daeken/ReCurta/app/curta_jpegs/Curta_1_2037.jpg

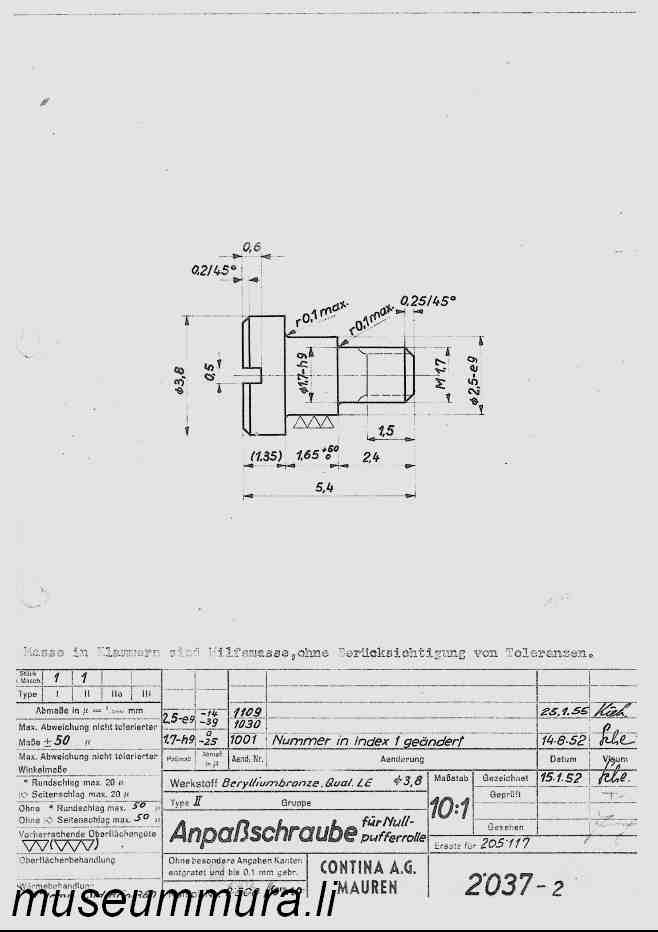
app/curta_jpegs/Curta_1_2037.jpg
