daeken/ReCurta/app/curta_jpegs/Curta_1_10002.jpg

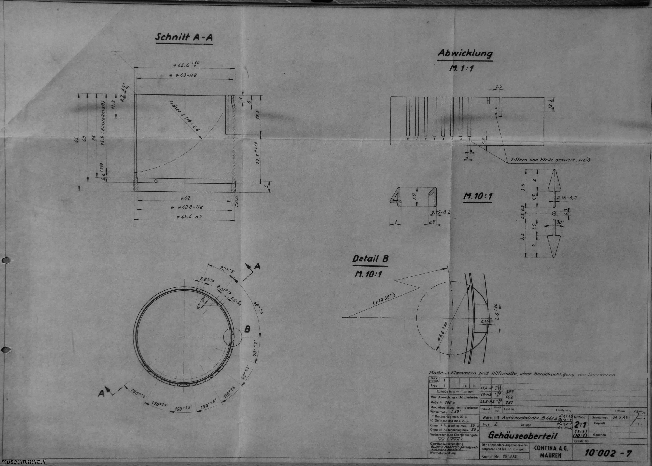
app/curta_jpegs/Curta_1_10002.jpg
