daeken/ReCurta/app/curta_jpegs/Curta_1_10006.jpg

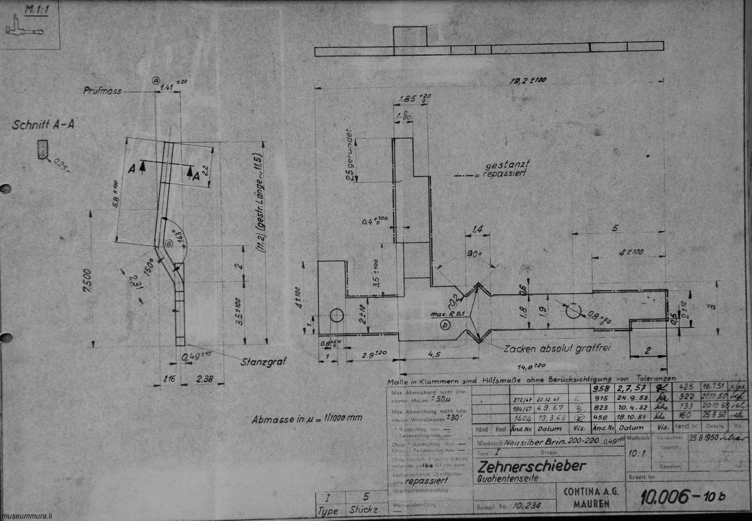
app/curta_jpegs/Curta_1_10006.jpg
