daeken/ReCurta/app/curta_jpegs/Curta_1_10007.jpg

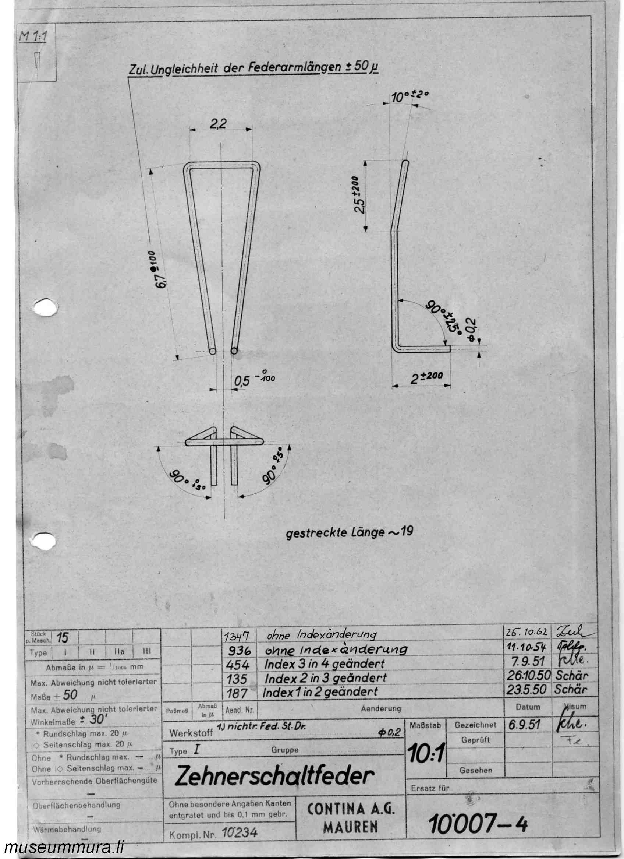
app/curta_jpegs/Curta_1_10007.jpg
