daeken/ReCurta/app/curta_jpegs/Curta_1_10008.jpg

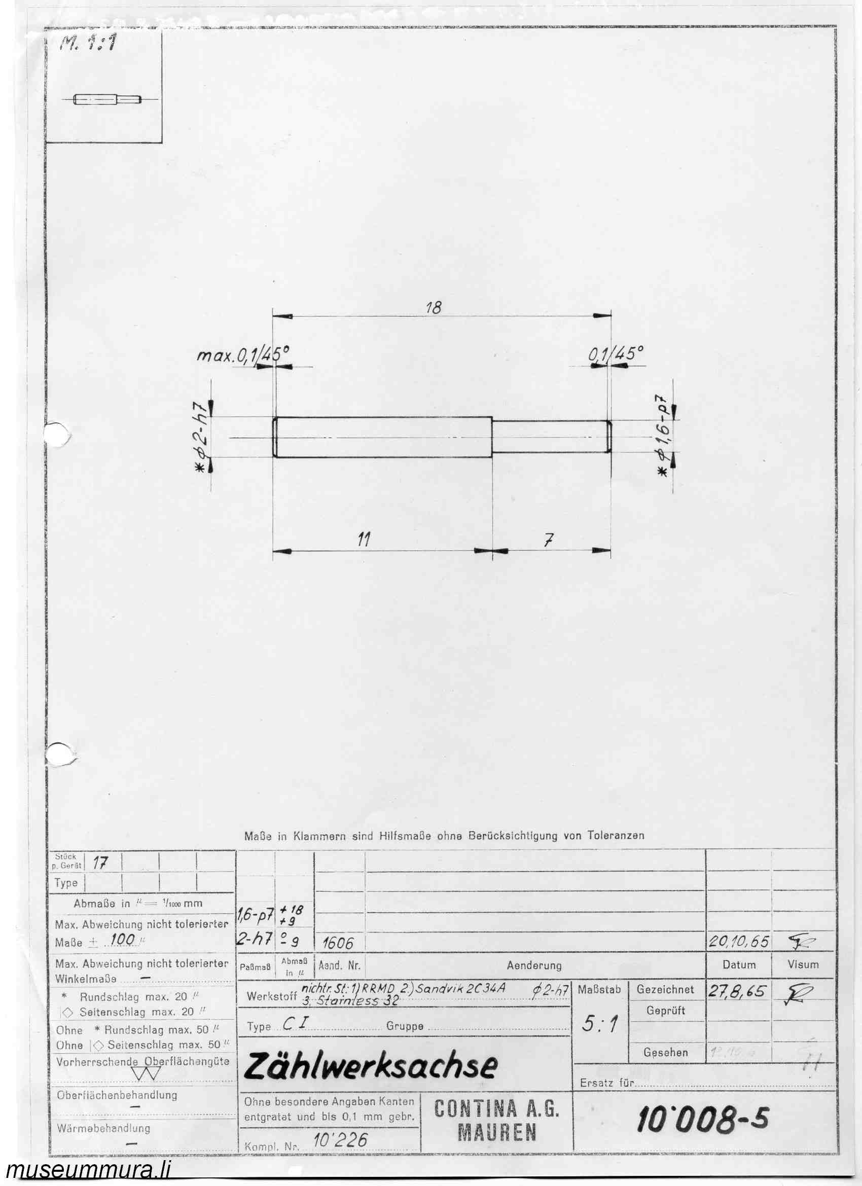
app/curta_jpegs/Curta_1_10008.jpg
