daeken/ReCurta/app/curta_jpegs/Curta_1_10009.jpg

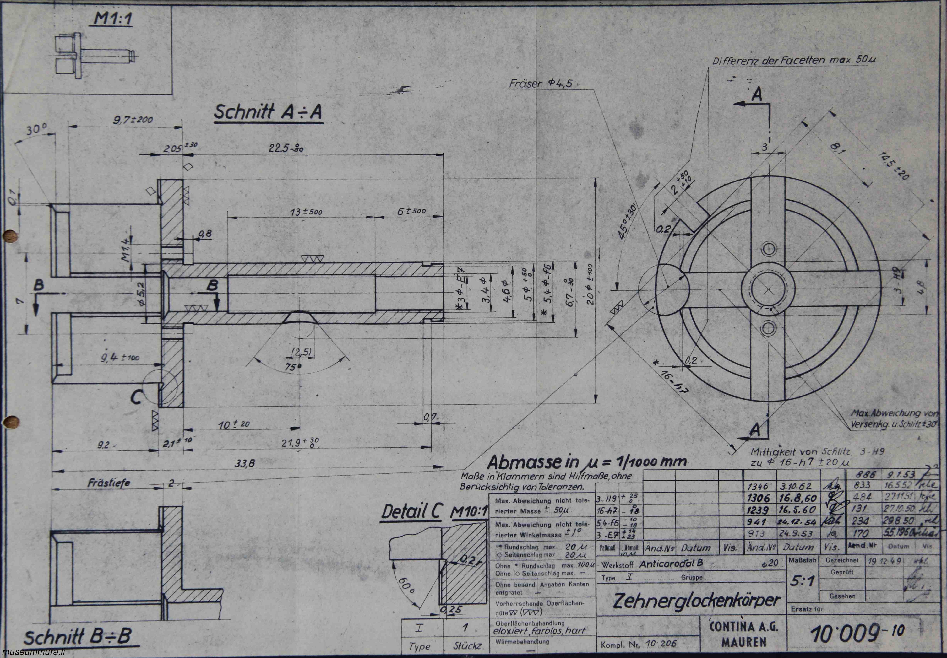
app/curta_jpegs/Curta_1_10009.jpg
