daeken/ReCurta/app/curta_jpegs/Curta_1_10010.jpg

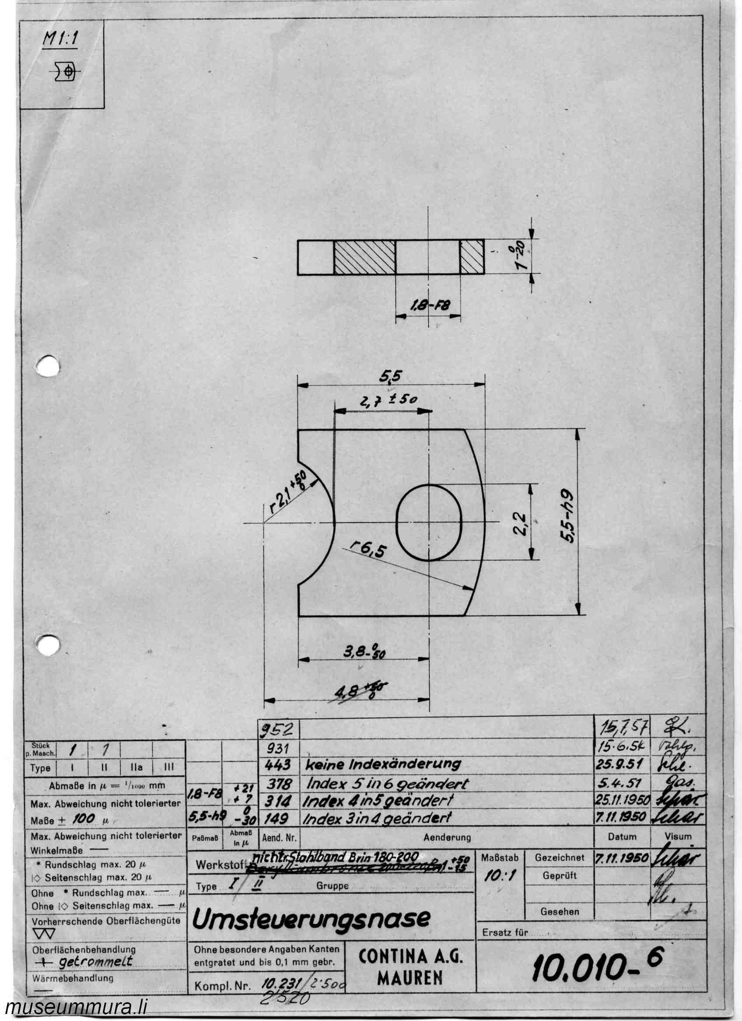
app/curta_jpegs/Curta_1_10010.jpg
