daeken/ReCurta/app/curta_jpegs/Curta_1_10011.jpg

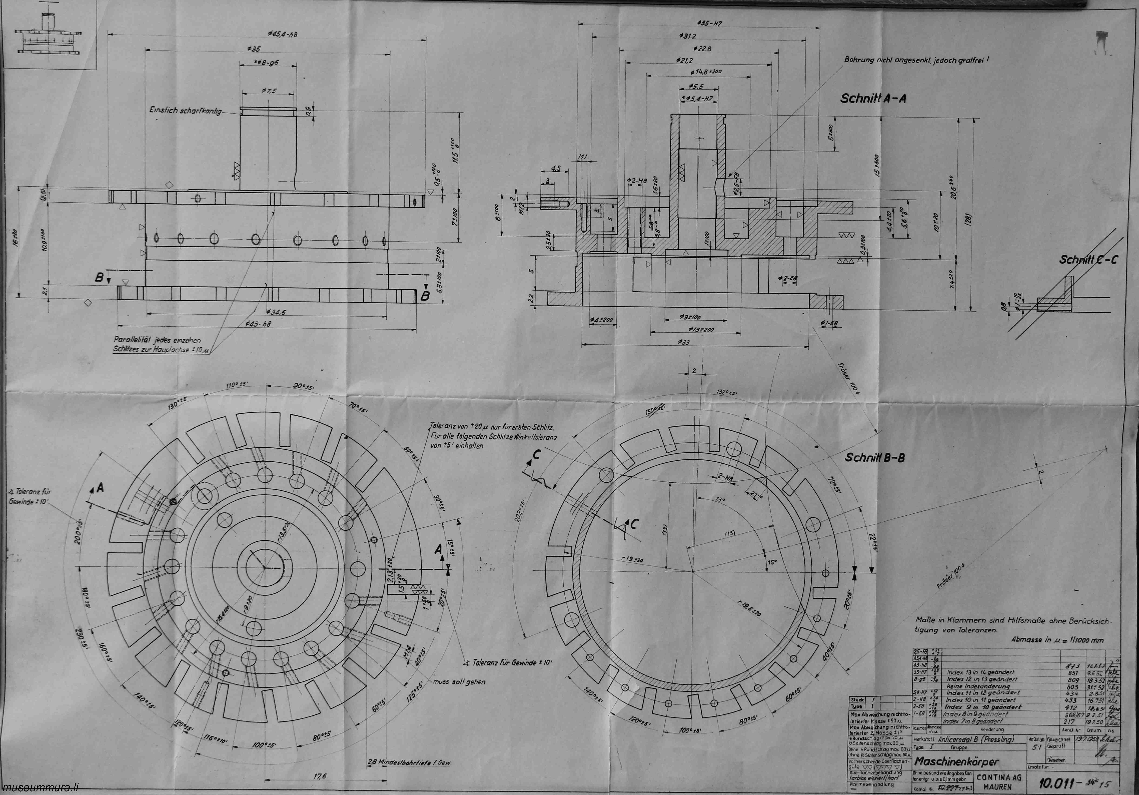
app/curta_jpegs/Curta_1_10011.jpg
