daeken/ReCurta/app/curta_jpegs/Curta_1_10014.jpg

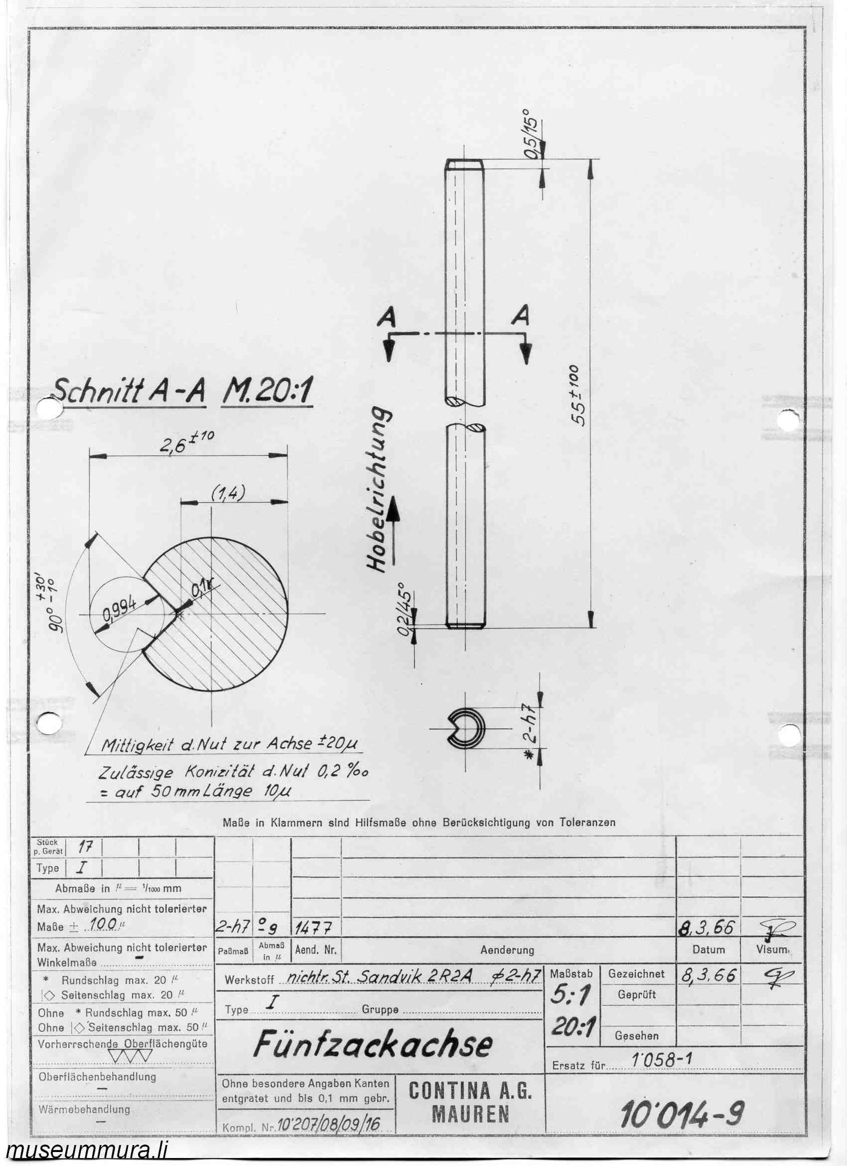
app/curta_jpegs/Curta_1_10014.jpg
