daeken/ReCurta/app/curta_jpegs/Curta_1_10015.jpg

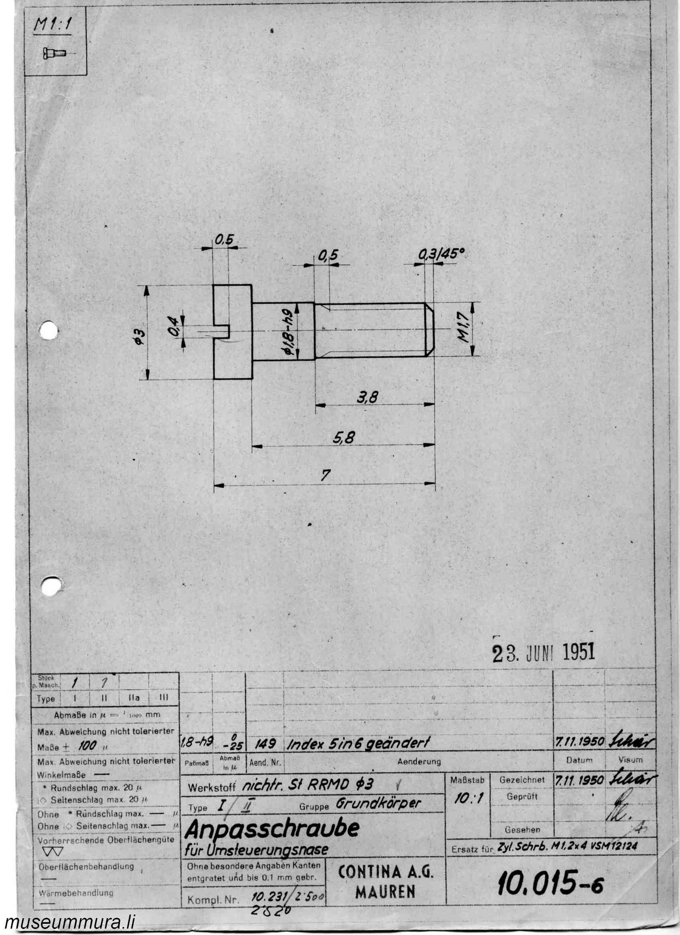
app/curta_jpegs/Curta_1_10015.jpg
