daeken/ReCurta/app/curta_jpegs/Curta_1_10018.jpg

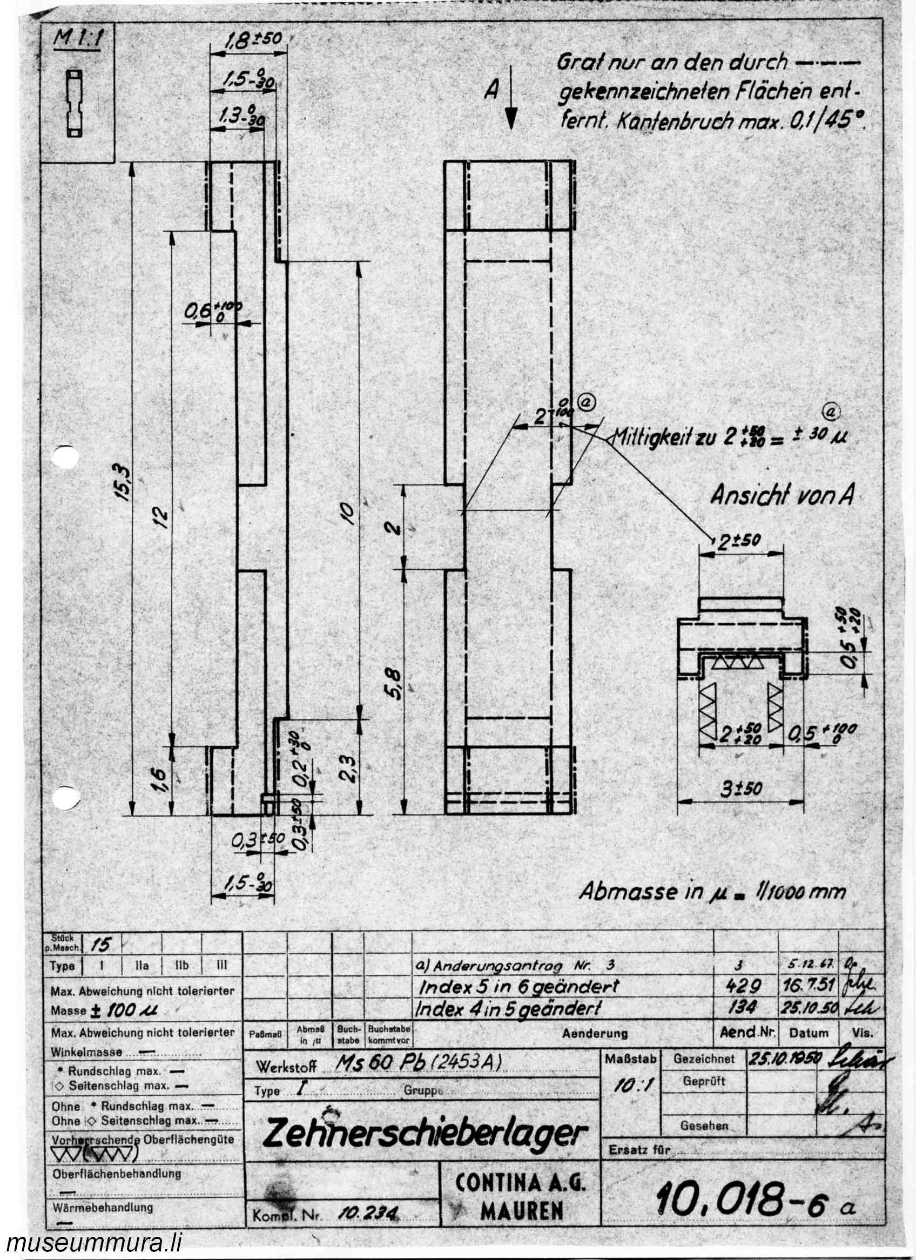
app/curta_jpegs/Curta_1_10018.jpg
