daeken/ReCurta/app/curta_jpegs/Curta_1_10019.jpg

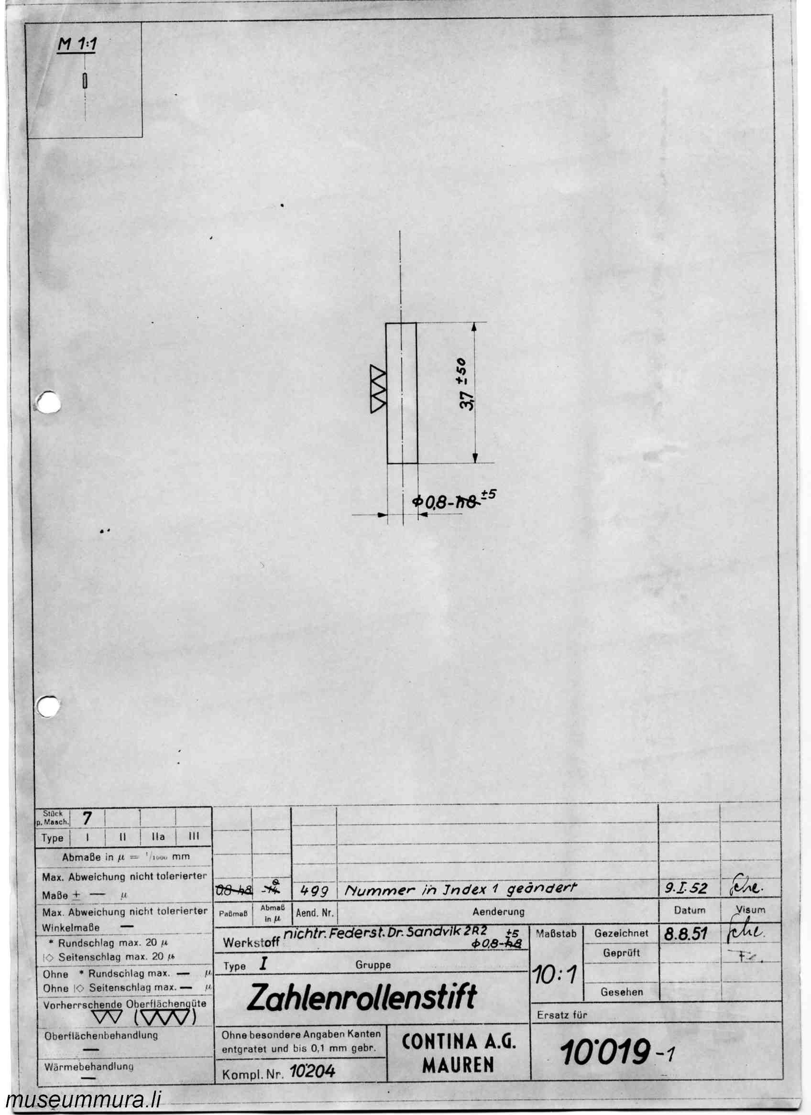
app/curta_jpegs/Curta_1_10019.jpg
