daeken/ReCurta/app/curta_jpegs/Curta_1_10020.jpg

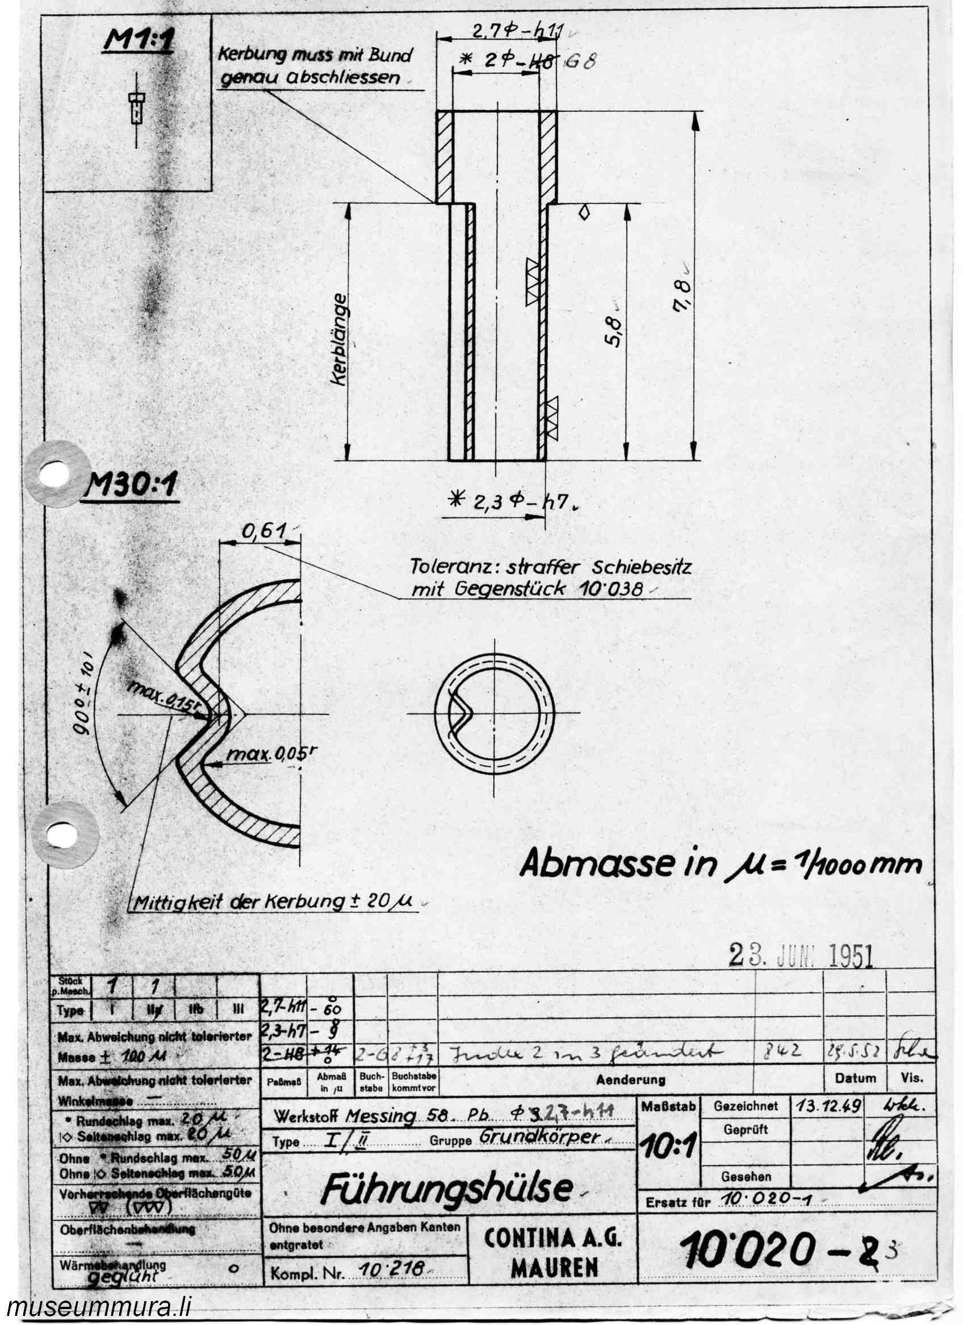
app/curta_jpegs/Curta_1_10020.jpg
