daeken/ReCurta/app/curta_jpegs/Curta_1_10021.jpg

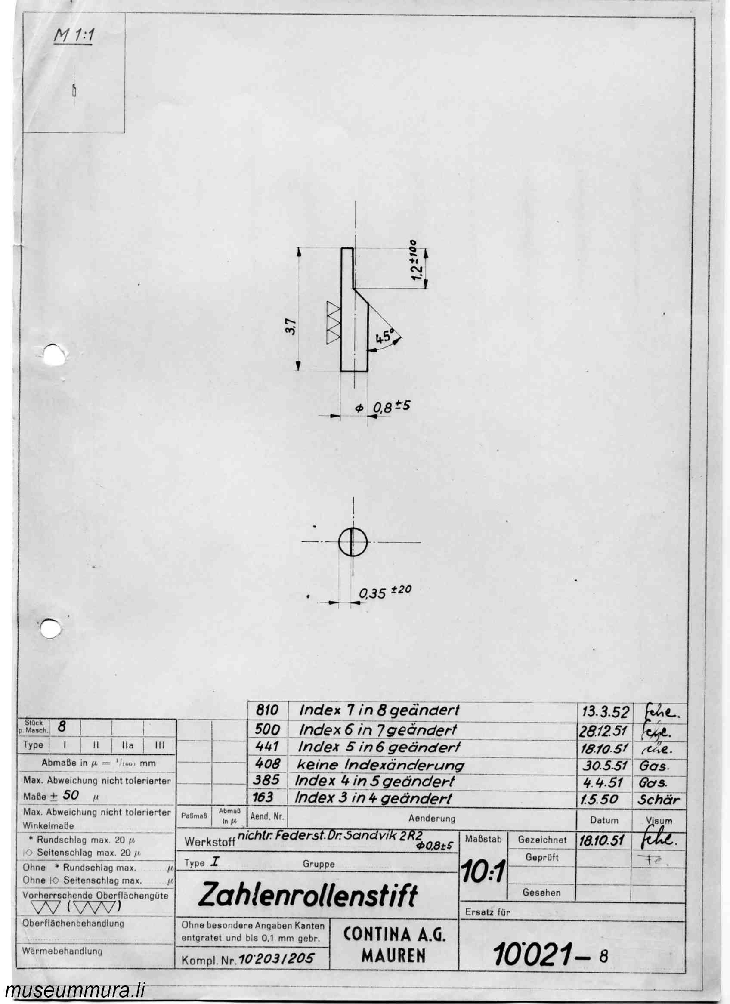
app/curta_jpegs/Curta_1_10021.jpg
