daeken/ReCurta/app/curta_jpegs/Curta_1_10024.jpg

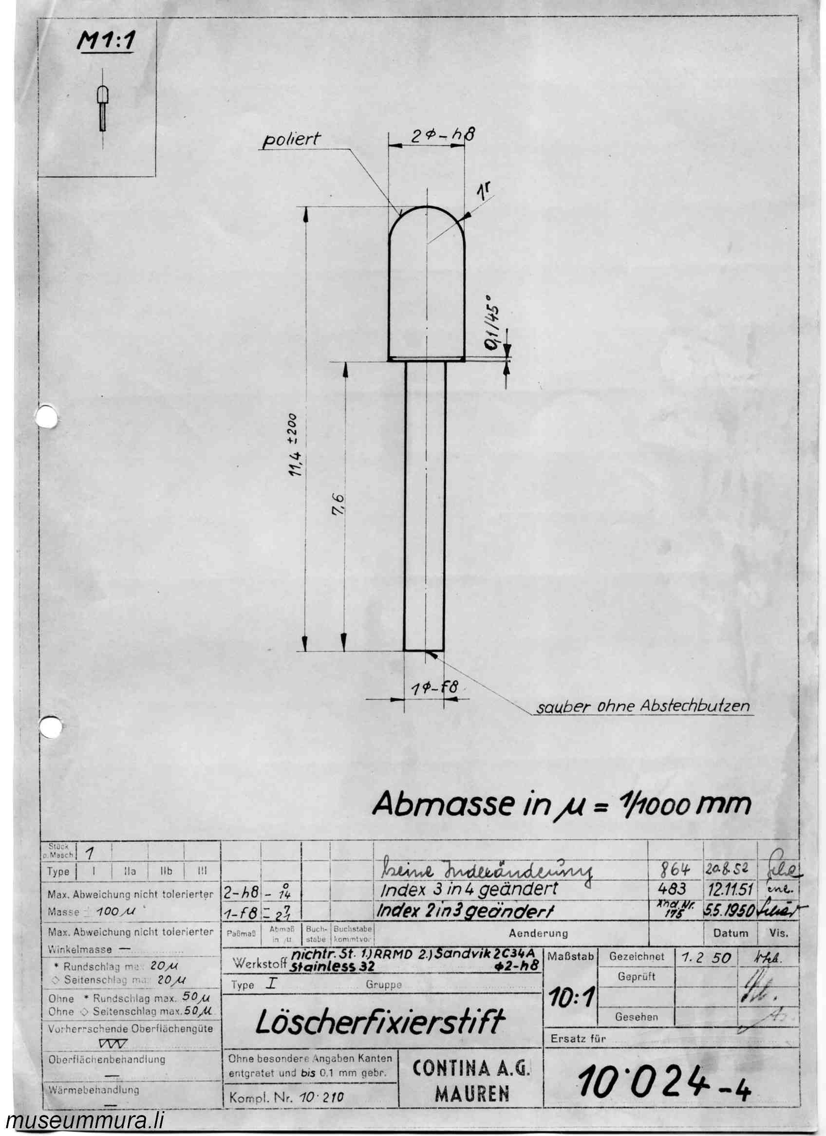
app/curta_jpegs/Curta_1_10024.jpg
