daeken/ReCurta/app/curta_jpegs/Curta_1_10026.jpg

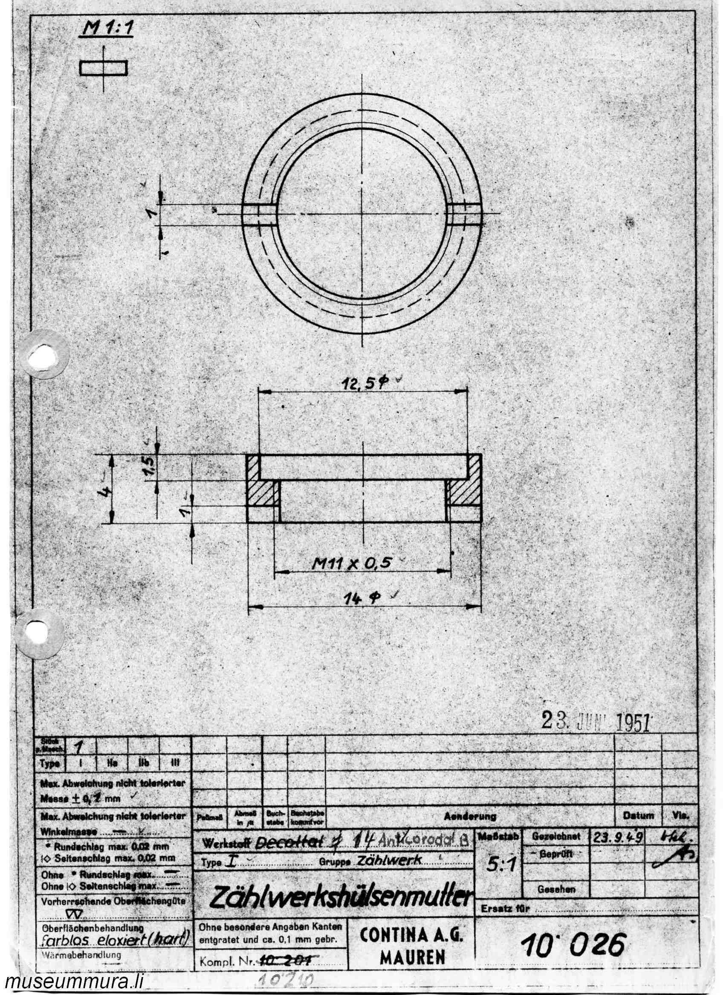
app/curta_jpegs/Curta_1_10026.jpg
