daeken/ReCurta/app/curta_jpegs/Curta_1_10028.jpg

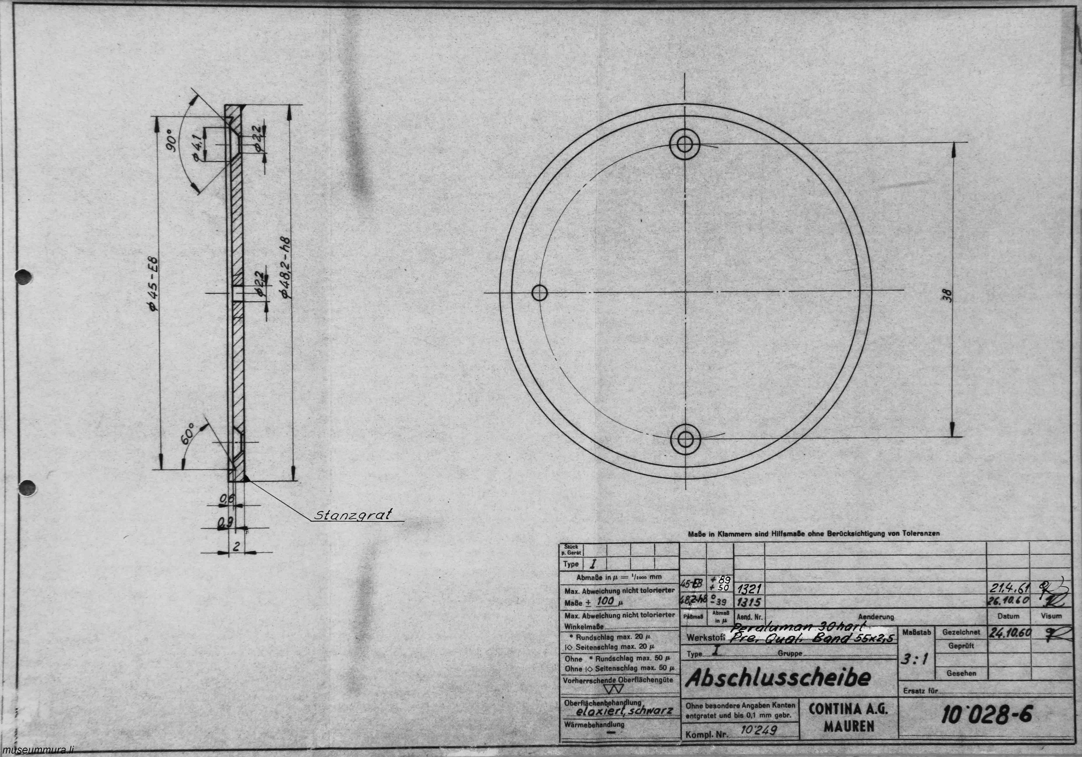
app/curta_jpegs/Curta_1_10028.jpg
