daeken/ReCurta/app/curta_jpegs/Curta_1_10030.jpg

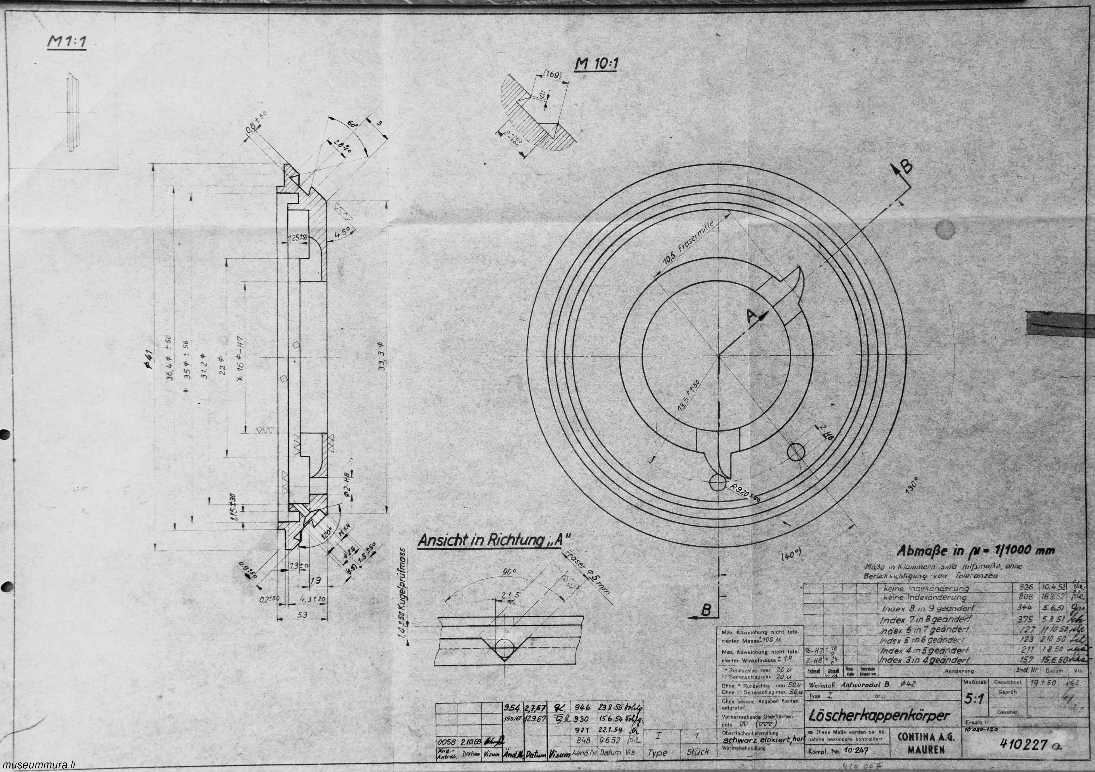
app/curta_jpegs/Curta_1_10030.jpg
