daeken/ReCurta/app/curta_jpegs/Curta_1_10031.jpg

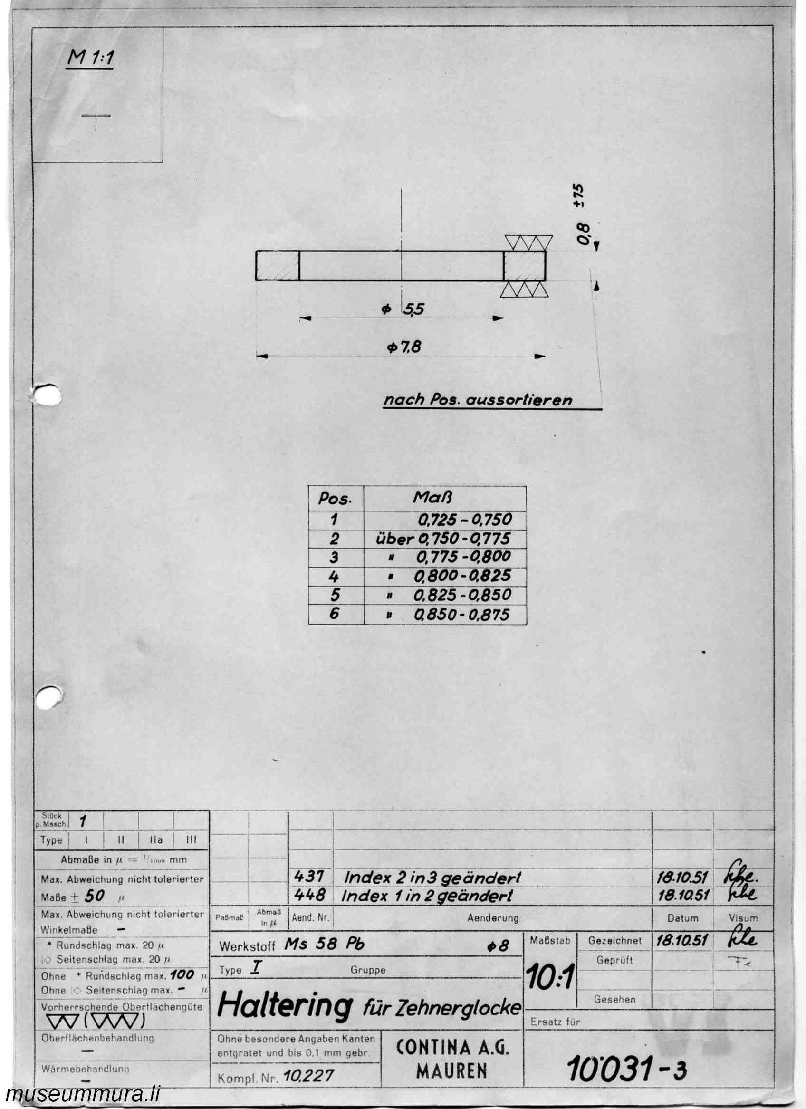
app/curta_jpegs/Curta_1_10031.jpg
