daeken/ReCurta/app/curta_jpegs/Curta_1_10033.jpg

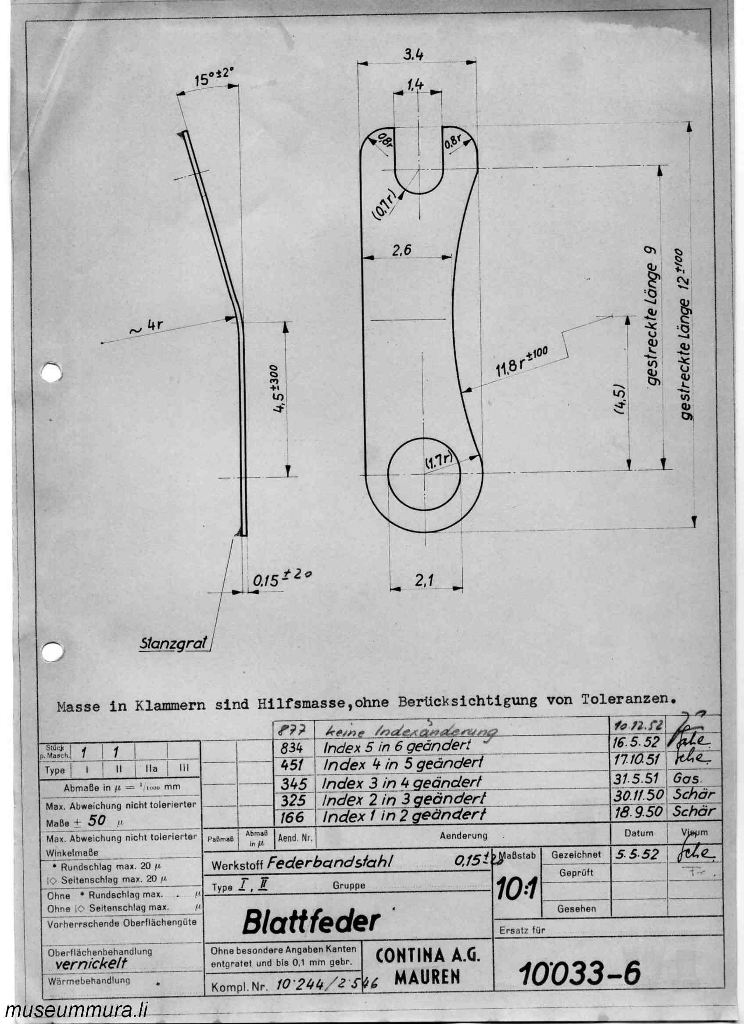
app/curta_jpegs/Curta_1_10033.jpg
