daeken/ReCurta/app/curta_jpegs/Curta_1_10034.jpg

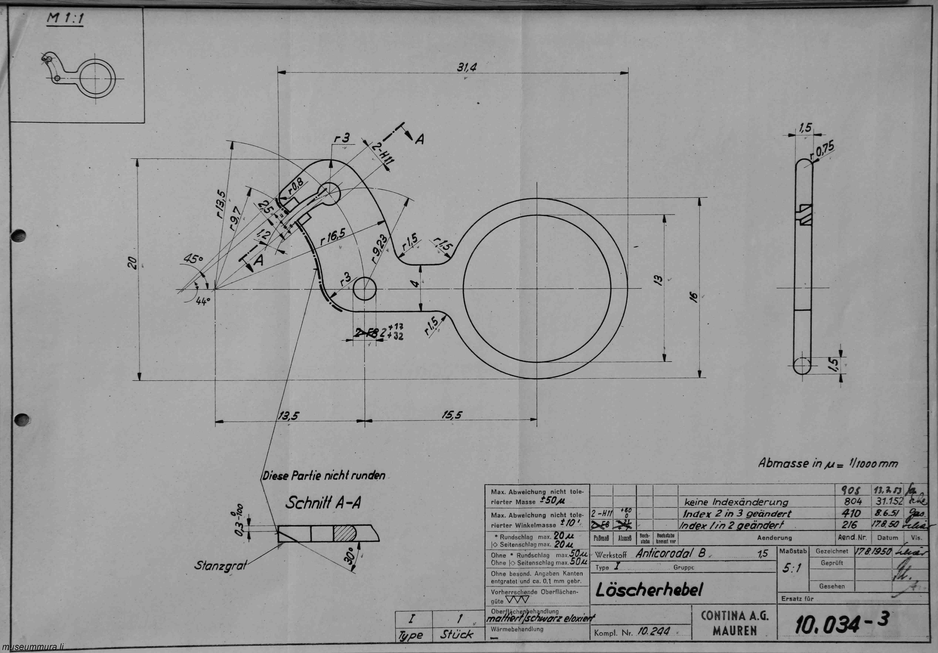
app/curta_jpegs/Curta_1_10034.jpg
