daeken/ReCurta/app/curta_jpegs/Curta_1_10035.jpg

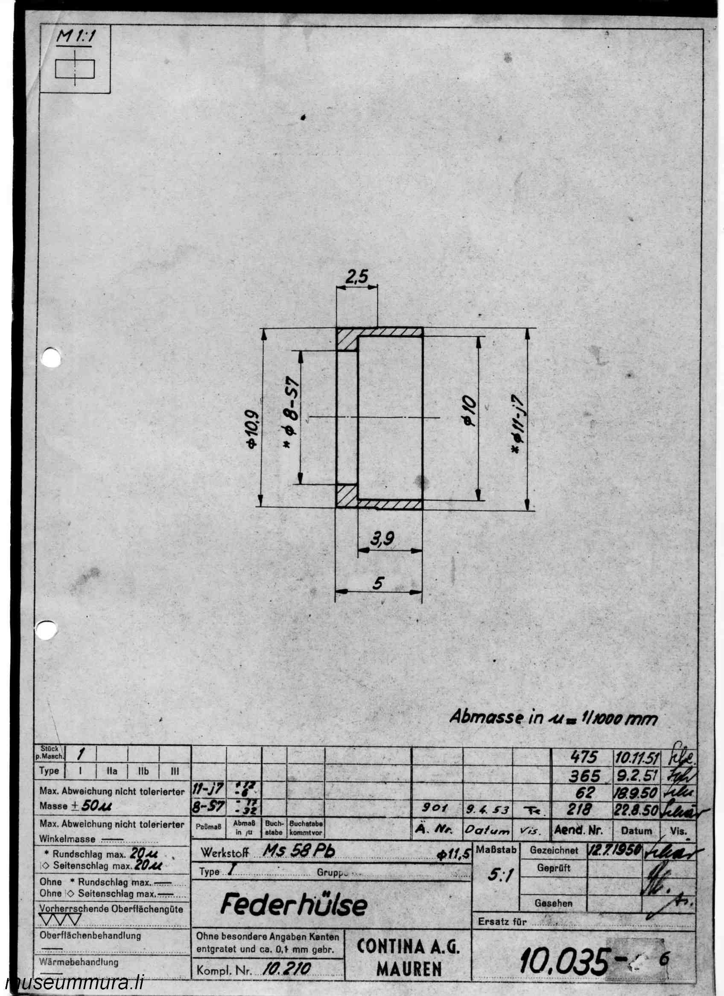
app/curta_jpegs/Curta_1_10035.jpg
