daeken/ReCurta/app/curta_jpegs/Curta_1_10036.jpg

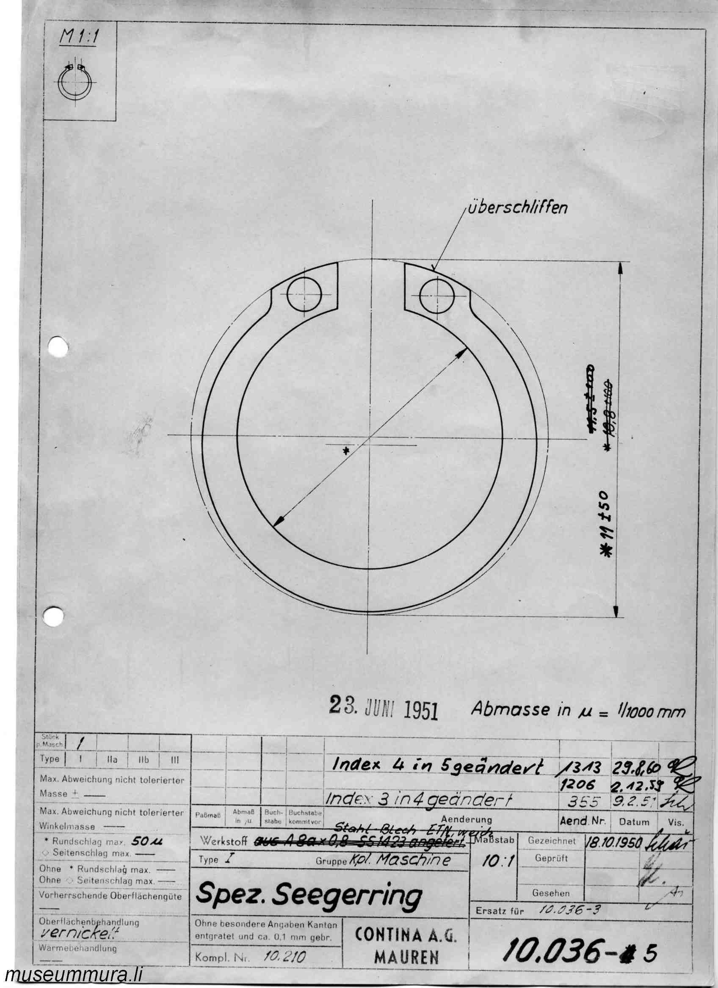
app/curta_jpegs/Curta_1_10036.jpg
