daeken/ReCurta/app/curta_jpegs/Curta_1_10039.jpg

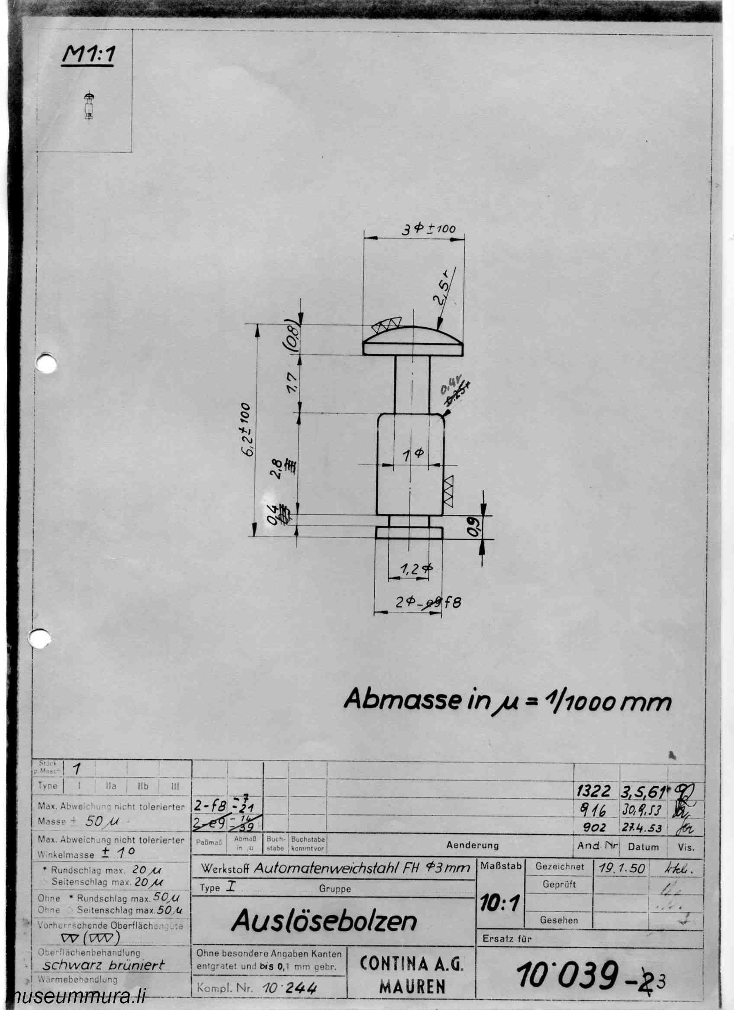
app/curta_jpegs/Curta_1_10039.jpg
