daeken/ReCurta/app/curta_jpegs/Curta_1_10041.jpg

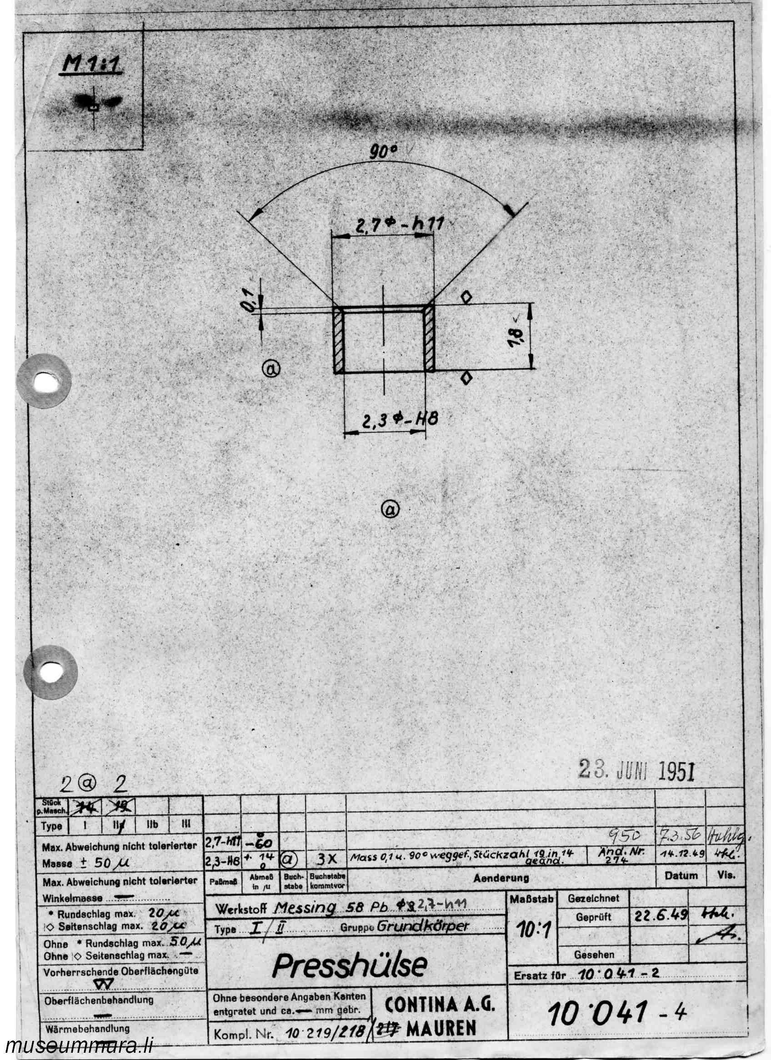
app/curta_jpegs/Curta_1_10041.jpg
