daeken/ReCurta/app/curta_jpegs/Curta_1_10046.jpg

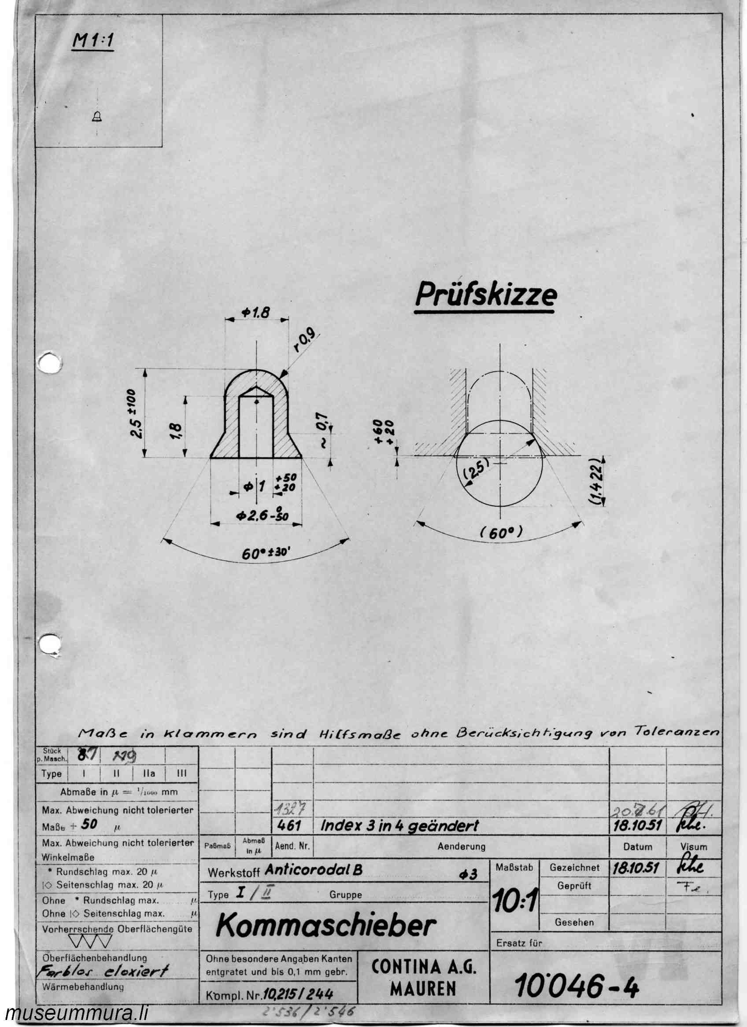
app/curta_jpegs/Curta_1_10046.jpg
