daeken/ReCurta/app/curta_jpegs/Curta_1_10047.jpg

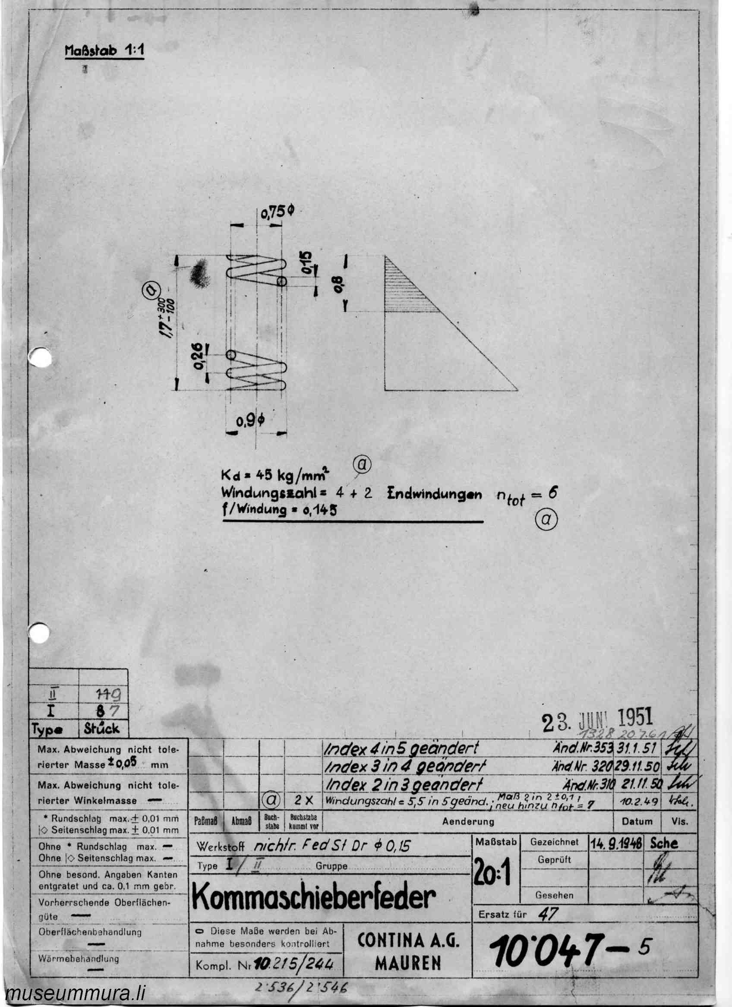
app/curta_jpegs/Curta_1_10047.jpg
