daeken/ReCurta/app/curta_jpegs/Curta_1_10048.jpg

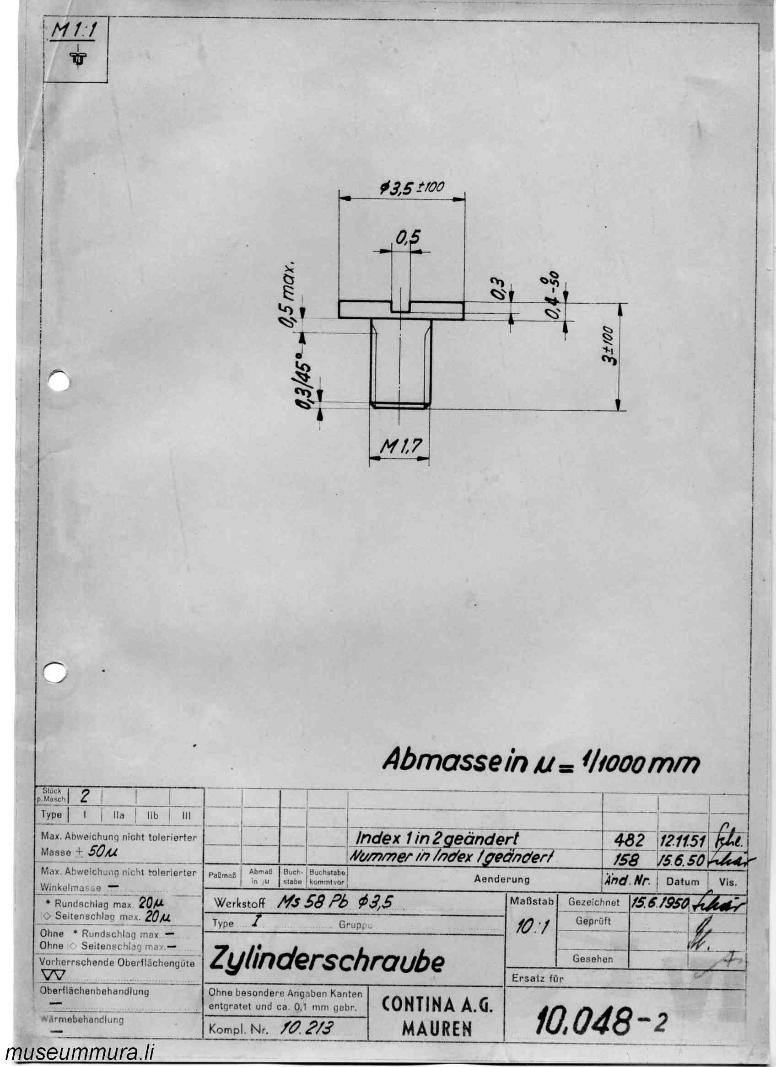
app/curta_jpegs/Curta_1_10048.jpg
