daeken/ReCurta/app/curta_jpegs/Curta_1_10049.jpg

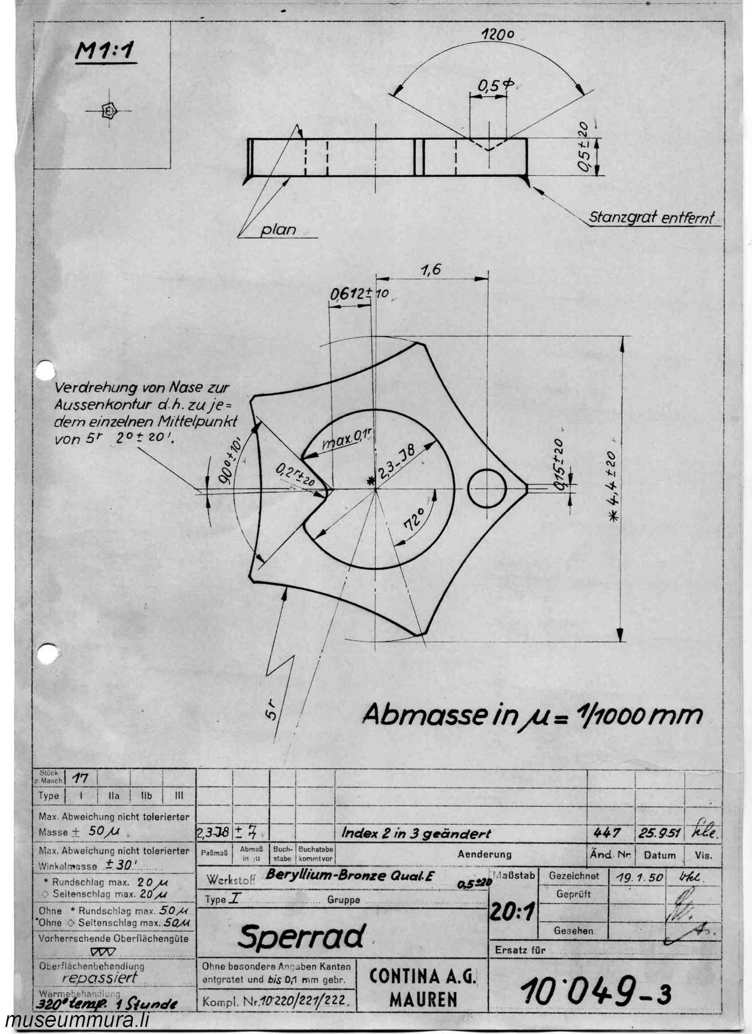
app/curta_jpegs/Curta_1_10049.jpg
