daeken/ReCurta/app/curta_jpegs/Curta_1_10051.jpg

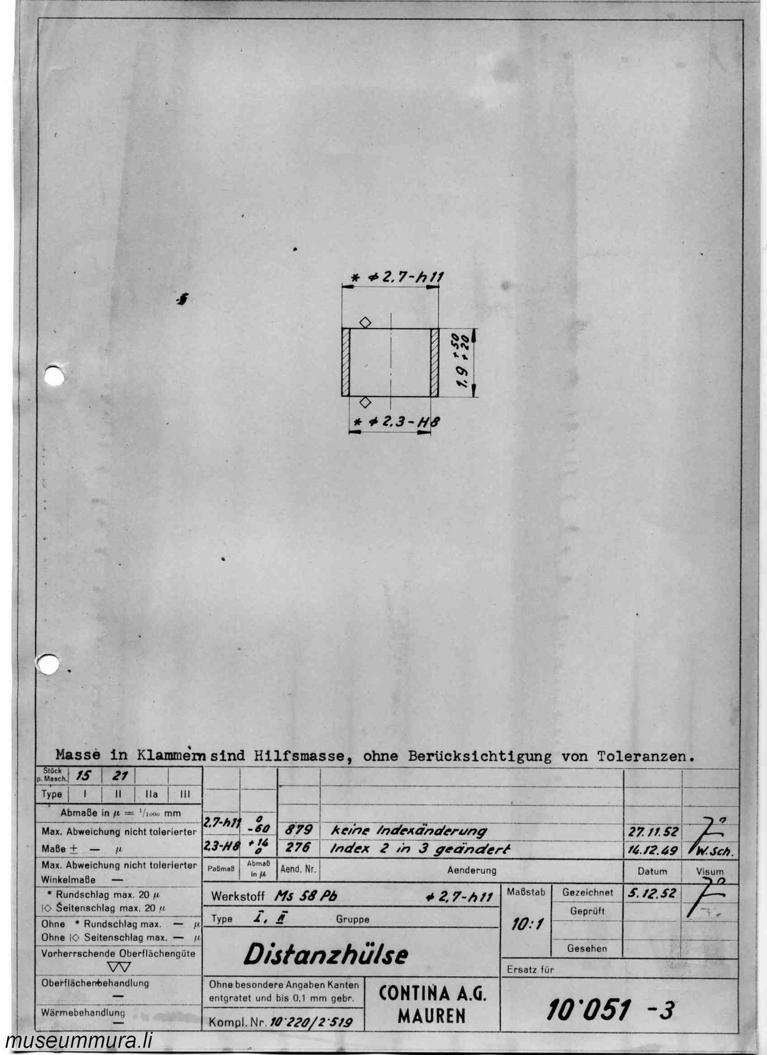
app/curta_jpegs/Curta_1_10051.jpg
