daeken/ReCurta/app/curta_jpegs/Curta_1_10052.jpg

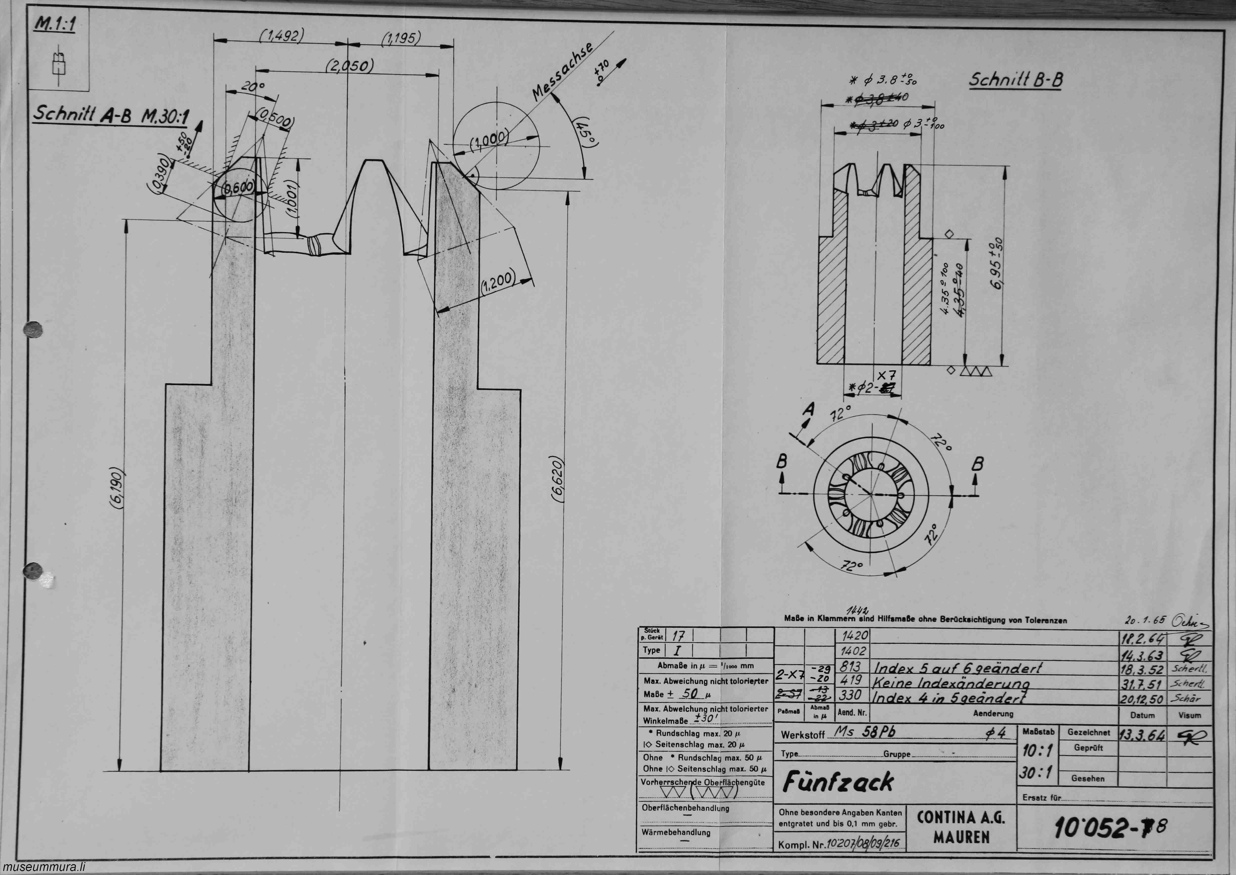
app/curta_jpegs/Curta_1_10052.jpg
