daeken/ReCurta/app/curta_jpegs/Curta_1_10059.jpg

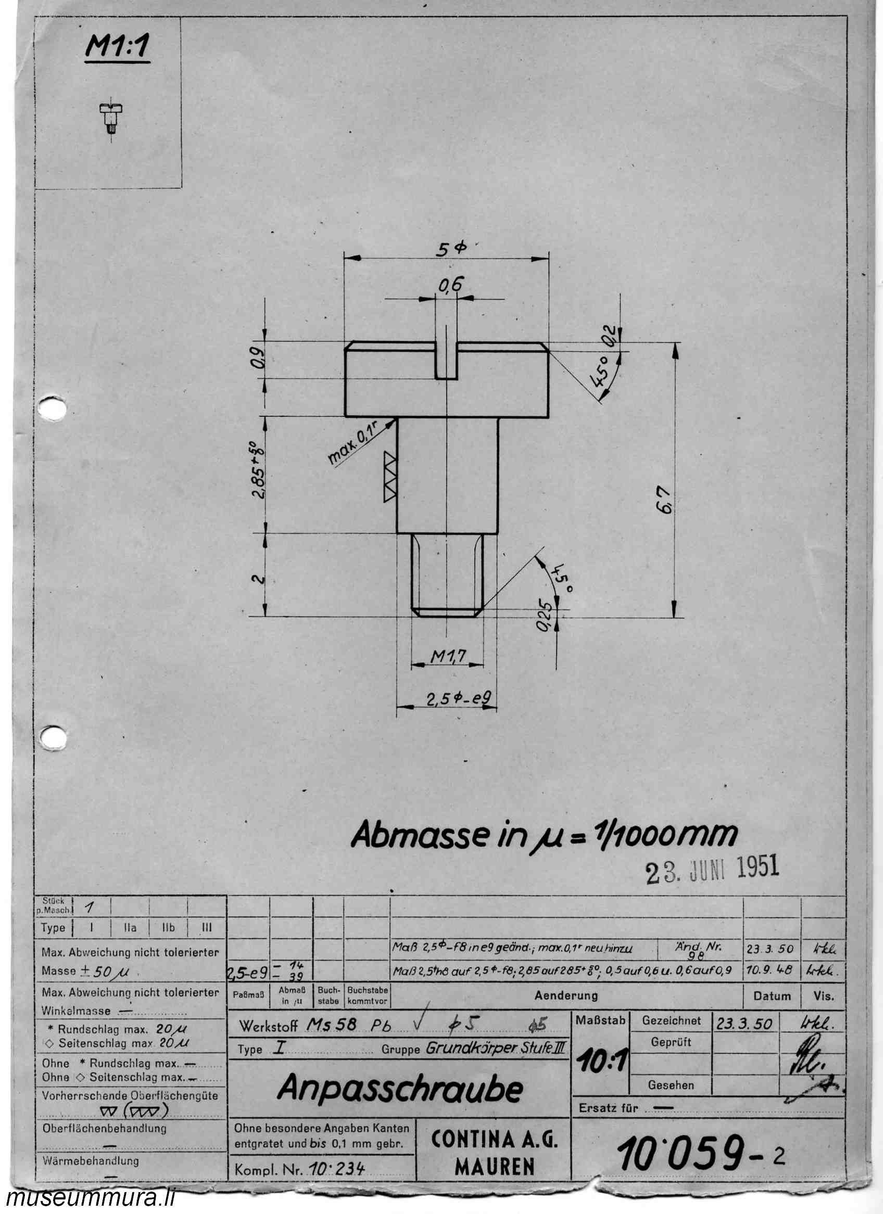
app/curta_jpegs/Curta_1_10059.jpg
