daeken/ReCurta/app/curta_jpegs/Curta_1_10064.jpg

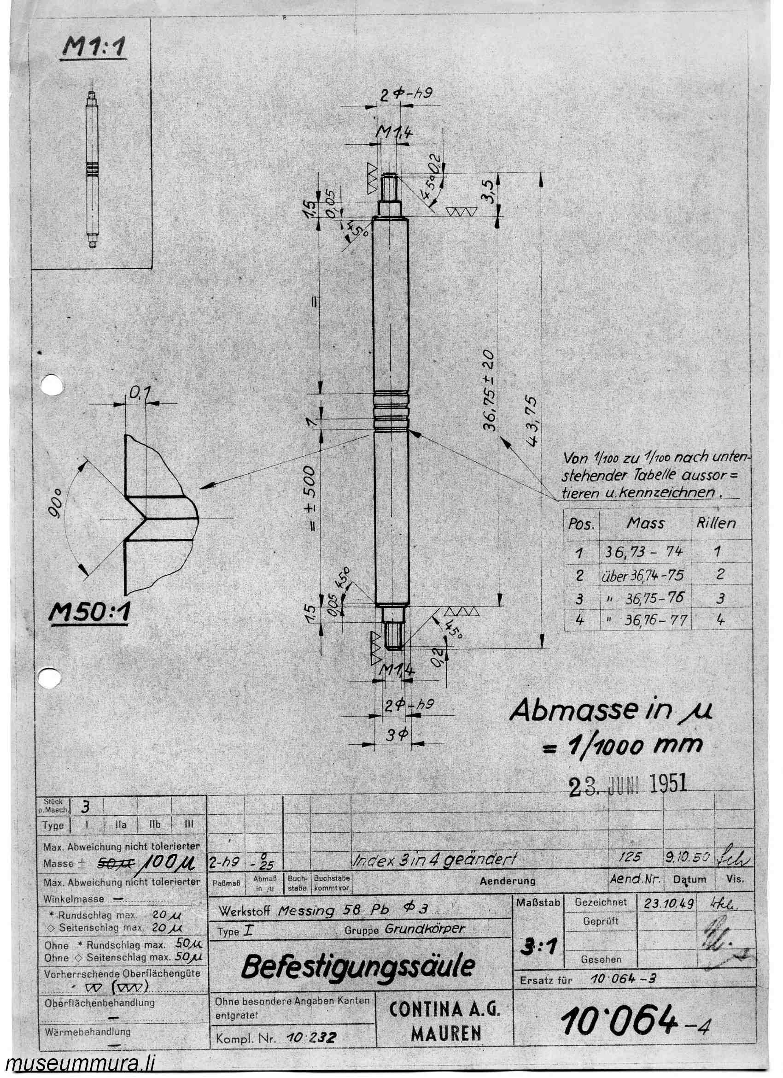
app/curta_jpegs/Curta_1_10064.jpg
