daeken/ReCurta/app/curta_jpegs/Curta_1_10068.jpg

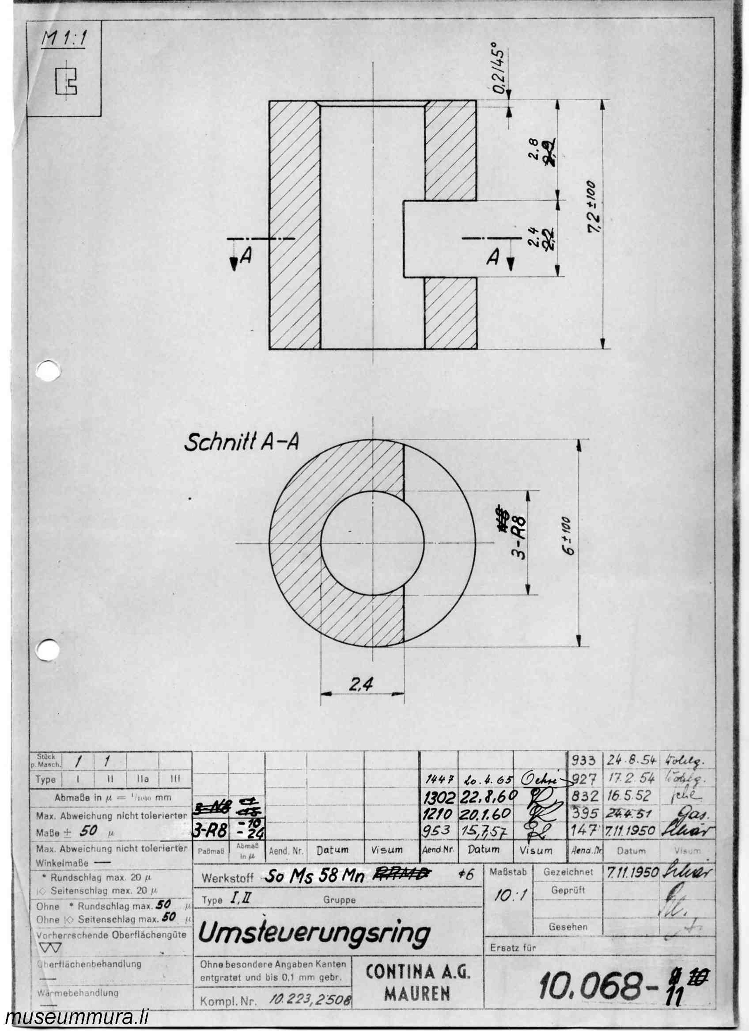
app/curta_jpegs/Curta_1_10068.jpg
