daeken/ReCurta/app/curta_jpegs/Curta_1_10072.jpg

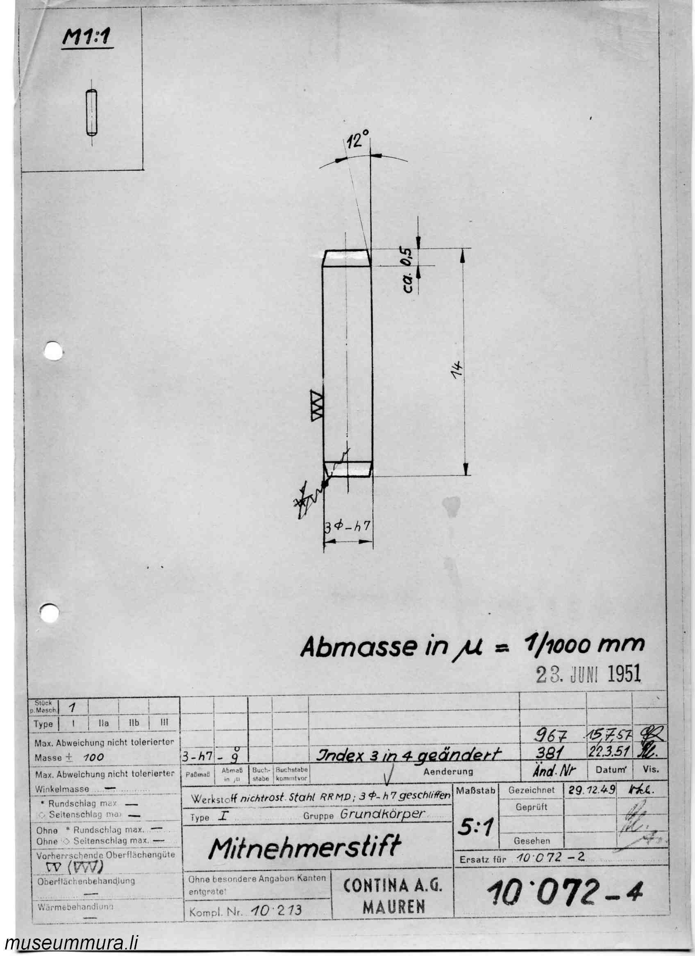
app/curta_jpegs/Curta_1_10072.jpg
