daeken/ReCurta/app/curta_jpegs/Curta_1_10073.jpg

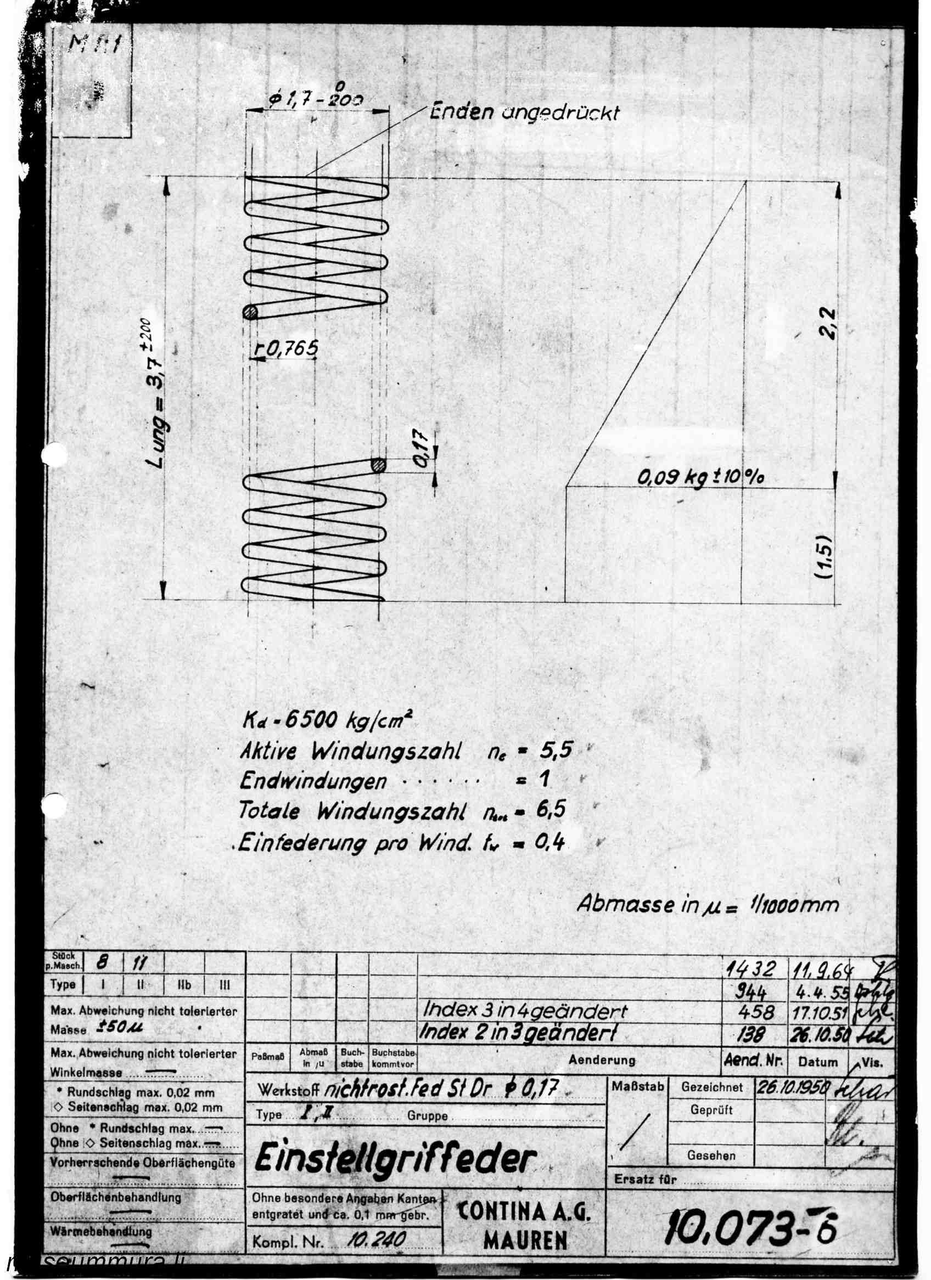
app/curta_jpegs/Curta_1_10073.jpg
