daeken/ReCurta/app/curta_jpegs/Curta_1_10074.jpg

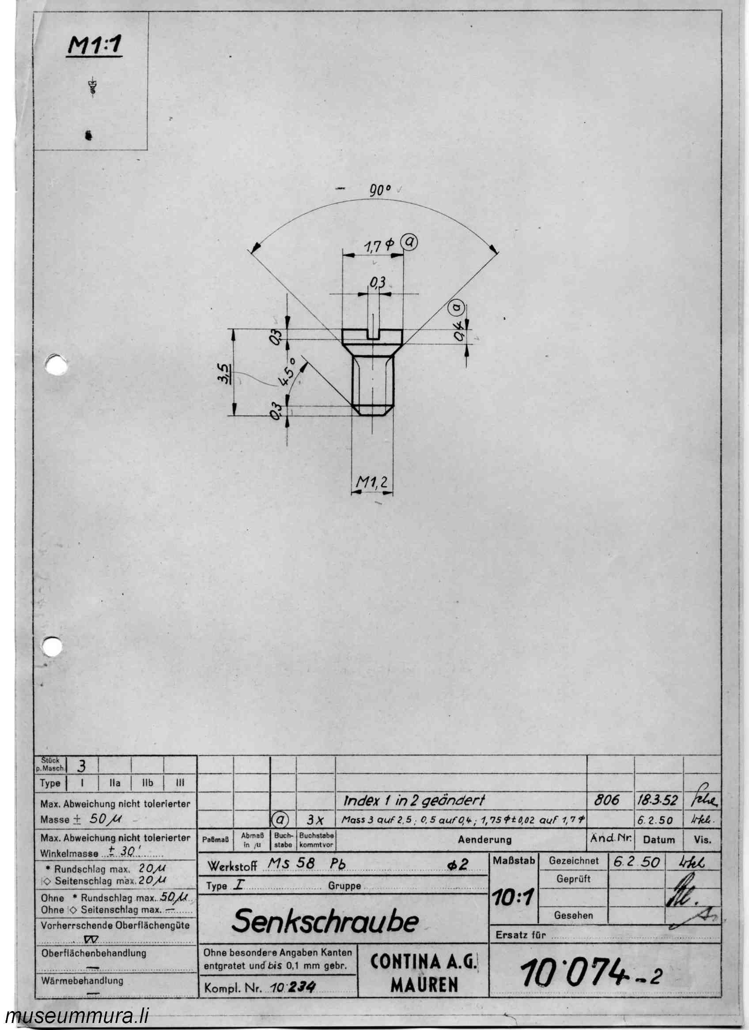
app/curta_jpegs/Curta_1_10074.jpg
