daeken/ReCurta/app/curta_jpegs/Curta_1_10075.jpg

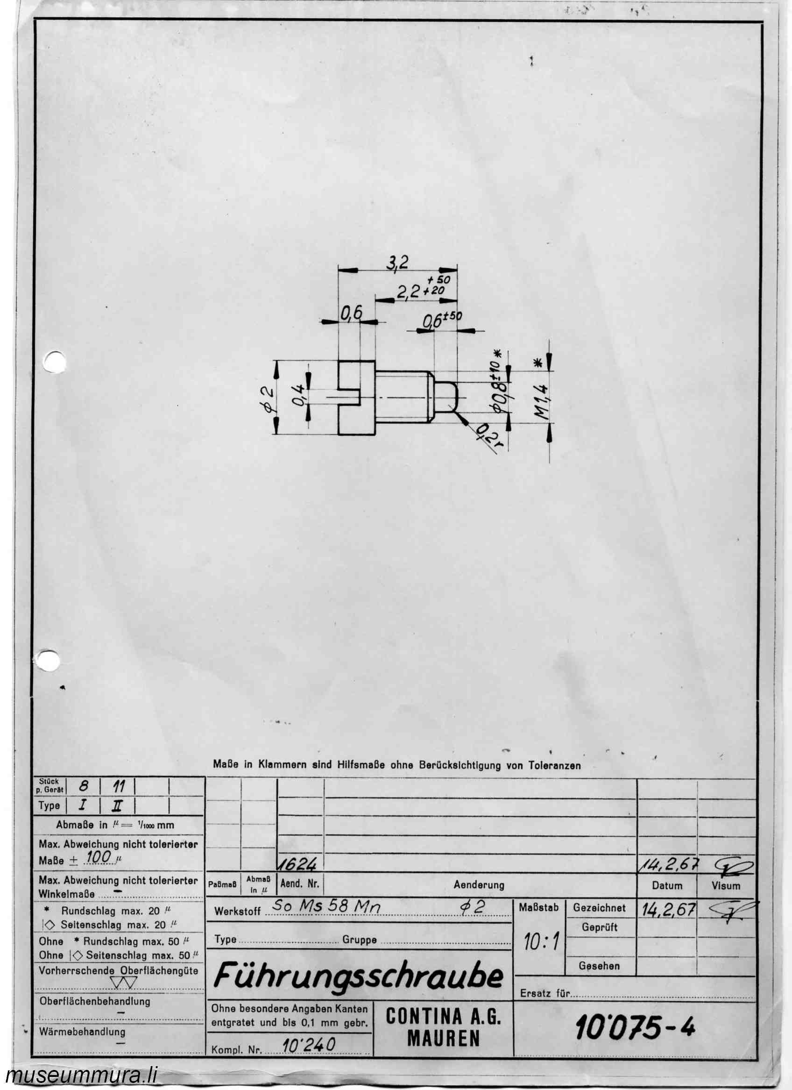
app/curta_jpegs/Curta_1_10075.jpg
