daeken/ReCurta/app/curta_jpegs/Curta_1_10076.jpg

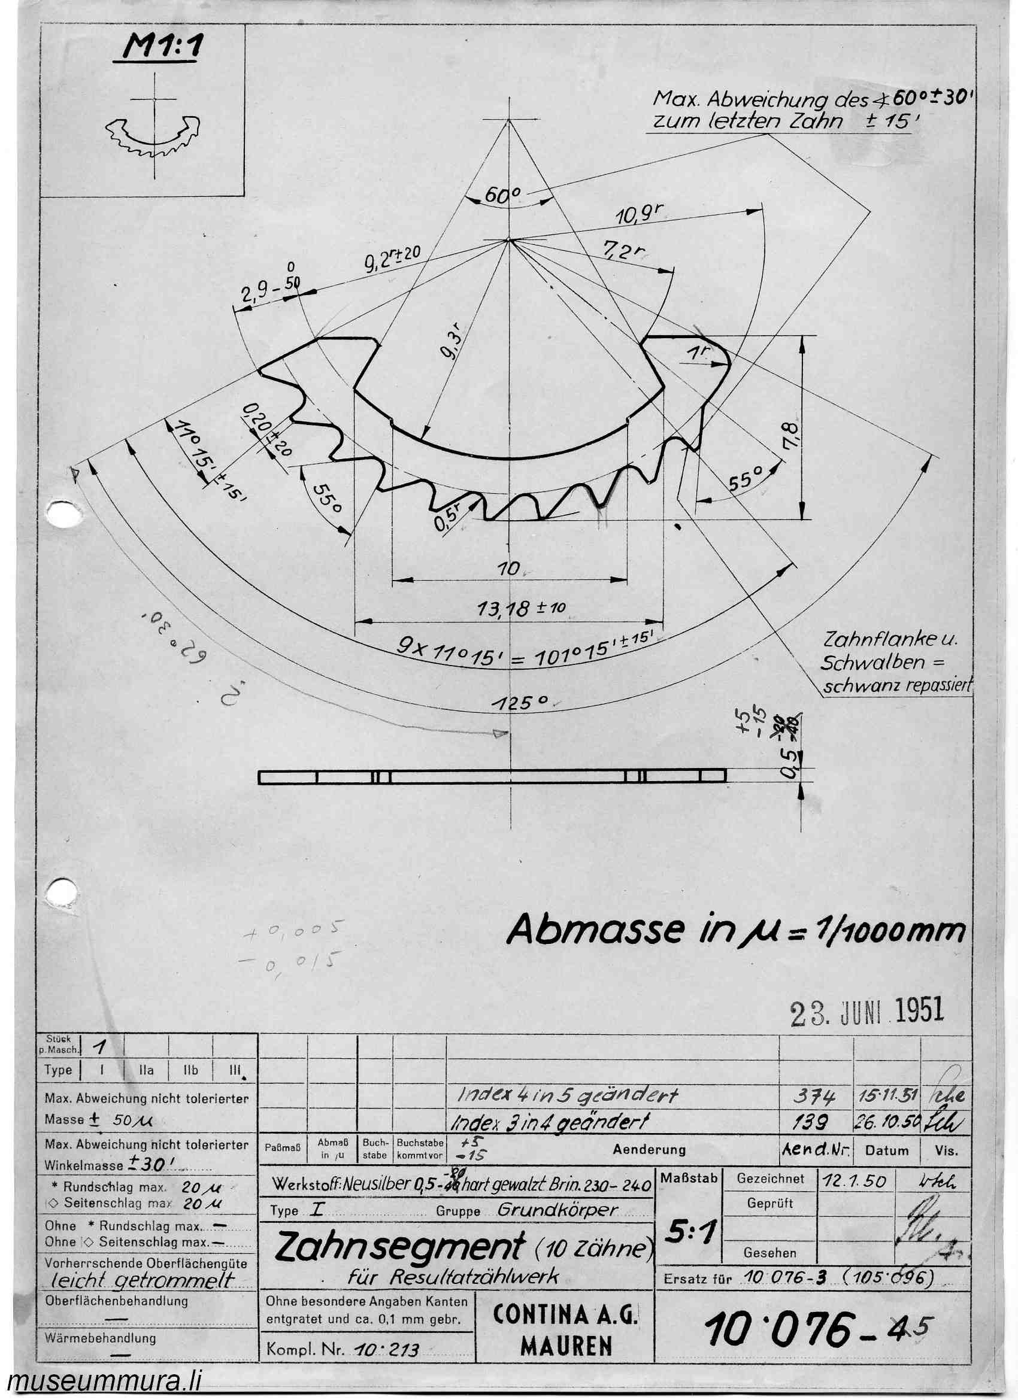
app/curta_jpegs/Curta_1_10076.jpg
