daeken/ReCurta/app/curta_jpegs/Curta_1_10077.jpg

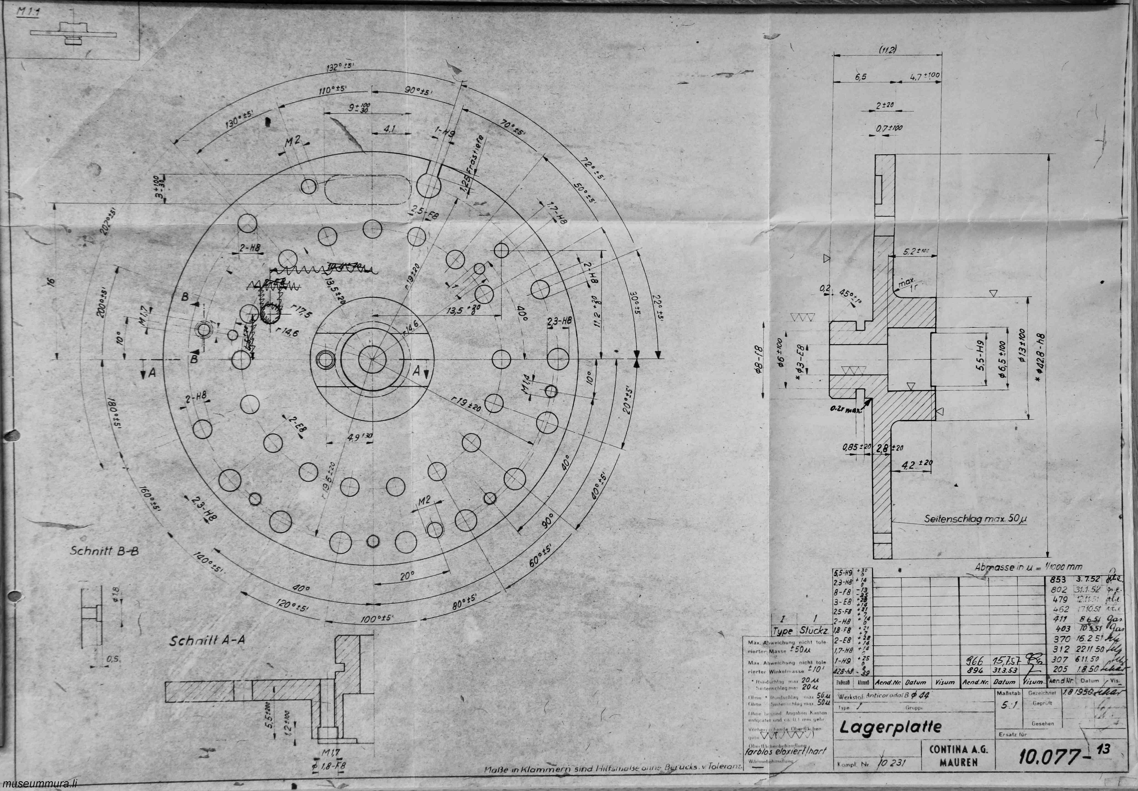
app/curta_jpegs/Curta_1_10077.jpg
