daeken/ReCurta/app/curta_jpegs/Curta_1_10078.jpg

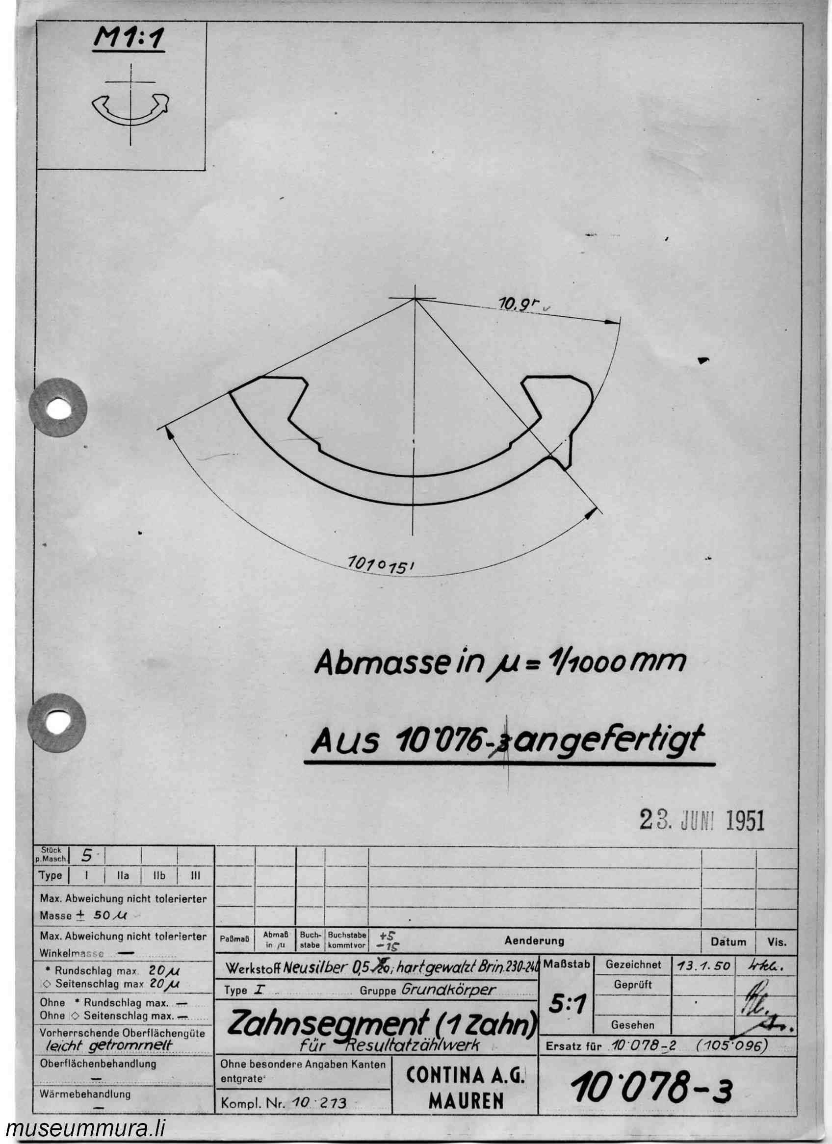
app/curta_jpegs/Curta_1_10078.jpg
