daeken/ReCurta/app/curta_jpegs/Curta_1_10081.jpg

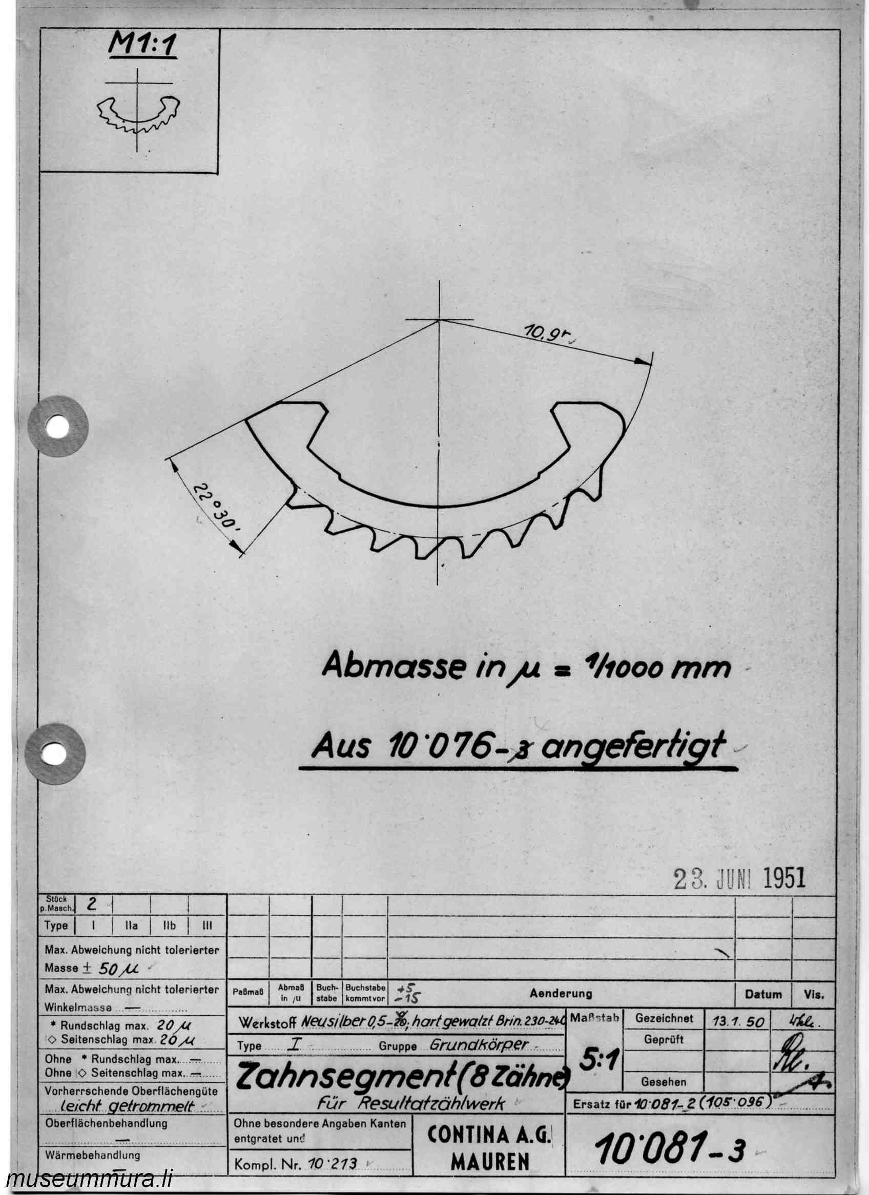
app/curta_jpegs/Curta_1_10081.jpg
