daeken/ReCurta/app/curta_jpegs/Curta_1_10082.jpg

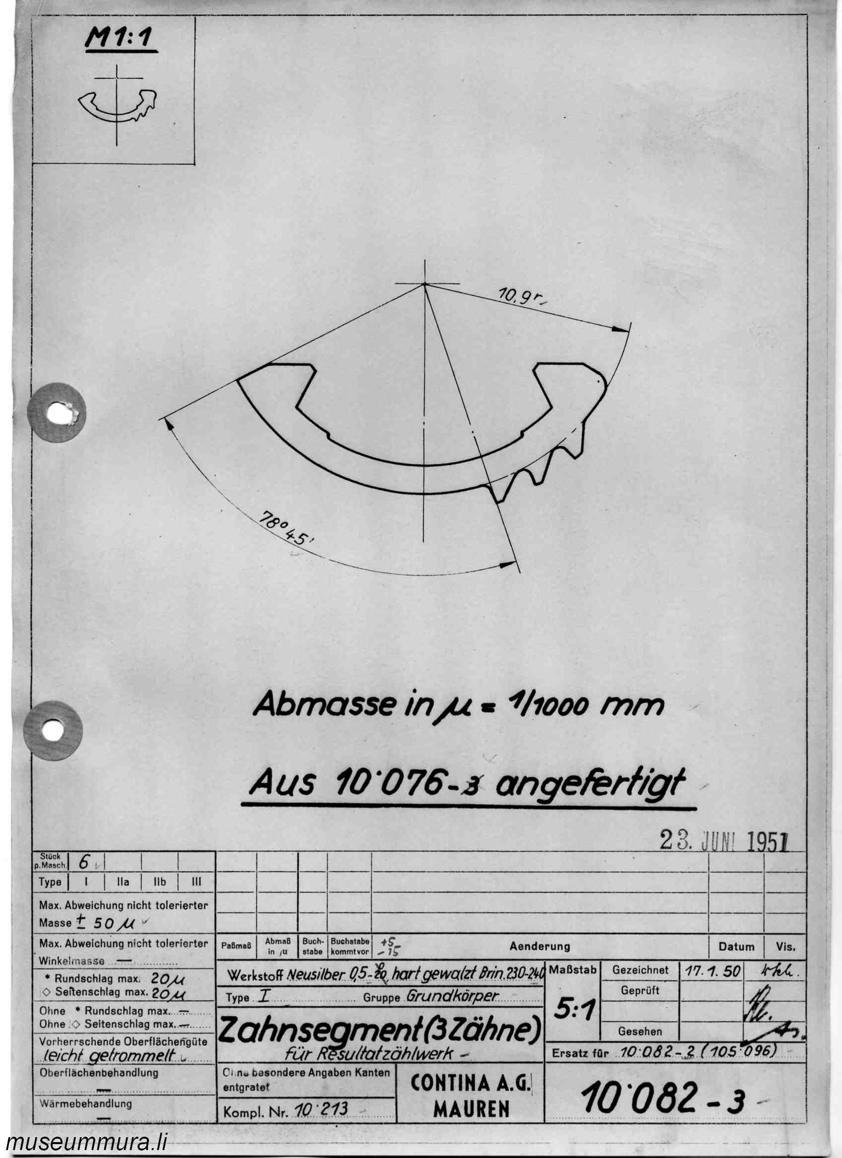
app/curta_jpegs/Curta_1_10082.jpg
