daeken/ReCurta/app/curta_jpegs/Curta_1_10083.jpg

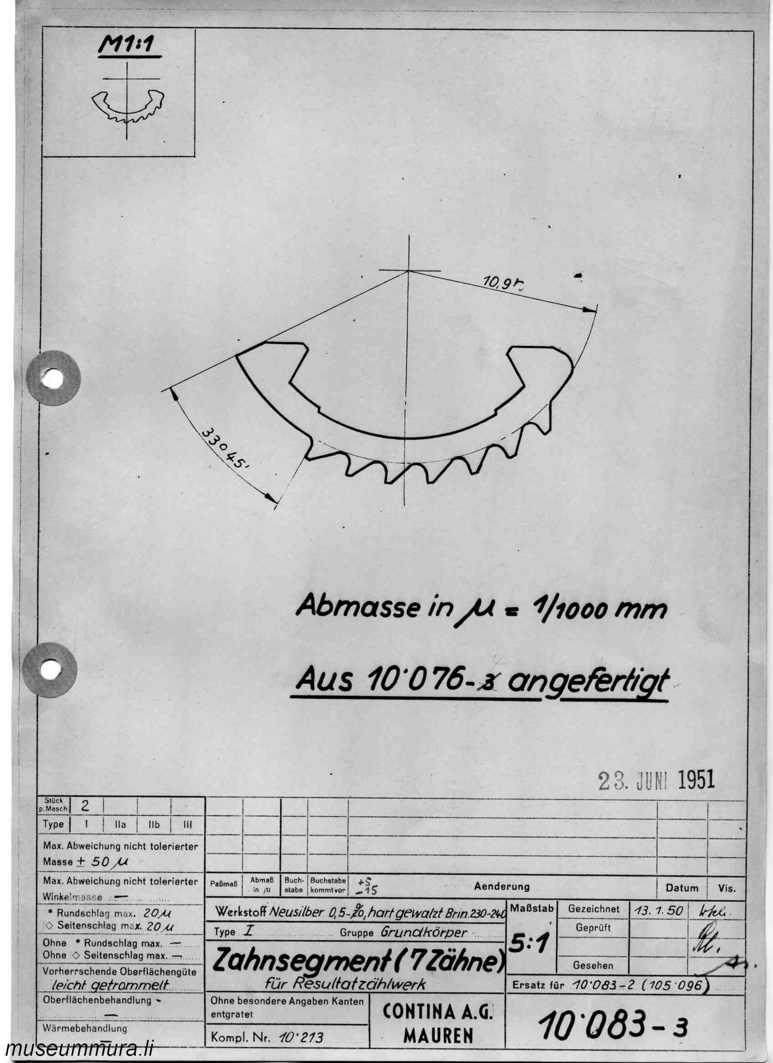
app/curta_jpegs/Curta_1_10083.jpg
