daeken/ReCurta/app/curta_jpegs/Curta_1_10084.jpg

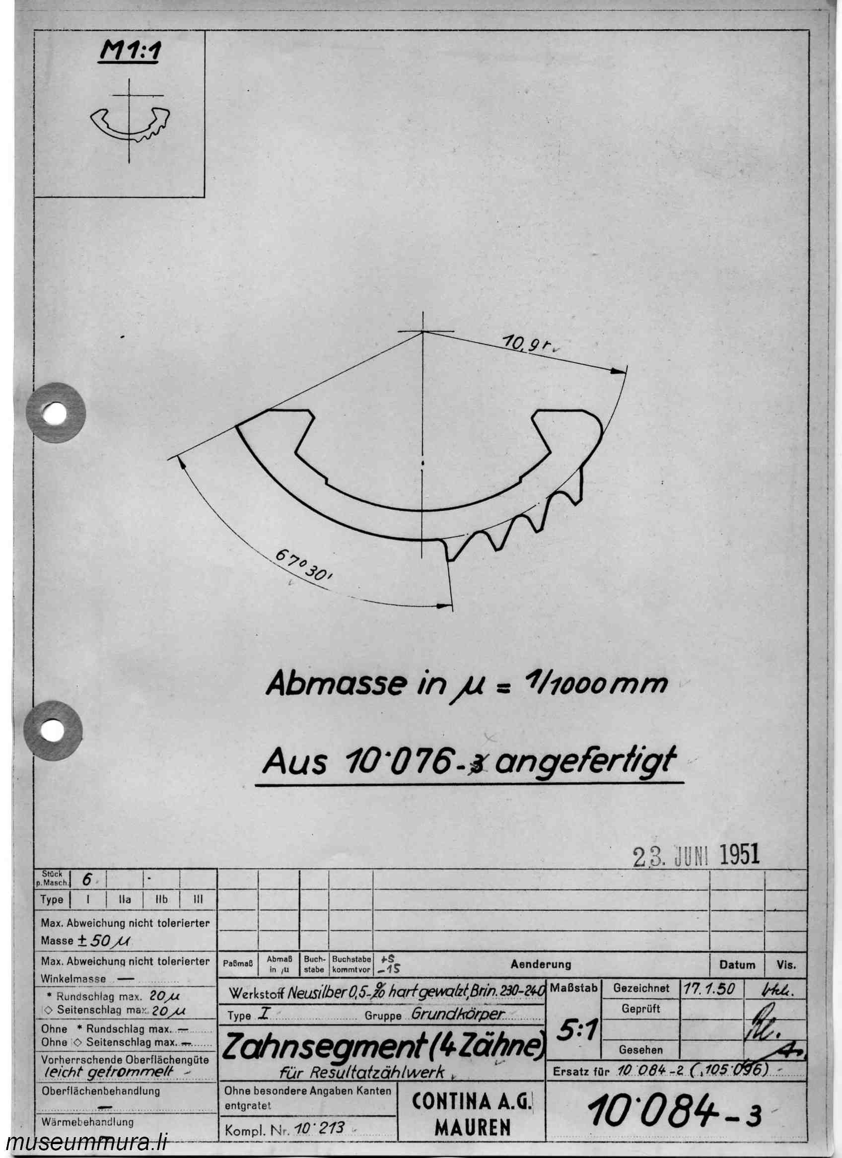
app/curta_jpegs/Curta_1_10084.jpg
