daeken/ReCurta/app/curta_jpegs/Curta_1_10085.jpg

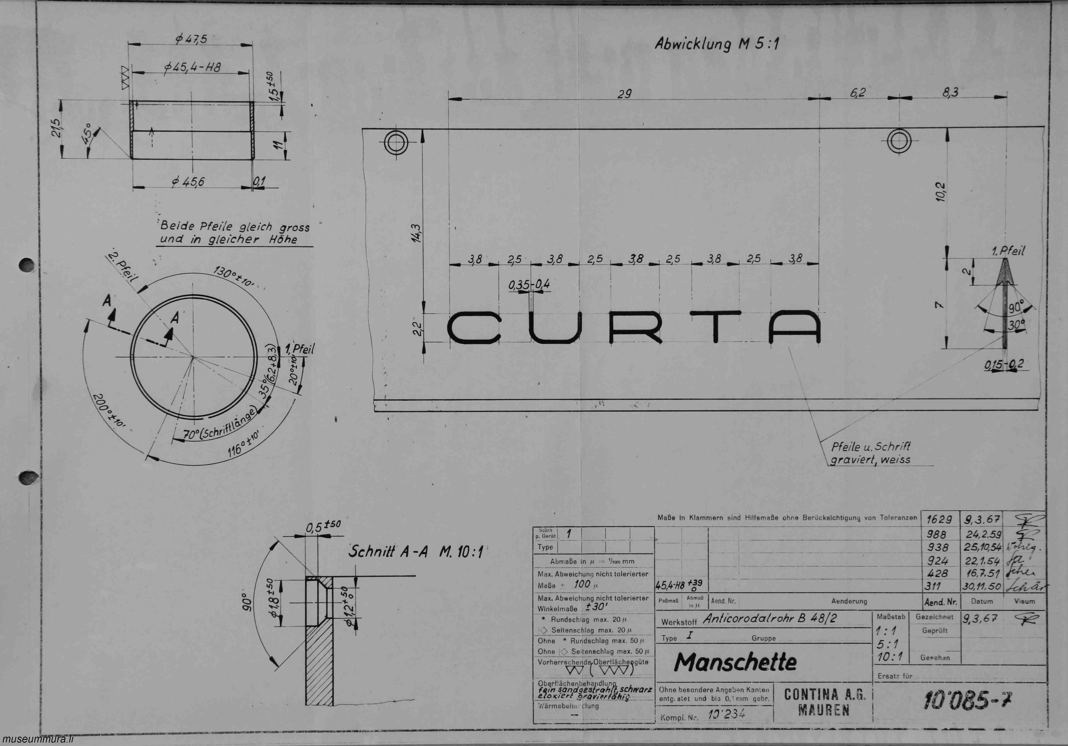
app/curta_jpegs/Curta_1_10085.jpg
