daeken/ReCurta/app/curta_jpegs/Curta_1_10086.jpg

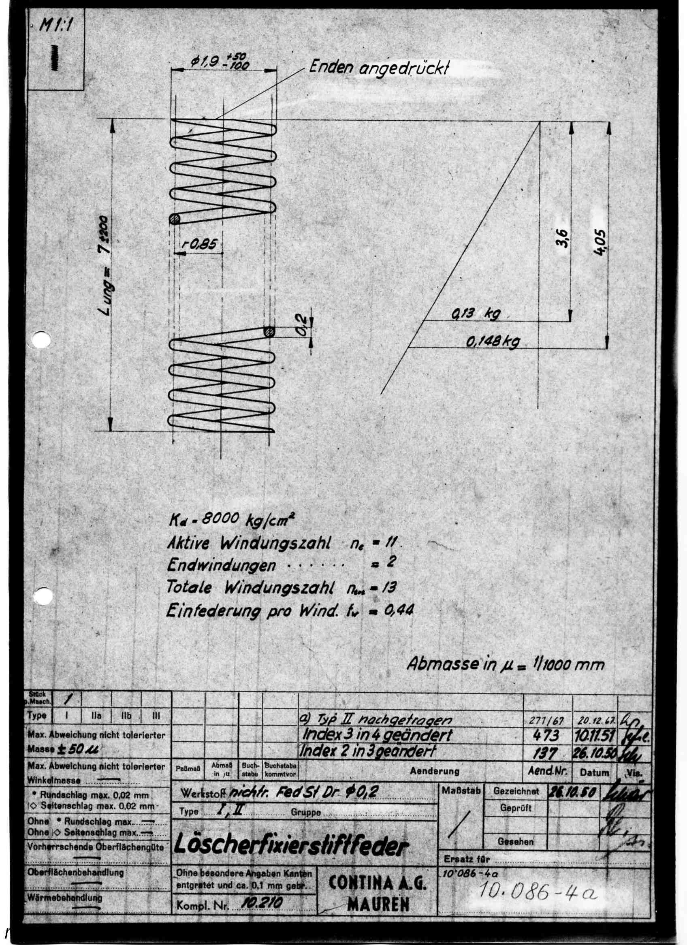
app/curta_jpegs/Curta_1_10086.jpg
