daeken/ReCurta/app/curta_jpegs/Curta_1_10087.jpg

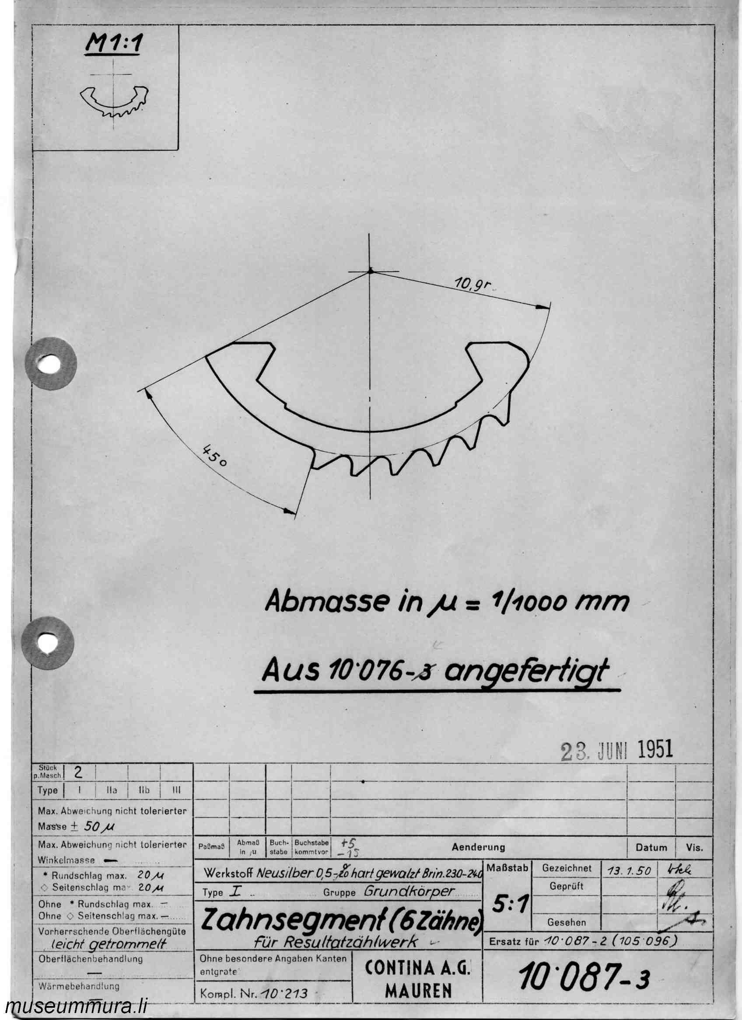
app/curta_jpegs/Curta_1_10087.jpg
