daeken/ReCurta/app/curta_jpegs/Curta_1_10088.jpg

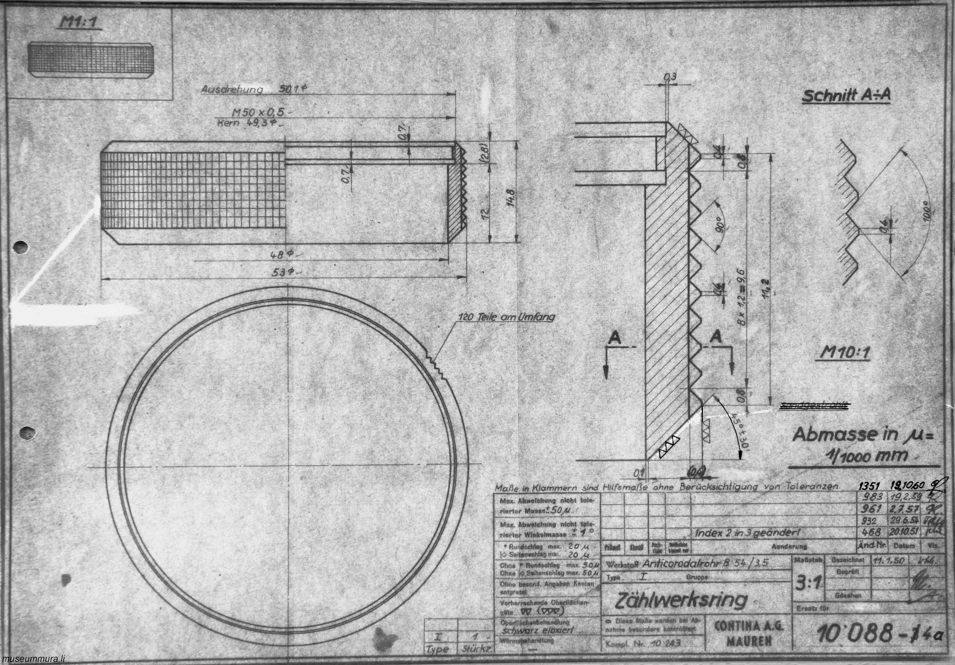
app/curta_jpegs/Curta_1_10088.jpg
