daeken/ReCurta/app/curta_jpegs/Curta_1_10089.jpg

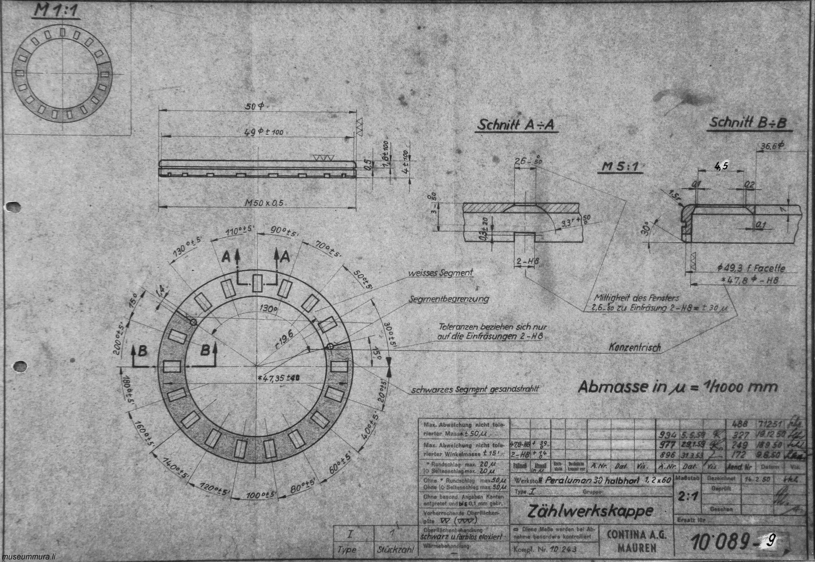
app/curta_jpegs/Curta_1_10089.jpg
