daeken/ReCurta/app/curta_jpegs/Curta_1_10094.jpg

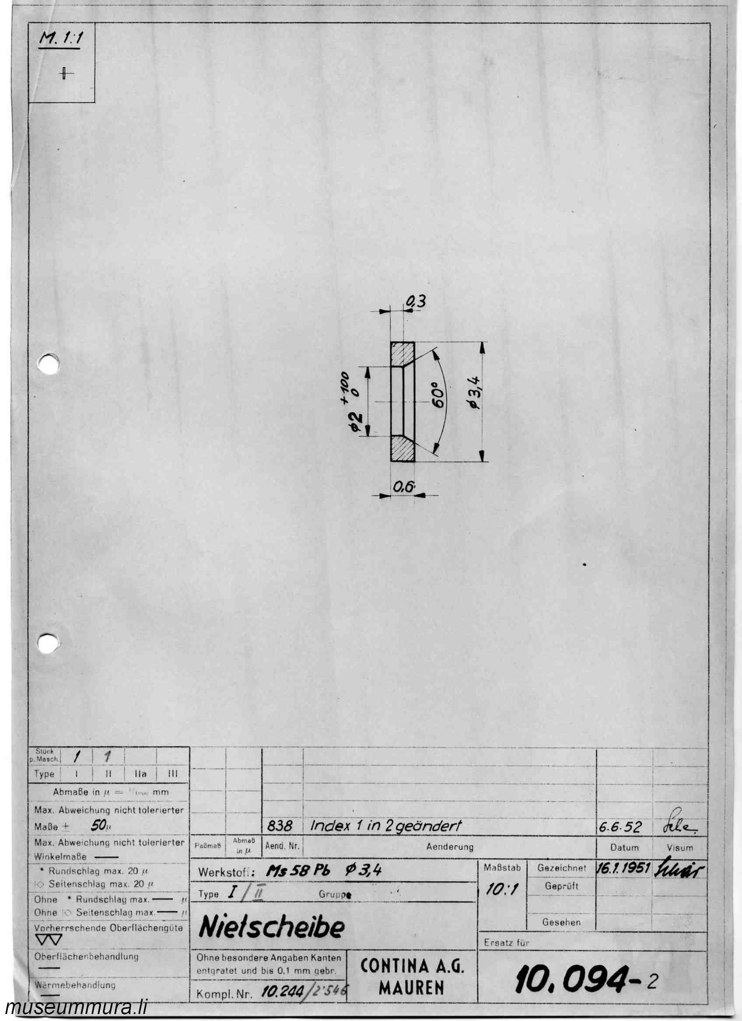
app/curta_jpegs/Curta_1_10094.jpg
