daeken/ReCurta/app/curta_jpegs/Curta_1_10098.jpg

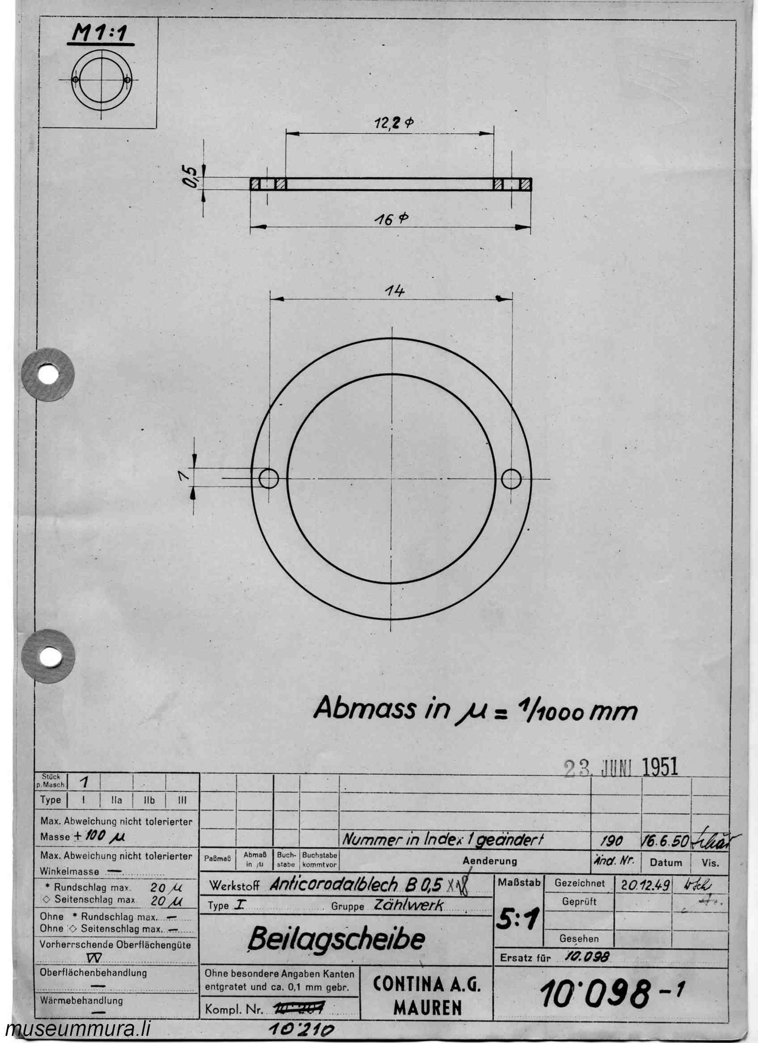
app/curta_jpegs/Curta_1_10098.jpg
