daeken/ReCurta/app/curta_jpegs/Curta_1_10101.jpg

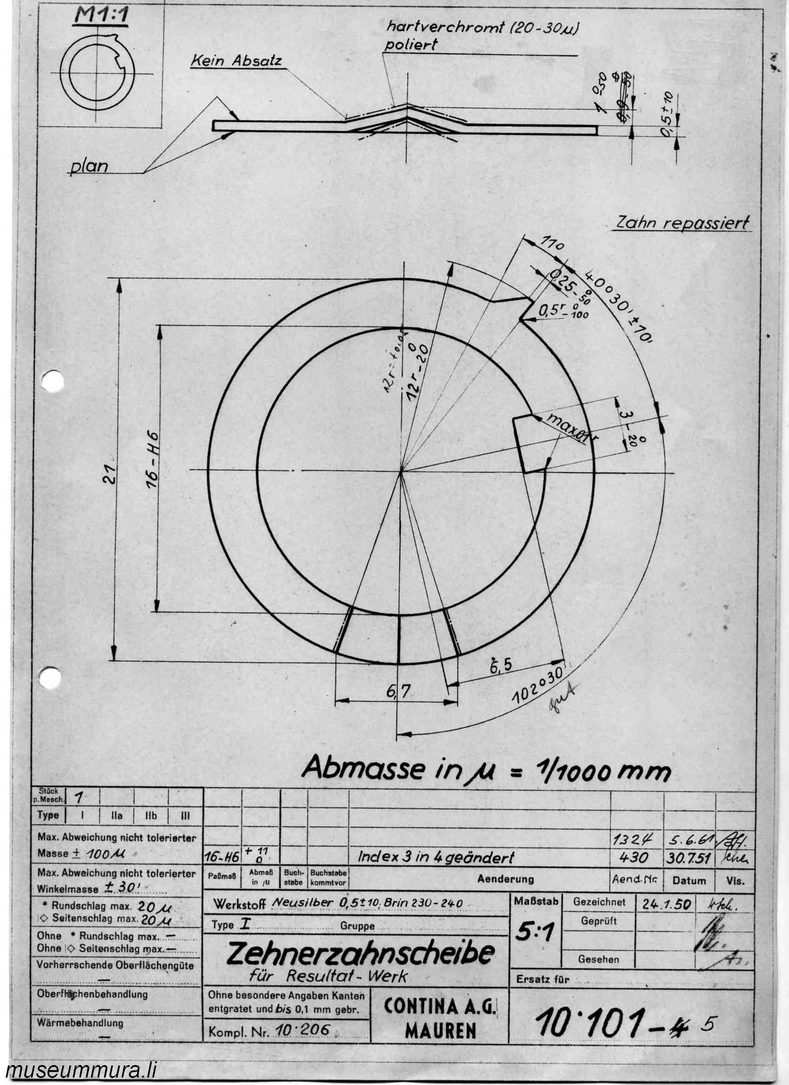
app/curta_jpegs/Curta_1_10101.jpg
