daeken/ReCurta/app/curta_jpegs/Curta_1_10103.jpg

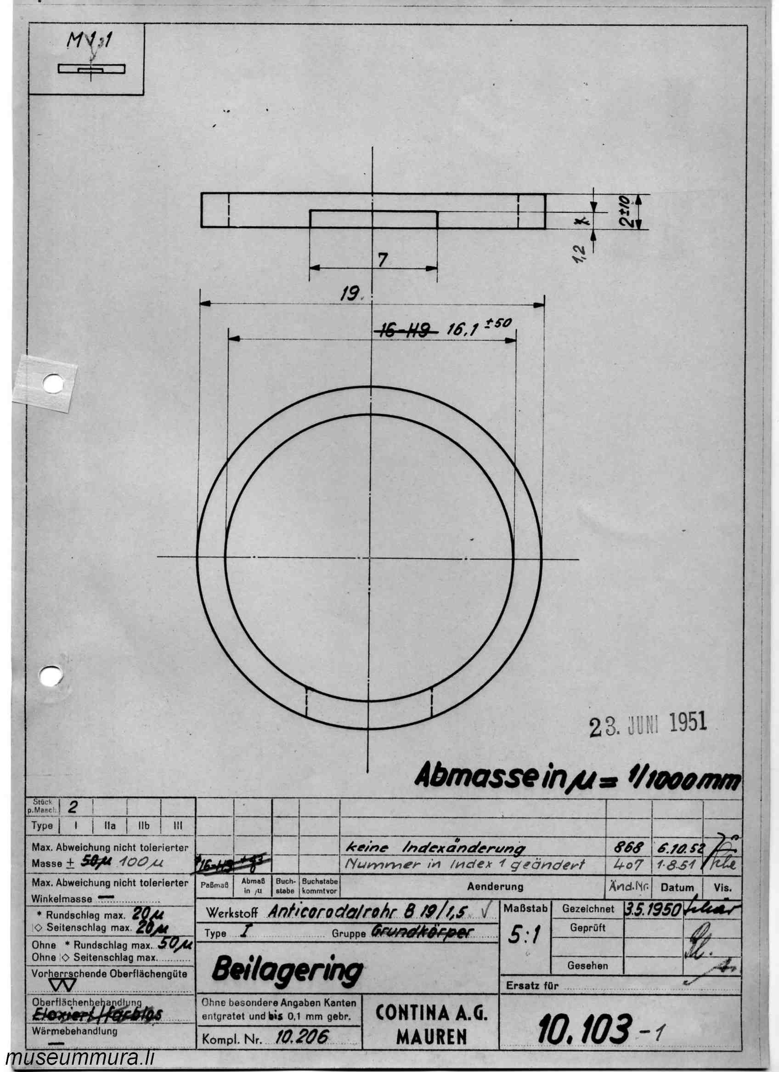
app/curta_jpegs/Curta_1_10103.jpg
