daeken/ReCurta/app/curta_jpegs/Curta_1_10105.jpg

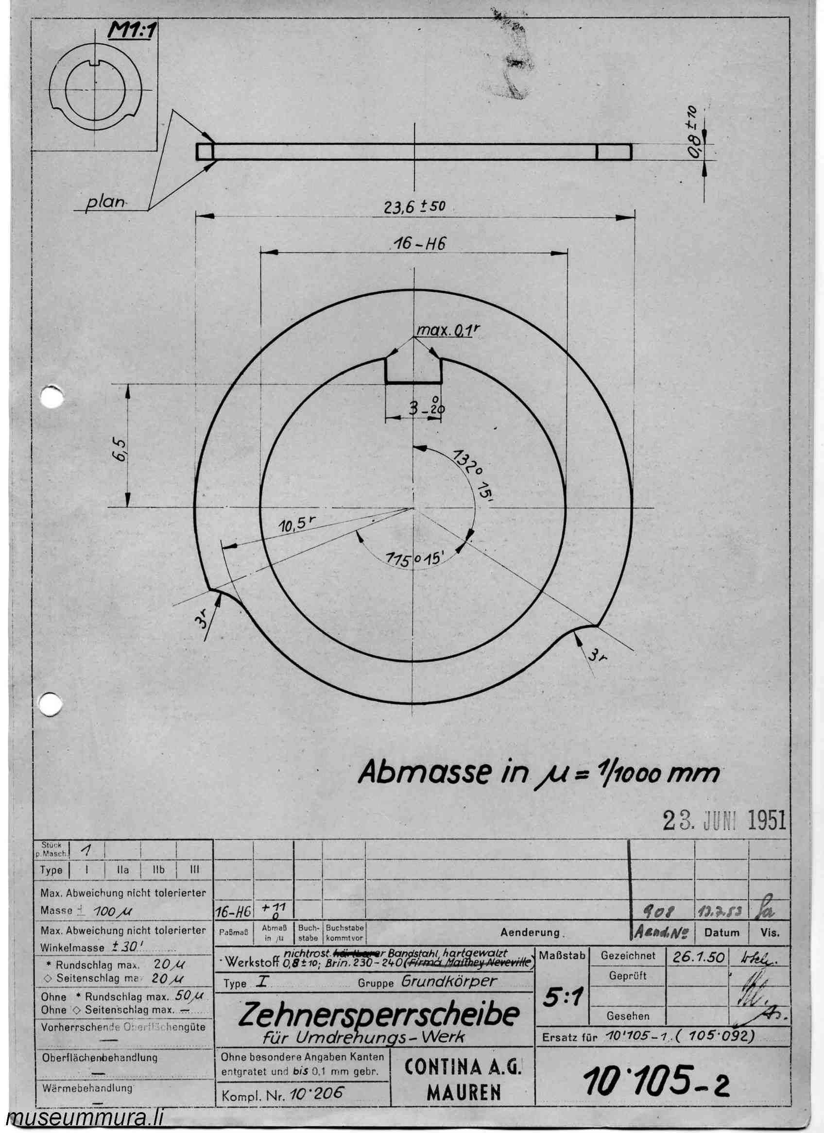
app/curta_jpegs/Curta_1_10105.jpg
