daeken/ReCurta/app/curta_jpegs/Curta_1_10106.jpg

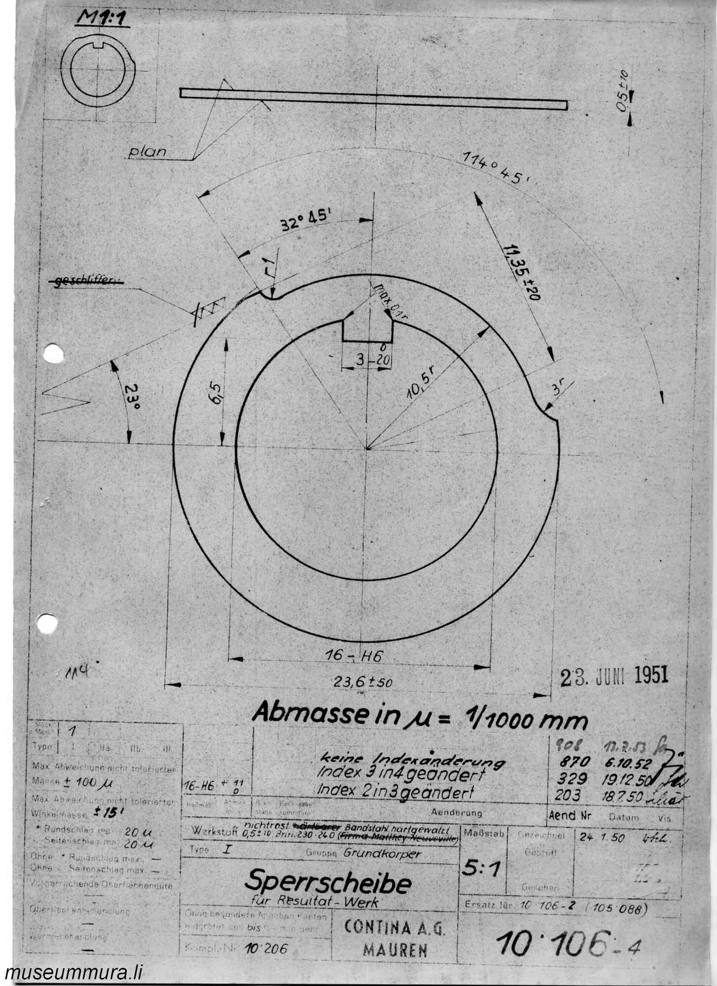
app/curta_jpegs/Curta_1_10106.jpg
