daeken/ReCurta/app/curta_jpegs/Curta_1_10107.jpg

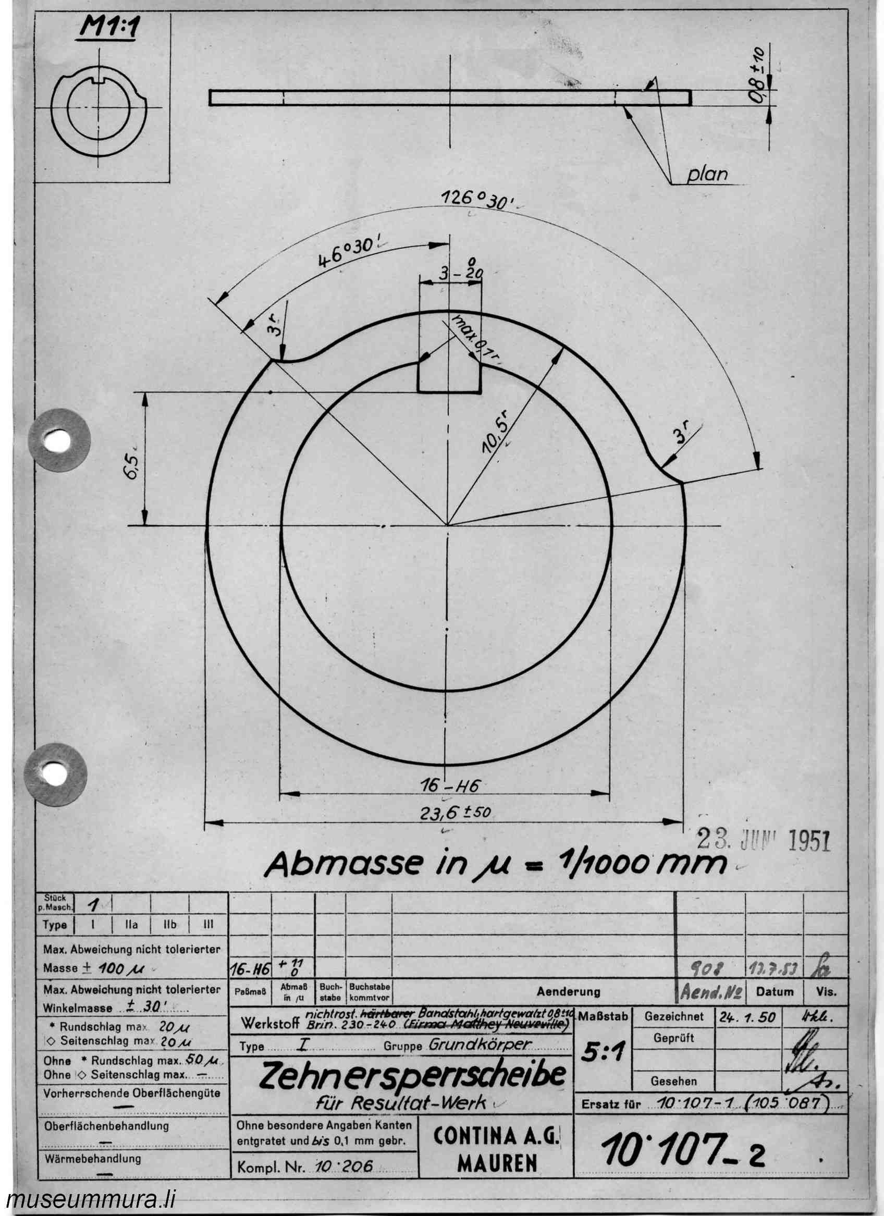
app/curta_jpegs/Curta_1_10107.jpg
