daeken/ReCurta/app/curta_jpegs/Curta_1_10110.jpg

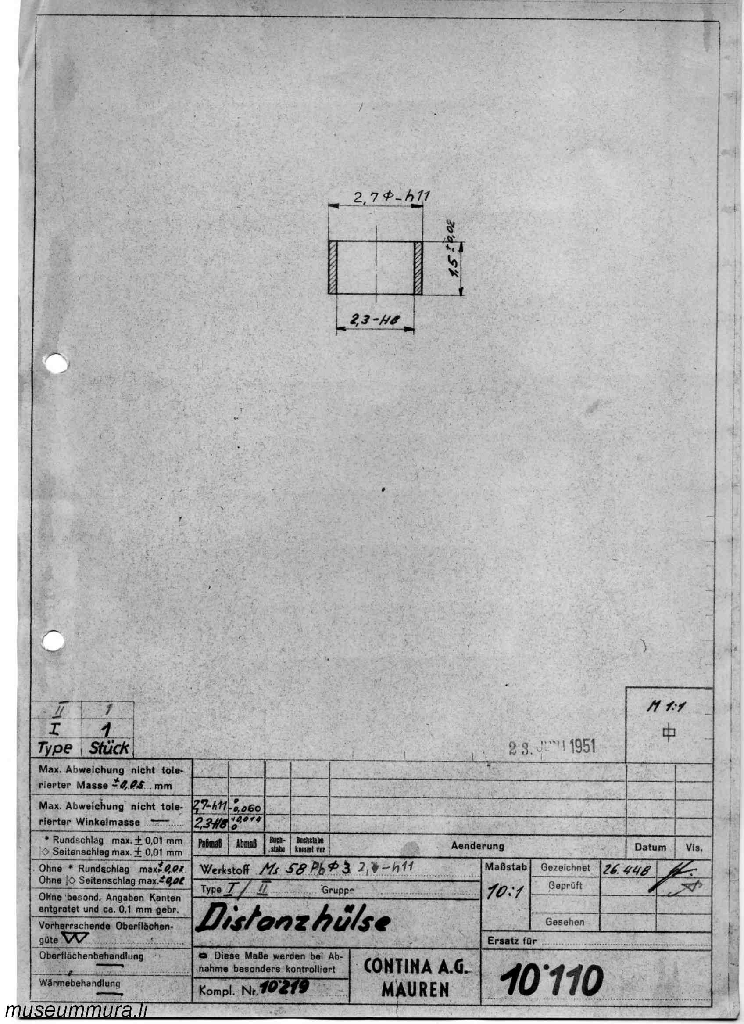
app/curta_jpegs/Curta_1_10110.jpg
