daeken/ReCurta/app/curta_jpegs/Curta_1_10111.jpg

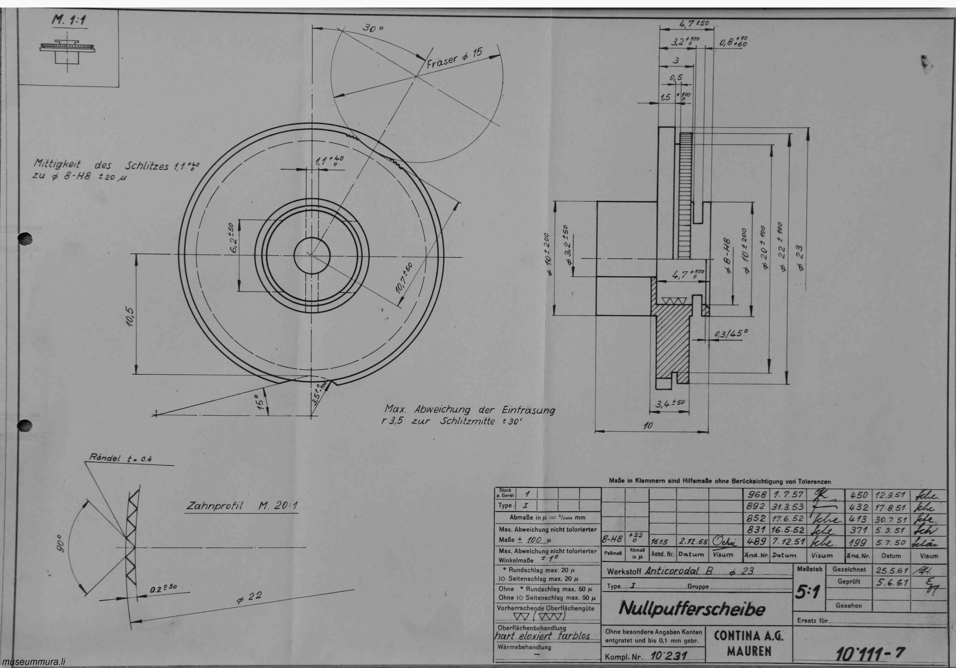
app/curta_jpegs/Curta_1_10111.jpg
