daeken/ReCurta/app/curta_jpegs/Curta_1_10112.jpg

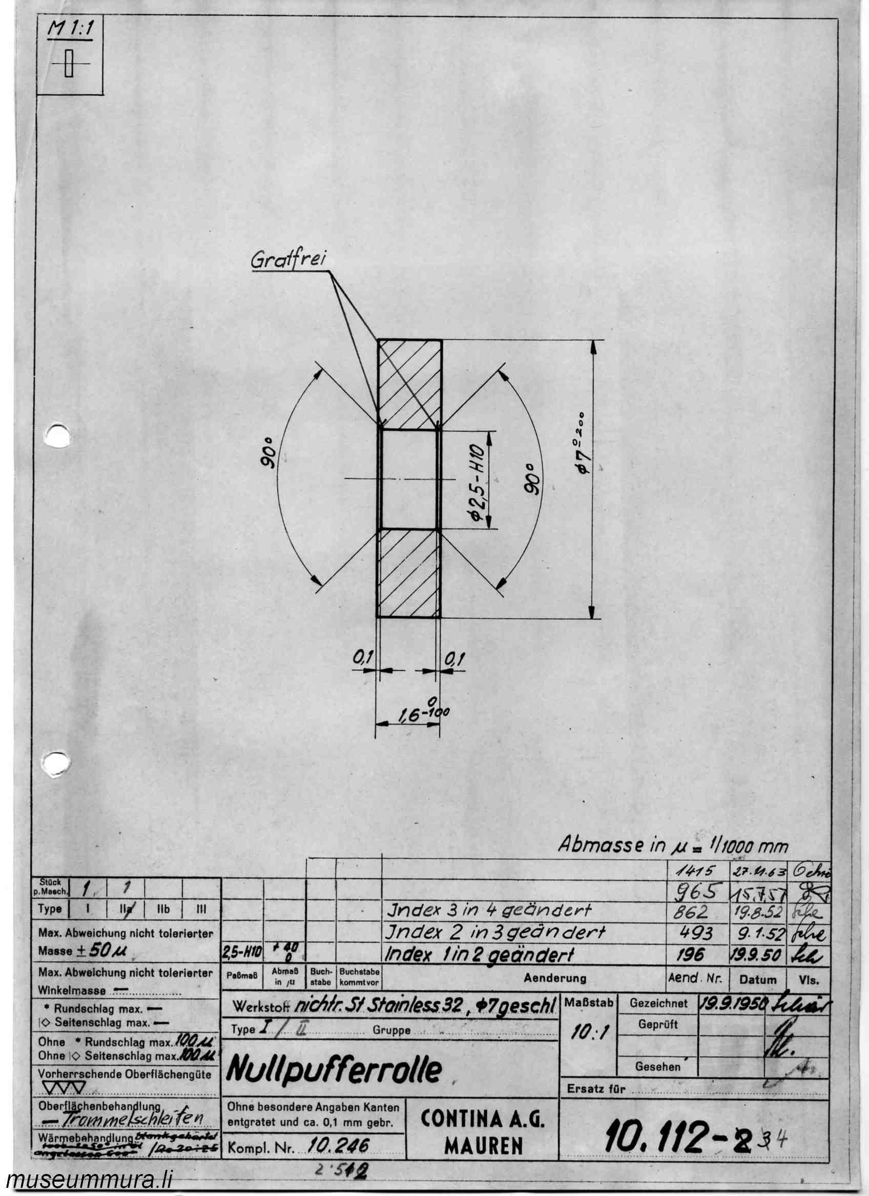
app/curta_jpegs/Curta_1_10112.jpg
