daeken/ReCurta/app/curta_jpegs/Curta_1_10114.jpg

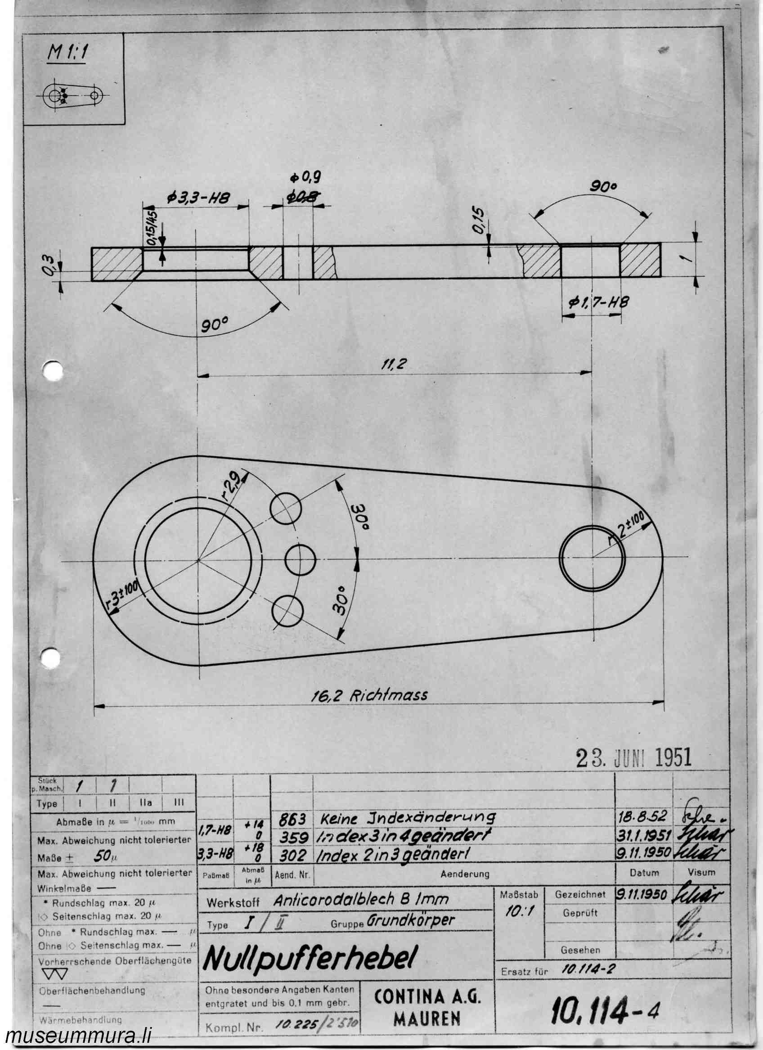
app/curta_jpegs/Curta_1_10114.jpg
