daeken/ReCurta/app/curta_jpegs/Curta_1_10116.jpg

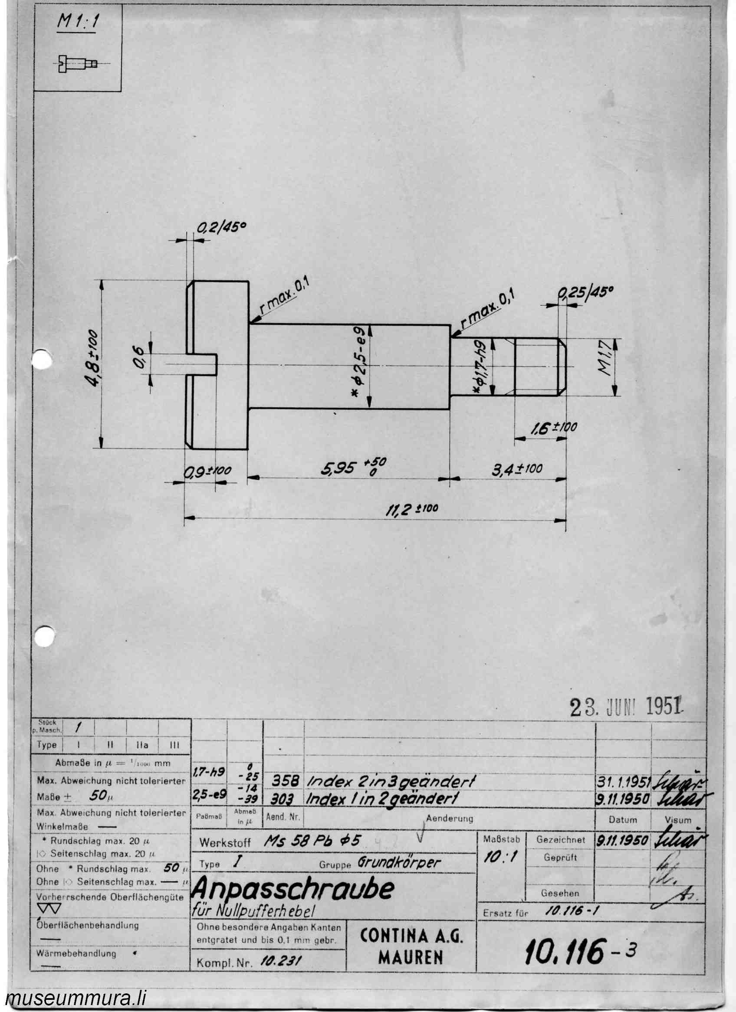
app/curta_jpegs/Curta_1_10116.jpg
