daeken/ReCurta/app/curta_jpegs/Curta_1_10119.jpg

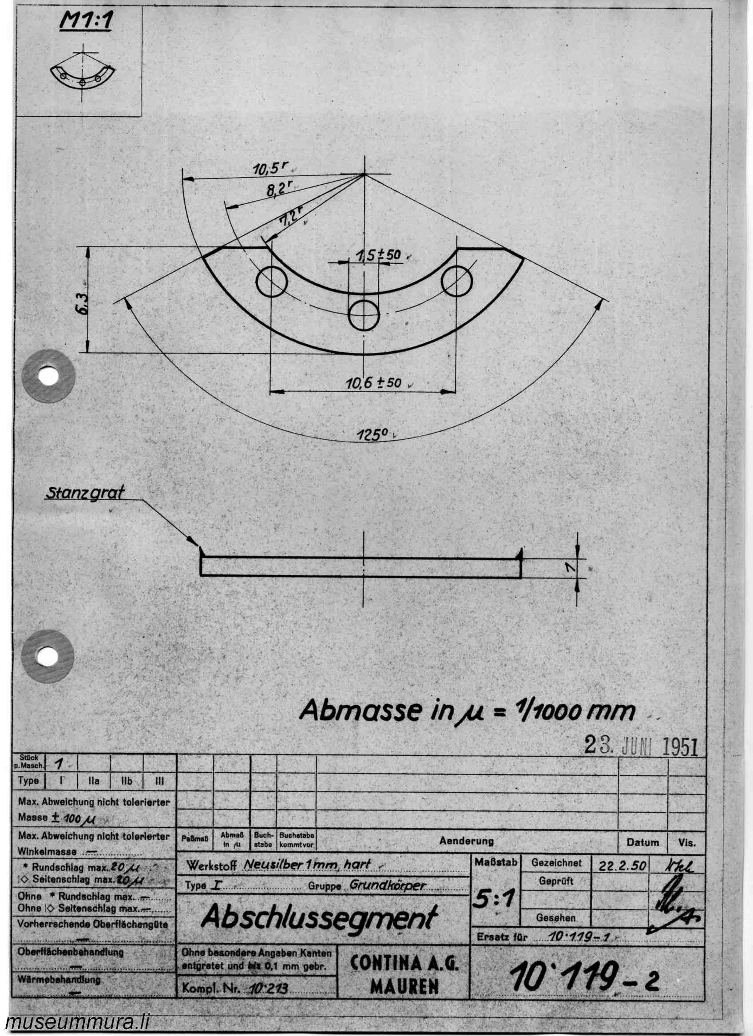
app/curta_jpegs/Curta_1_10119.jpg
