daeken/ReCurta/app/curta_jpegs/Curta_1_10124.jpg

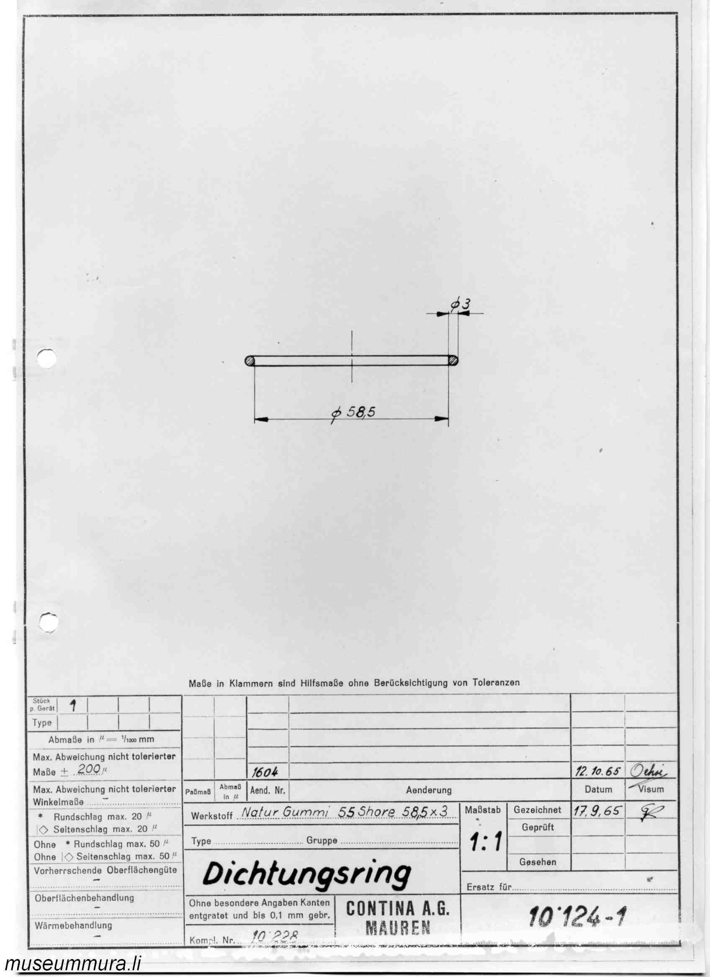
app/curta_jpegs/Curta_1_10124.jpg
