daeken/ReCurta/app/curta_jpegs/Curta_1_10125.jpg

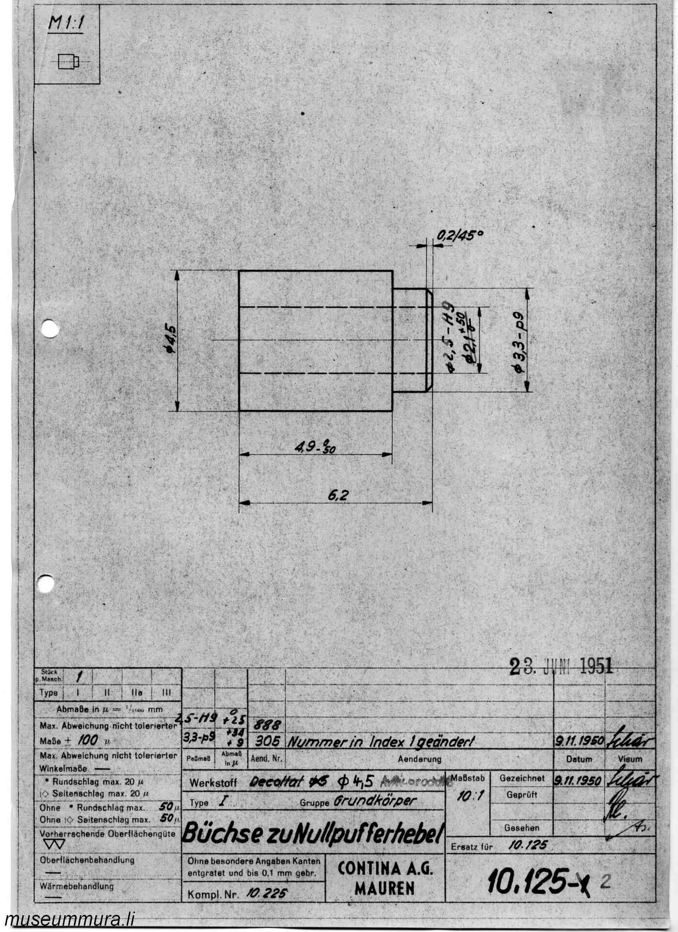
app/curta_jpegs/Curta_1_10125.jpg
