daeken/ReCurta/app/curta_jpegs/Curta_1_10126.jpg

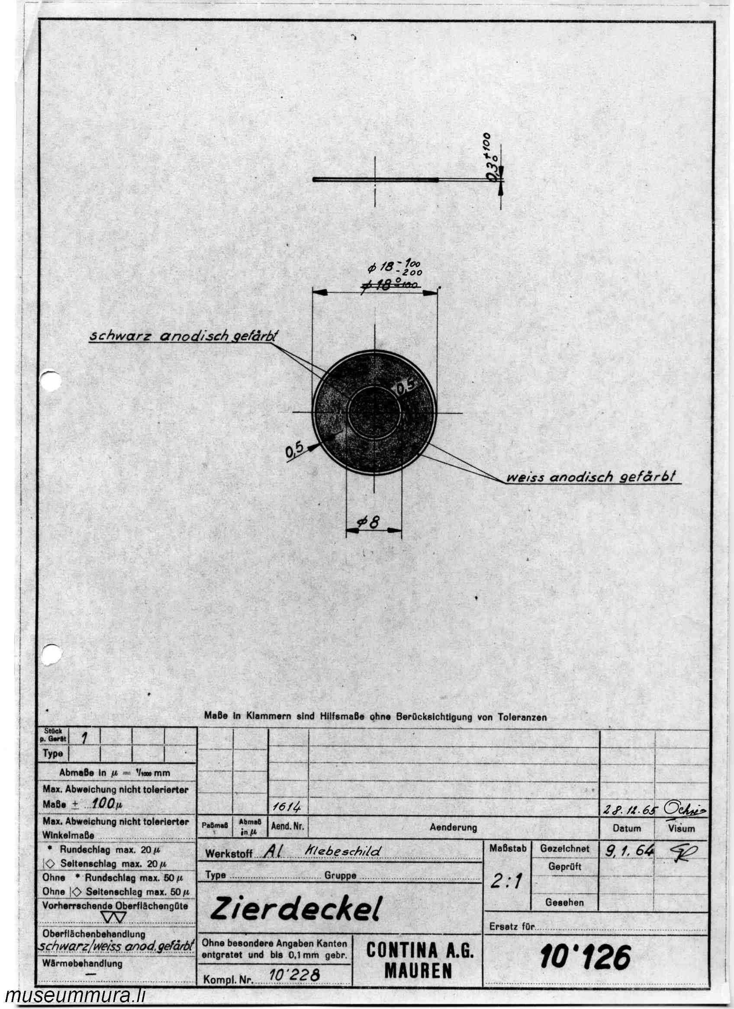
app/curta_jpegs/Curta_1_10126.jpg
