daeken/ReCurta/app/curta_jpegs/Curta_1_10130.jpg

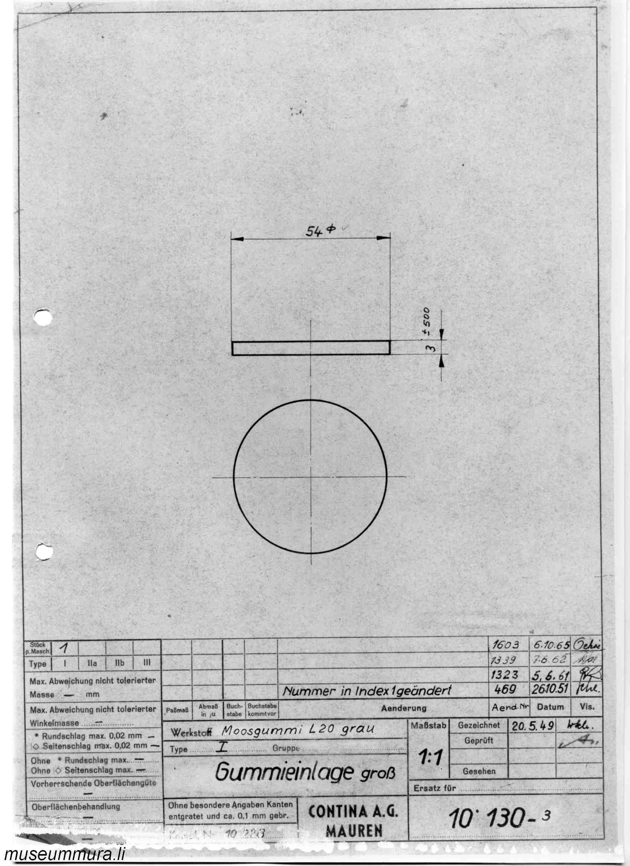
app/curta_jpegs/Curta_1_10130.jpg
