daeken/ReCurta/app/curta_jpegs/Curta_1_10131.jpg

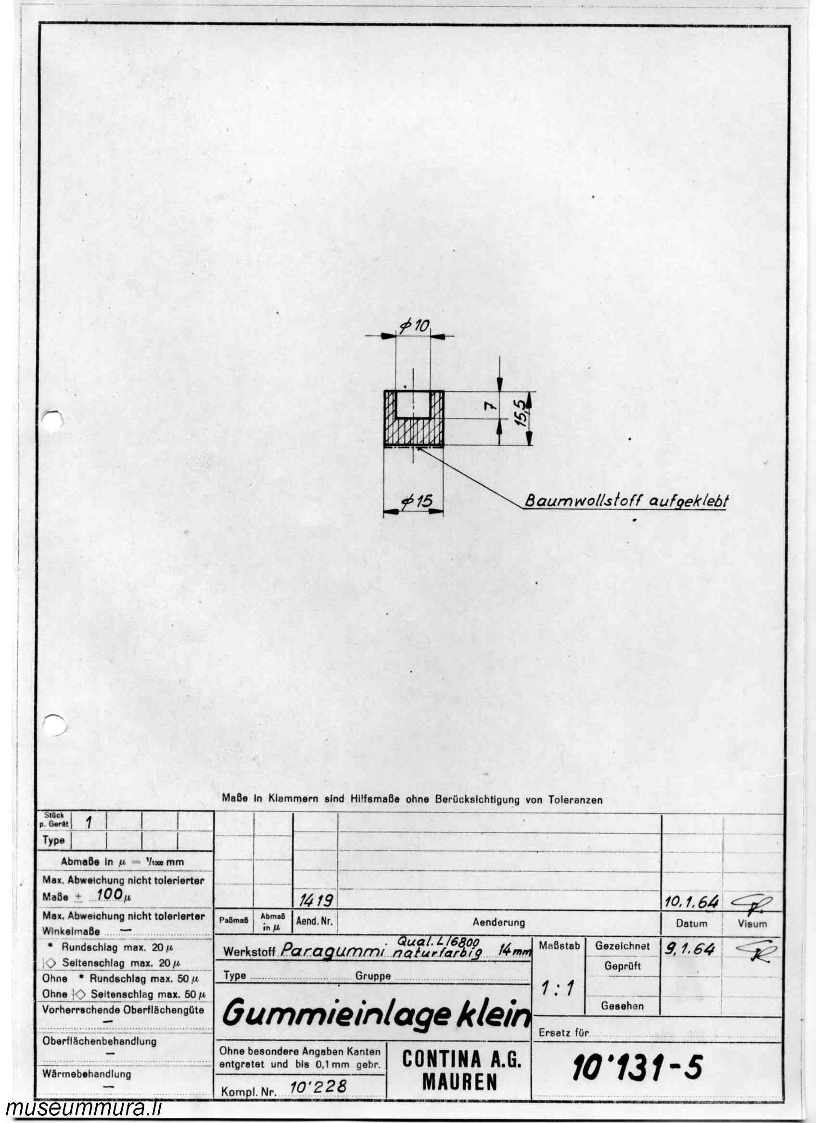
app/curta_jpegs/Curta_1_10131.jpg
