daeken/ReCurta/app/curta_jpegs/Curta_1_10136.jpg

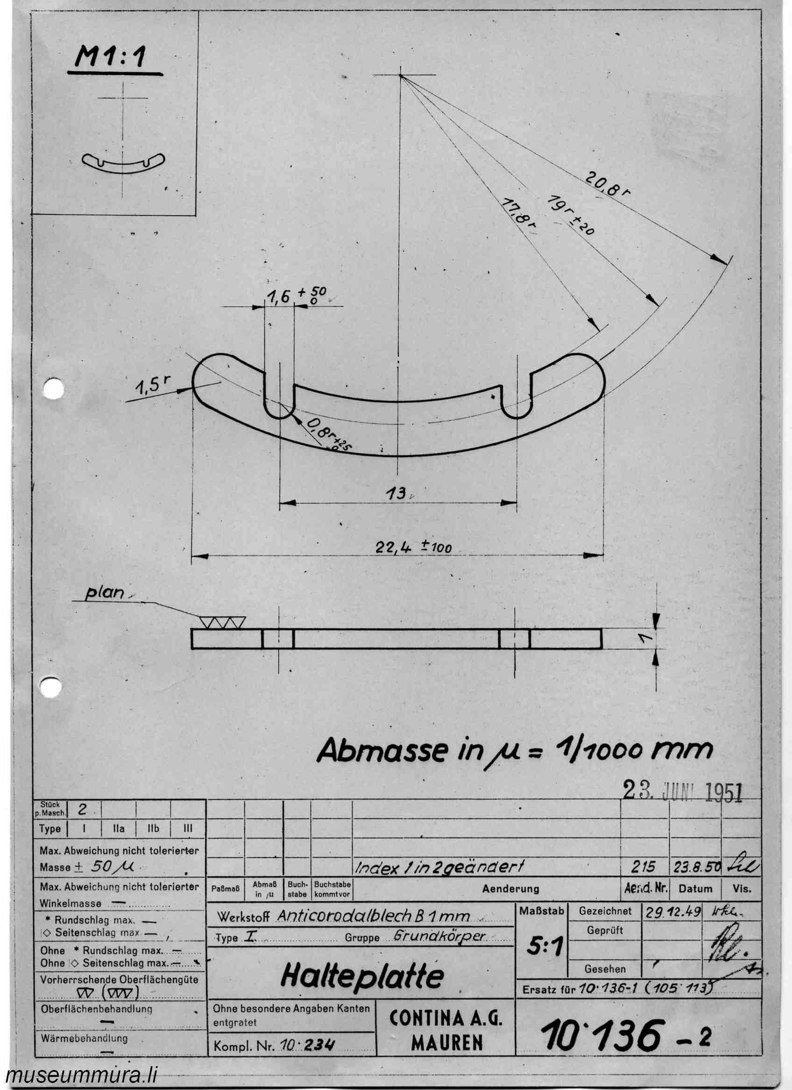
app/curta_jpegs/Curta_1_10136.jpg
