daeken/ReCurta/app/curta_jpegs/Curta_1_10138.jpg

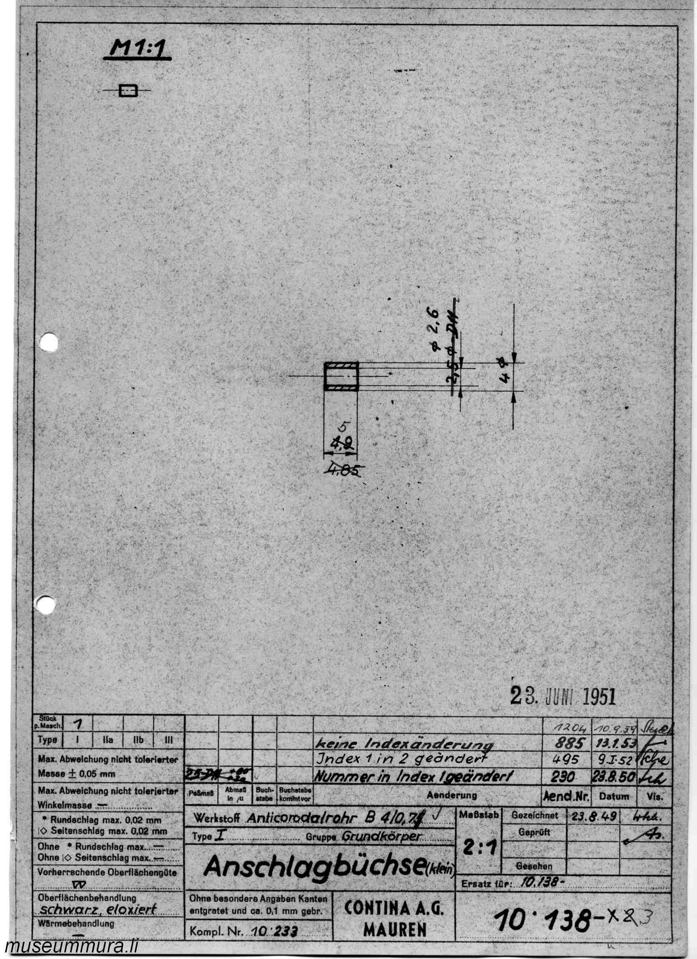
app/curta_jpegs/Curta_1_10138.jpg
