daeken/ReCurta/app/curta_jpegs/Curta_1_10142.jpg

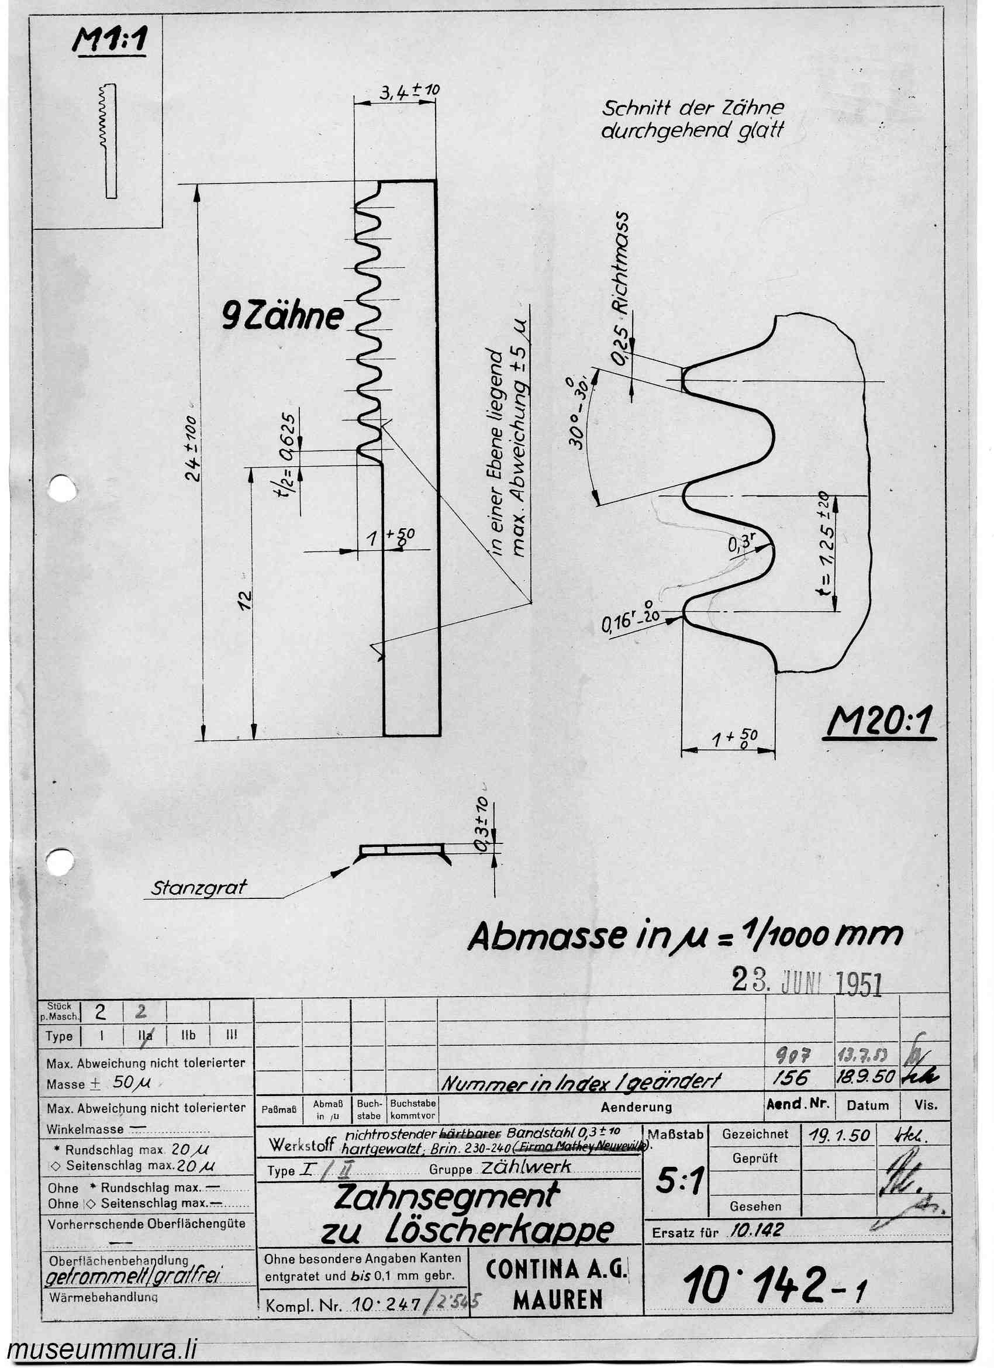
app/curta_jpegs/Curta_1_10142.jpg
