daeken/ReCurta/app/curta_jpegs/Curta_1_10143.jpg

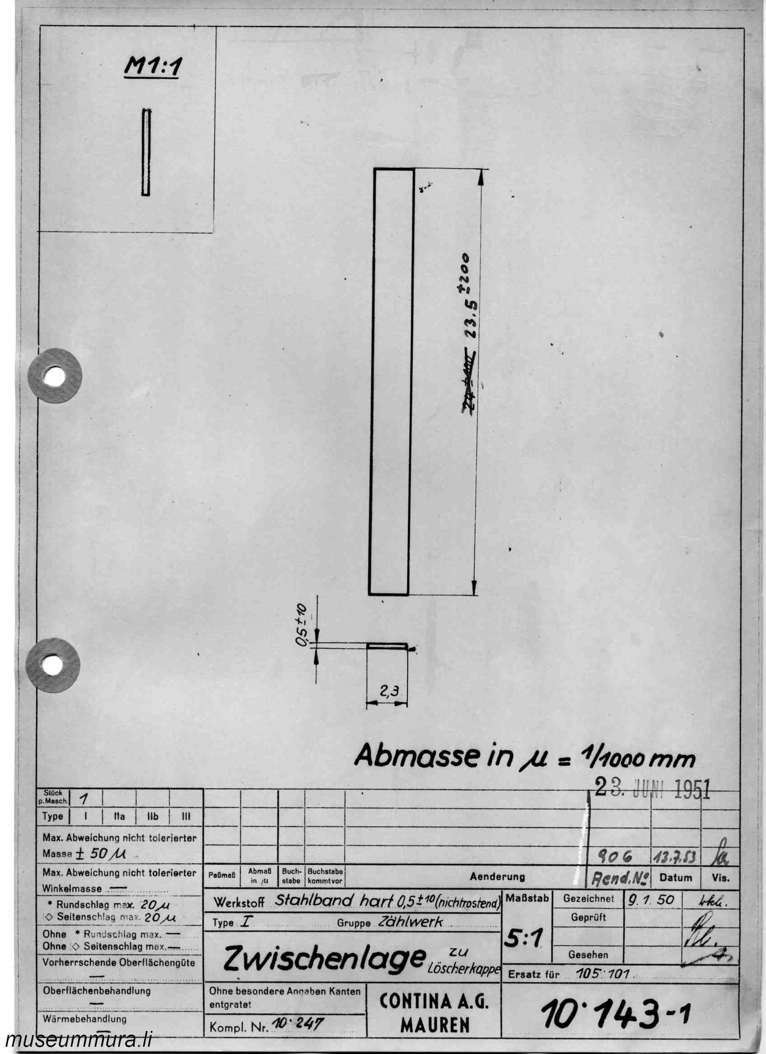
app/curta_jpegs/Curta_1_10143.jpg
