daeken/ReCurta/app/curta_jpegs/Curta_1_10145.jpg

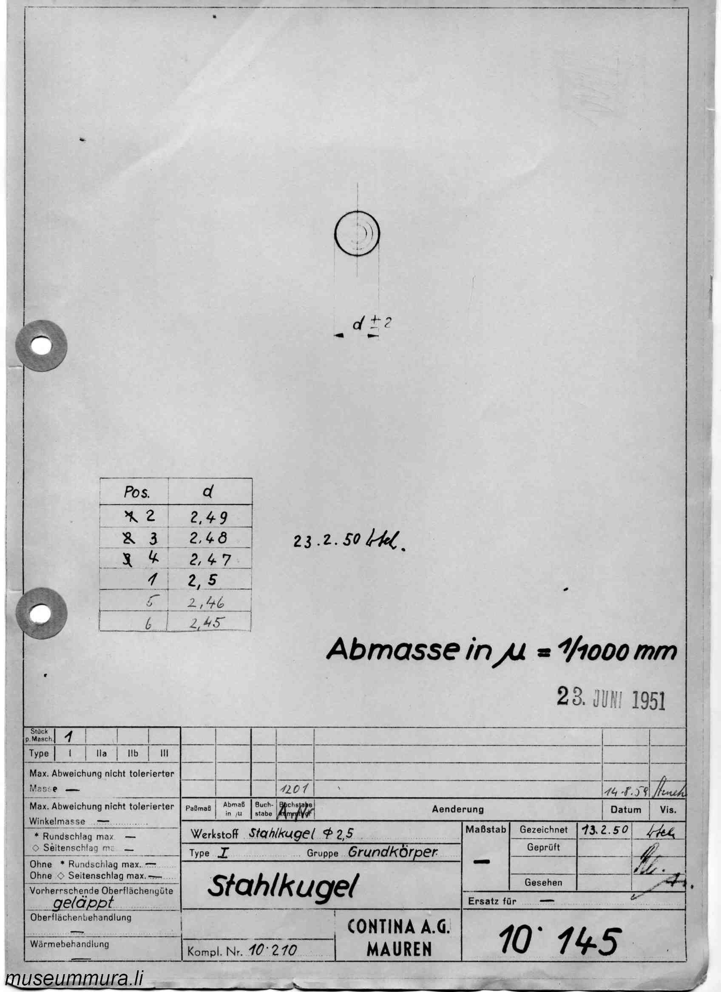
app/curta_jpegs/Curta_1_10145.jpg
