daeken/ReCurta/app/curta_jpegs/Curta_1_10147.jpg

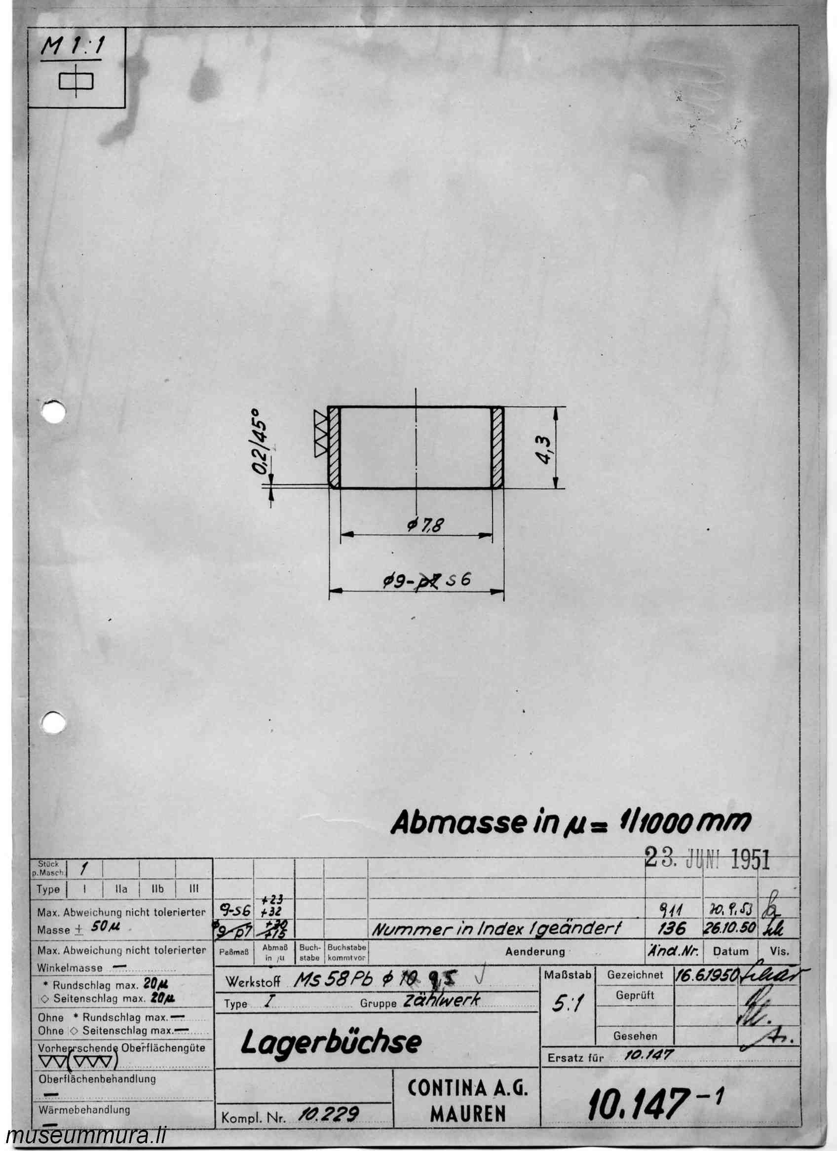
app/curta_jpegs/Curta_1_10147.jpg
