daeken/ReCurta/app/curta_jpegs/Curta_1_10150.jpg

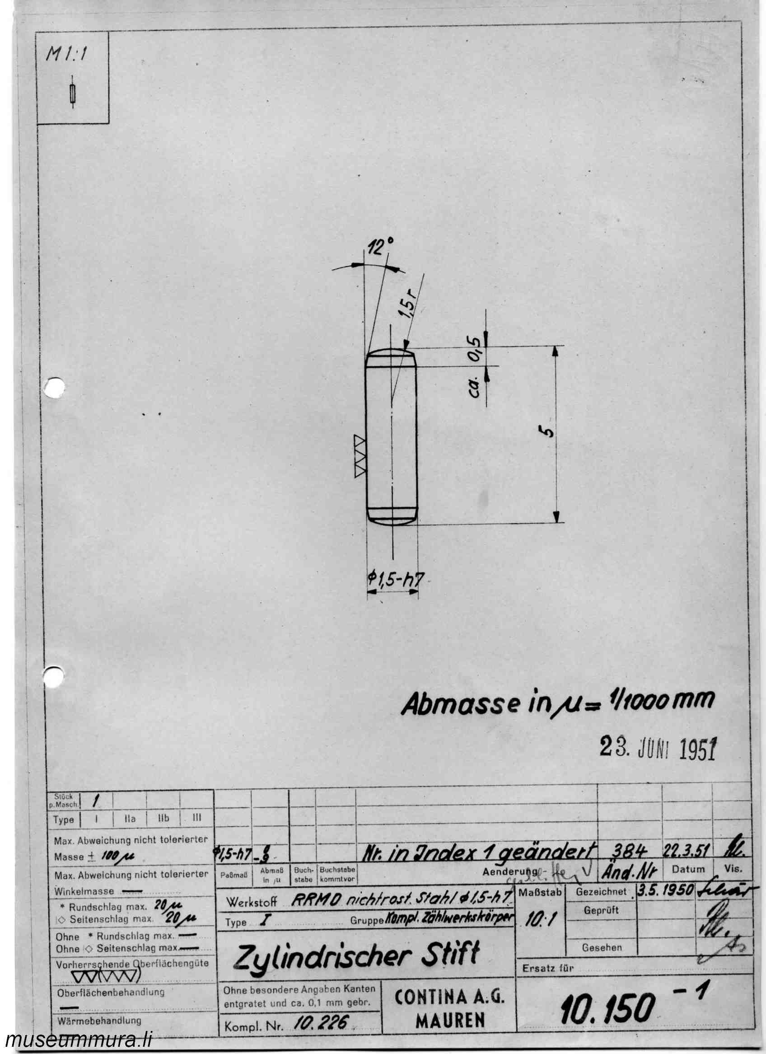
app/curta_jpegs/Curta_1_10150.jpg
