daeken/ReCurta/app/curta_jpegs/Curta_1_10153.jpg

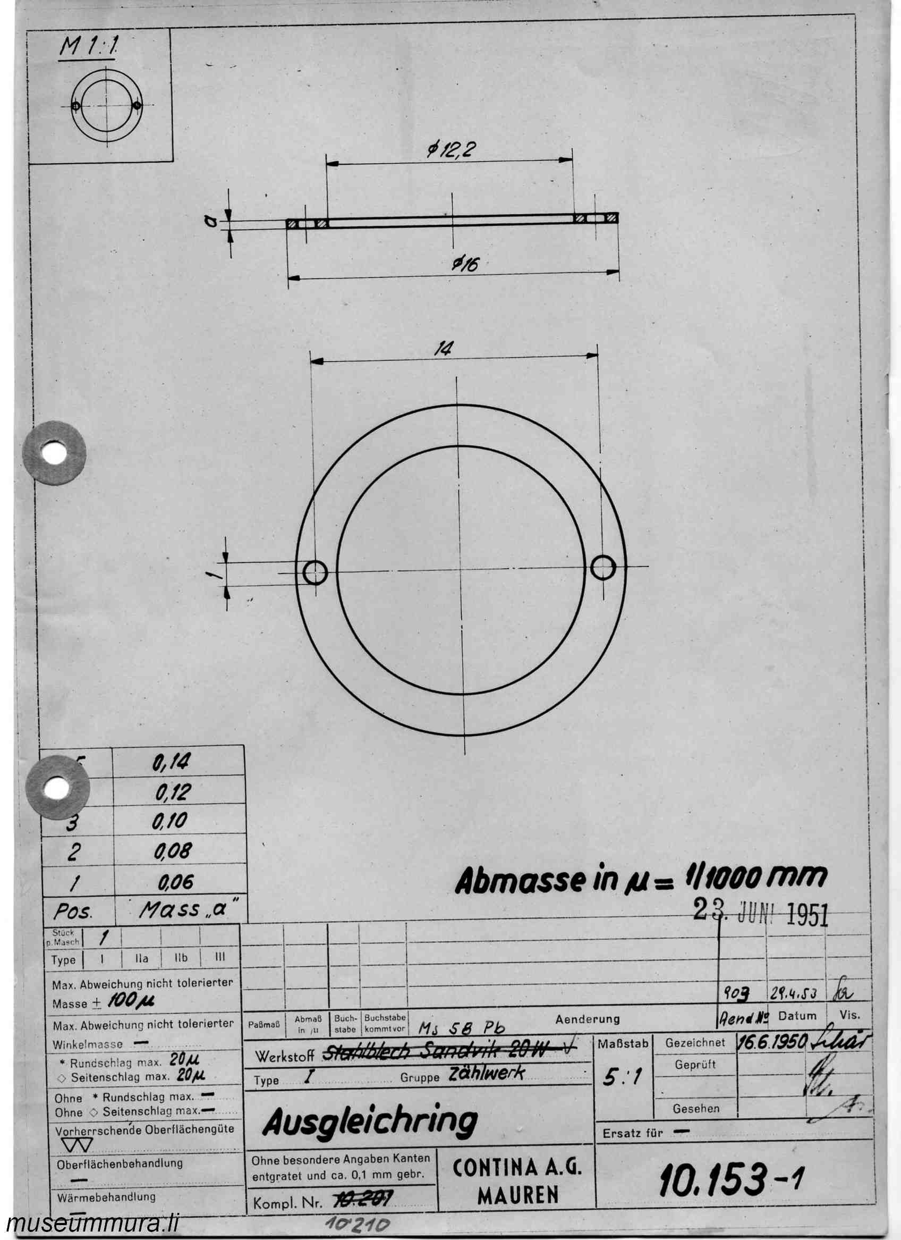
app/curta_jpegs/Curta_1_10153.jpg
