daeken/ReCurta/app/curta_jpegs/Curta_1_10156.jpg

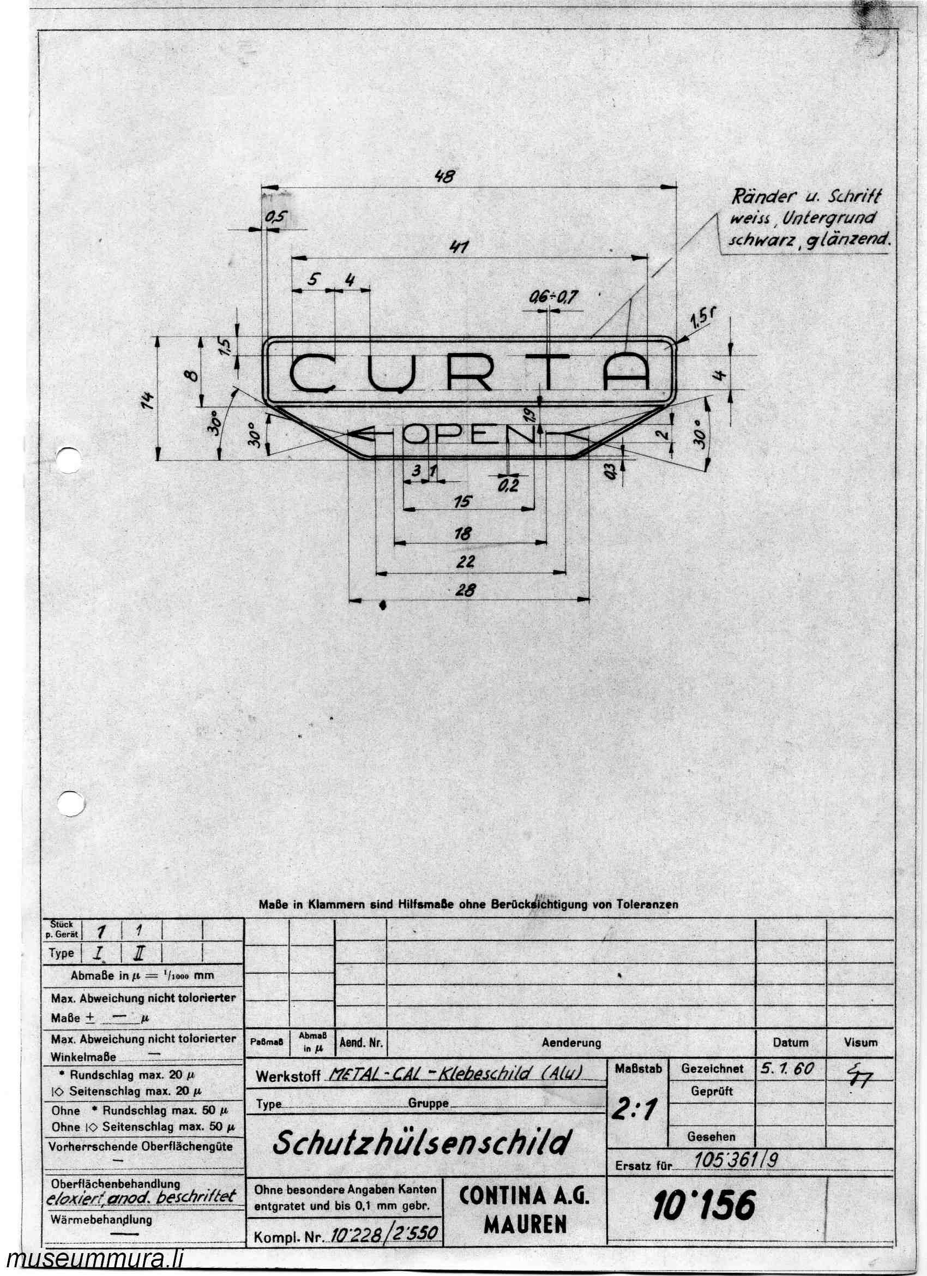
app/curta_jpegs/Curta_1_10156.jpg
