daeken/ReCurta/app/curta_jpegs/Curta_1_10158.jpg

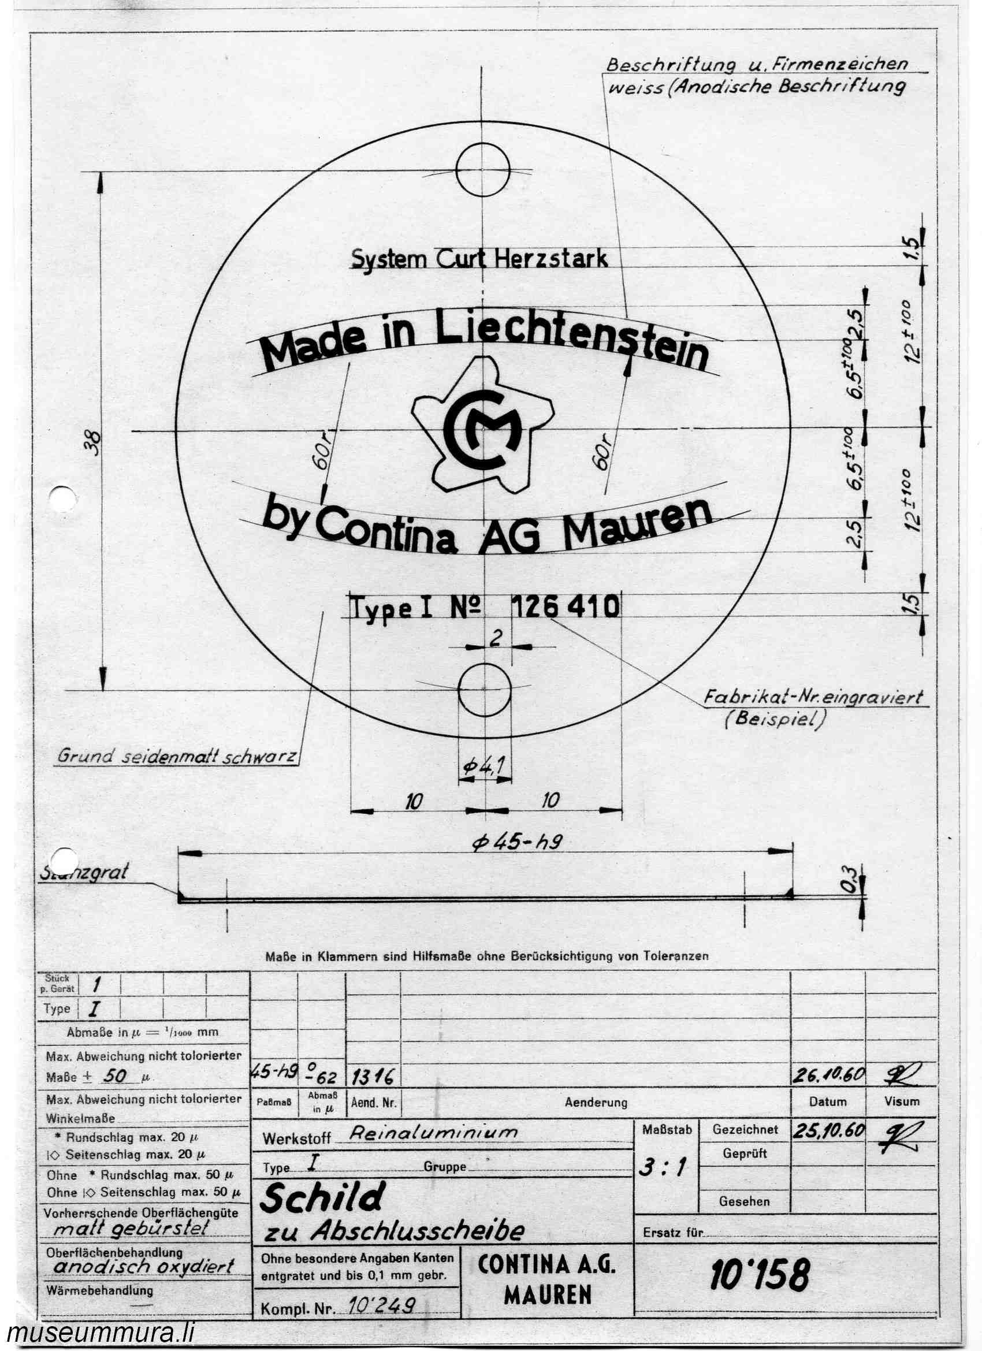
app/curta_jpegs/Curta_1_10158.jpg
