daeken/ReCurta/app/curta_jpegs/Curta_1_10162.jpg

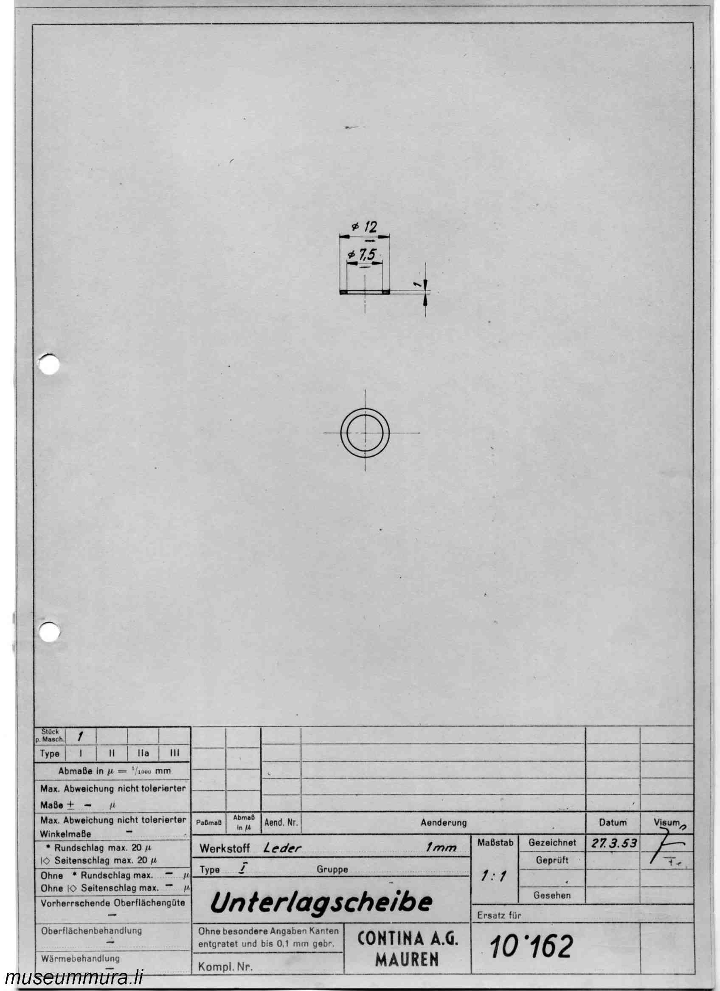
app/curta_jpegs/Curta_1_10162.jpg
