daeken/ReCurta/reference-photo/IMG_1038.jpg

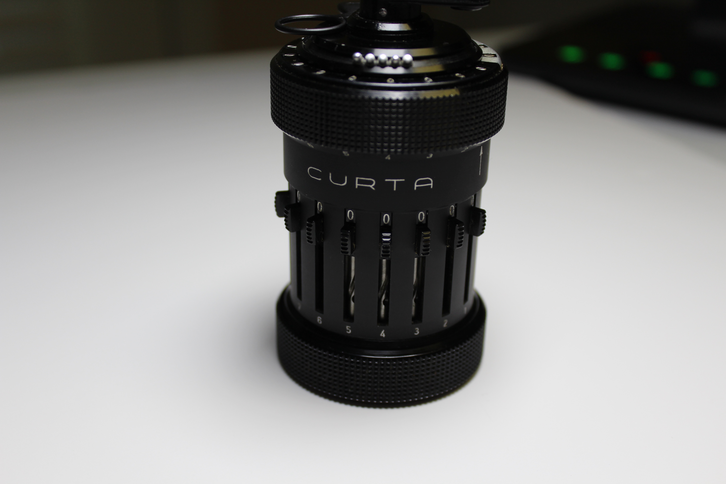
reference-photo/IMG_1038.jpg
