daeken/ReCurta/reference-photo/IMG_1040.jpg

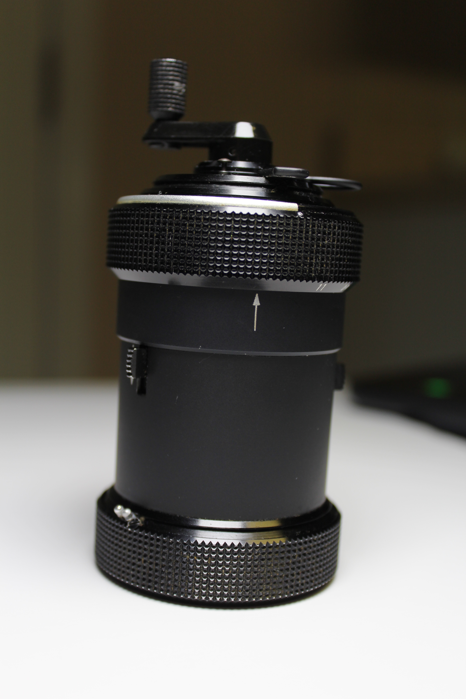
reference-photo/IMG_1040.jpg
