daeken/ReCurta/reference-photo/IMG_1043.jpg

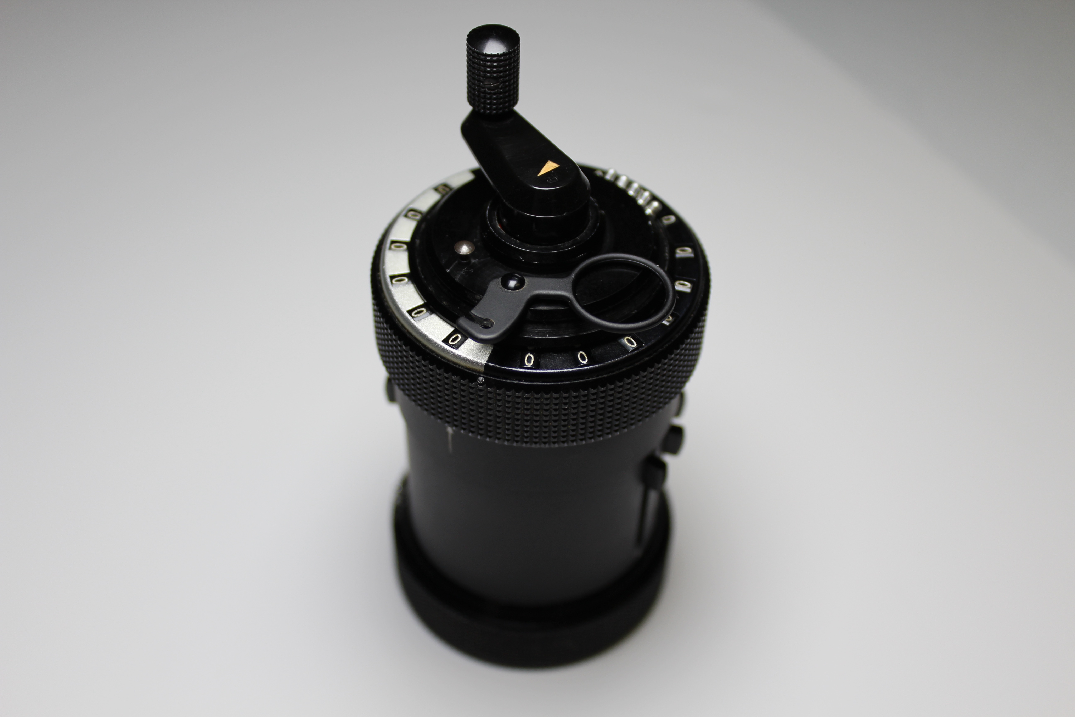
reference-photo/IMG_1043.jpg
