daeken/ReCurta/reference-photo/IMG_1048.jpg

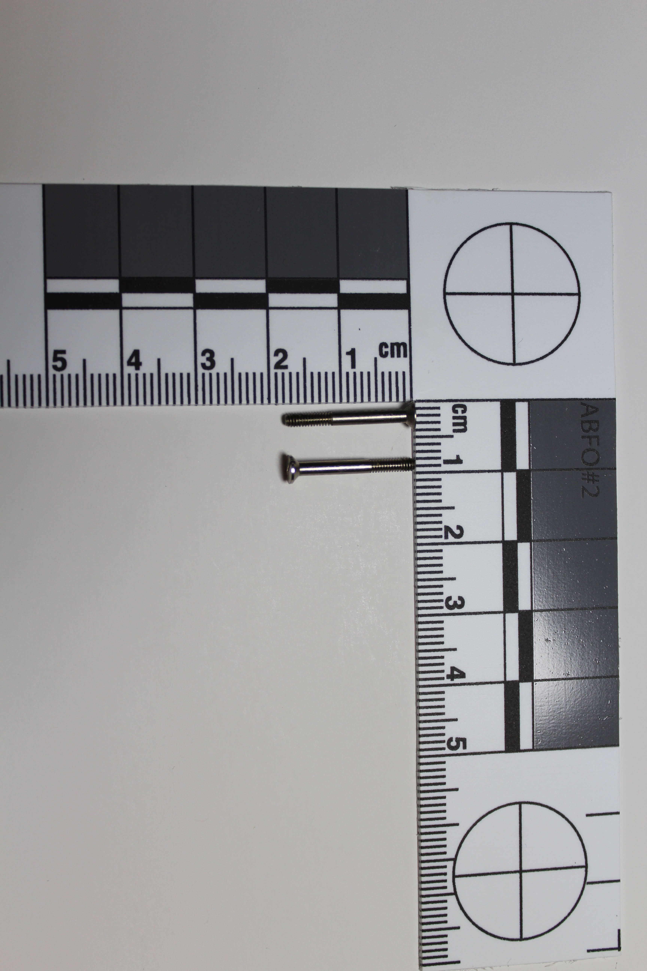
reference-photo/IMG_1048.jpg
