daeken/ReCurta/reference-photo/IMG_1049.jpg

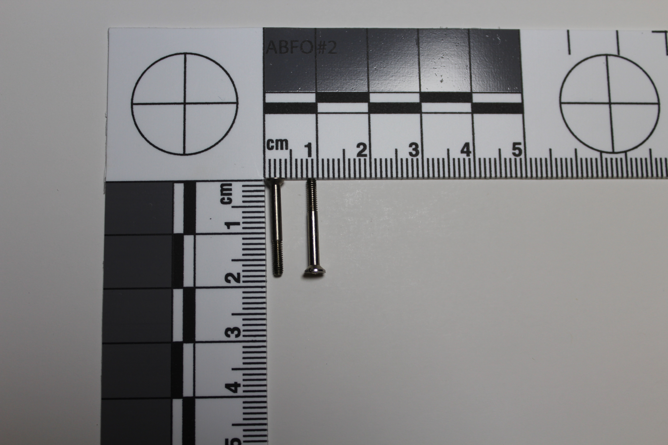
reference-photo/IMG_1049.jpg
