daeken/ReCurta/reference-photo/IMG_1050.jpg

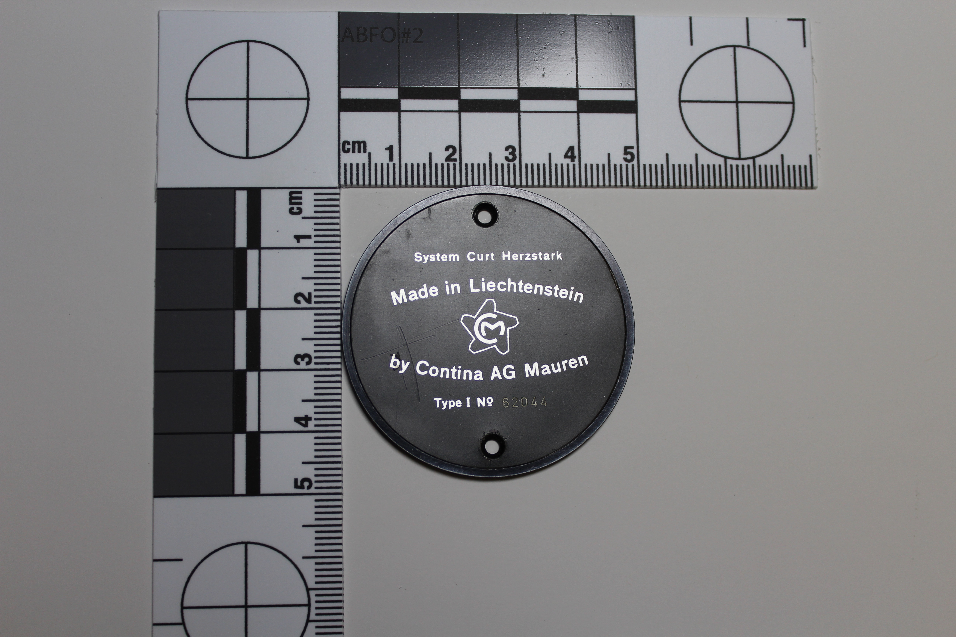
reference-photo/IMG_1050.jpg
