daeken/ReCurta/reference-photo/IMG_1051.jpg

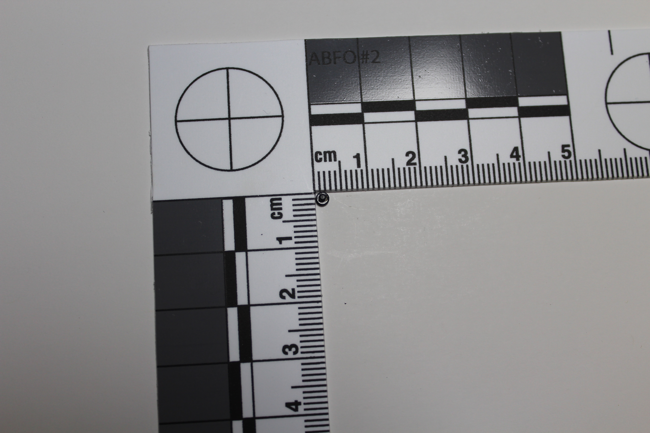
reference-photo/IMG_1051.jpg
