daeken/ReCurta/reference-photo/IMG_1054.jpg

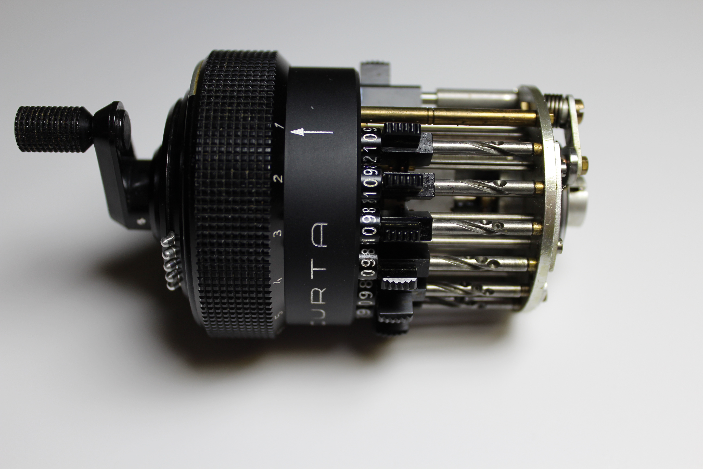
reference-photo/IMG_1054.jpg
