daeken/ReCurta/reference-photo/IMG_1055.jpg

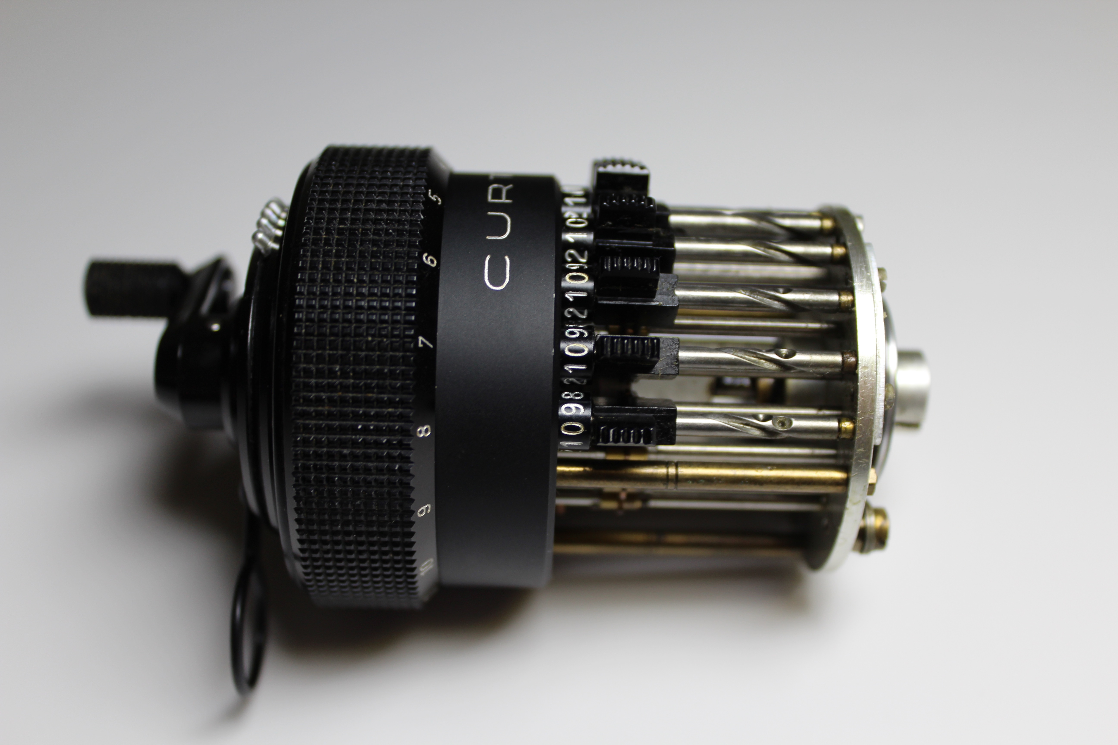
reference-photo/IMG_1055.jpg
