daeken/ReCurta/reference-photo/IMG_1056.jpg

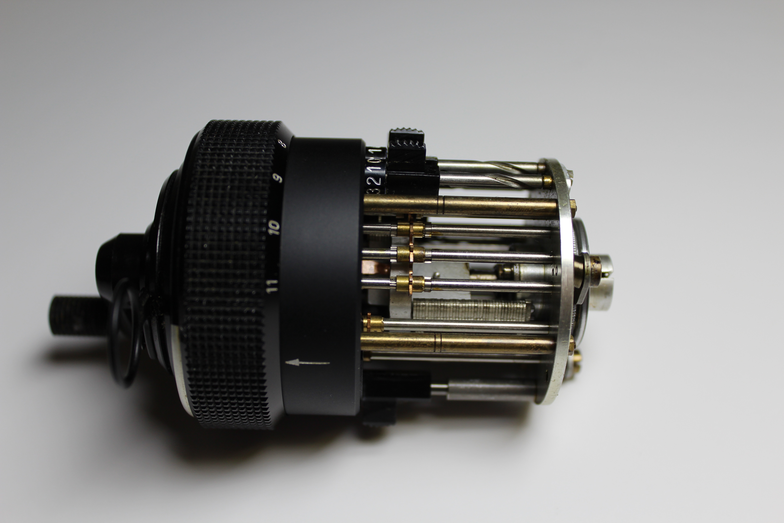
reference-photo/IMG_1056.jpg
