daeken/ReCurta/reference-photo/IMG_1059.jpg

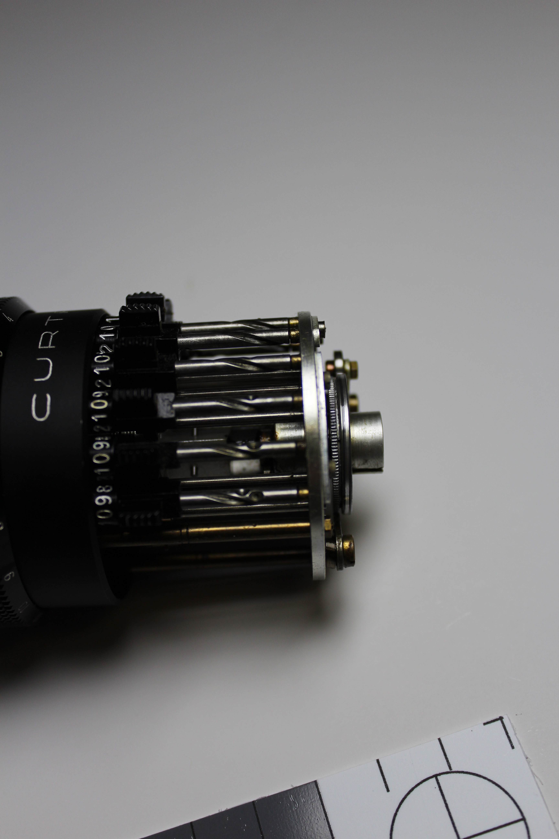
reference-photo/IMG_1059.jpg
