daeken/ReCurta/reference-photo/IMG_1061.jpg

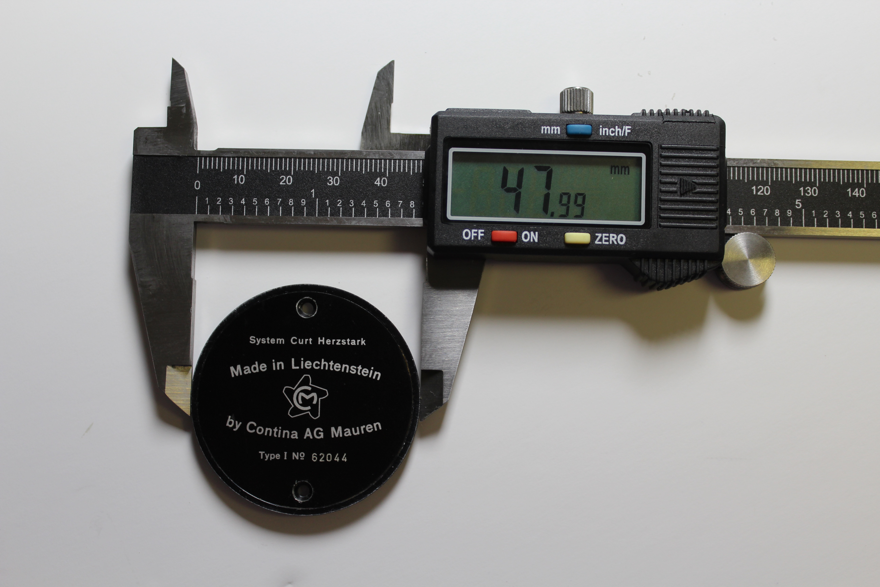
reference-photo/IMG_1061.jpg
