daeken/ReCurta/reference-photo/tn_Img_2981-3095.jpg

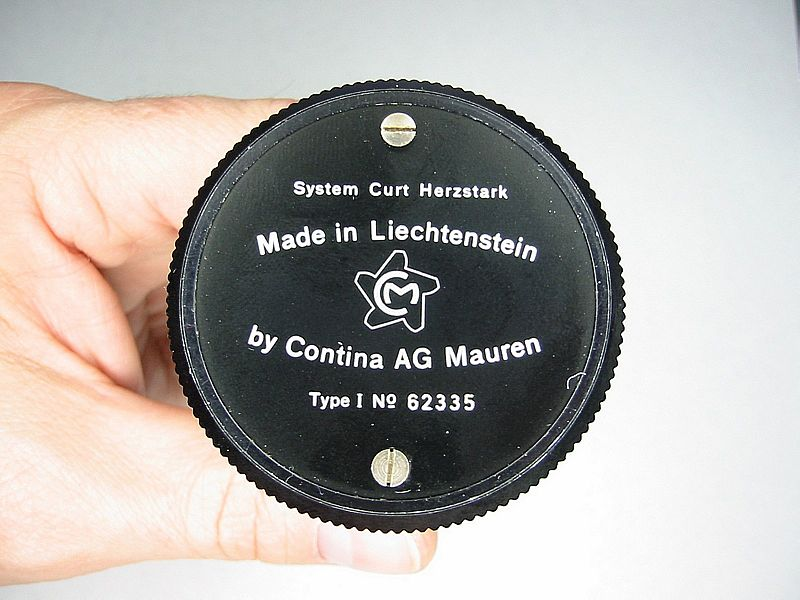
reference-photo/tn_Img_2981-3095.jpg
