daeken/ReCurta/reference-photo/tn_Img_2981-3096.jpg

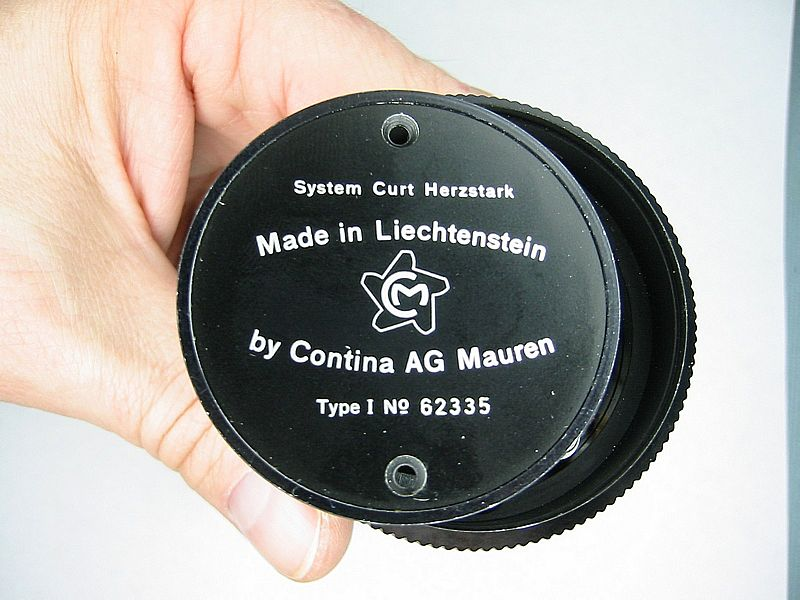
reference-photo/tn_Img_2981-3096.jpg
