daeken/ReCurta/reference-photo/tn_Img_2981-3098.jpg

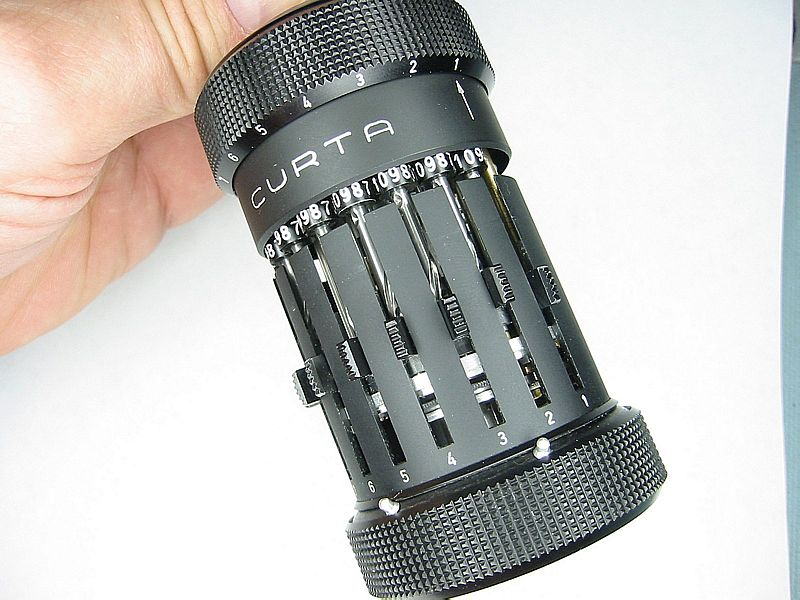
reference-photo/tn_Img_2981-3098.jpg
