daeken/ReCurta/reference-photo/tn_Img_2981-3099.jpg

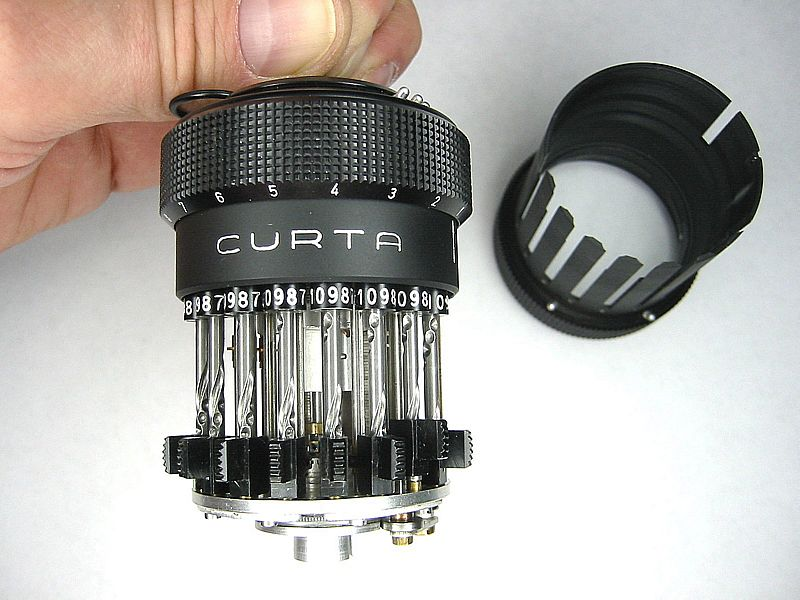
reference-photo/tn_Img_2981-3099.jpg
