daeken/ReCurta/reference-photo/tn_Img_2981-3101.jpg

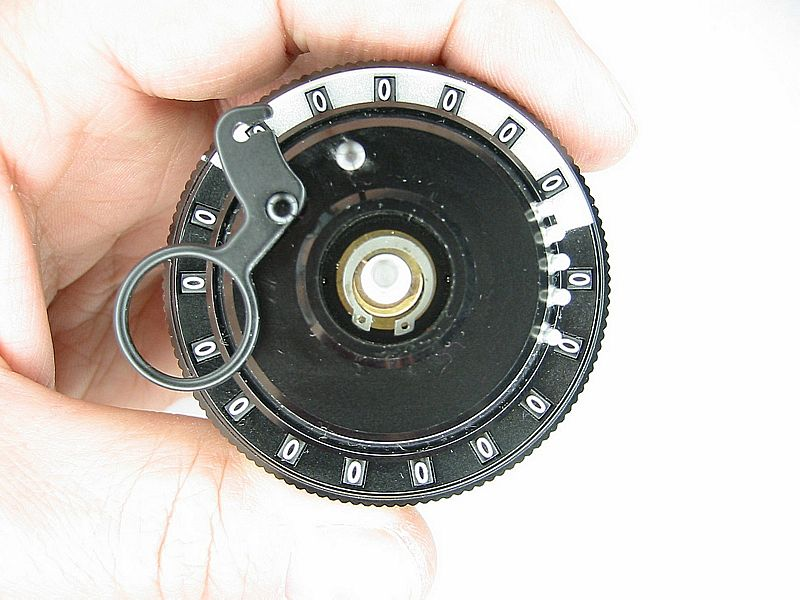
reference-photo/tn_Img_2981-3101.jpg
