daeken/ReCurta/reference-photo/tn_Img_2981-3102.jpg

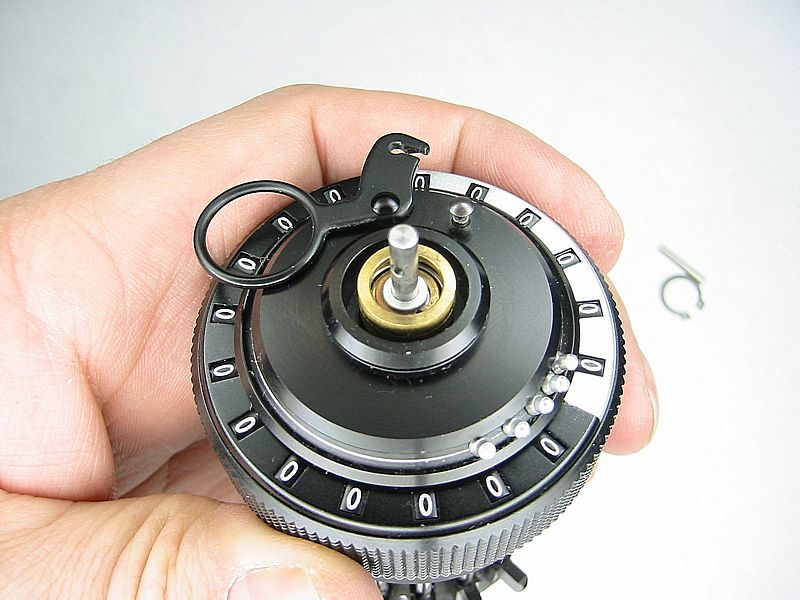
reference-photo/tn_Img_2981-3102.jpg
