daeken/ReCurta/reference-photo/tn_Img_2981-3104.jpg

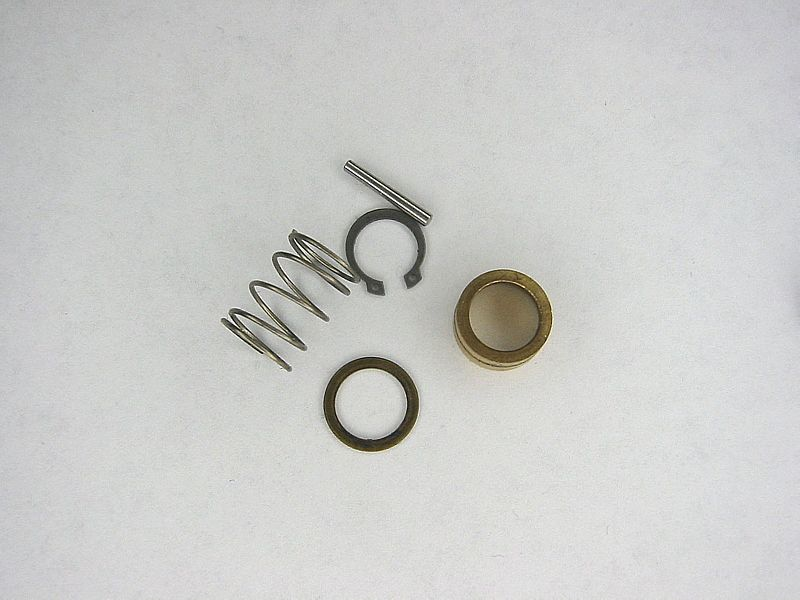
reference-photo/tn_Img_2981-3104.jpg
