daeken/ReCurta/reference-photo/tn_Img_2981-3105.jpg

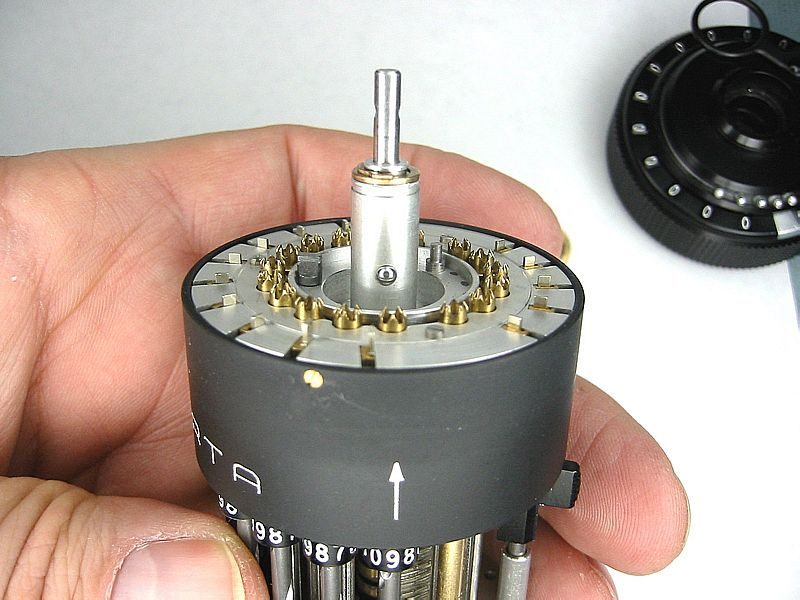
reference-photo/tn_Img_2981-3105.jpg
