daeken/ReCurta/reference-photo/tn_Img_2981-3106.jpg

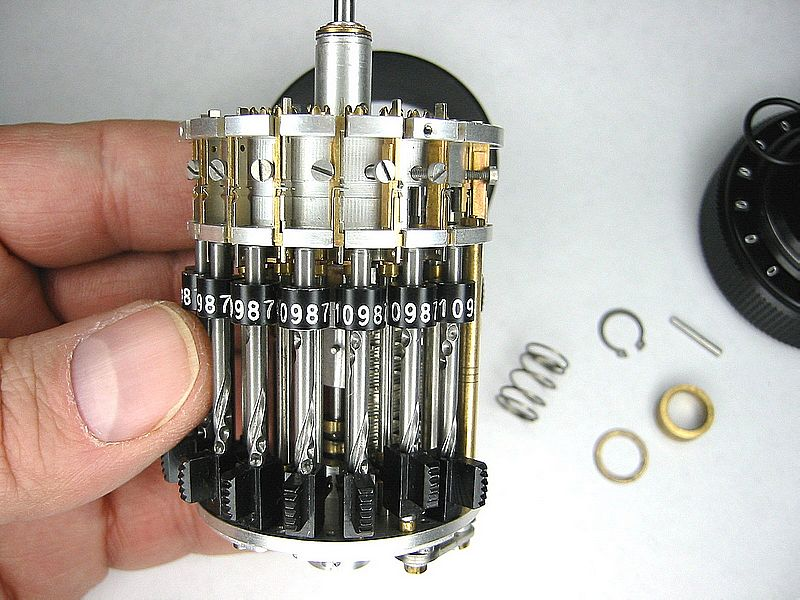
reference-photo/tn_Img_2981-3106.jpg
