daeken/ReCurta/reference-photo/tn_Img_2981-3107.jpg

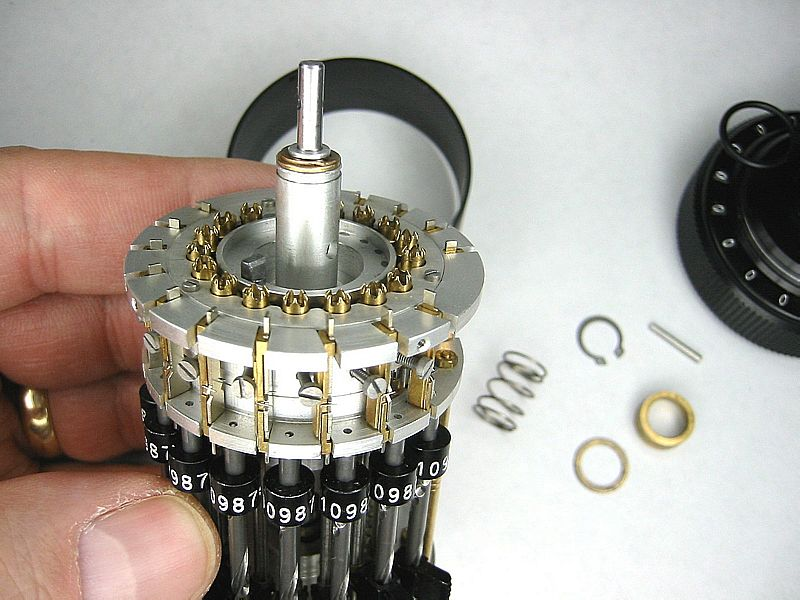
reference-photo/tn_Img_2981-3107.jpg
