daeken/ReCurta/reference-photo/tn_Img_2981-3109.jpg

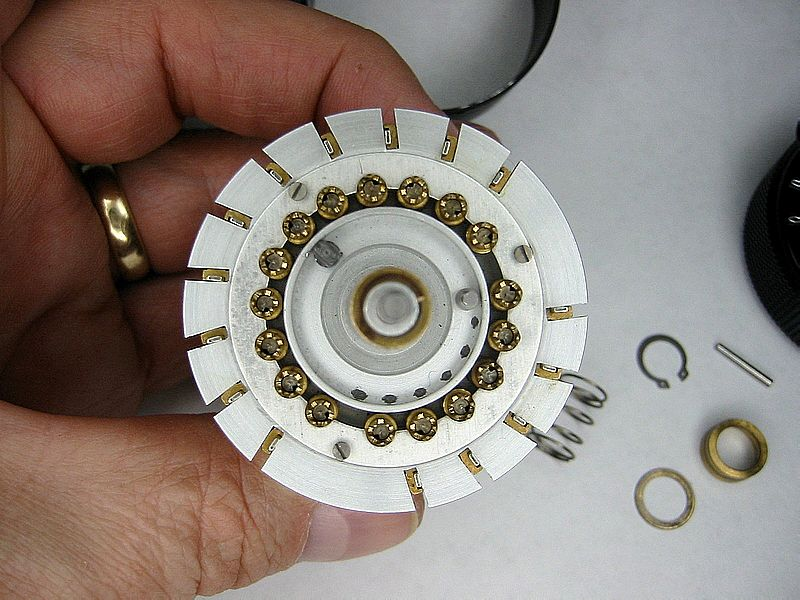
reference-photo/tn_Img_2981-3109.jpg
