daeken/ReCurta/reference-photo/tn_Img_2981a.jpg

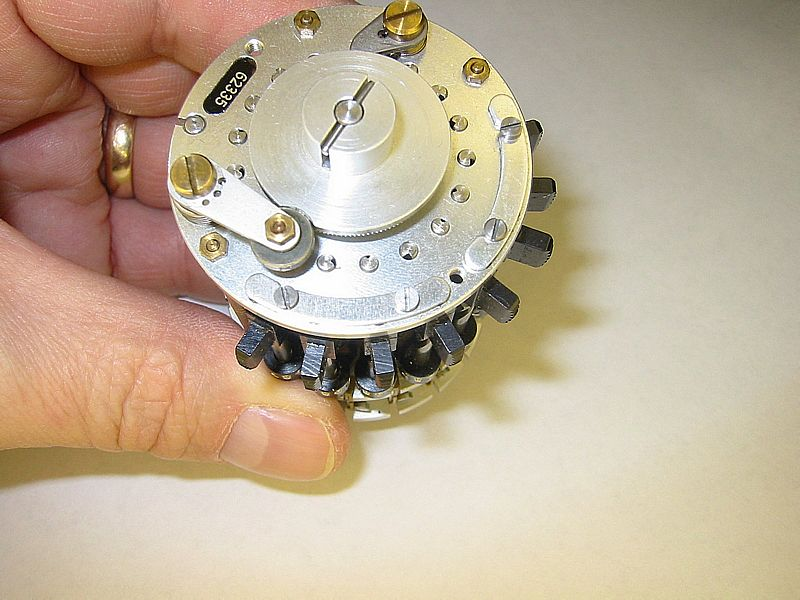
reference-photo/tn_Img_2981a.jpg
