daeken/ReCurta/reference-photo/tn_Img_2983a-3047.jpg

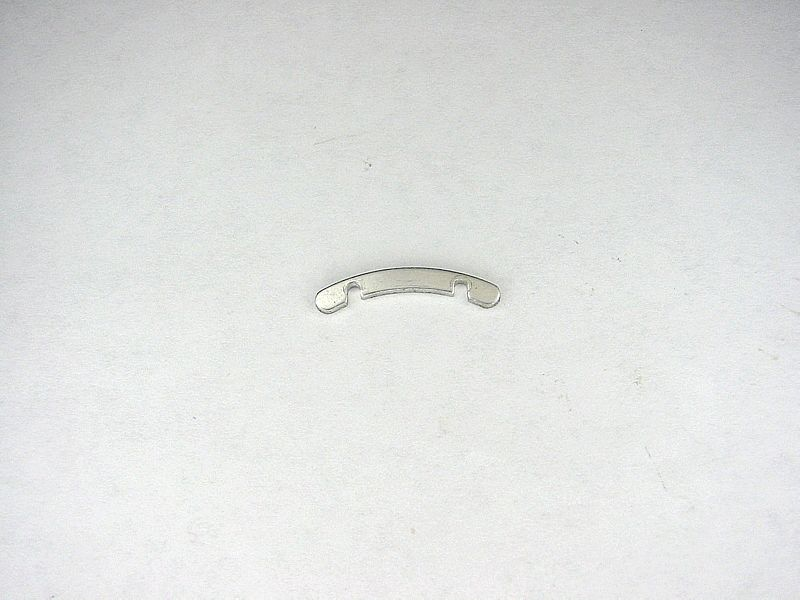
reference-photo/tn_Img_2983a-3047.jpg
