daeken/ReCurta/reference-photo/tn_Img_2984.jpg

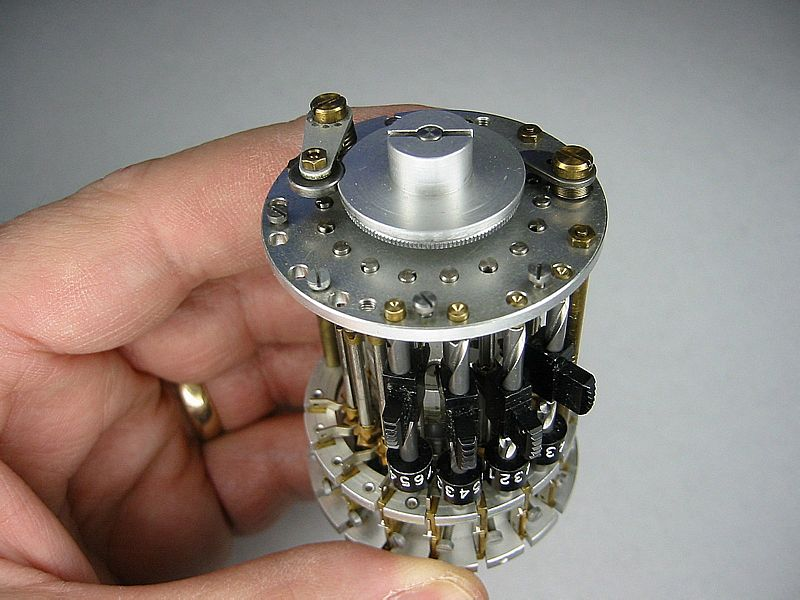
reference-photo/tn_Img_2984.jpg
