daeken/ReCurta/reference-photo/tn_Img_2986-3037.jpg

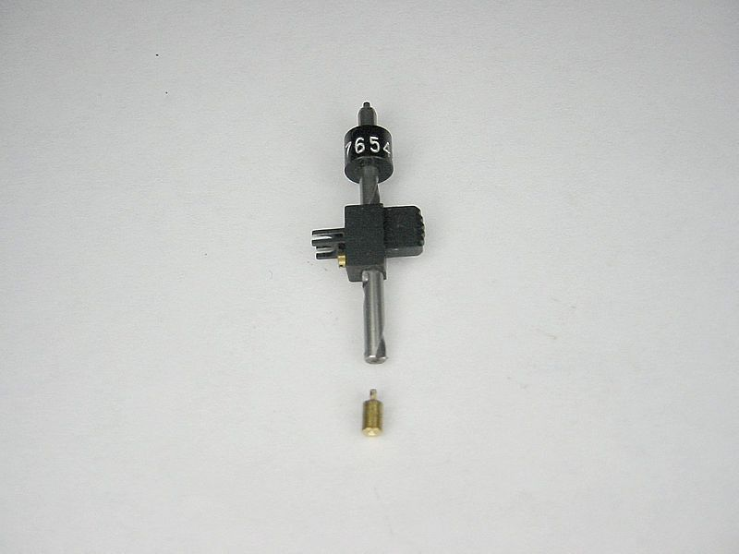
reference-photo/tn_Img_2986-3037.jpg
