daeken/ReCurta/reference-photo/tn_Img_2986-3039.jpg

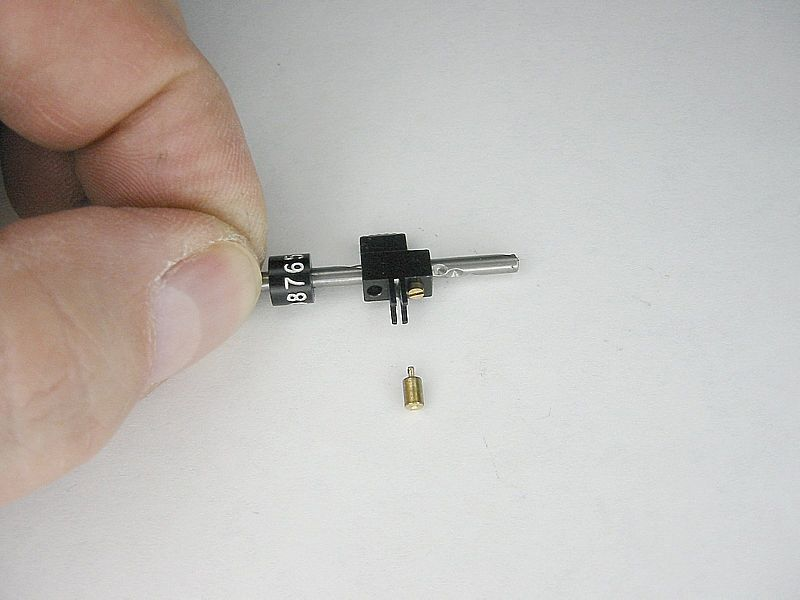
reference-photo/tn_Img_2986-3039.jpg
