daeken/ReCurta/reference-photo/tn_Img_2986-3040.jpg

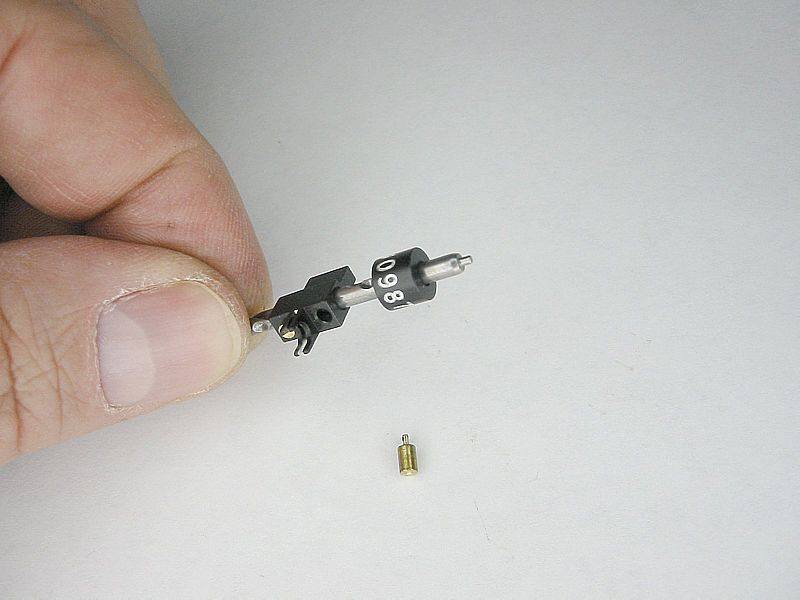
reference-photo/tn_Img_2986-3040.jpg
