daeken/ReCurta/reference-photo/tn_Img_2986-3057.jpg

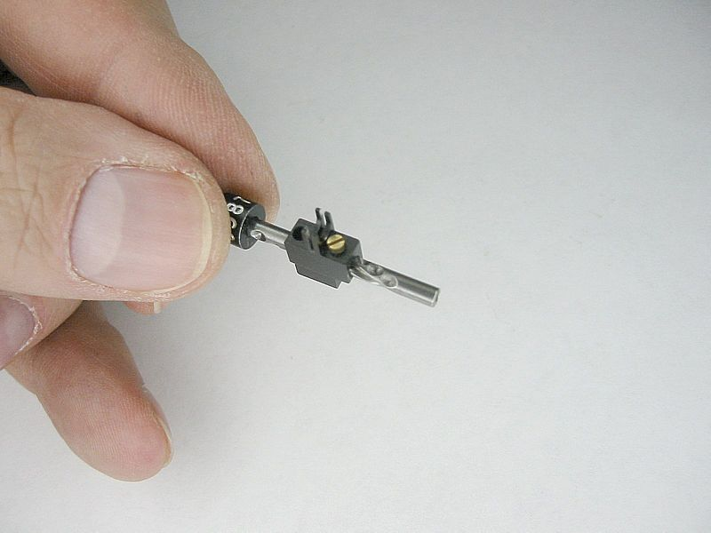
reference-photo/tn_Img_2986-3057.jpg
