daeken/ReCurta/reference-photo/tn_Img_2986a.jpg

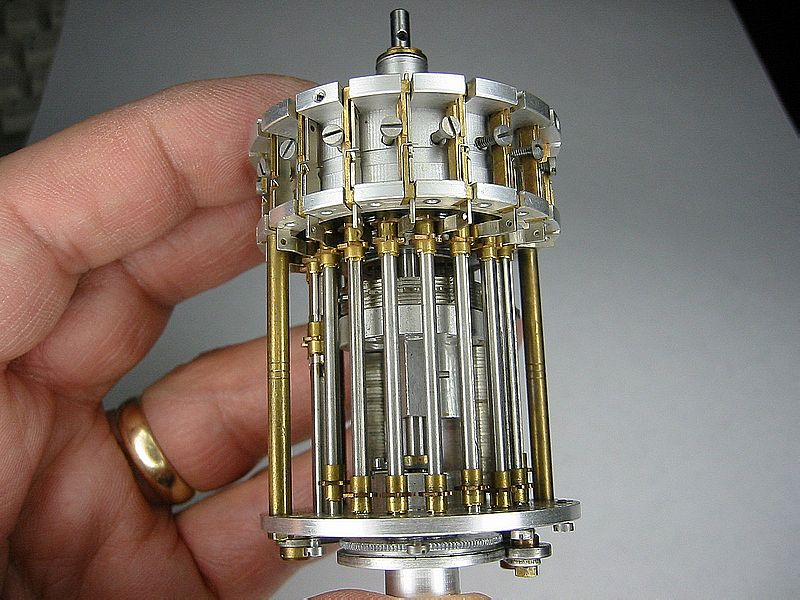
reference-photo/tn_Img_2986a.jpg
