daeken/ReCurta/reference-photo/tn_Img_2988a-3092.jpg

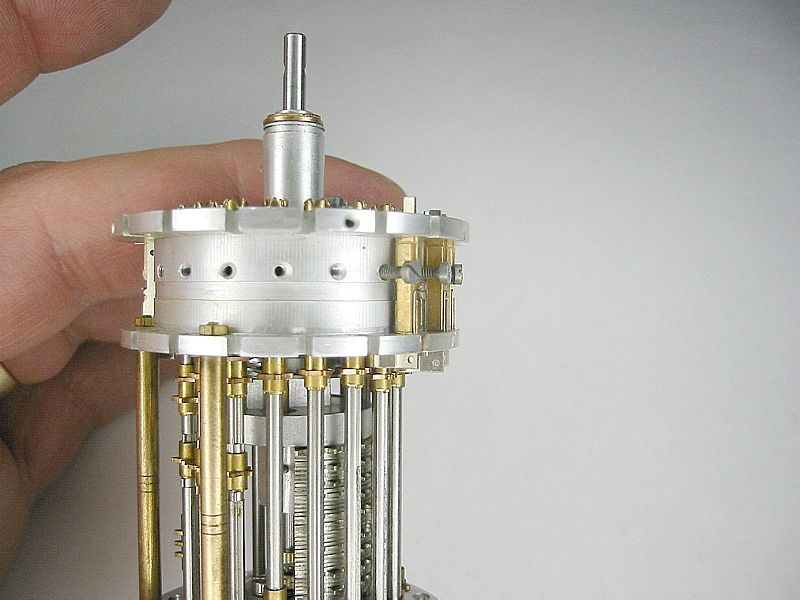
reference-photo/tn_Img_2988a-3092.jpg
