daeken/ReCurta/reference-photo/tn_Img_2988a-3094.jpg

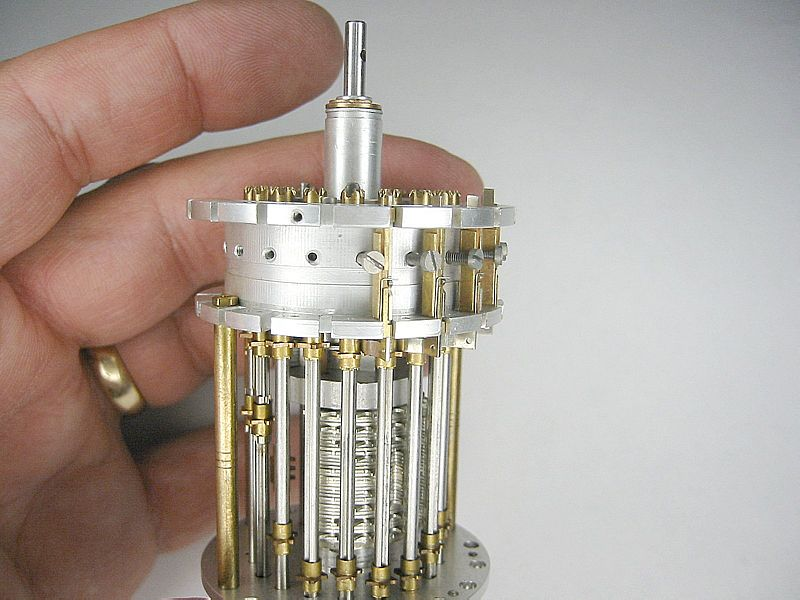
reference-photo/tn_Img_2988a-3094.jpg
