daeken/ReCurta/reference-photo/tn_Img_2989.jpg

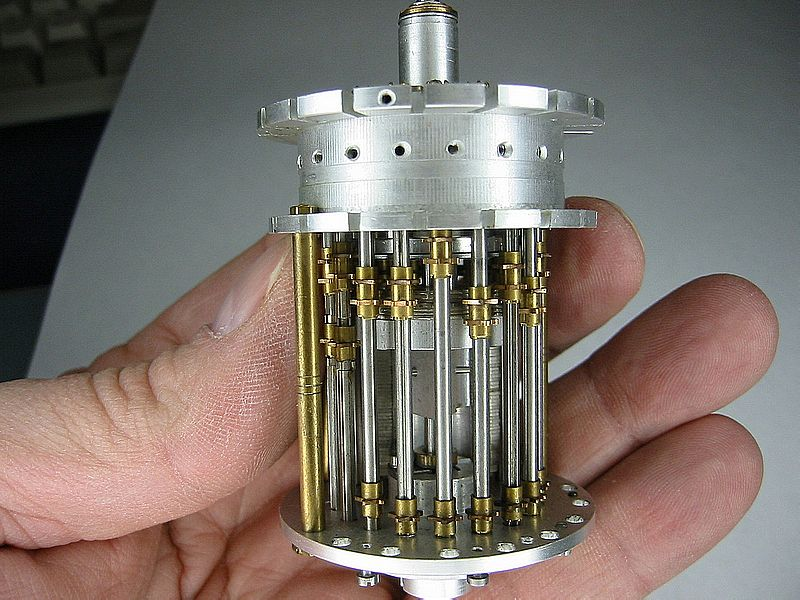
reference-photo/tn_Img_2989.jpg
