daeken/ReCurta/reference-photo/tn_Img_2991-3026.jpg

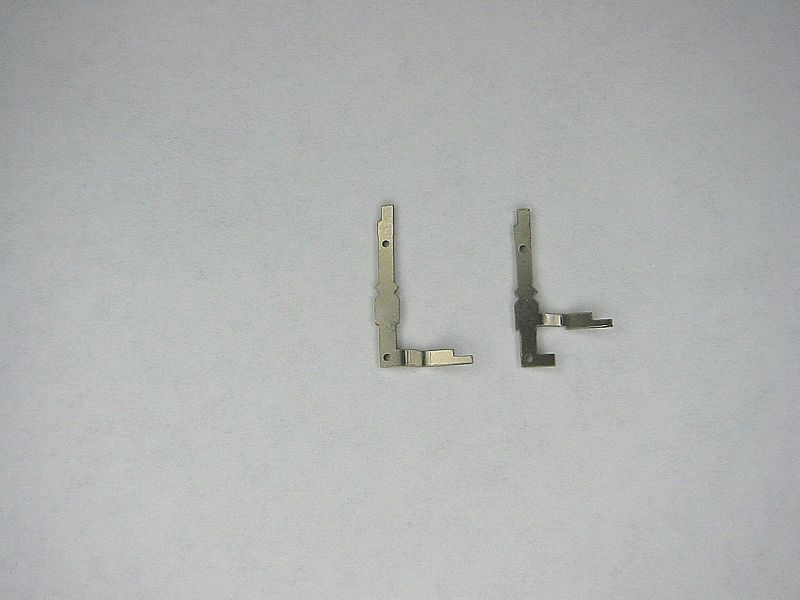
reference-photo/tn_Img_2991-3026.jpg
