daeken/ReCurta/reference-photo/tn_Img_2991a.jpg

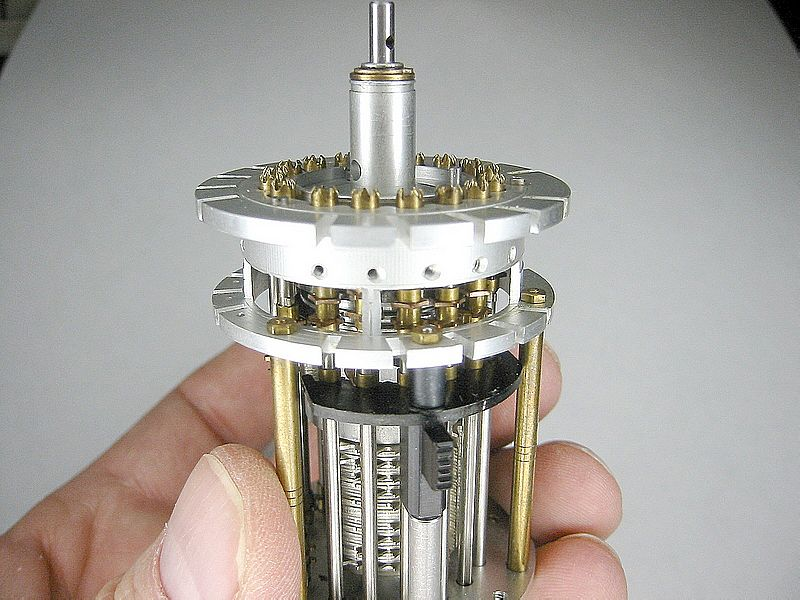
reference-photo/tn_Img_2991a.jpg
