daeken/ReCurta/reference-photo/tn_Img_2992.jpg

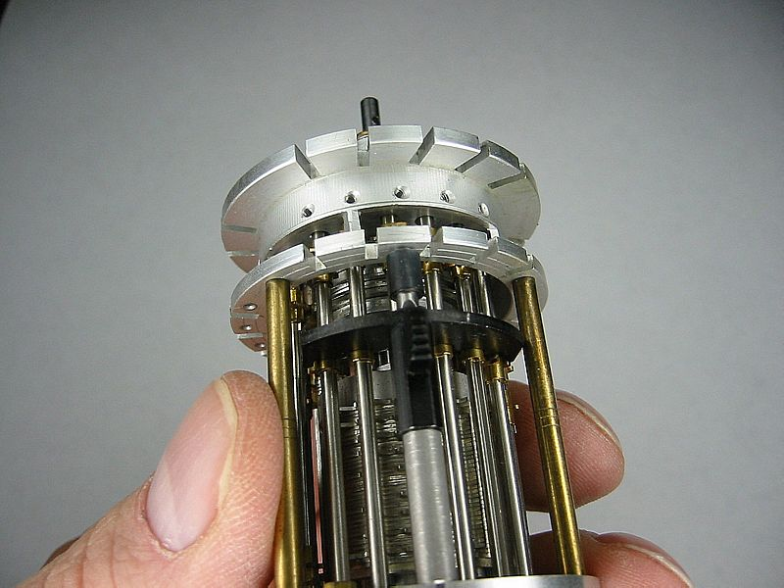
reference-photo/tn_Img_2992.jpg
