daeken/ReCurta/reference-photo/tn_Img_2993.jpg

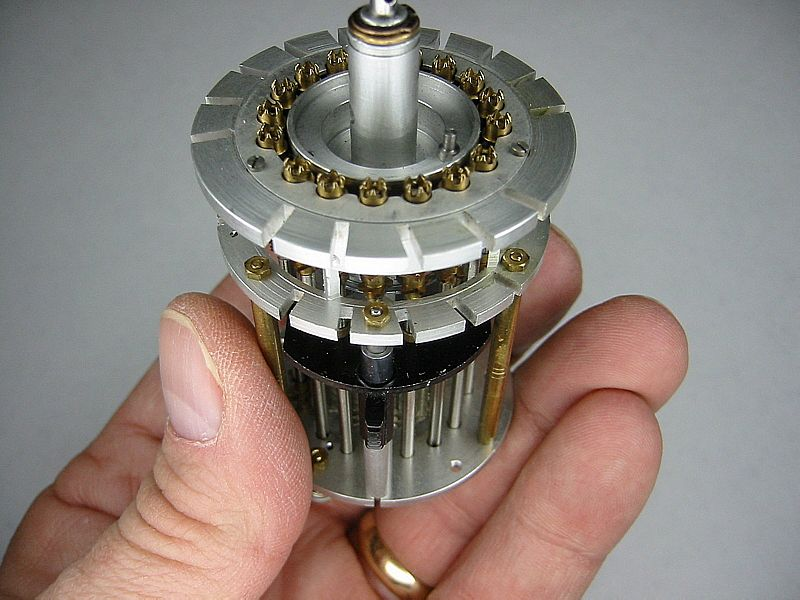
reference-photo/tn_Img_2993.jpg
