daeken/ReCurta/reference-photo/tn_Img_2994.jpg

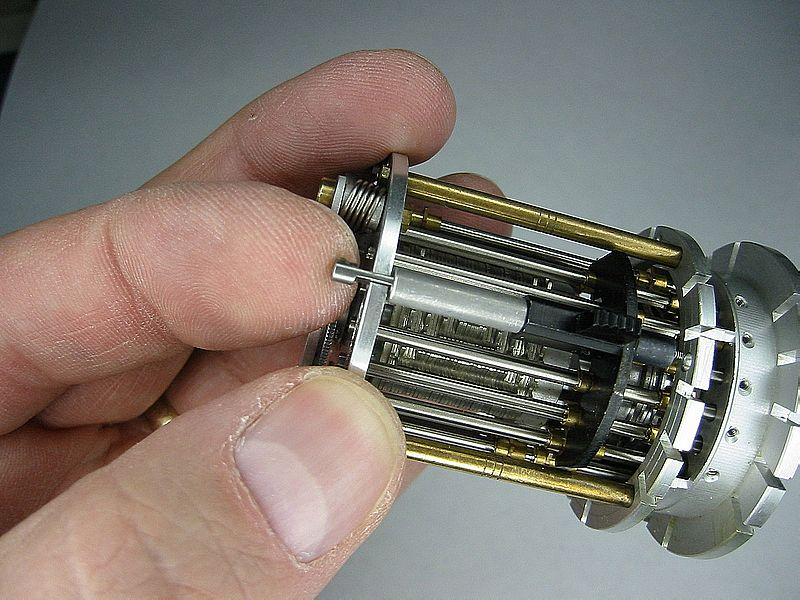
reference-photo/tn_Img_2994.jpg
