daeken/ReCurta/reference-photo/tn_Img_2995-3042.jpg

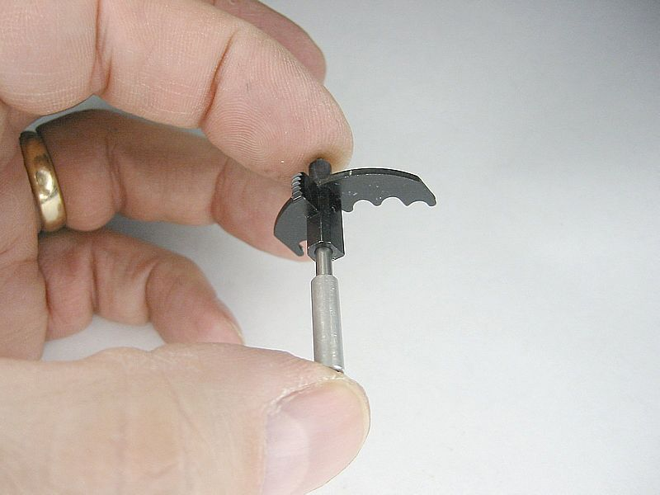
reference-photo/tn_Img_2995-3042.jpg
