daeken/ReCurta/reference-photo/tn_Img_2995-3044.jpg

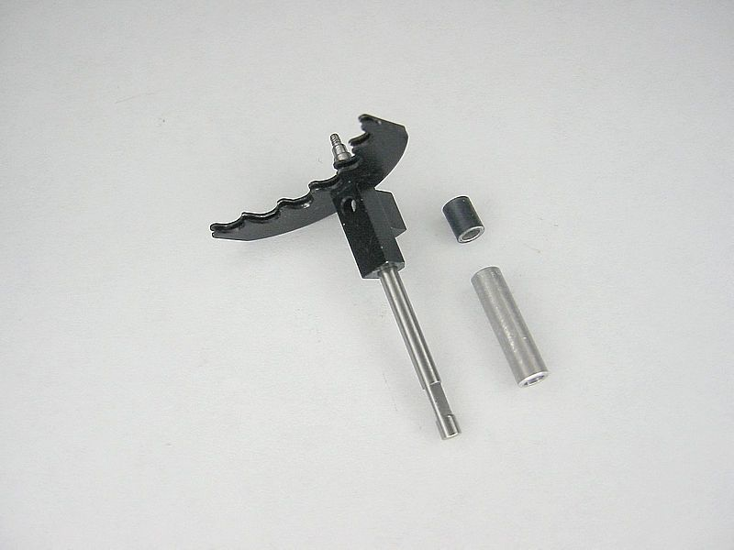
reference-photo/tn_Img_2995-3044.jpg
