daeken/ReCurta/reference-photo/tn_Img_2995-3045.jpg

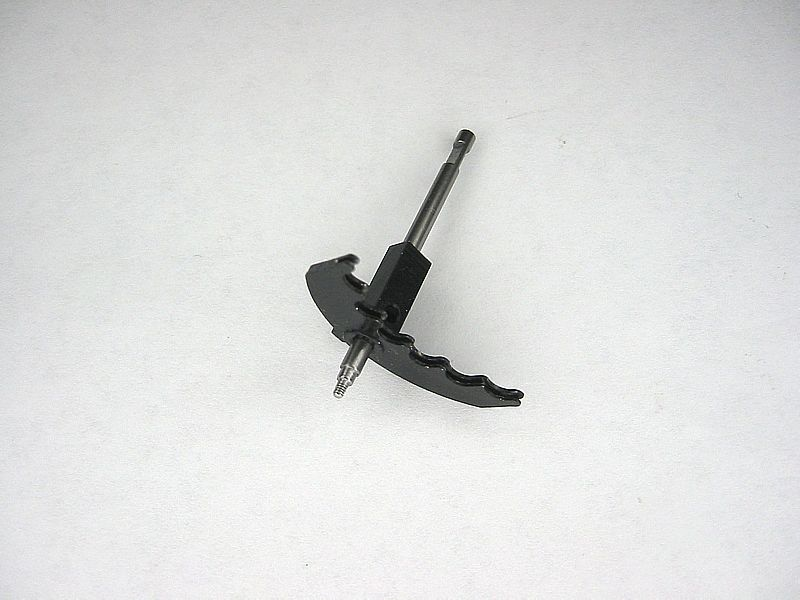
reference-photo/tn_Img_2995-3045.jpg
