daeken/ReCurta/reference-photo/tn_Img_2995-3046-3088.jpg

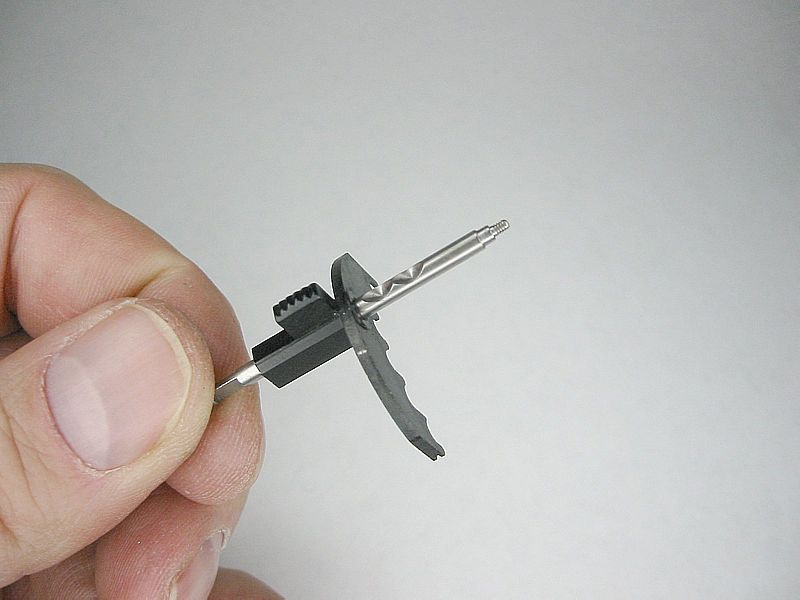
reference-photo/tn_Img_2995-3046-3088.jpg
