daeken/ReCurta/reference-photo/tn_Img_2995-3112.jpg

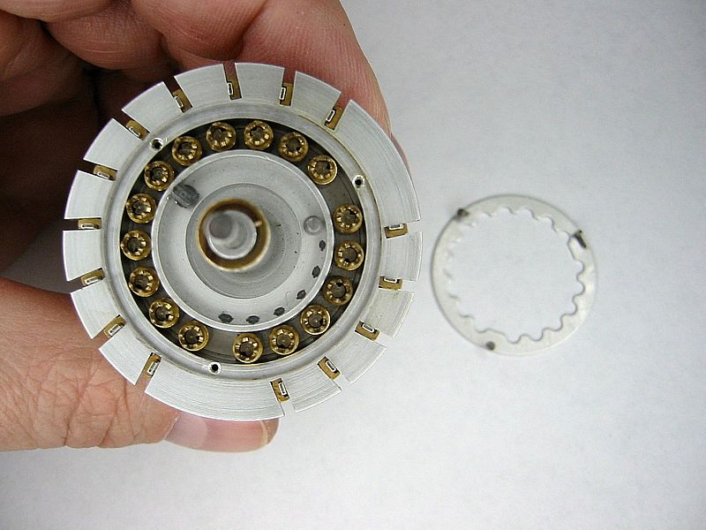
reference-photo/tn_Img_2995-3112.jpg
