daeken/ReCurta/reference-photo/tn_Img_2995-3113.jpg

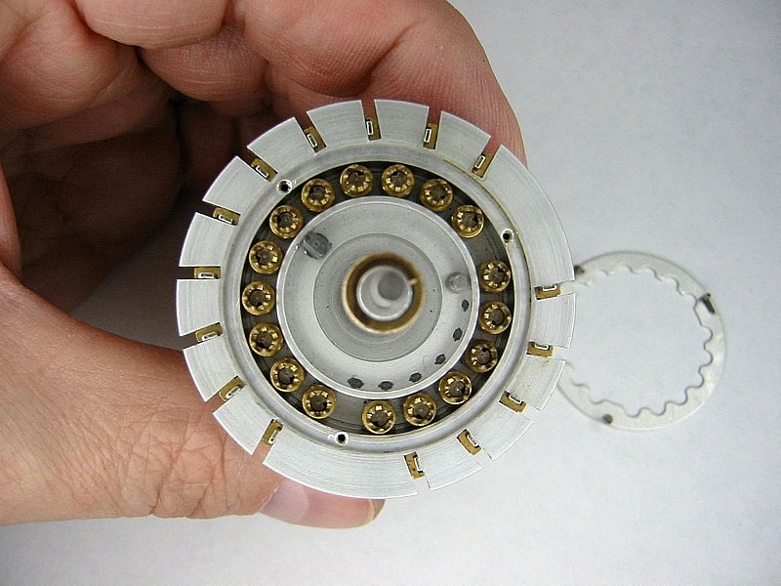
reference-photo/tn_Img_2995-3113.jpg
