daeken/ReCurta/reference-photo/tn_Img_2995-3114.jpg

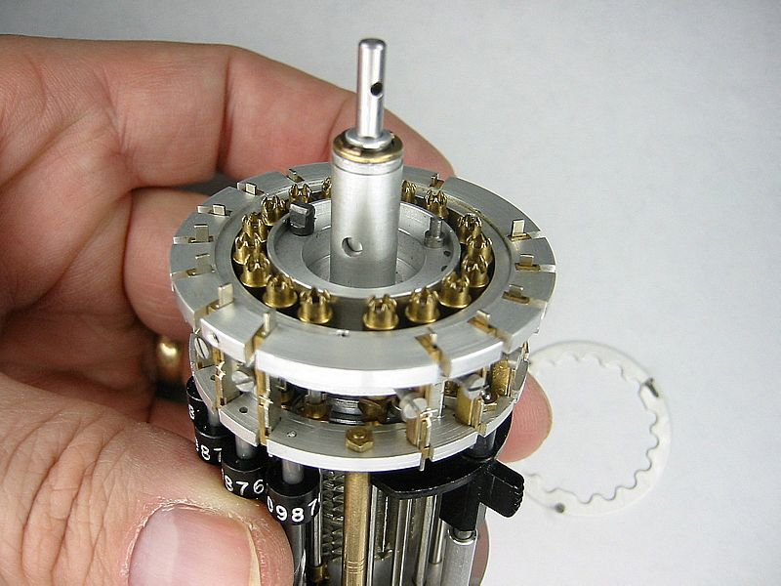
reference-photo/tn_Img_2995-3114.jpg
