daeken/ReCurta/reference-photo/tn_Img_2997-3053.jpg

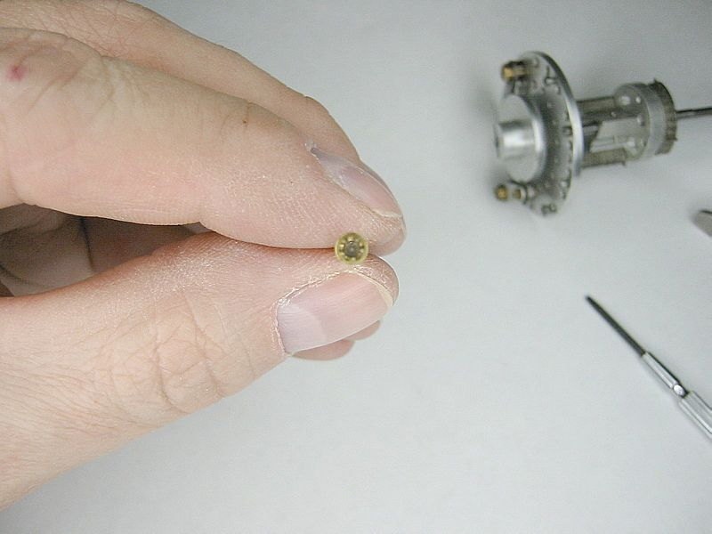
reference-photo/tn_Img_2997-3053.jpg
