daeken/ReCurta/reference-photo/tn_Img_2997-3054.jpg

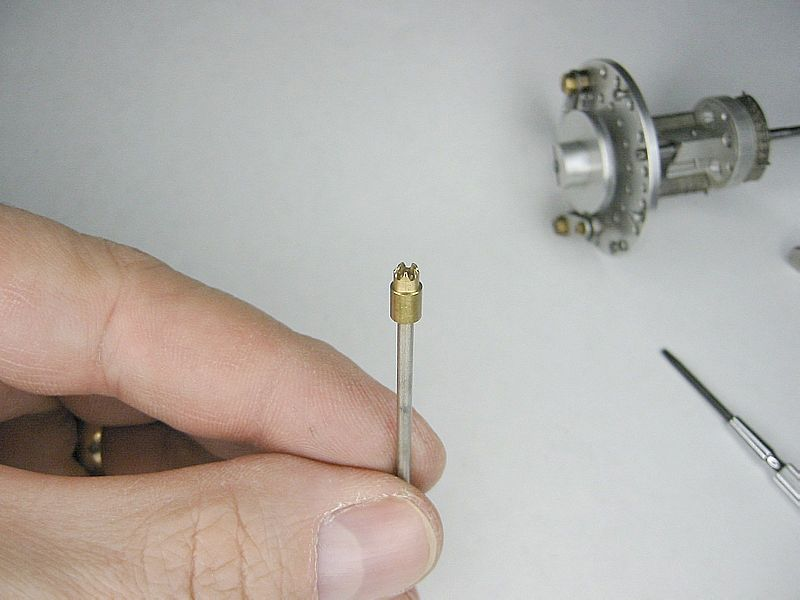
reference-photo/tn_Img_2997-3054.jpg
