daeken/ReCurta/reference-photo/tn_Img_2998-3032.jpg

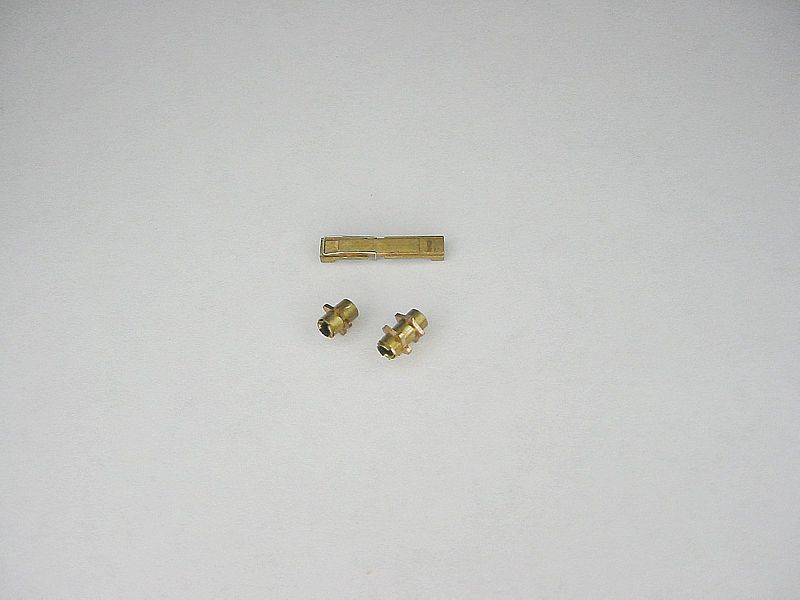
reference-photo/tn_Img_2998-3032.jpg
