daeken/ReCurta/reference-photo/tn_Img_2998-3033.jpg

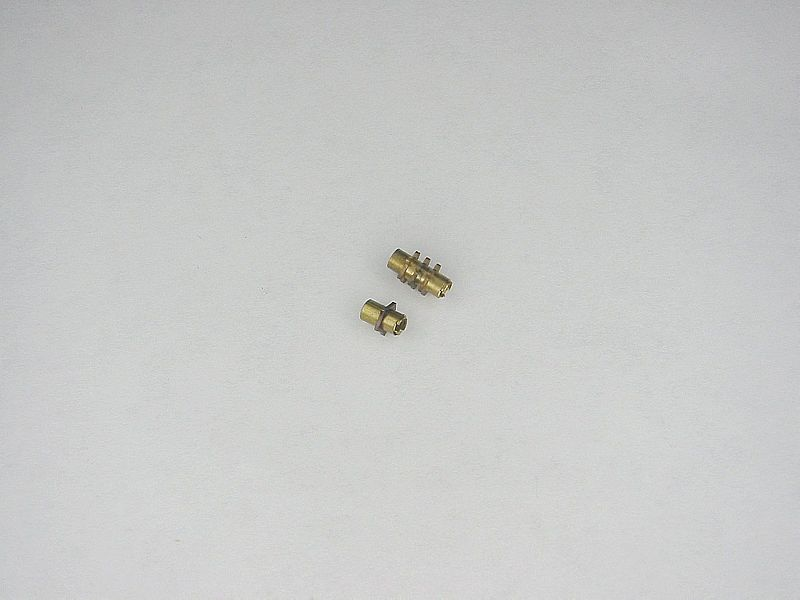
reference-photo/tn_Img_2998-3033.jpg
