daeken/ReCurta/reference-photo/tn_Img_3002.jpg

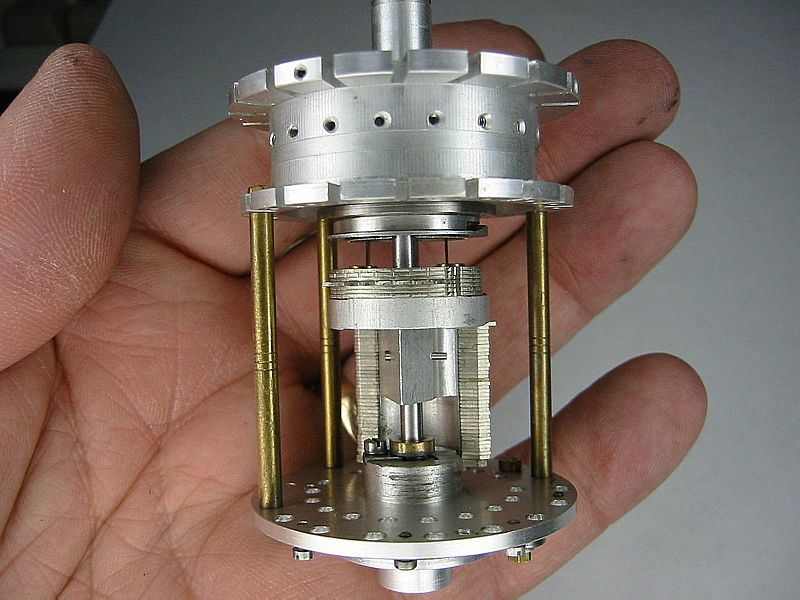
reference-photo/tn_Img_3002.jpg
