daeken/ReCurta/reference-photo/tn_Img_3003.jpg

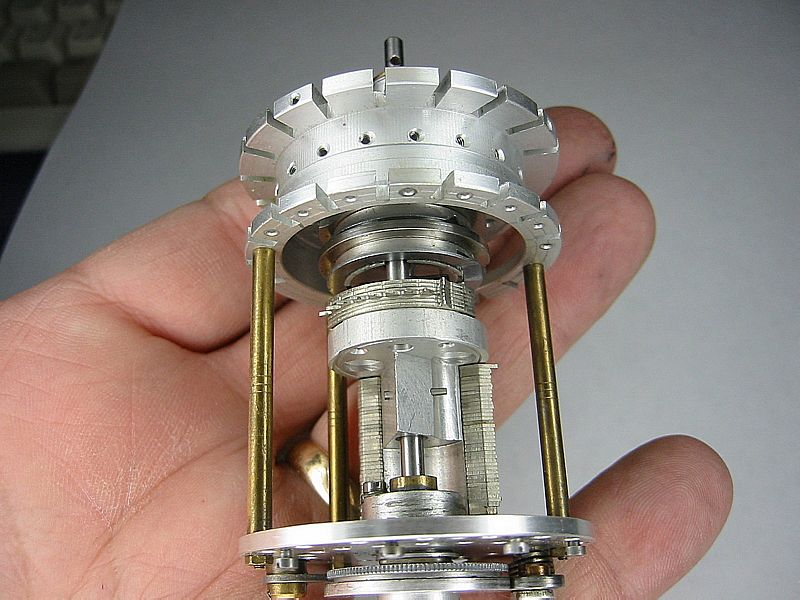
reference-photo/tn_Img_3003.jpg
