daeken/ReCurta/reference-photo/tn_Img_3005.jpg

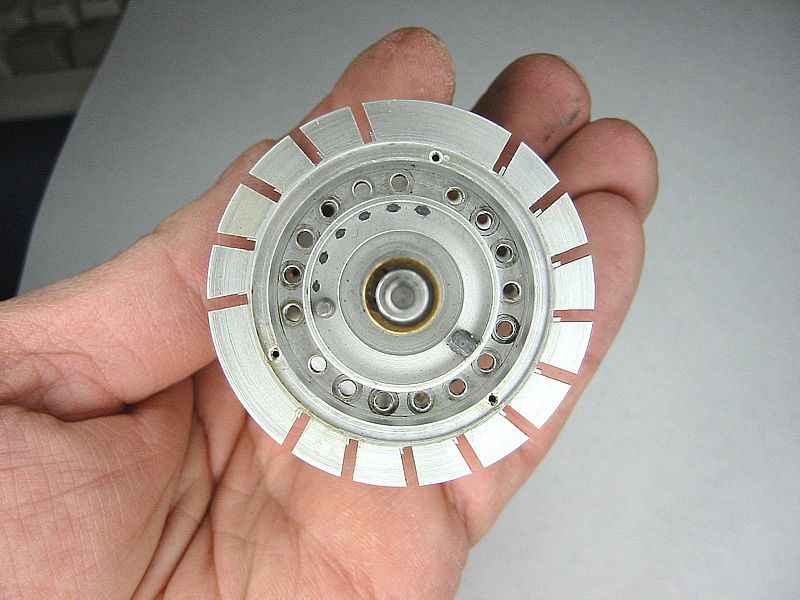
reference-photo/tn_Img_3005.jpg
