daeken/ReCurta/reference-photo/tn_Img_3006.jpg

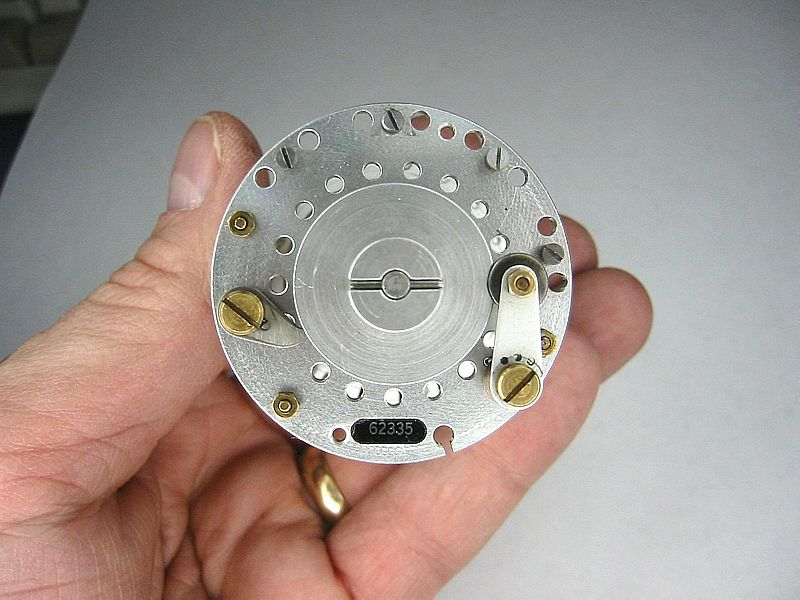
reference-photo/tn_Img_3006.jpg
