daeken/ReCurta/reference-photo/tn_Img_3009-3089.jpg

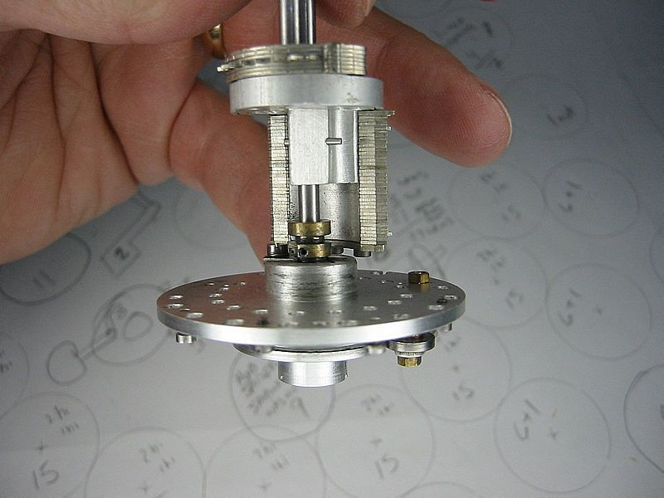
reference-photo/tn_Img_3009-3089.jpg
