daeken/ReCurta/reference-photo/tn_Img_3009-3090.jpg

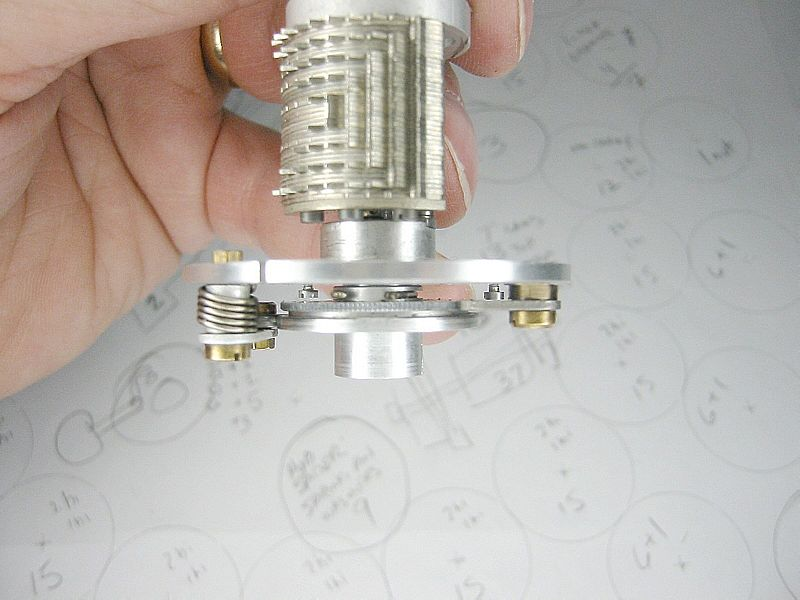
reference-photo/tn_Img_3009-3090.jpg
