daeken/ReCurta/reference-photo/tn_Img_3009a.jpg

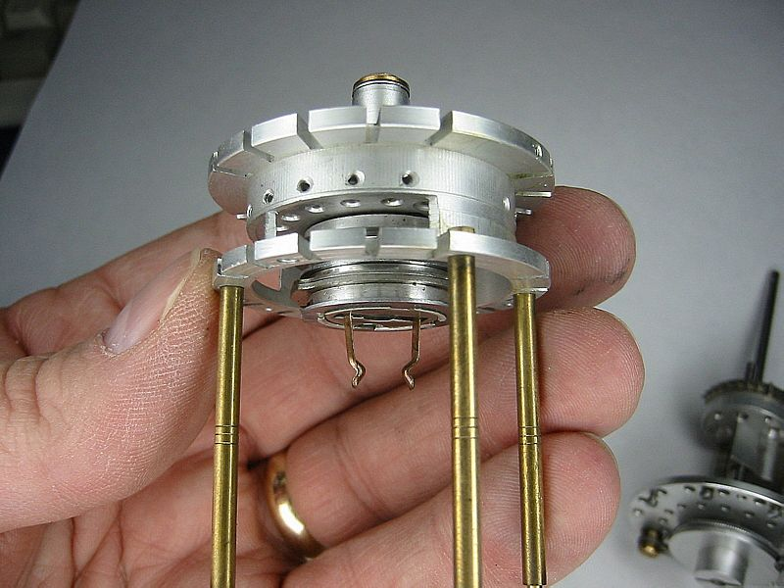
reference-photo/tn_Img_3009a.jpg
