daeken/ReCurta/reference-photo/tn_Img_3010.jpg

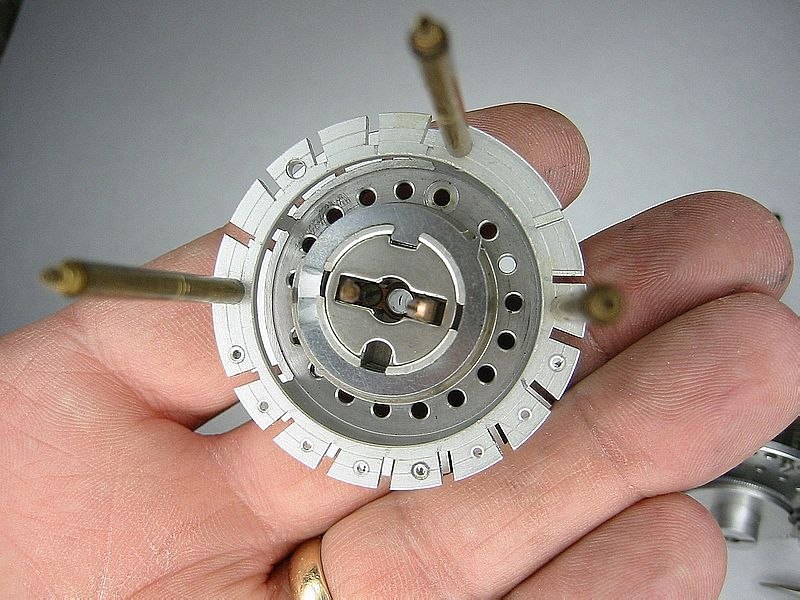
reference-photo/tn_Img_3010.jpg
