daeken/ReCurta/reference-photo/tn_Img_3014-3012.jpg

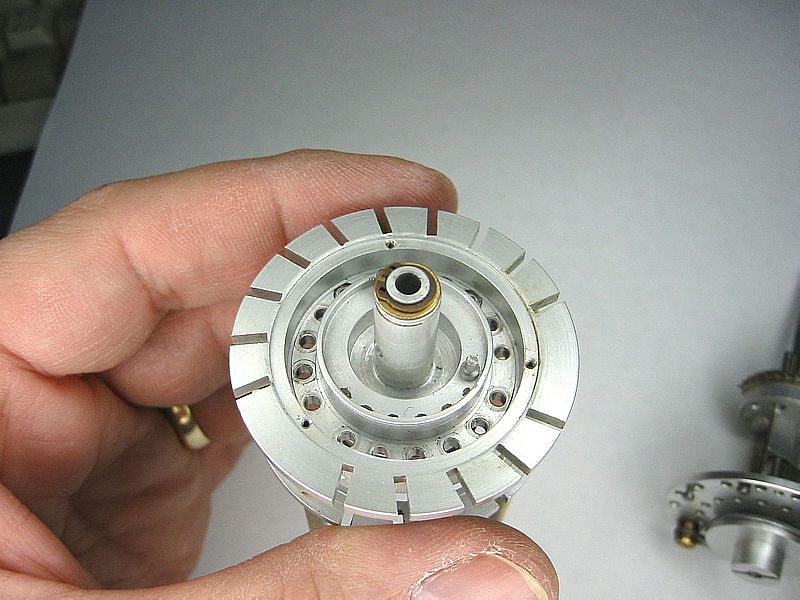
reference-photo/tn_Img_3014-3012.jpg
