daeken/ReCurta/reference-photo/tn_Img_3015.jpg

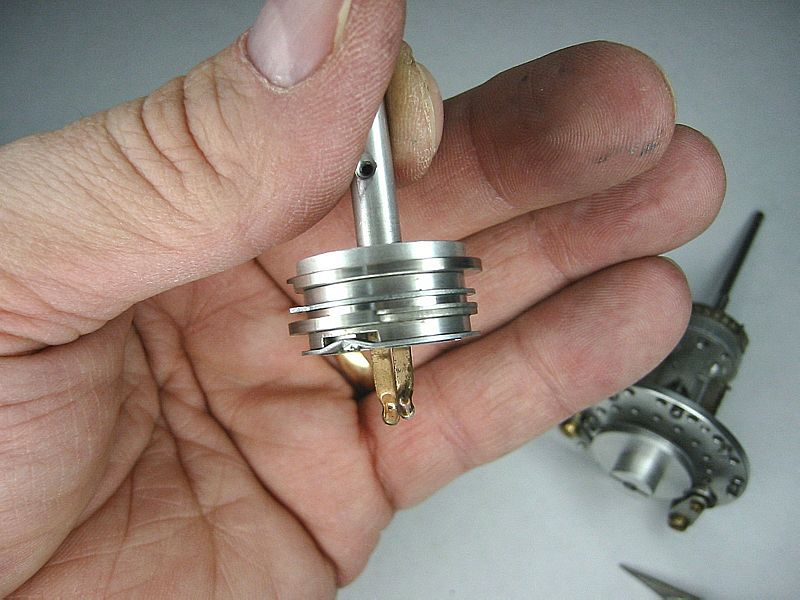
reference-photo/tn_Img_3015.jpg
