daeken/ReCurta/reference-photo/tn_Img_3017.jpg

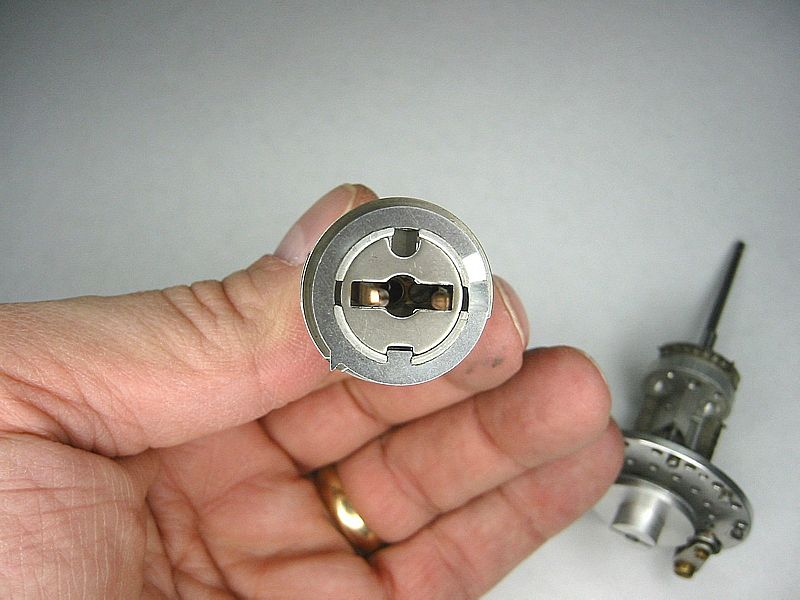
reference-photo/tn_Img_3017.jpg
