daeken/ReCurta/reference-photo/tn_Img_3018.jpg

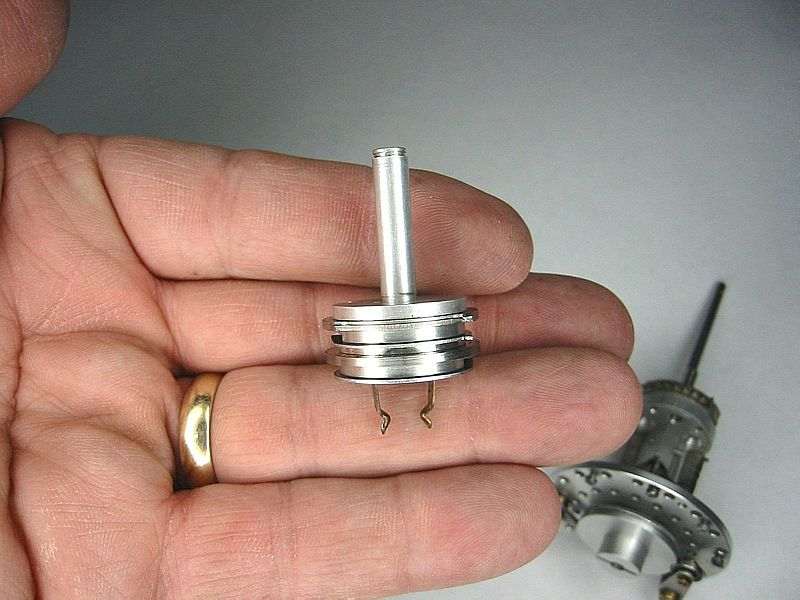
reference-photo/tn_Img_3018.jpg
