daeken/ReCurta/reference-photo/tn_Img_3020a-3013.jpg

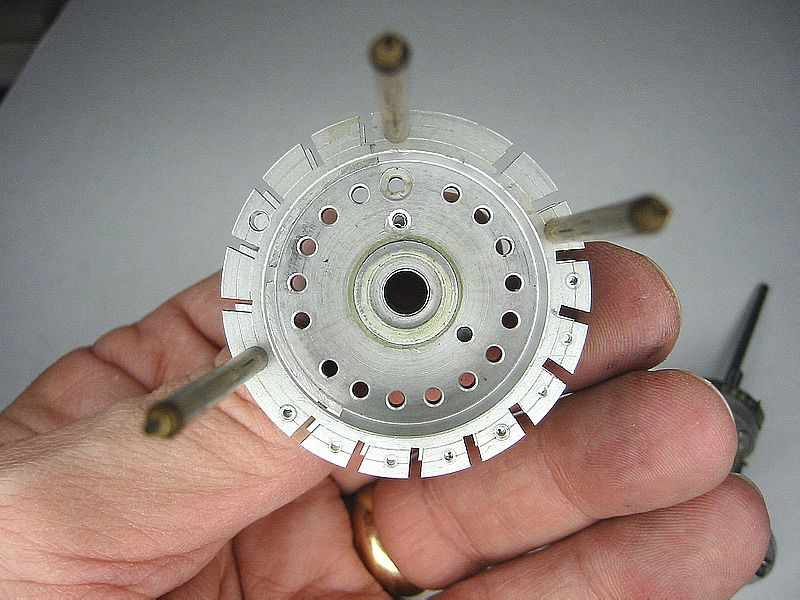
reference-photo/tn_Img_3020a-3013.jpg
