daeken/ReCurta/reference-photo/tn_Img_3021.jpg

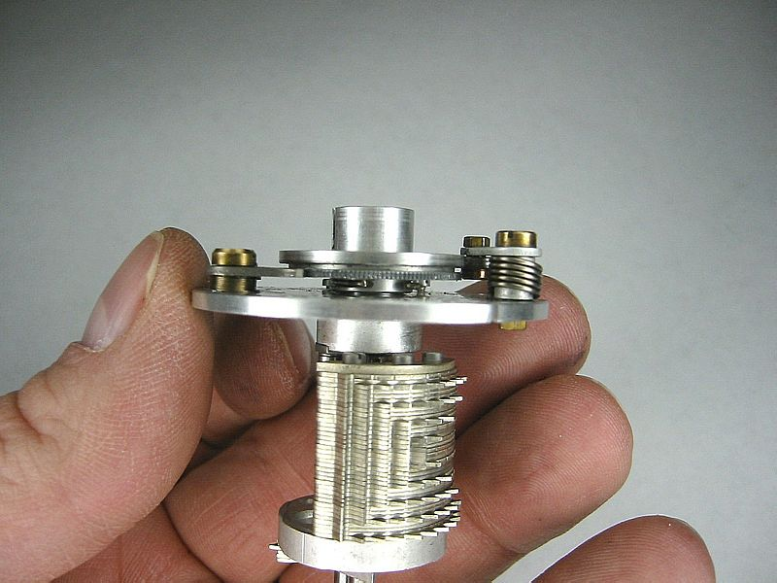
reference-photo/tn_Img_3021.jpg
