daeken/ReCurta/reference-photo/tn_Img_3023.jpg

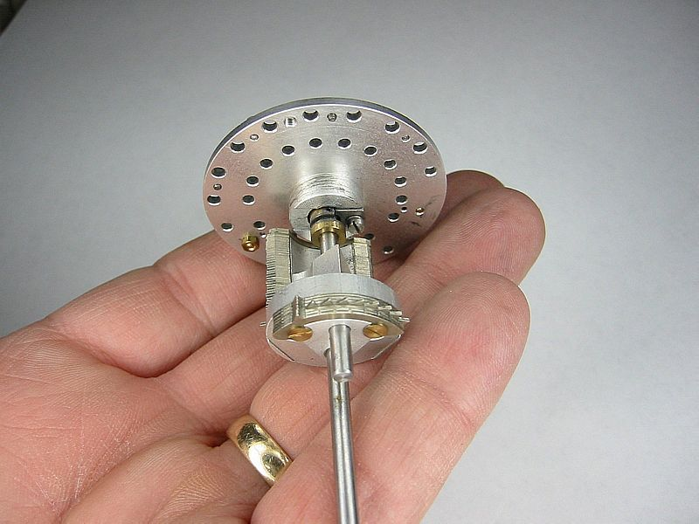
reference-photo/tn_Img_3023.jpg
