daeken/ReCurta/reference-photo/tn_Img_3051.jpg

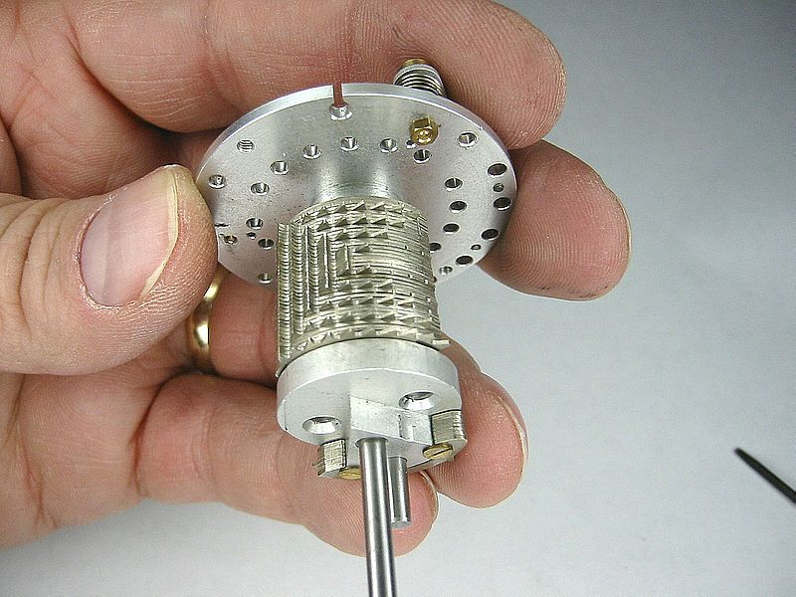
reference-photo/tn_Img_3051.jpg
