daeken/ReCurta/reference-photo/tn_Img_3052.jpg

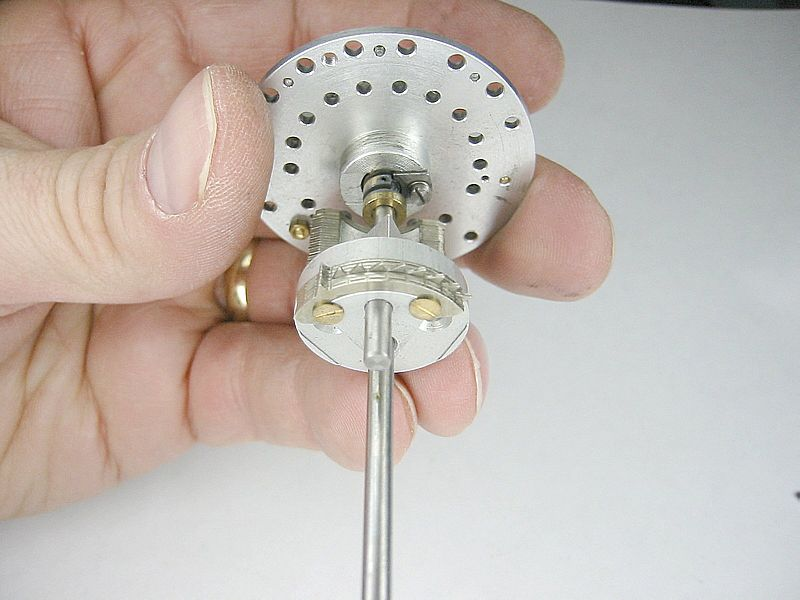
reference-photo/tn_Img_3052.jpg
