daeken/ReCurta/reference-photo/tn_Img_3058.jpg

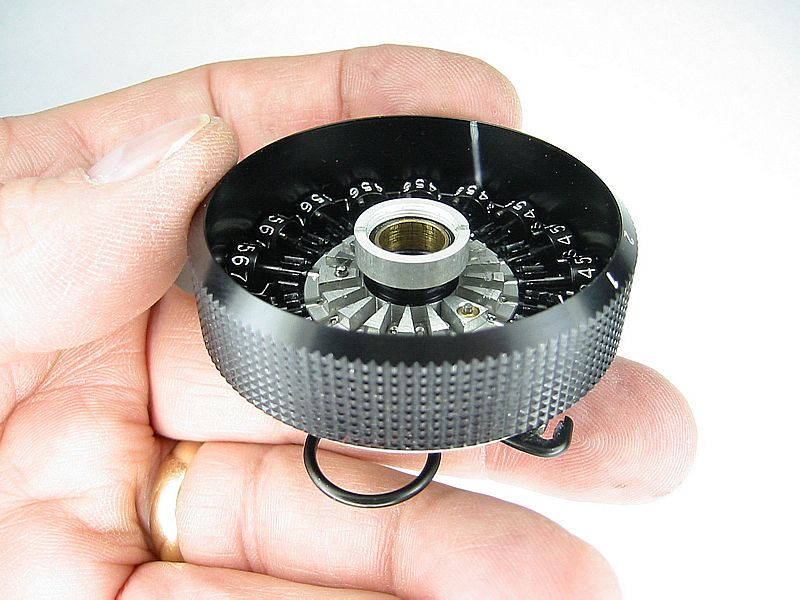
reference-photo/tn_Img_3058.jpg
