daeken/ReCurta/reference-photo/tn_Img_3064.jpg

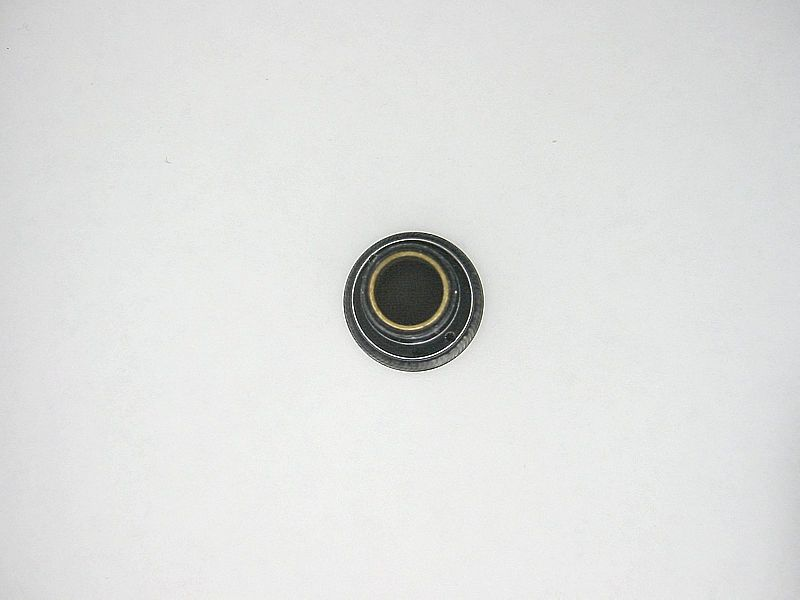
reference-photo/tn_Img_3064.jpg
