daeken/ReCurta/reference-photo/tn_Img_3066.jpg

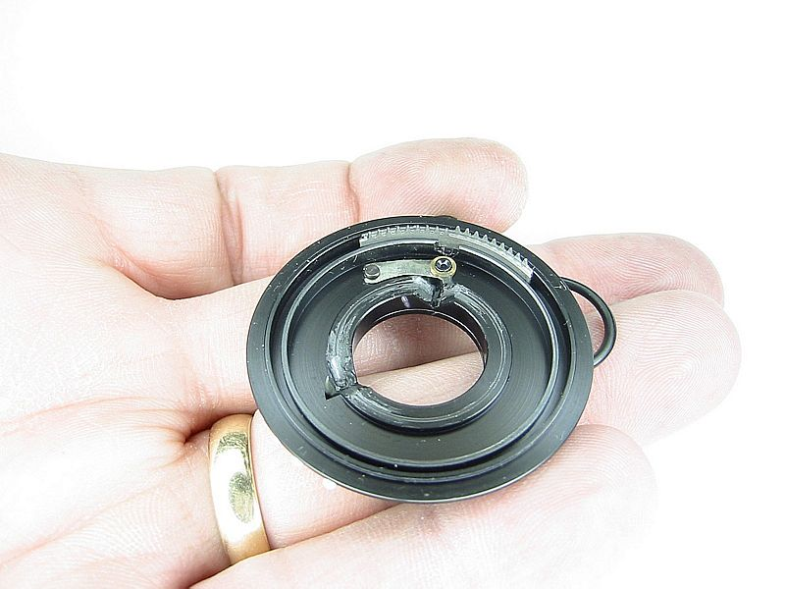
reference-photo/tn_Img_3066.jpg
