daeken/ReCurta/reference-photo/tn_Img_3068.jpg

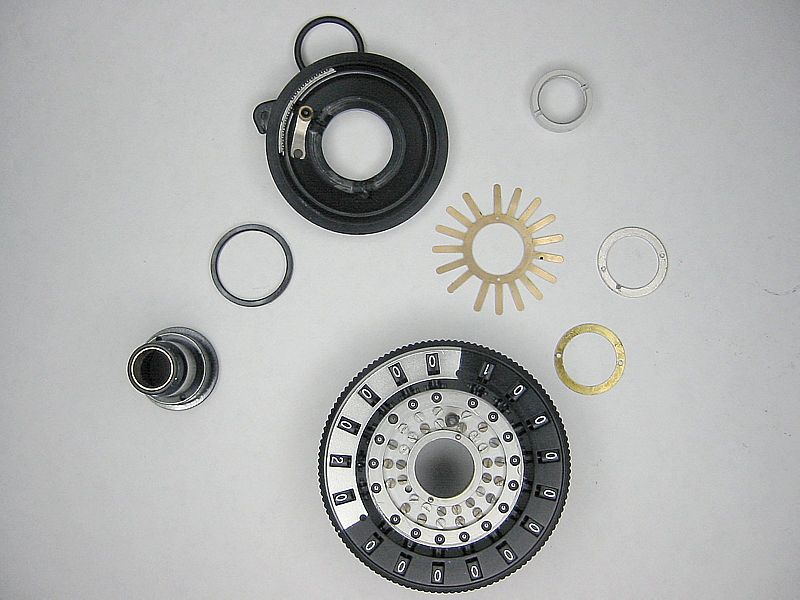
reference-photo/tn_Img_3068.jpg
