daeken/ReCurta/reference-photo/tn_Img_3070.jpg

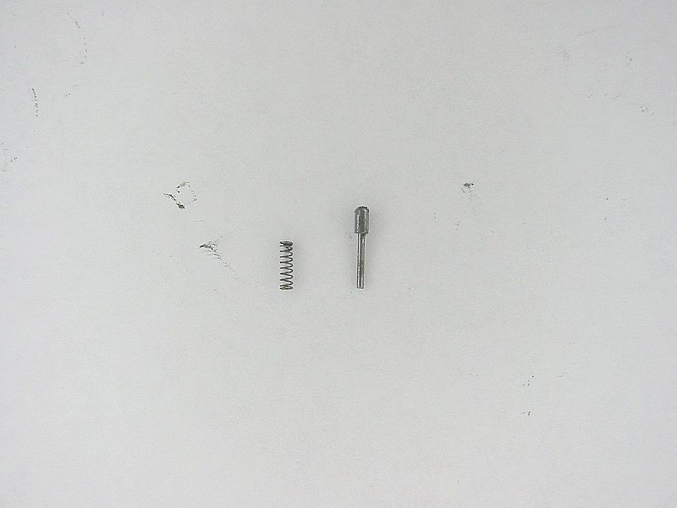
reference-photo/tn_Img_3070.jpg
