daeken/ReCurta/reference-photo/tn_Img_3074.jpg

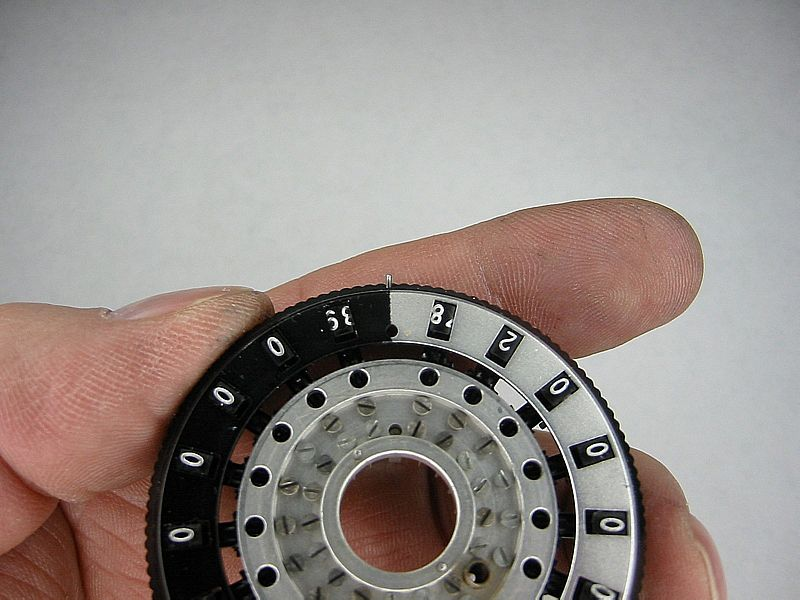
reference-photo/tn_Img_3074.jpg
