daeken/ReCurta/reference-photo/tn_Img_3075.jpg

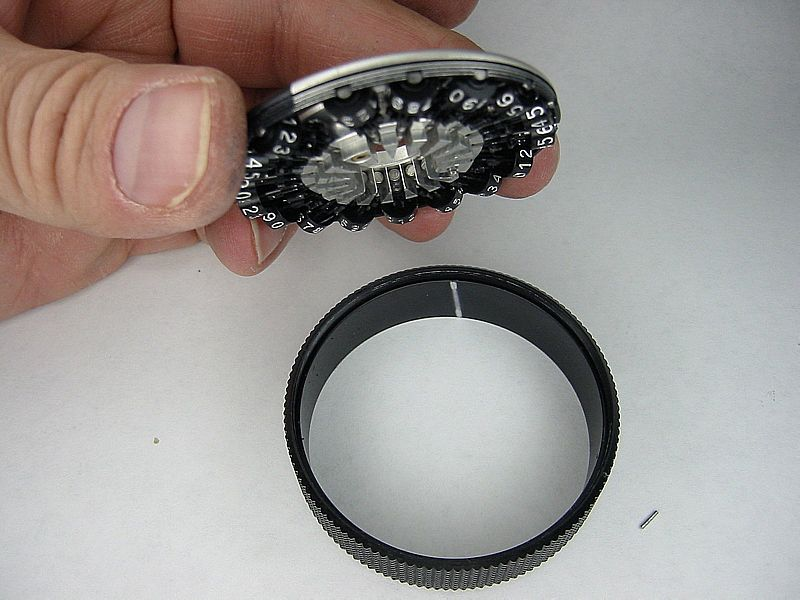
reference-photo/tn_Img_3075.jpg
