daeken/ReCurta/reference-photos/IMG_1039.jpg

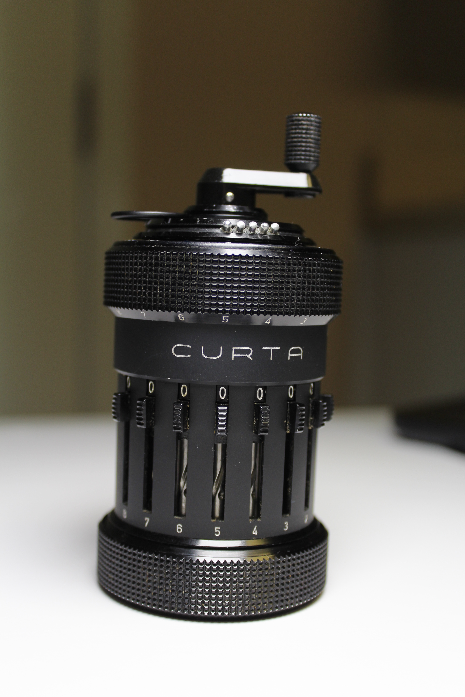
reference-photos/IMG_1039.jpg
