daeken/ReCurta/reference-photos/IMG_1042.jpg

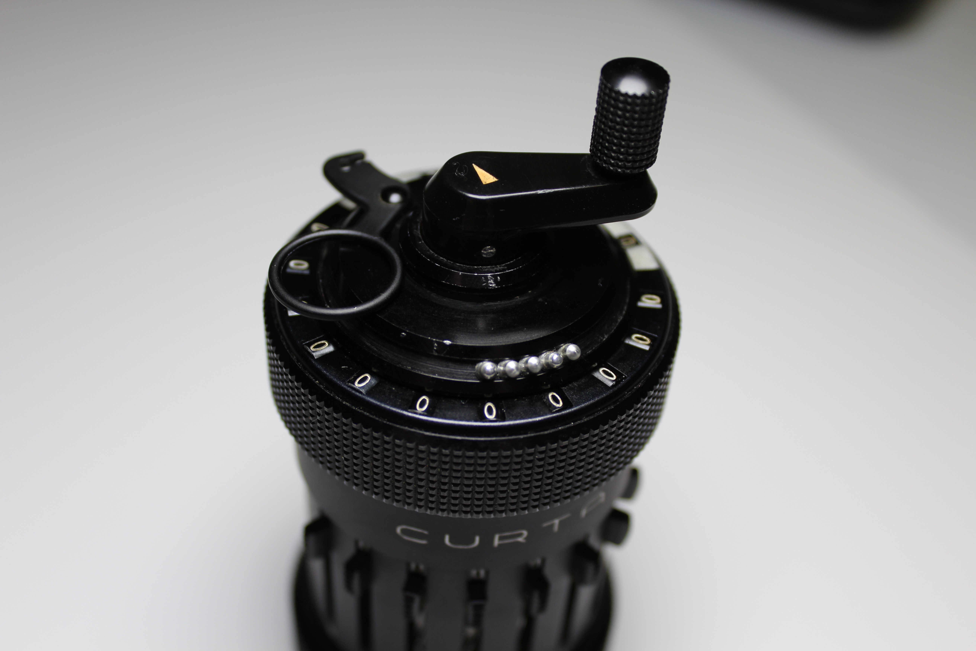
reference-photos/IMG_1042.jpg
