daeken/ReCurta/reference-photos/IMG_1044.jpg

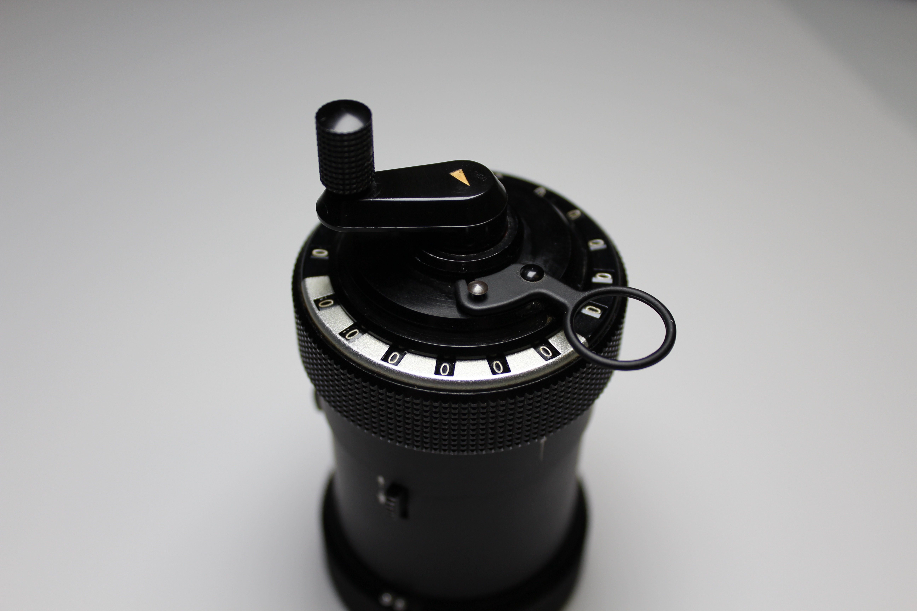
reference-photos/IMG_1044.jpg
