daeken/ReCurta/reference-photos/IMG_1046.jpg

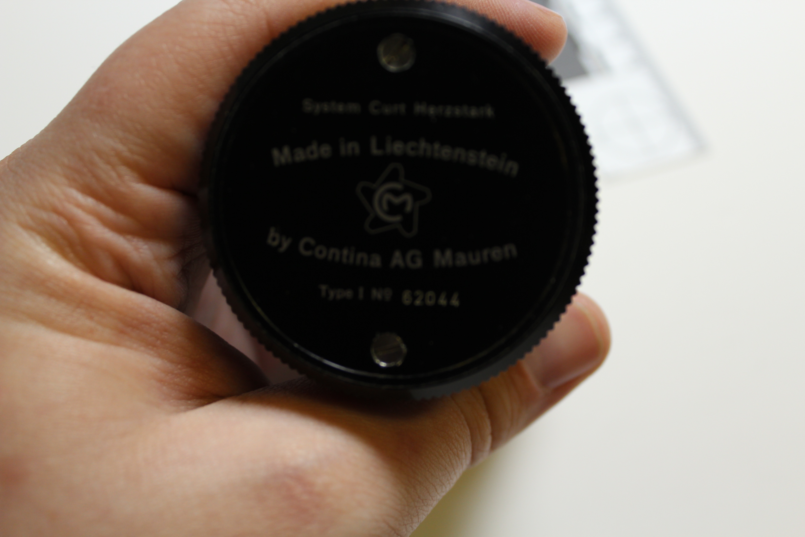
reference-photos/IMG_1046.jpg
