daeken/ReCurta/reference-photos/IMG_1052.jpg

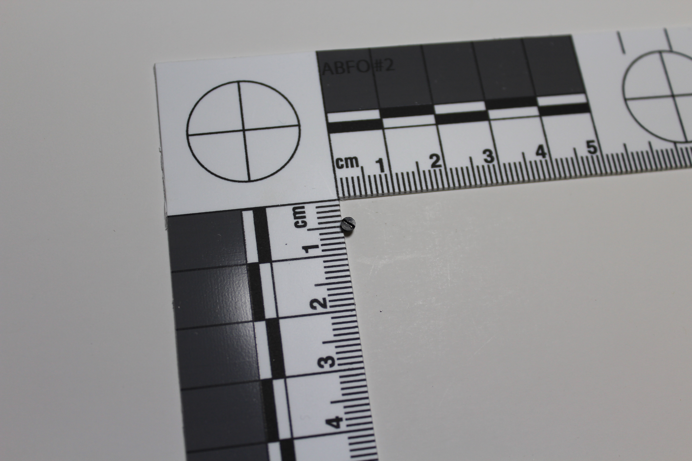
reference-photos/IMG_1052.jpg
