daeken/ReCurta/reference-photos/IMG_1053.jpg

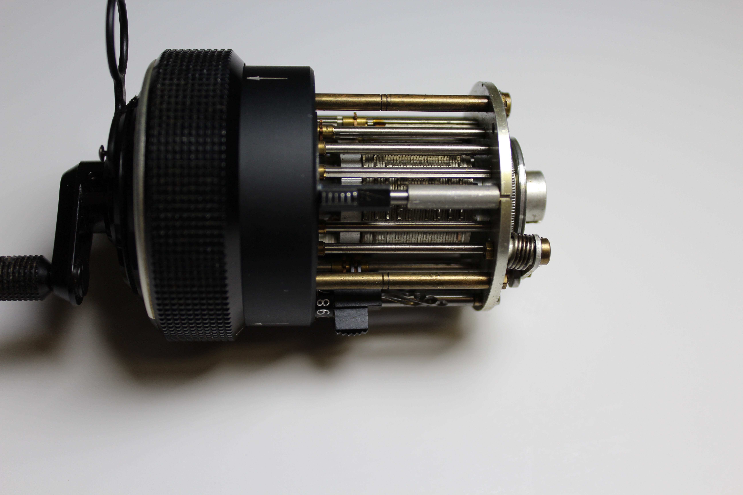
reference-photos/IMG_1053.jpg
