daeken/ReCurta/reference-photos/IMG_1057.jpg

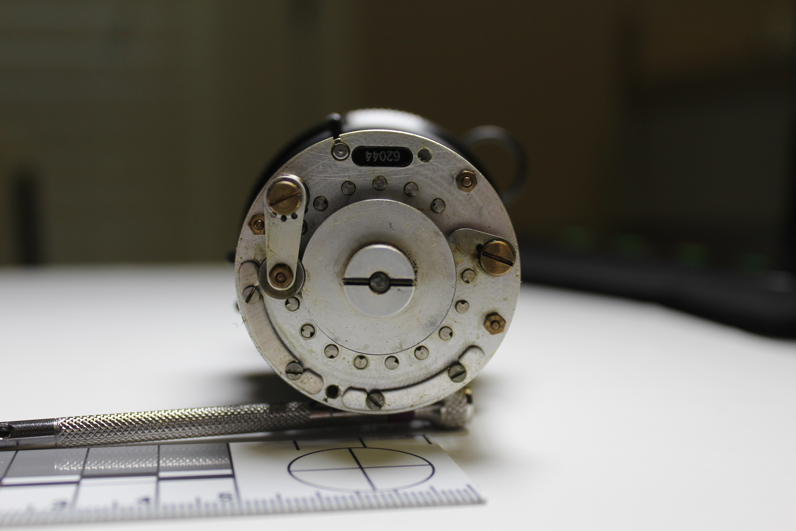
reference-photos/IMG_1057.jpg
