daeken/ReCurta/reference-photos/IMG_1095.jpg

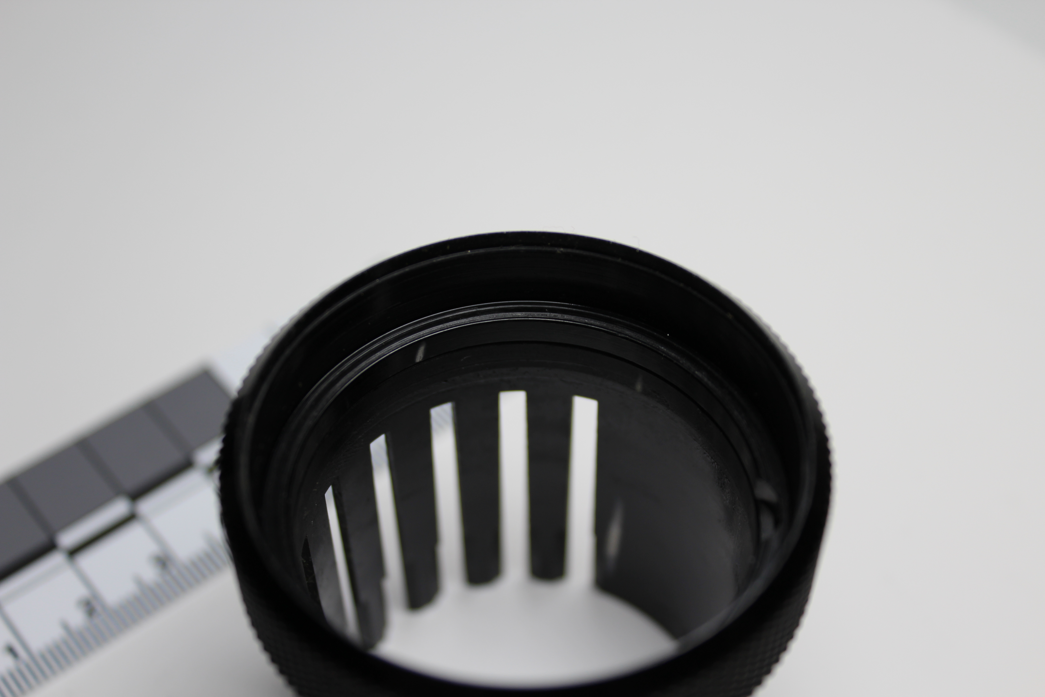
reference-photos/IMG_1095.jpg
