daeken/ReCurta/reference-photos/tn_Img_2981-3100-3121.jpg

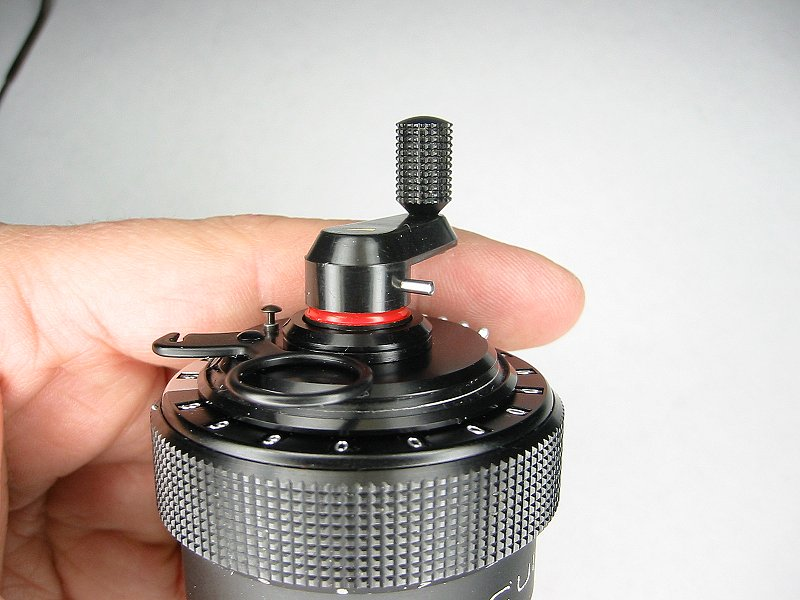
reference-photos/tn_Img_2981-3100-3121.jpg
