daeken/ReCurta/reference-photos/tn_Img_2986-3038.jpg

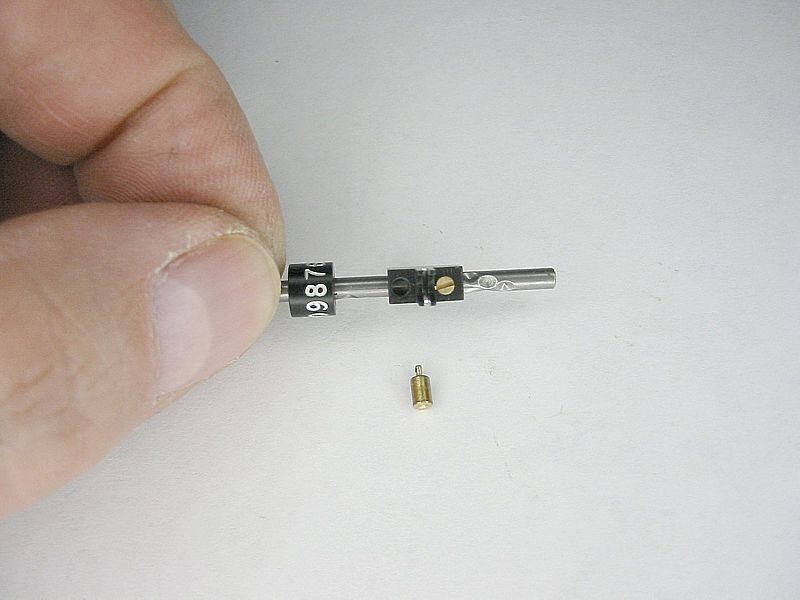
reference-photos/tn_Img_2986-3038.jpg
