daeken/ReCurta/reference-photos/tn_Img_2987.jpg

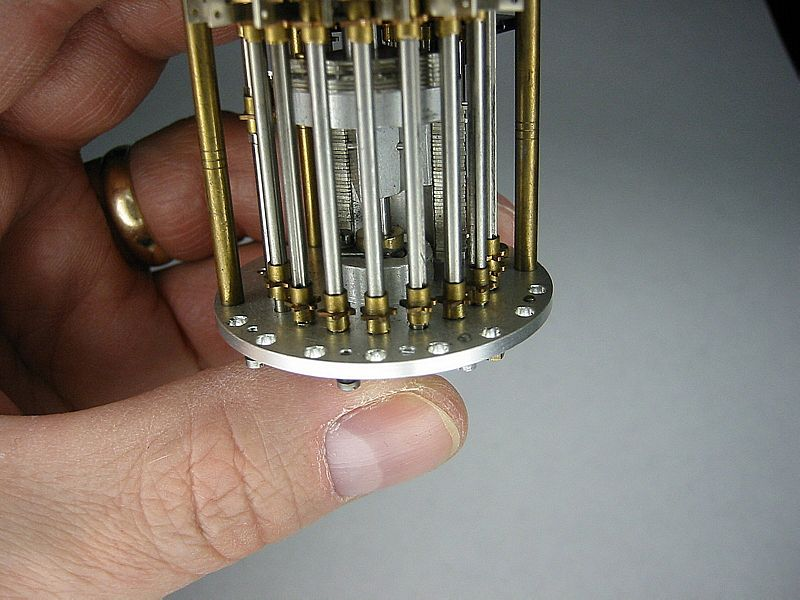
reference-photos/tn_Img_2987.jpg
