daeken/ReCurta/reference-photos/tn_Img_2988.jpg

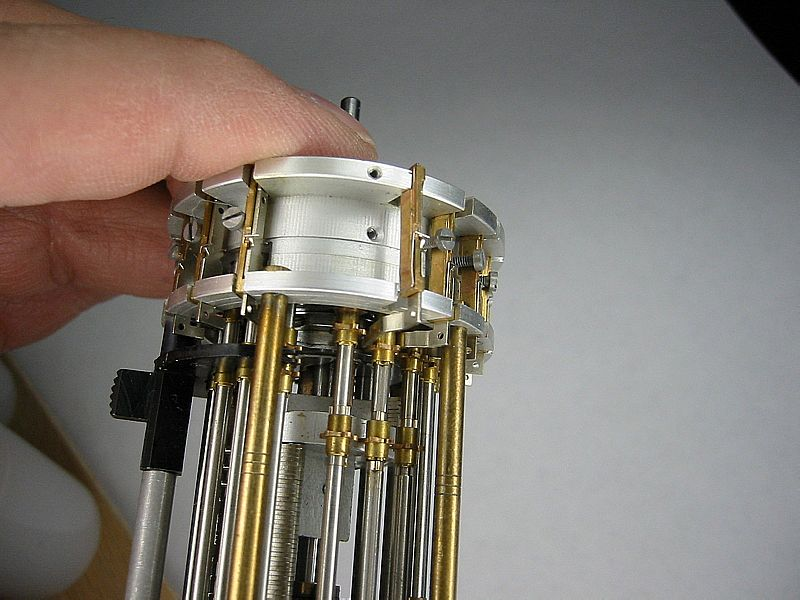
reference-photos/tn_Img_2988.jpg
