daeken/ReCurta/reference-photos/tn_Img_2990.jpg

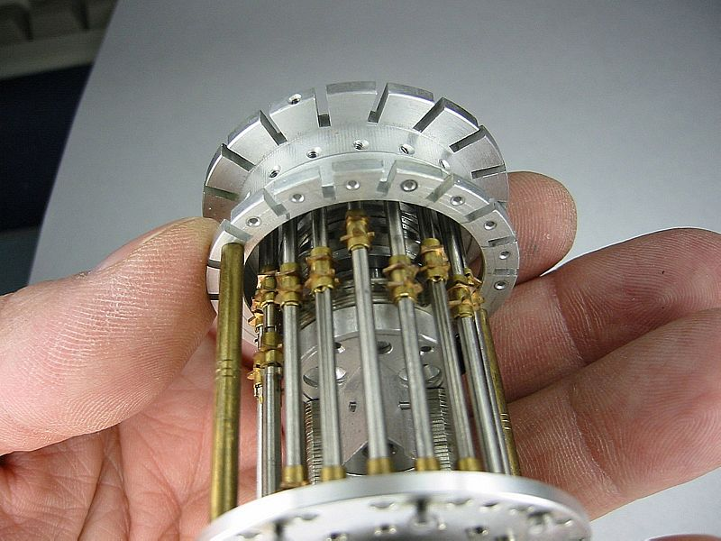
reference-photos/tn_Img_2990.jpg
