daeken/ReCurta/reference-photos/tn_Img_2991-3027.jpg

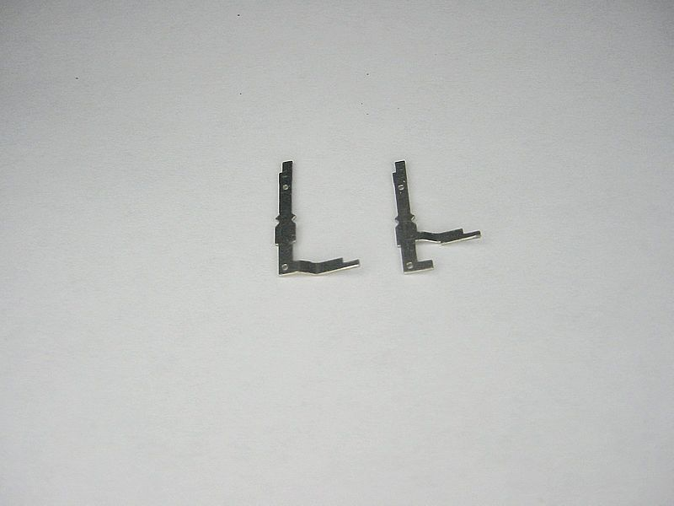
reference-photos/tn_Img_2991-3027.jpg
