daeken/ReCurta/reference-photos/tn_Img_2991-3028.jpg

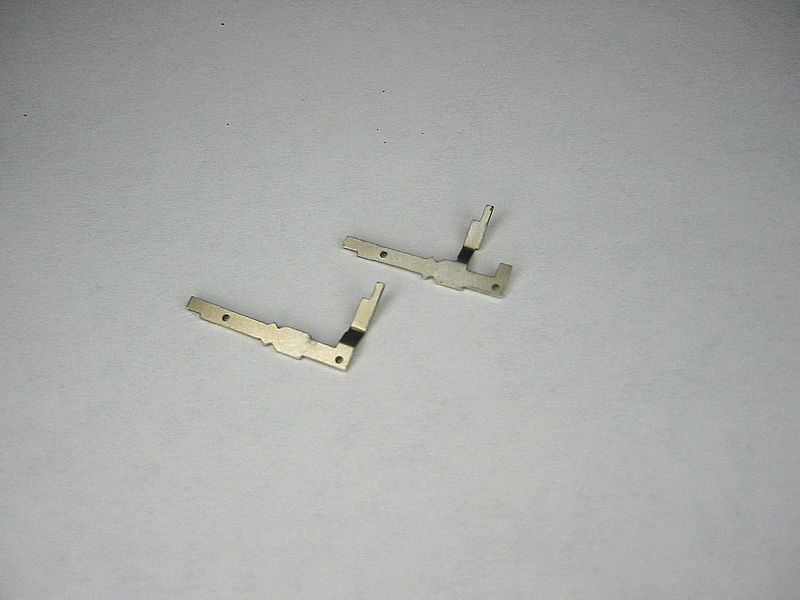
reference-photos/tn_Img_2991-3028.jpg
