daeken/ReCurta/reference-photos/tn_Img_2995-3041.jpg

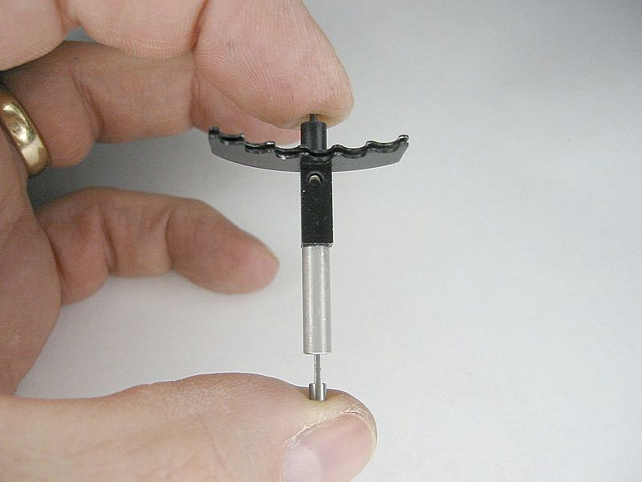
reference-photos/tn_Img_2995-3041.jpg
