daeken/ReCurta/reference-photos/tn_Img_2995-3046.jpg

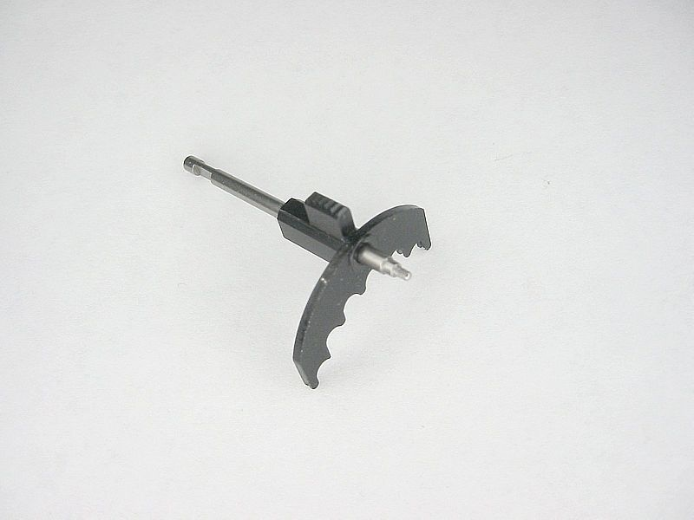
reference-photos/tn_Img_2995-3046.jpg
