daeken/ReCurta/reference-photos/tn_Img_2995-3115-3056.jpg

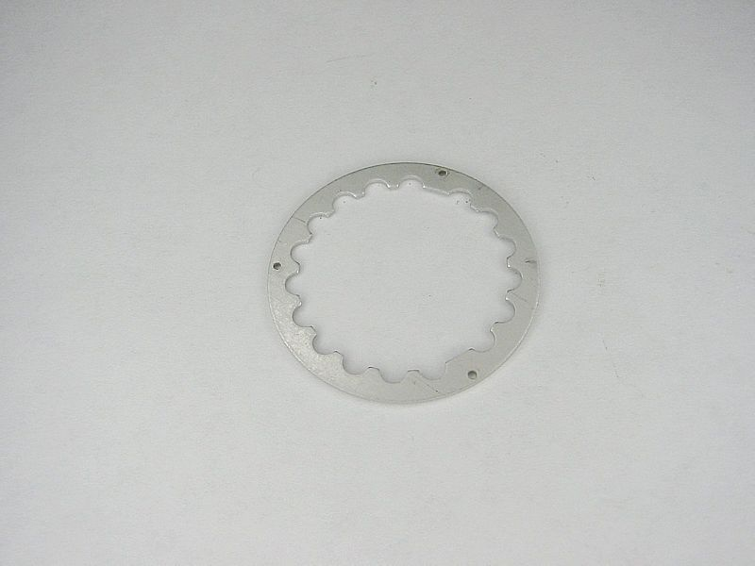
reference-photos/tn_Img_2995-3115-3056.jpg
