daeken/ReCurta/reference-photos/tn_Img_2996-2995.jpg

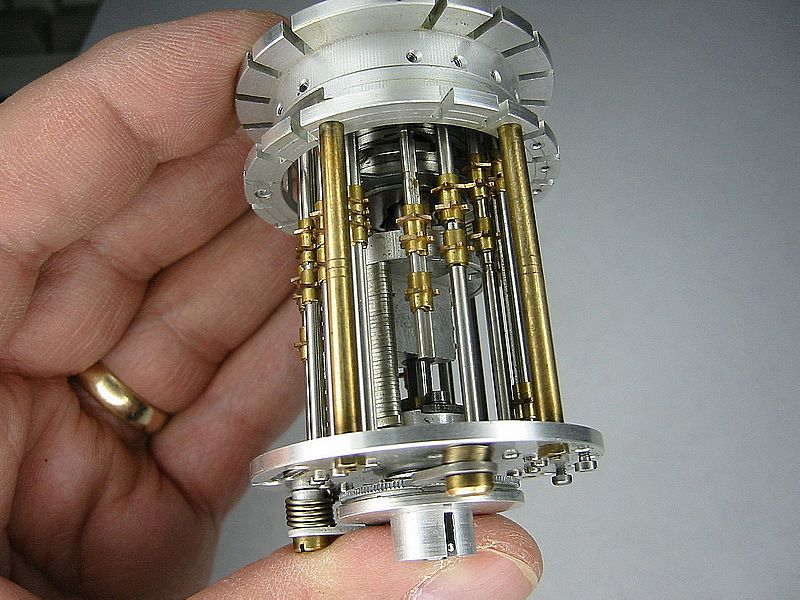
reference-photos/tn_Img_2996-2995.jpg
