daeken/ReCurta/reference-photos/tn_Img_2997a.jpg

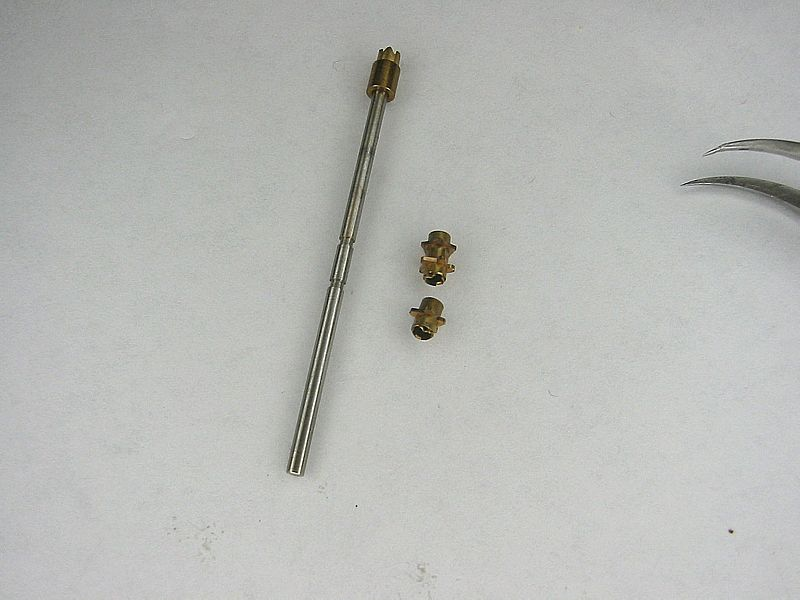
reference-photos/tn_Img_2997a.jpg
