daeken/ReCurta/reference-photos/tn_Img_2998-3030.jpg

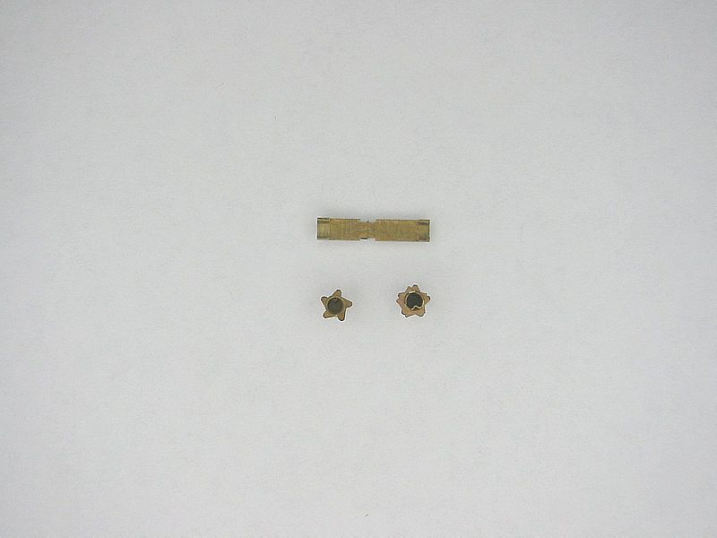
reference-photos/tn_Img_2998-3030.jpg
