daeken/ReCurta/reference-photos/tn_Img_2998-3031.jpg

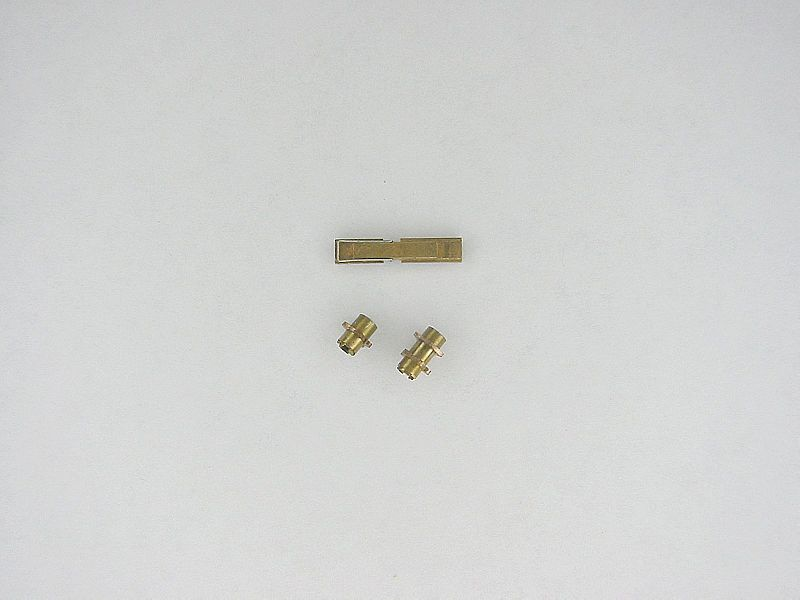
reference-photos/tn_Img_2998-3031.jpg
