daeken/ReCurta/reference-photos/tn_Img_2998a.jpg

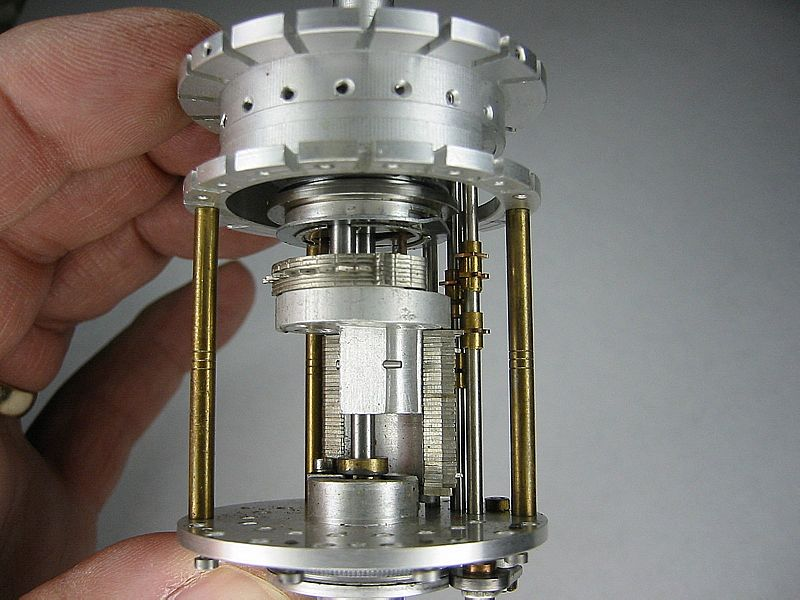
reference-photos/tn_Img_2998a.jpg
