daeken/ReCurta/reference-photos/tn_Img_2999.jpg

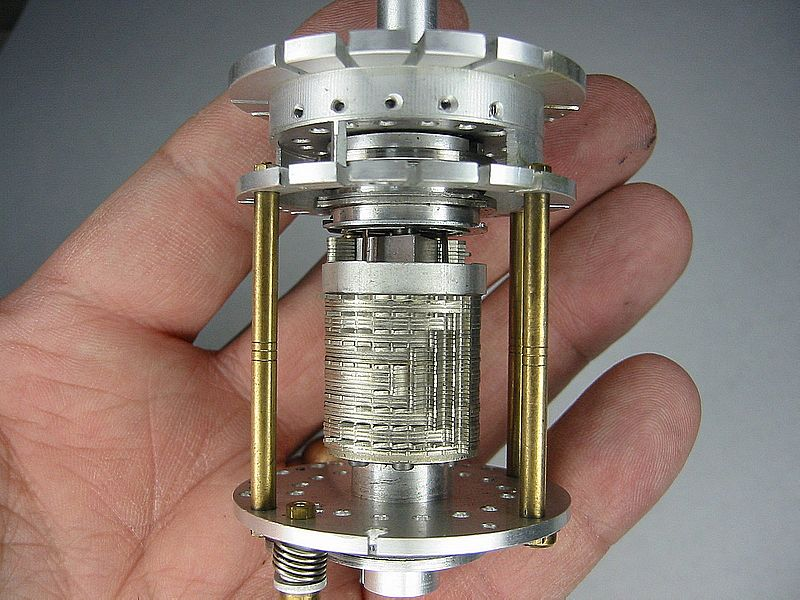
reference-photos/tn_Img_2999.jpg
