daeken/ReCurta/reference-photos/tn_Img_3001.jpg

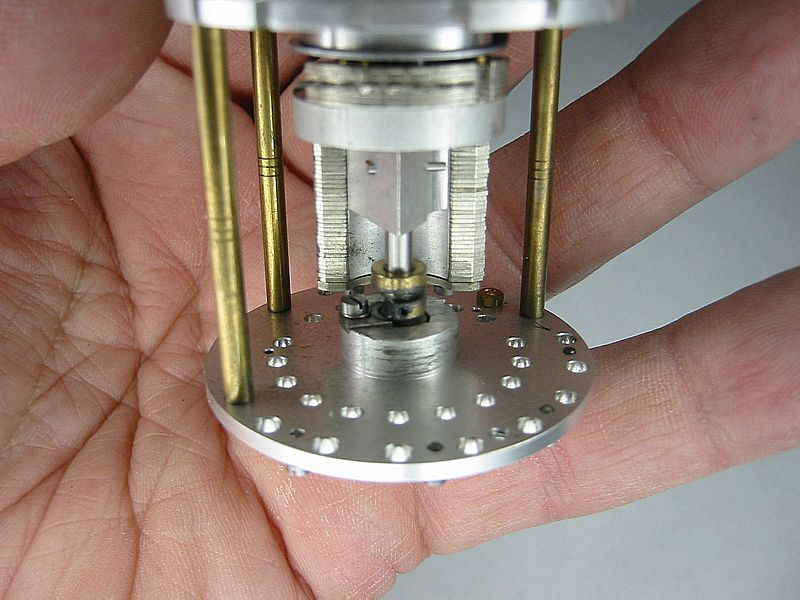
reference-photos/tn_Img_3001.jpg
