daeken/ReCurta/reference-photos/tn_Img_3004.jpg

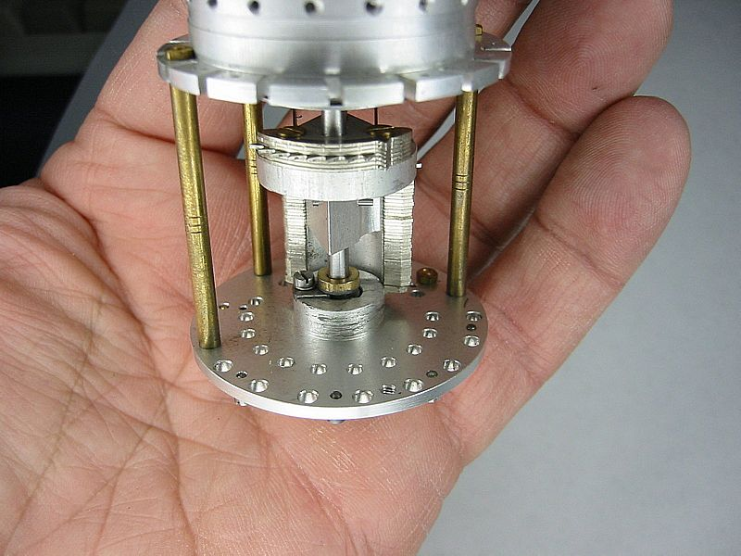
reference-photos/tn_Img_3004.jpg
