daeken/ReCurta/reference-photos/tn_Img_3007.jpg

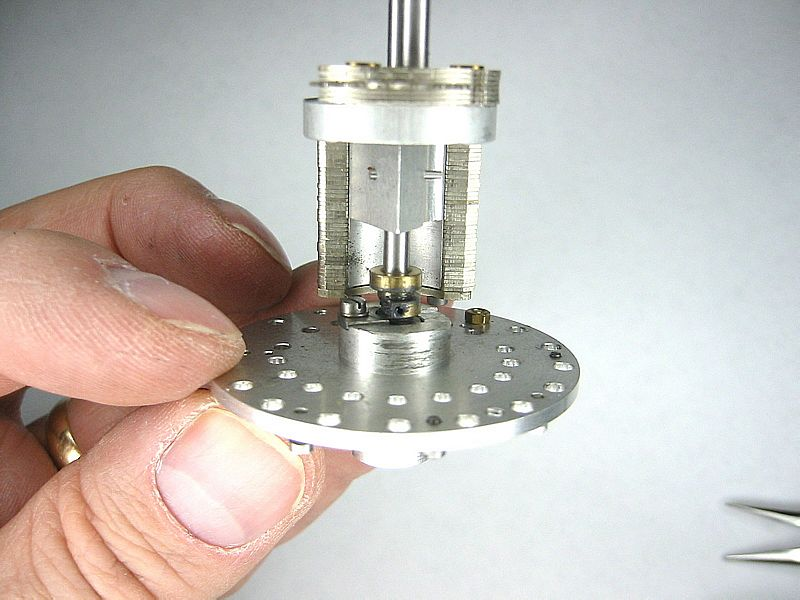
reference-photos/tn_Img_3007.jpg
