daeken/ReCurta/reference-photos/tn_Img_3008.jpg

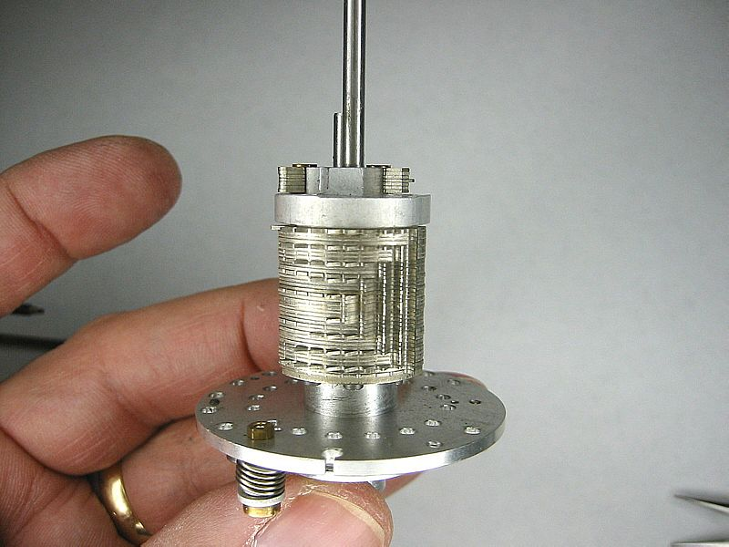
reference-photos/tn_Img_3008.jpg
