daeken/ReCurta/reference-photos/tn_Img_3009-3091.jpg

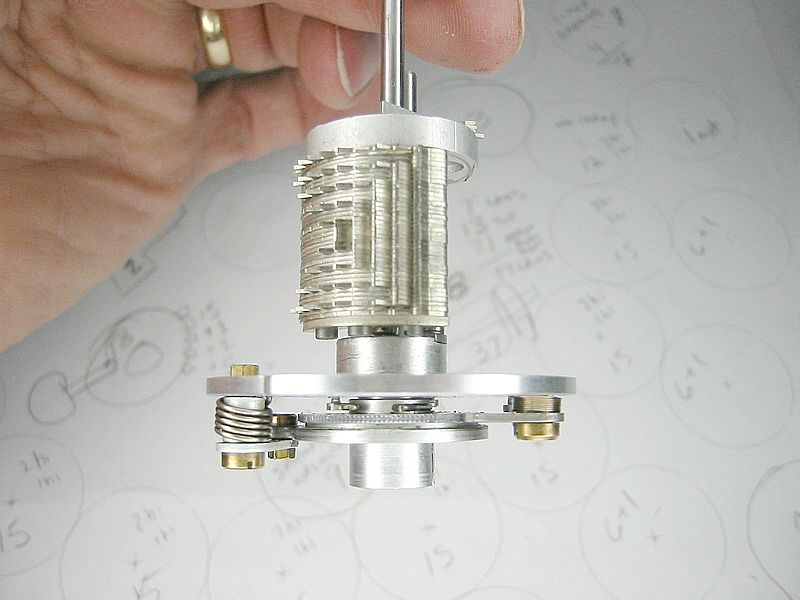
reference-photos/tn_Img_3009-3091.jpg
