daeken/ReCurta/reference-photos/tn_Img_3011.jpg

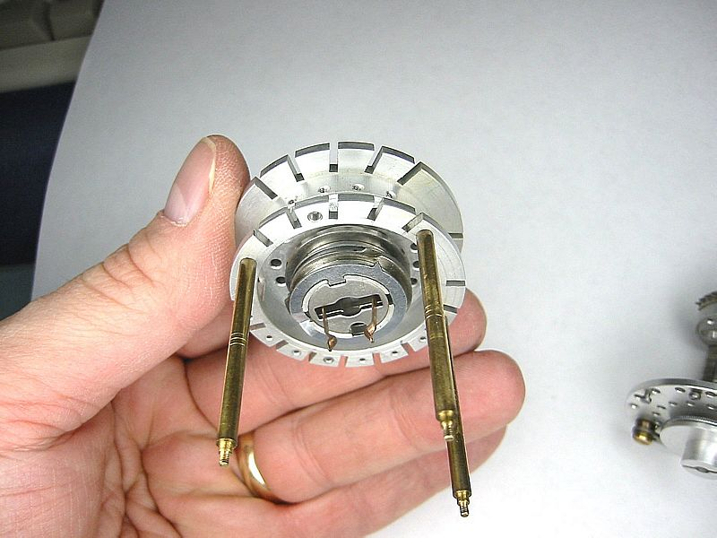
reference-photos/tn_Img_3011.jpg
