daeken/ReCurta/reference-photos/tn_Img_3014a.jpg

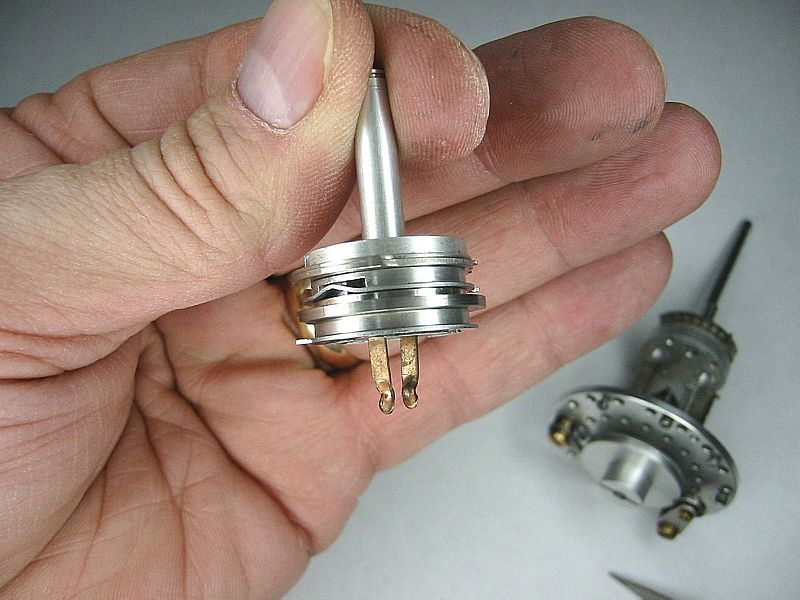
reference-photos/tn_Img_3014a.jpg
