daeken/ReCurta/reference-photos/tn_Img_3019.jpg

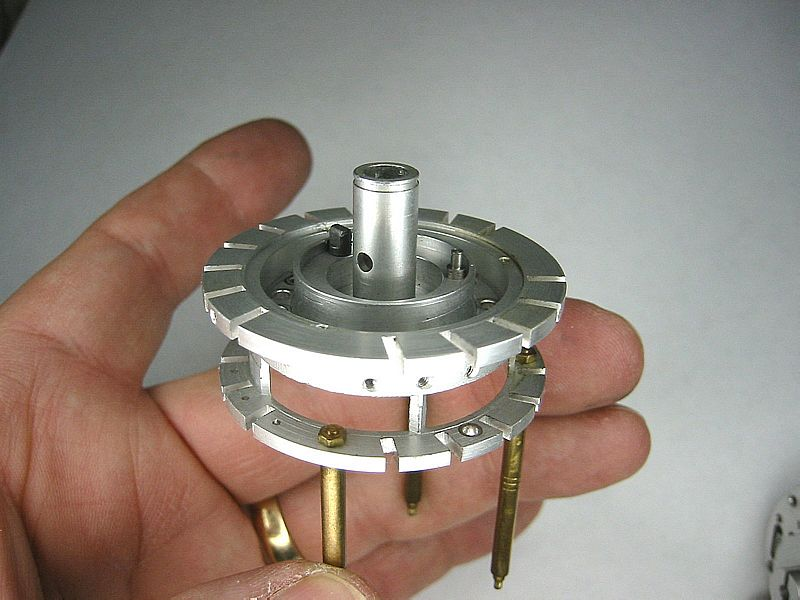
reference-photos/tn_Img_3019.jpg
