daeken/ReCurta/reference-photos/tn_Img_3020.jpg

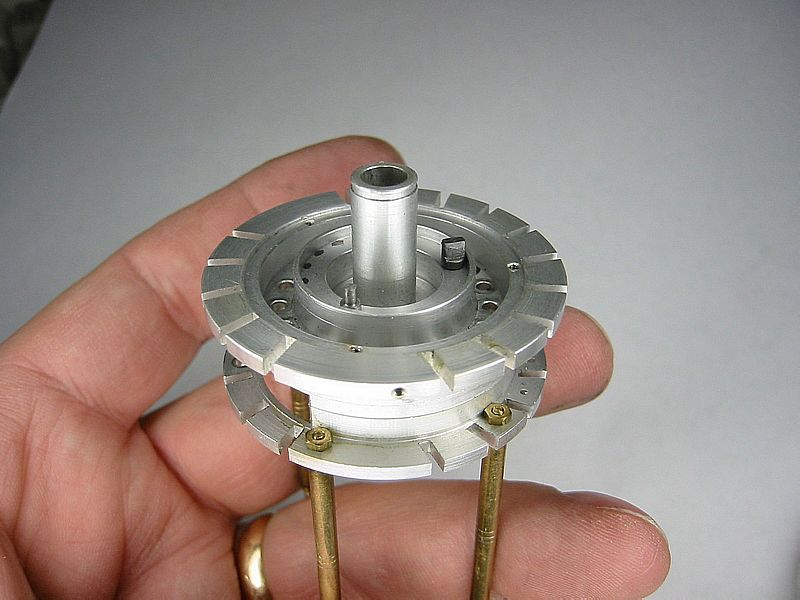
reference-photos/tn_Img_3020.jpg
