daeken/ReCurta/reference-photos/tn_Img_3048.jpg

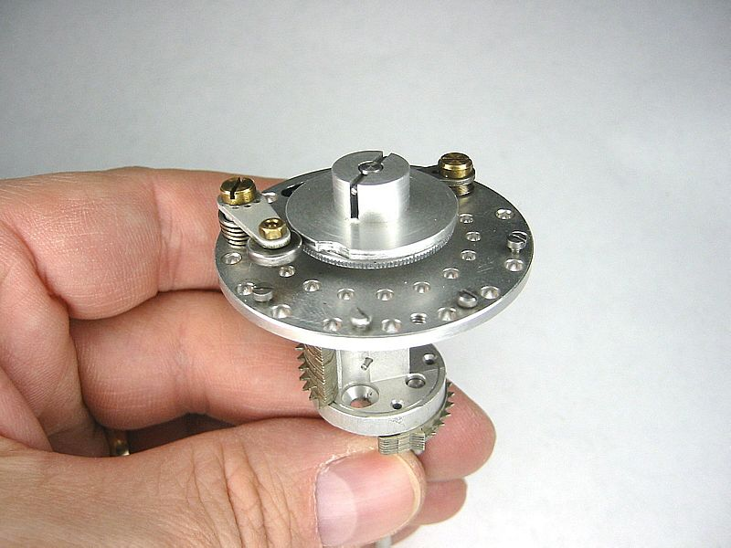
reference-photos/tn_Img_3048.jpg
