daeken/ReCurta/reference-photos/tn_Img_3049.jpg

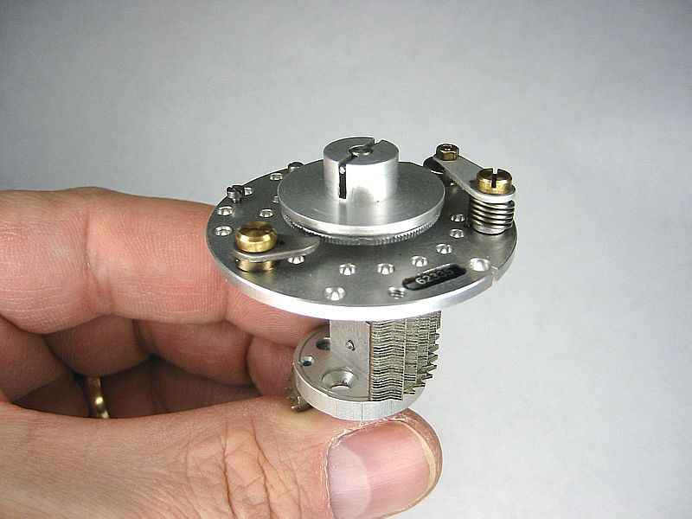
reference-photos/tn_Img_3049.jpg
