daeken/ReCurta/reference-photos/tn_Img_3050.jpg

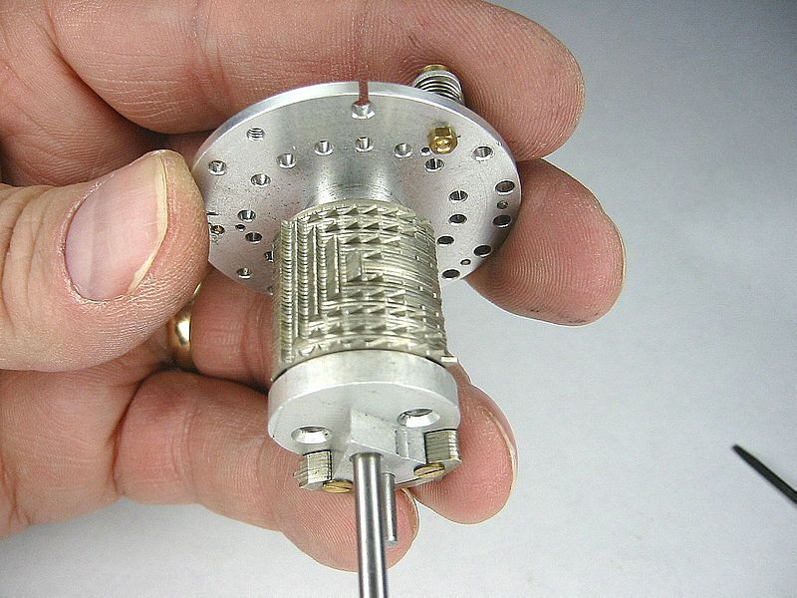
reference-photos/tn_Img_3050.jpg
