daeken/ReCurta/reference-photos/tn_Img_3060.jpg

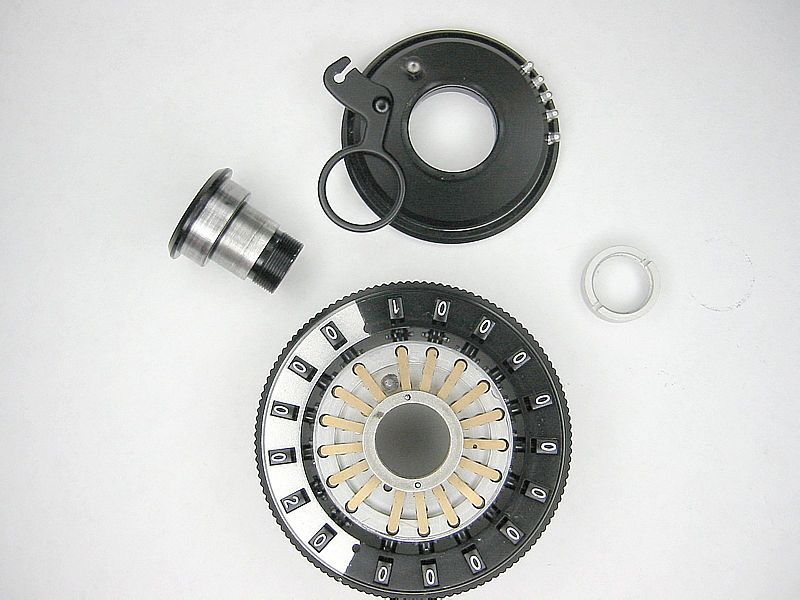
reference-photos/tn_Img_3060.jpg
