daeken/ReCurta/reference-photos/tn_Img_3061.jpg

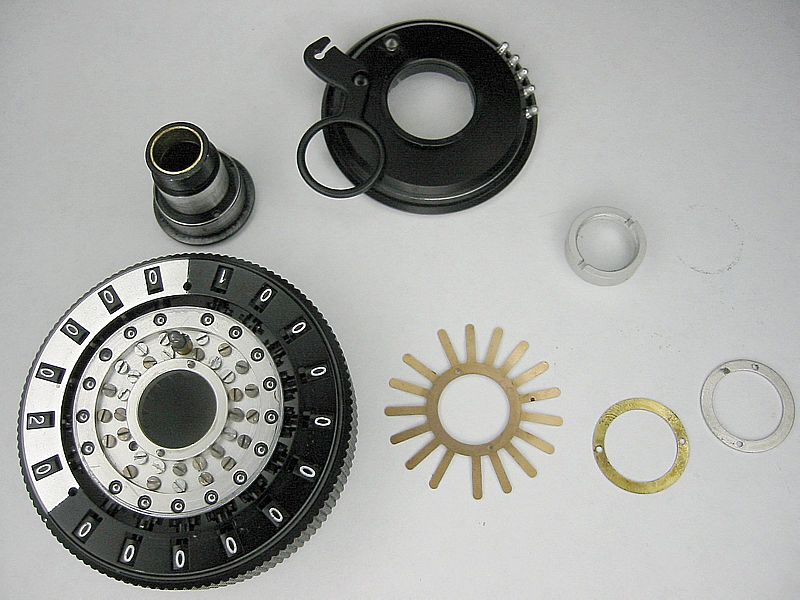
reference-photos/tn_Img_3061.jpg
