daeken/ReCurta/reference-photos/tn_Img_3062.jpg

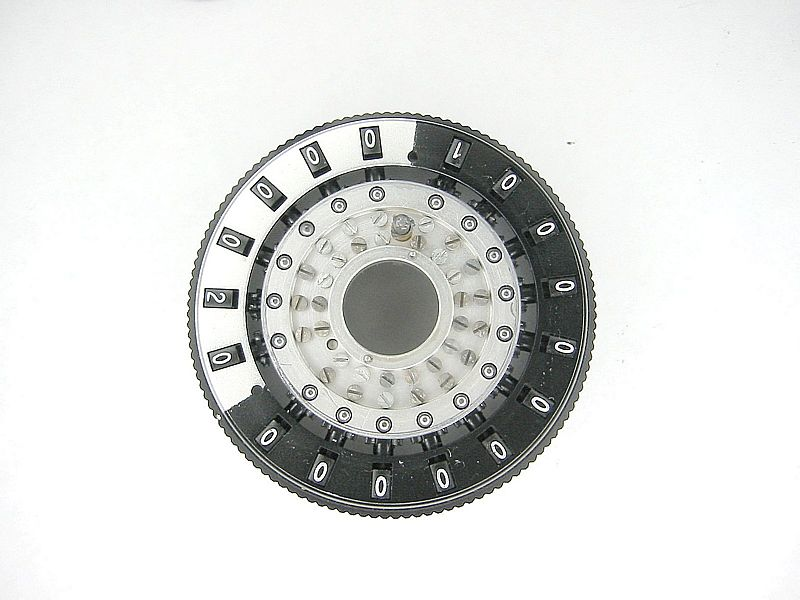
reference-photos/tn_Img_3062.jpg
