daeken/ReCurta/reference-photos/tn_Img_3063.jpg

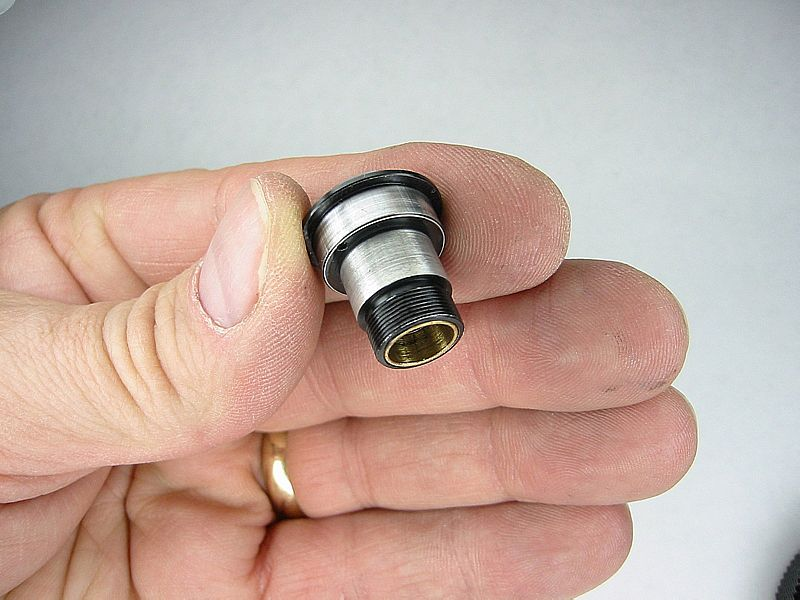
reference-photos/tn_Img_3063.jpg
