daeken/ReCurta/reference-photos/tn_Img_3066a-3072.jpg

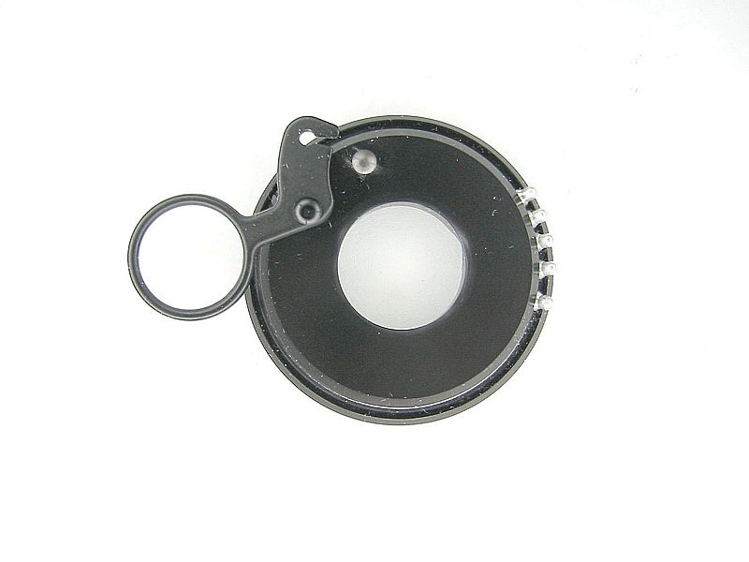
reference-photos/tn_Img_3066a-3072.jpg
