daeken/ReCurta/reference-photos/tn_Img_3067.jpg

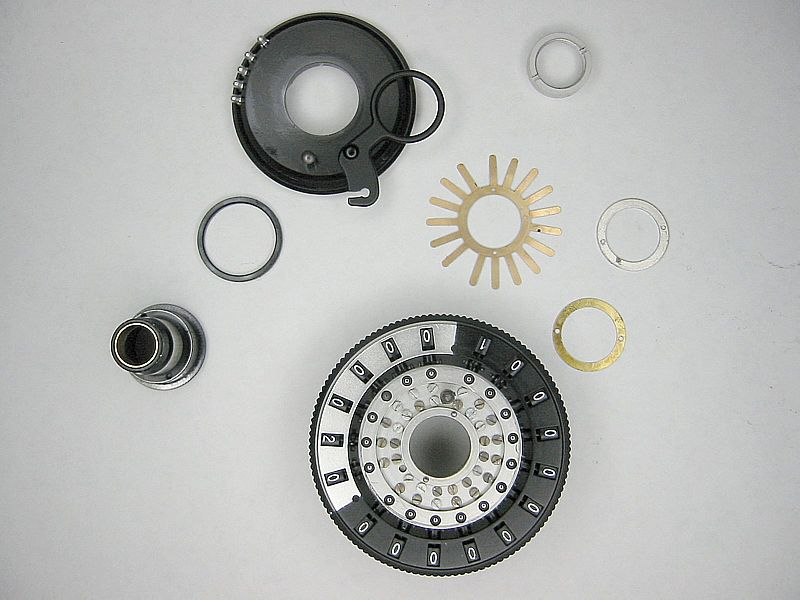
reference-photos/tn_Img_3067.jpg
