daeken/ReCurta/reference-photos/tn_Img_3069.jpg

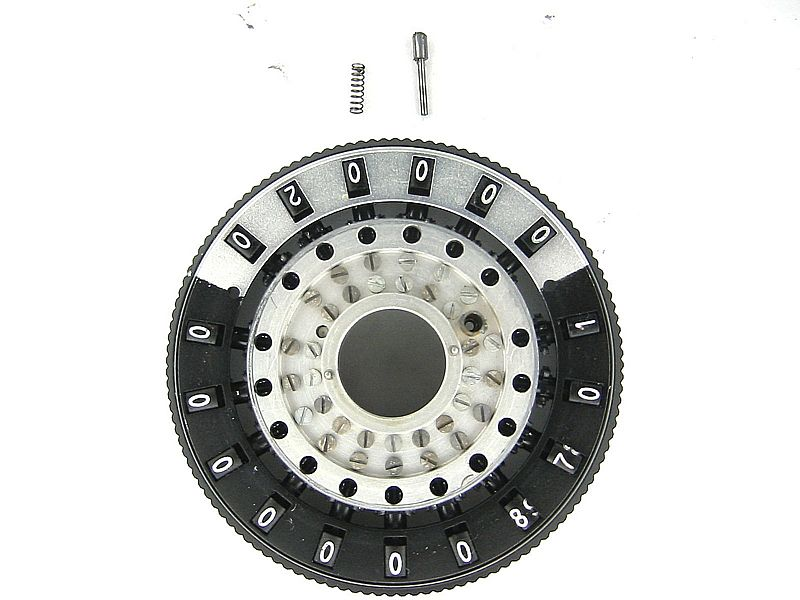
reference-photos/tn_Img_3069.jpg
