daeken/ReCurta/reference-photos/tn_Img_3071.jpg

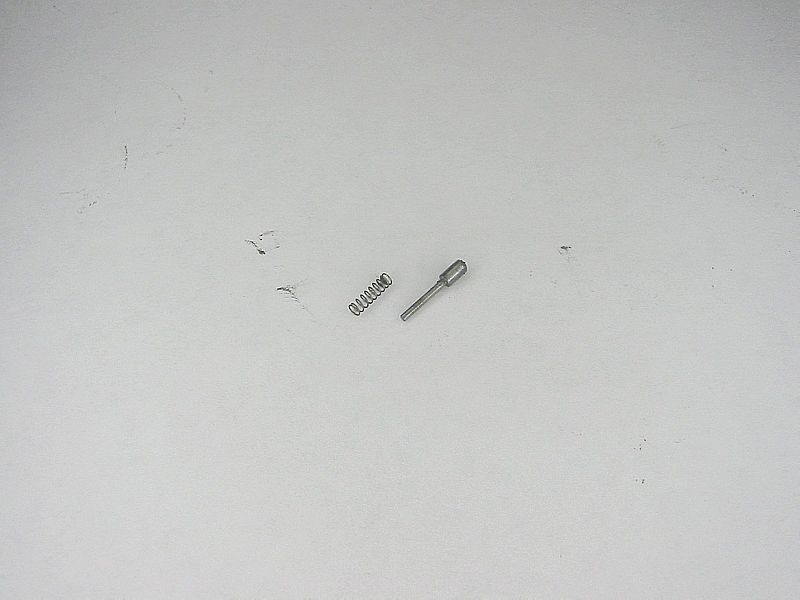
reference-photos/tn_Img_3071.jpg
