daeken/ReCurta/STL Models/10101.stl

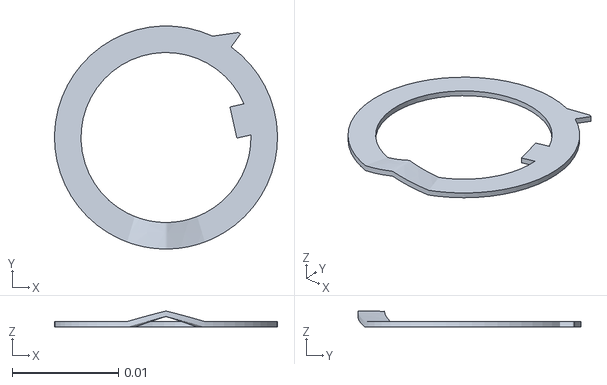
[picture p216: CAD file, 2015-10-22]
STL Models/10101.stl
0.021 x 0.021 x 0.00148
