daeken/ReCurta/Solidworks Drawings/10112.sldprt

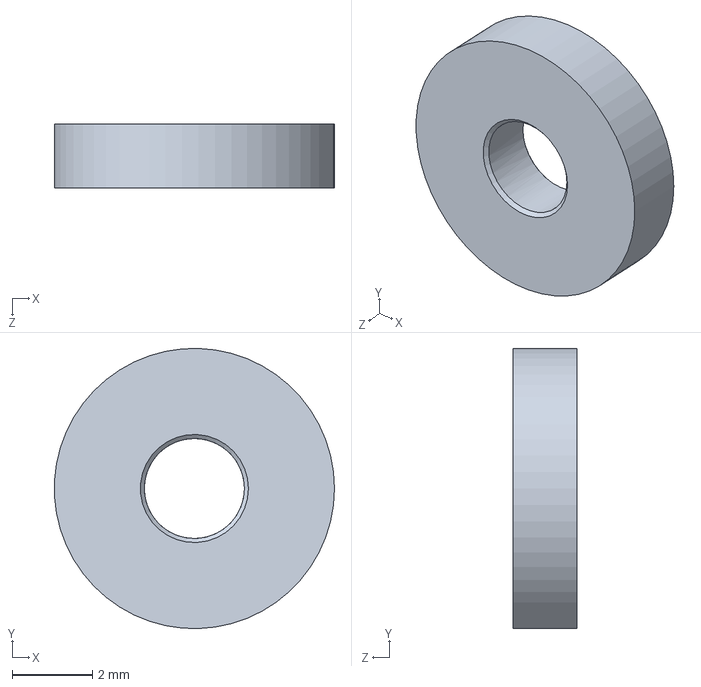
[picture p217: CAD file, 2016-02-25]
Solidworks Drawings/10112.sldprt
6.99 x 7.00 x 1.60 mm
