daeken/ReCurta/STL Models/10006.stl

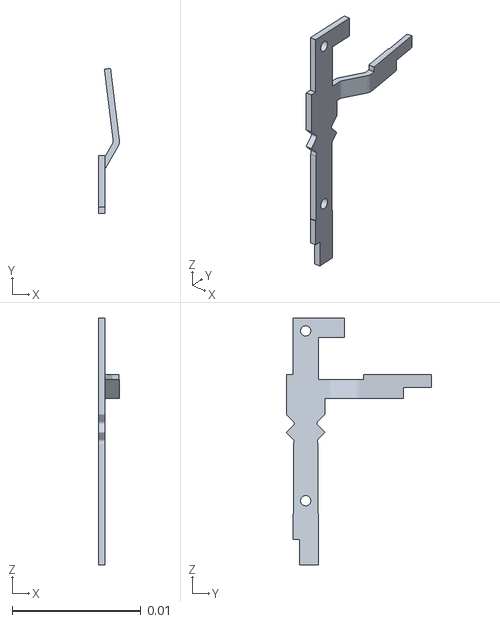
[picture p218: CAD file, 2015-10-22]
STL Models/10006.stl
0.00163 x 0.0113 x 0.0192
