daeken/ReCurta/Solidworks Drawings/10002.sldprt

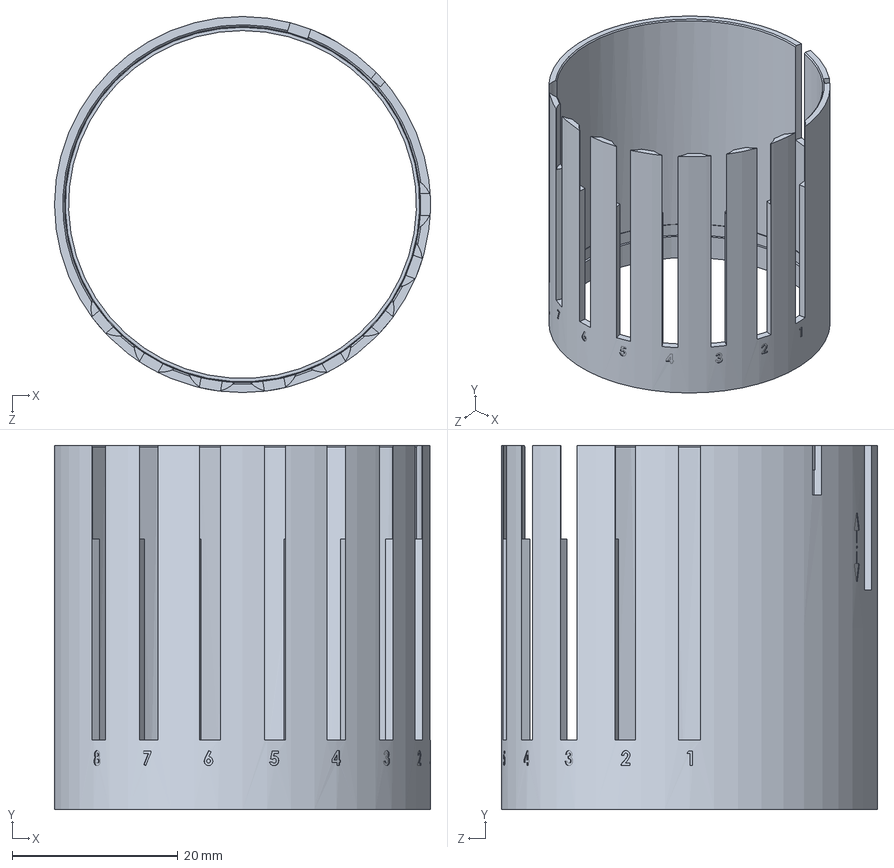
[picture p219: CAD file, 2016-02-25]
Solidworks Drawings/10002.sldprt
45.4 x 44.0 x 45.4 mm
