daeken/ReCurta/app/curta_jpegs/assembly/Curta_1_10203.jpg

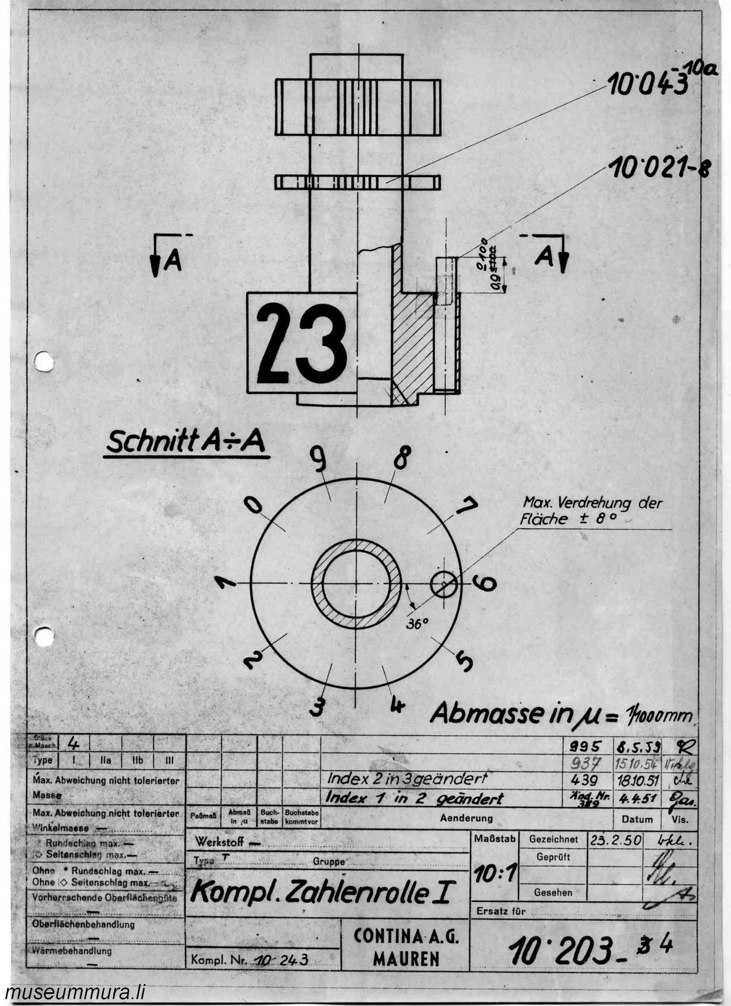
app/curta_jpegs/assembly/Curta_1_10203.jpg
