daeken/ReCurta/app/curta_jpegs/assembly/Curta_1_10204.jpg

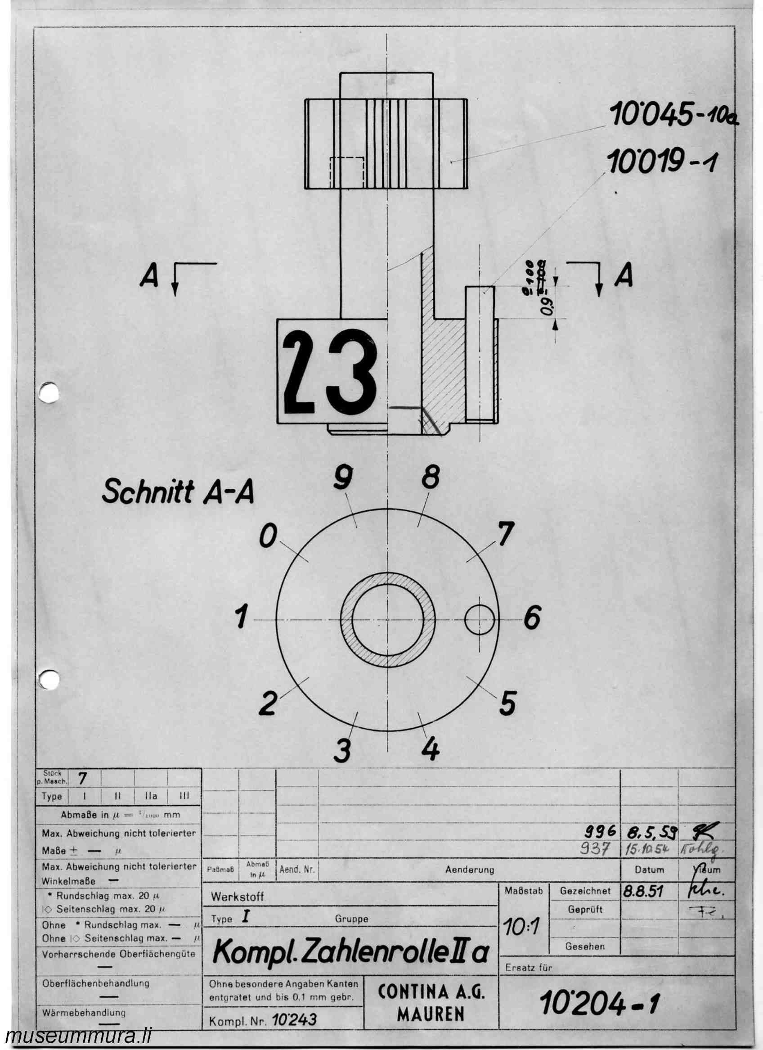
app/curta_jpegs/assembly/Curta_1_10204.jpg
