daeken/ReCurta/app/curta_jpegs/assembly/Curta_1_10205.jpg

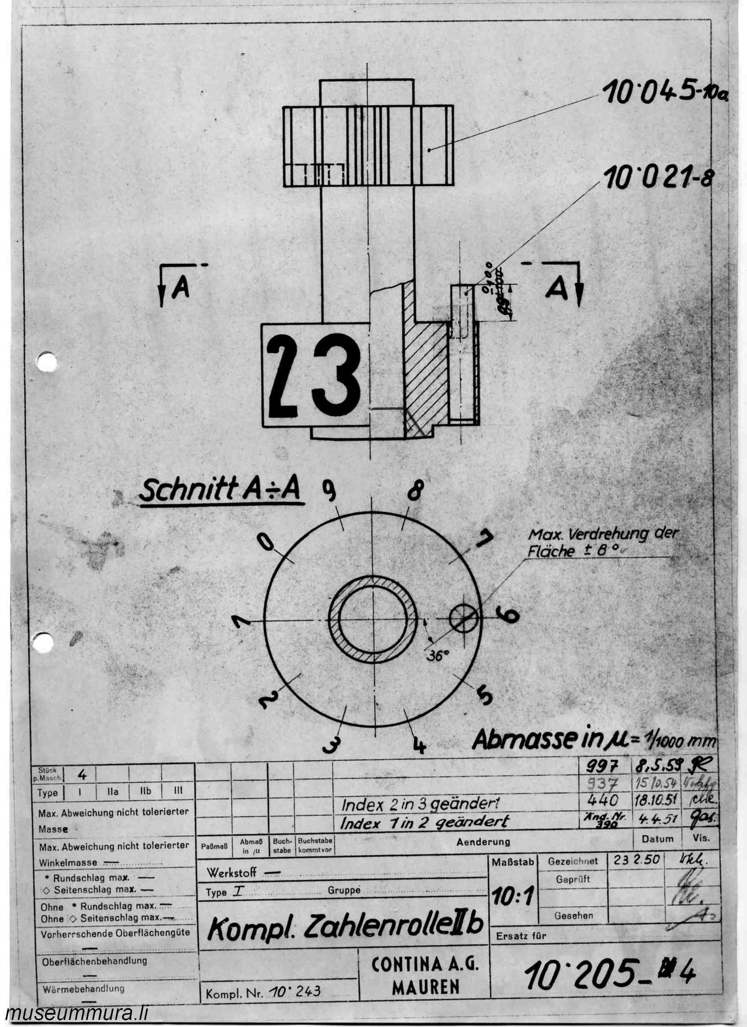
app/curta_jpegs/assembly/Curta_1_10205.jpg
