daeken/ReCurta/app/curta_jpegs/assembly/Curta_1_10206.jpg

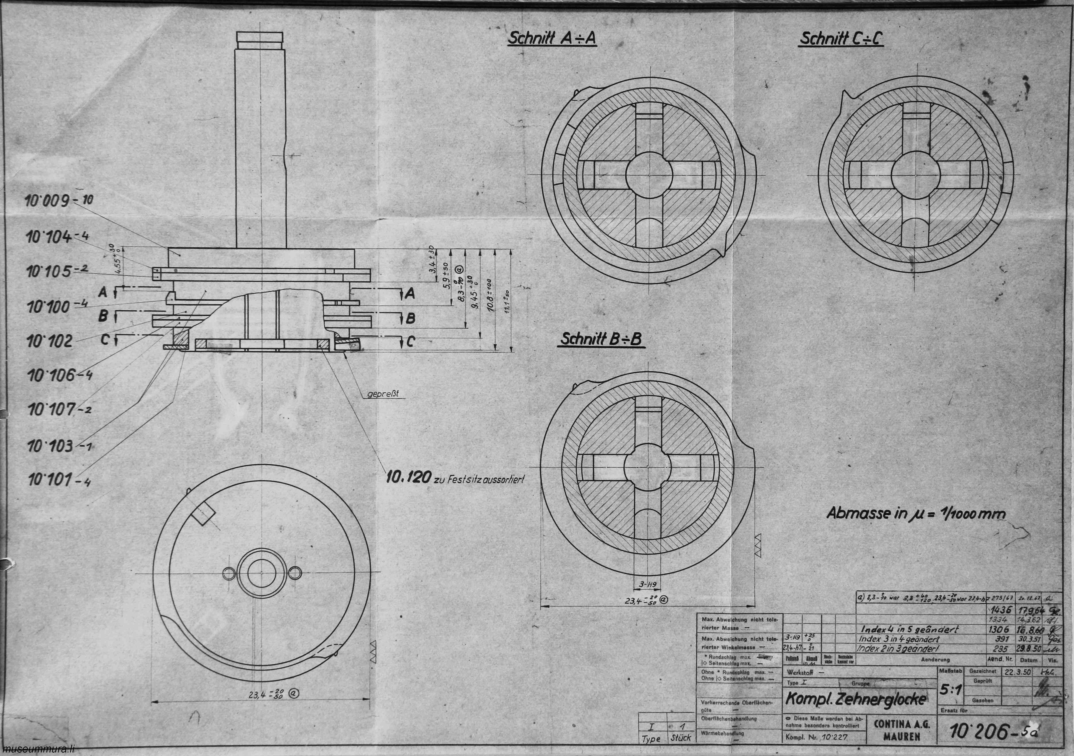
app/curta_jpegs/assembly/Curta_1_10206.jpg
