daeken/ReCurta/app/curta_jpegs/assembly/Curta_1_10207.jpg

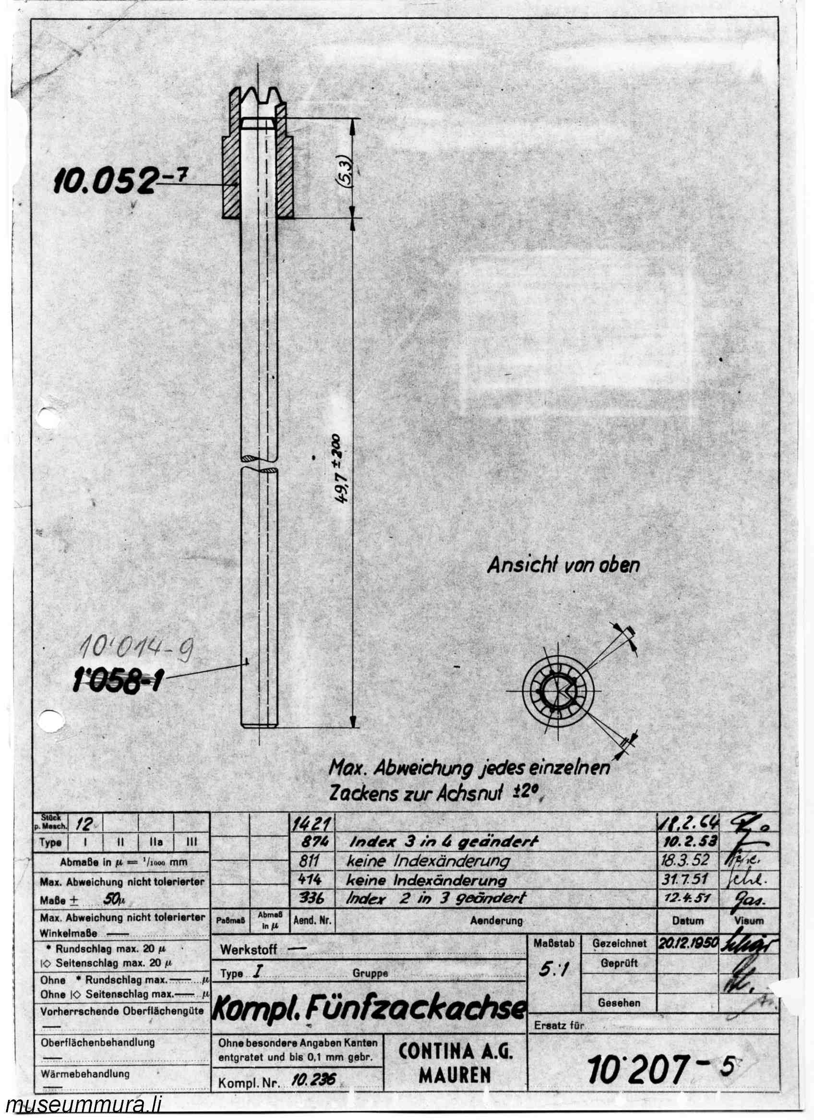
app/curta_jpegs/assembly/Curta_1_10207.jpg
