daeken/ReCurta/app/curta_jpegs/assembly/Curta_1_10208.jpg

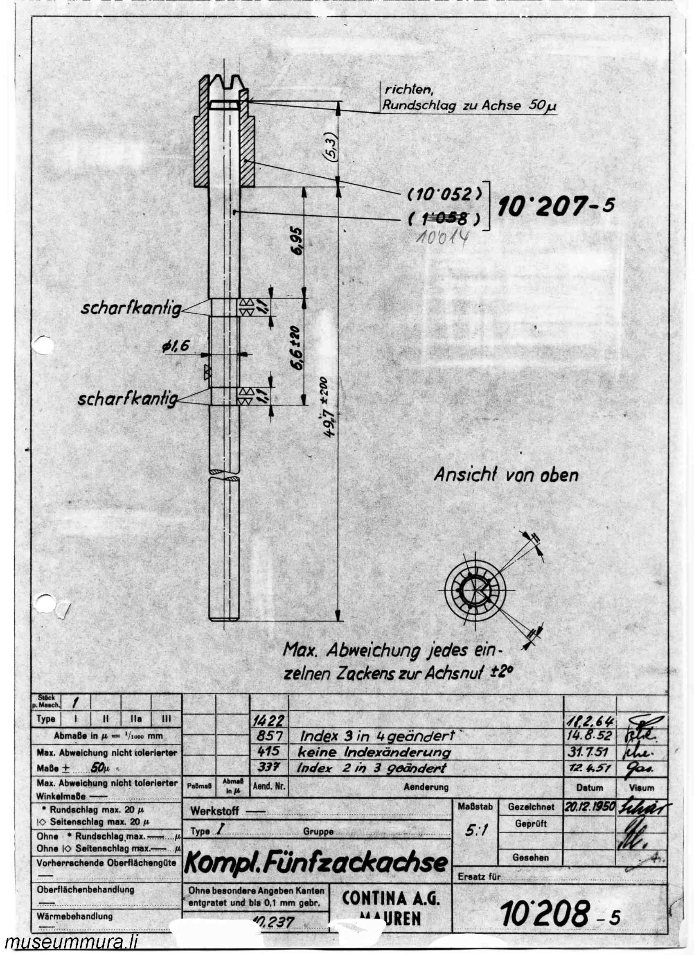
app/curta_jpegs/assembly/Curta_1_10208.jpg
