daeken/ReCurta/app/curta_jpegs/assembly/Curta_1_10209.jpg

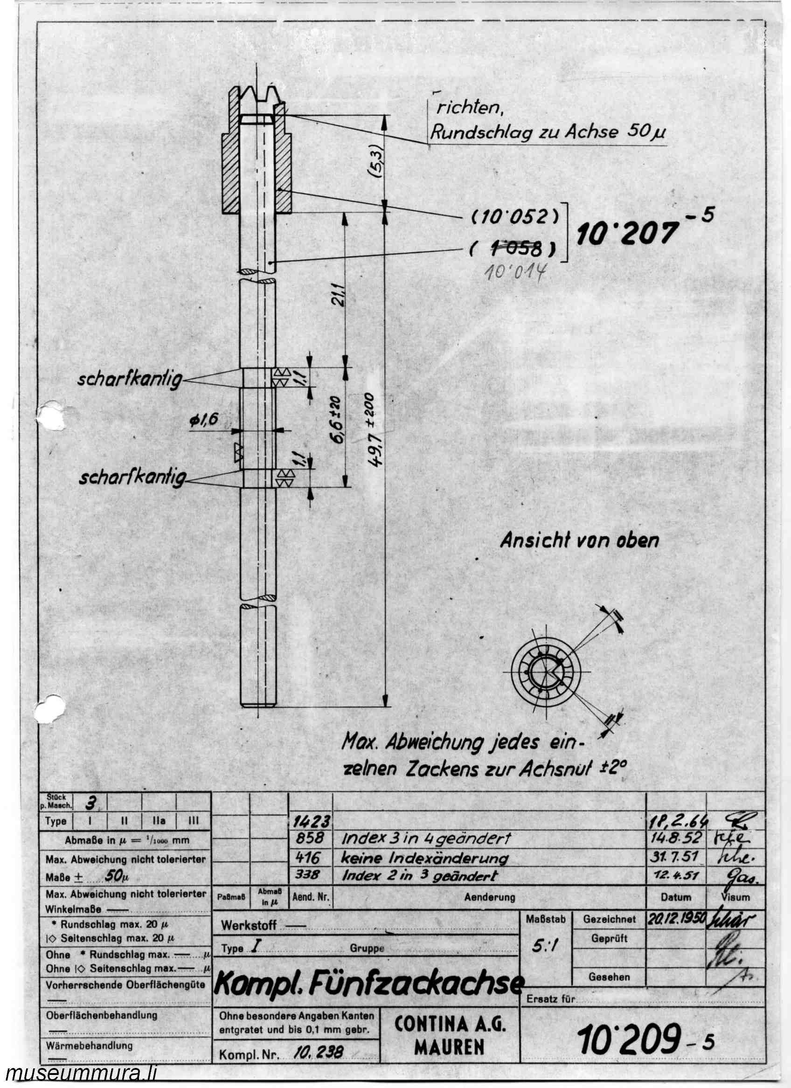
app/curta_jpegs/assembly/Curta_1_10209.jpg
