daeken/ReCurta/app/curta_jpegs/assembly/Curta_1_10210.jpg

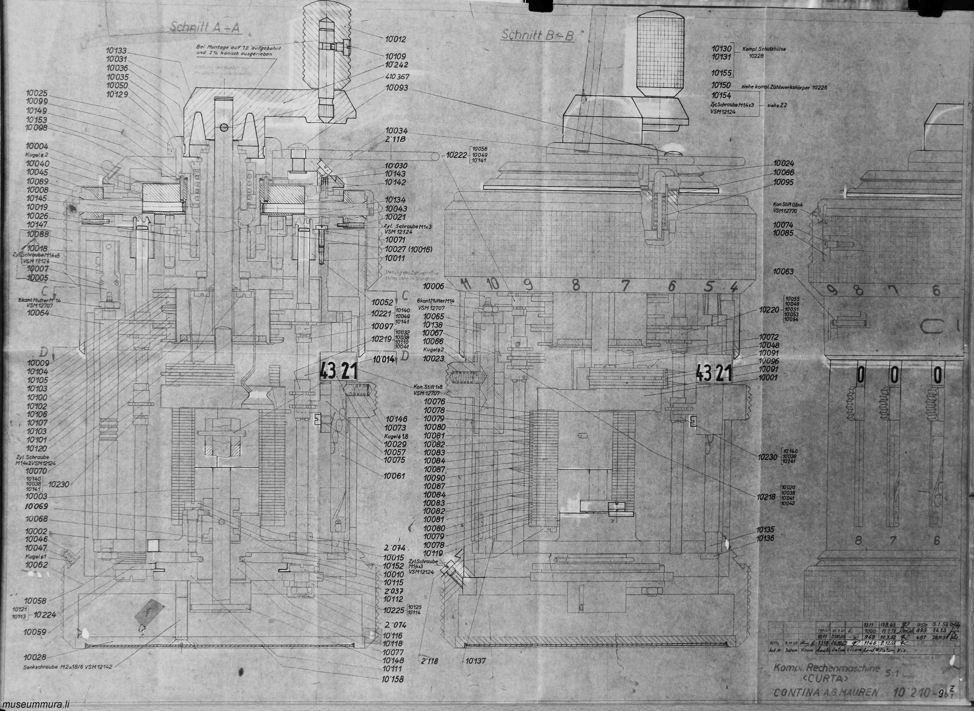
app/curta_jpegs/assembly/Curta_1_10210.jpg
