daeken/ReCurta/app/curta_jpegs/assembly/Curta_1_10210_1.jpg

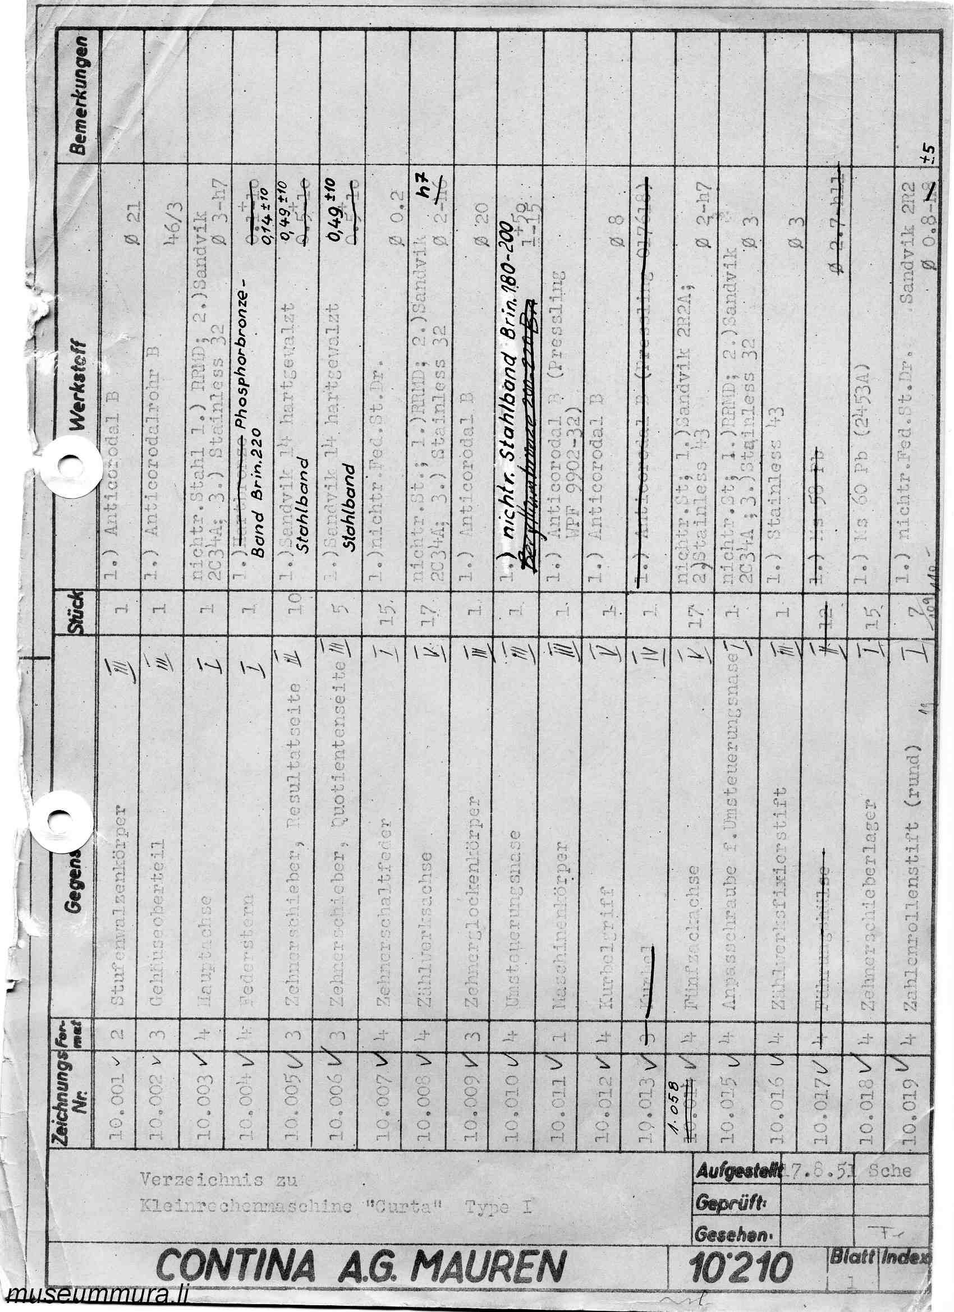
app/curta_jpegs/assembly/Curta_1_10210_1.jpg
