daeken/ReCurta/app/curta_jpegs/assembly/Curta_1_10210_4.jpg

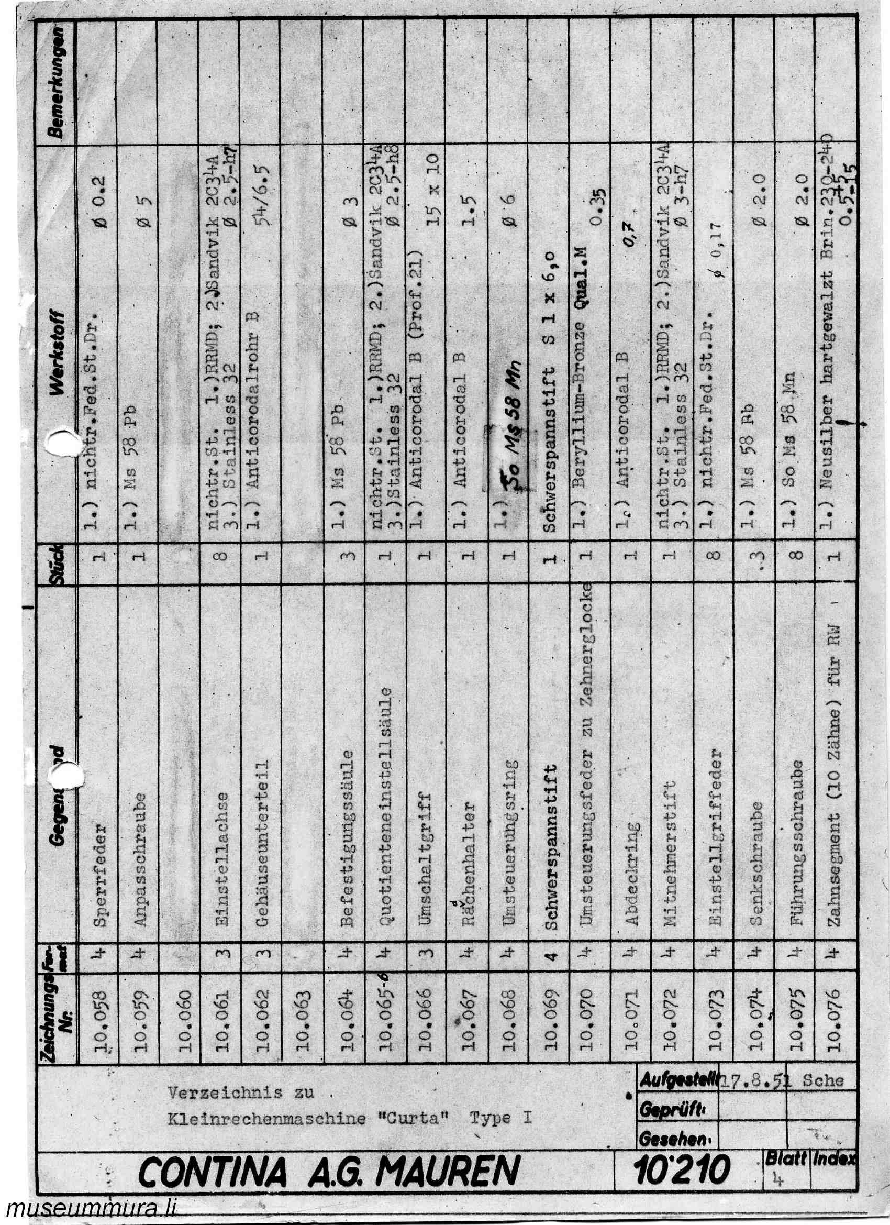
app/curta_jpegs/assembly/Curta_1_10210_4.jpg
