daeken/ReCurta/app/curta_jpegs/assembly/Curta_1_10210_5.jpg

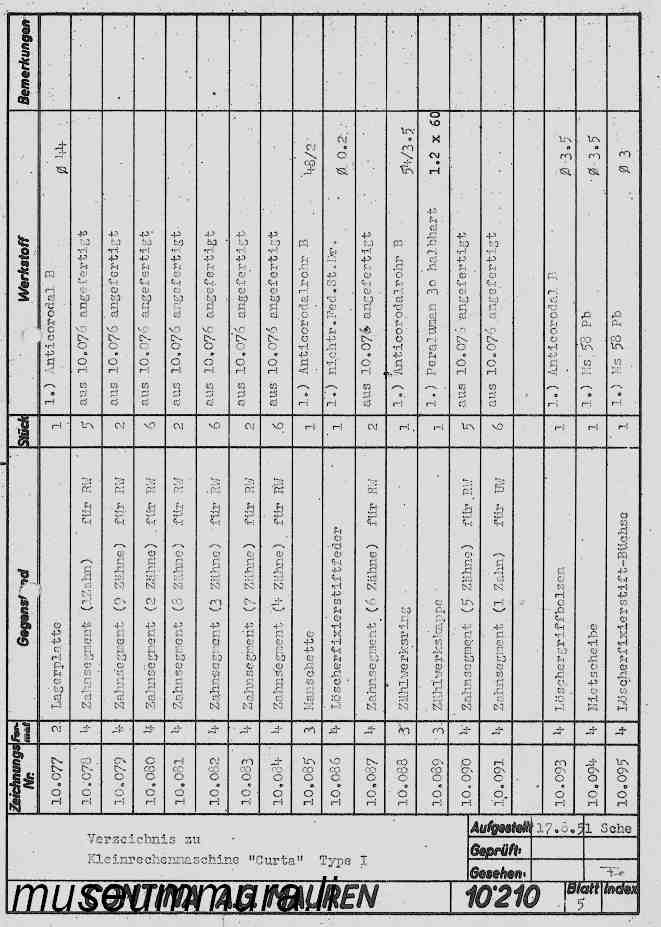
app/curta_jpegs/assembly/Curta_1_10210_5.jpg
