daeken/ReCurta/app/curta_jpegs/assembly/Curta_1_10210_6.jpg

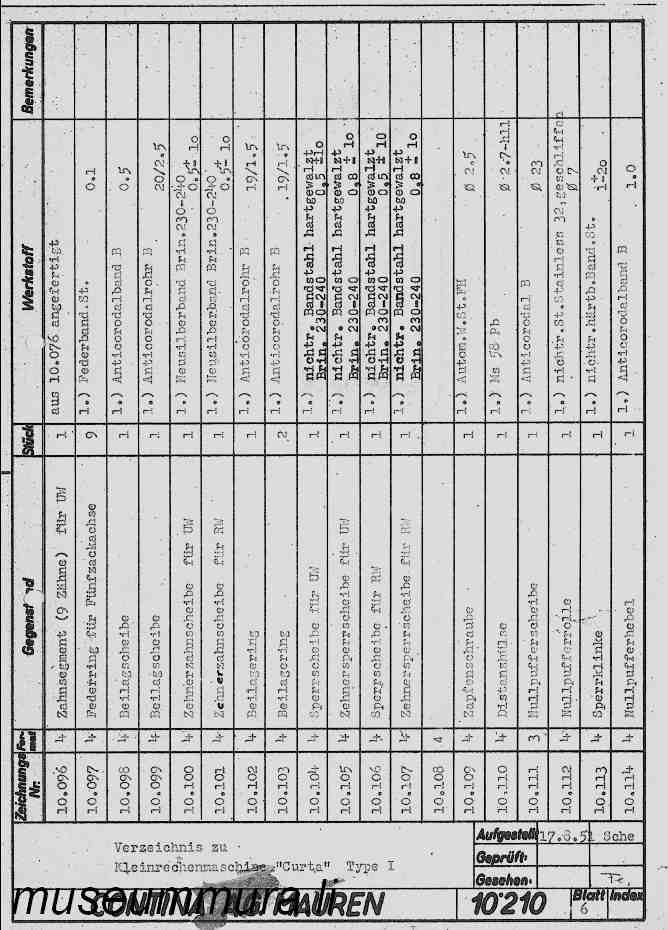
app/curta_jpegs/assembly/Curta_1_10210_6.jpg
