daeken/ReCurta/app/curta_jpegs/assembly/Curta_1_10210_8.jpg

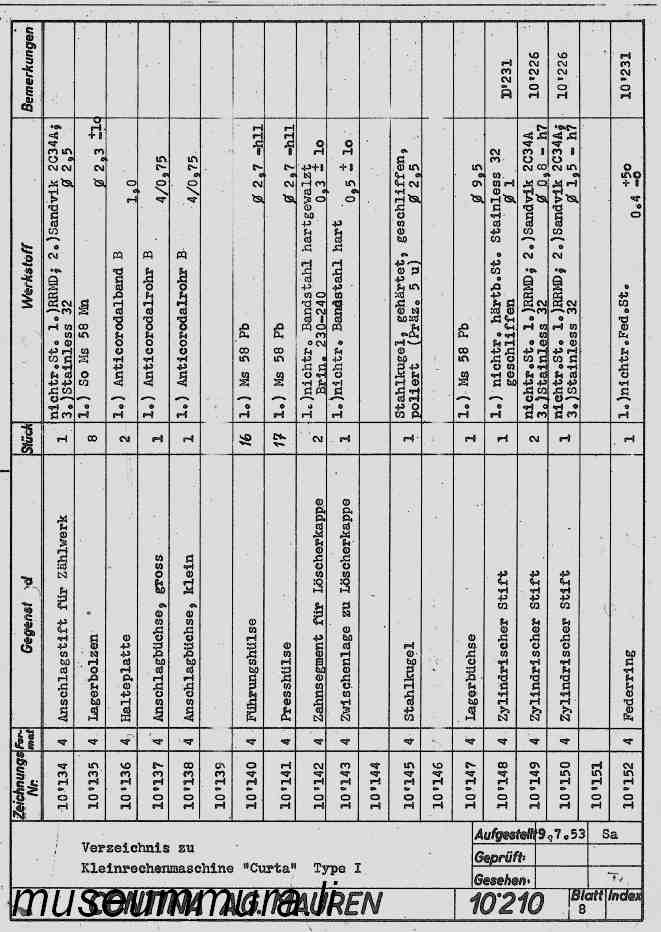
app/curta_jpegs/assembly/Curta_1_10210_8.jpg
