daeken/ReCurta/app/curta_jpegs/assembly/Curta_1_10210_11.jpg

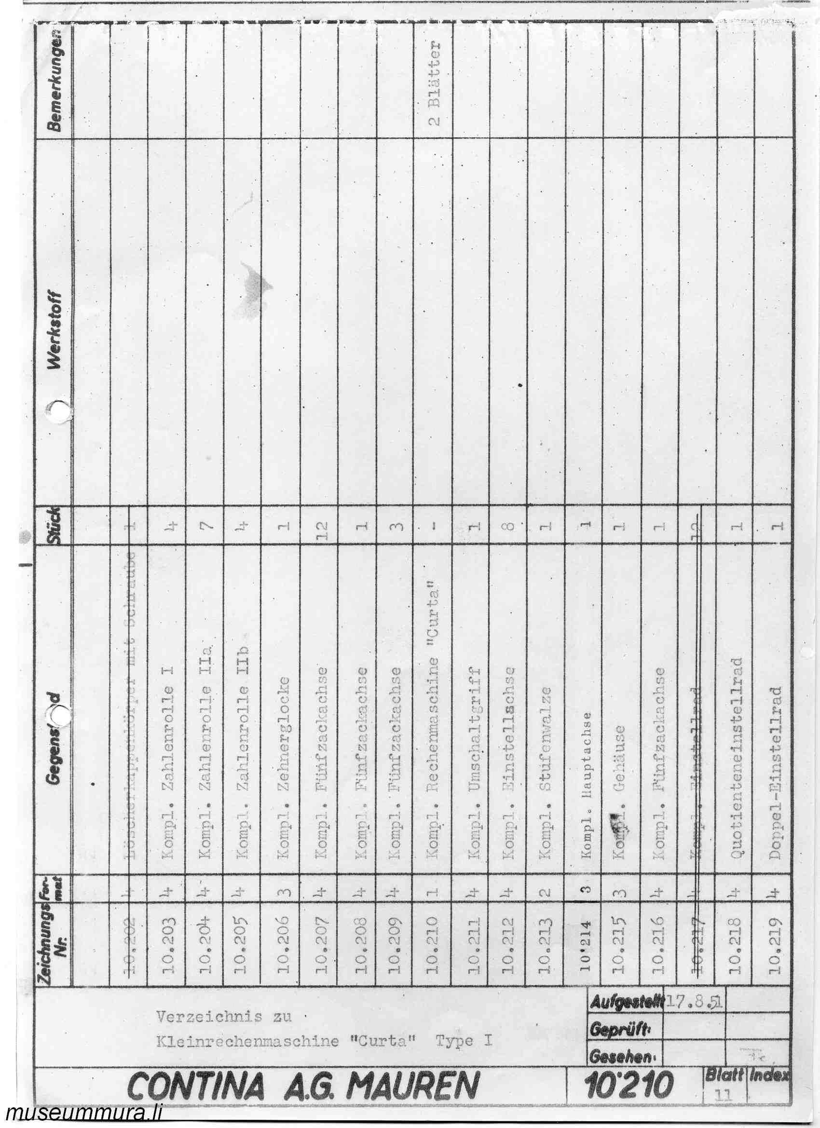
app/curta_jpegs/assembly/Curta_1_10210_11.jpg
