daeken/ReCurta/app/curta_jpegs/assembly/Curta_1_10210_13.jpg

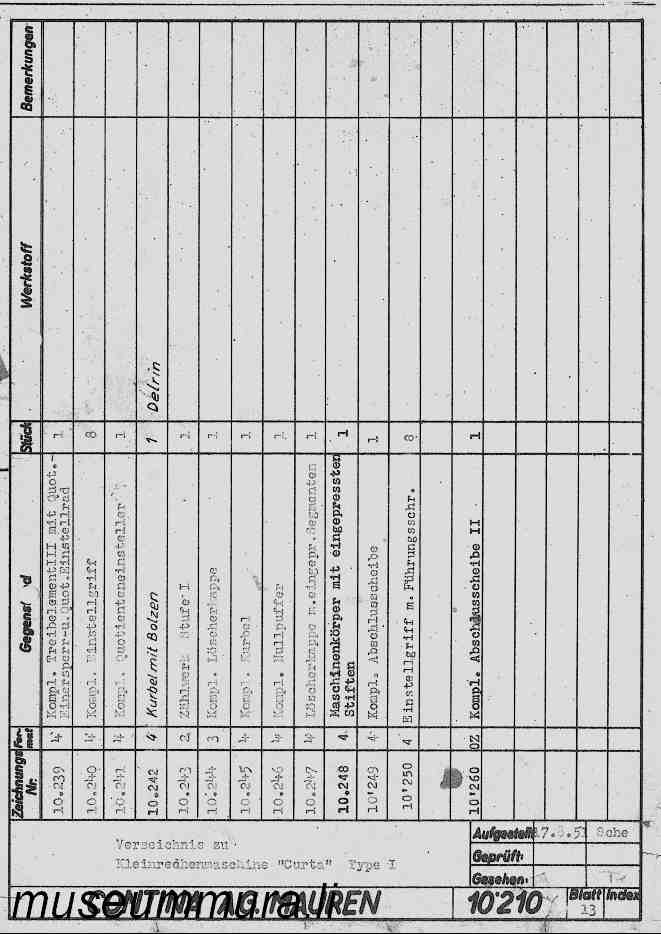
app/curta_jpegs/assembly/Curta_1_10210_13.jpg
