daeken/ReCurta/app/curta_jpegs/assembly/Curta_1_10211.jpg

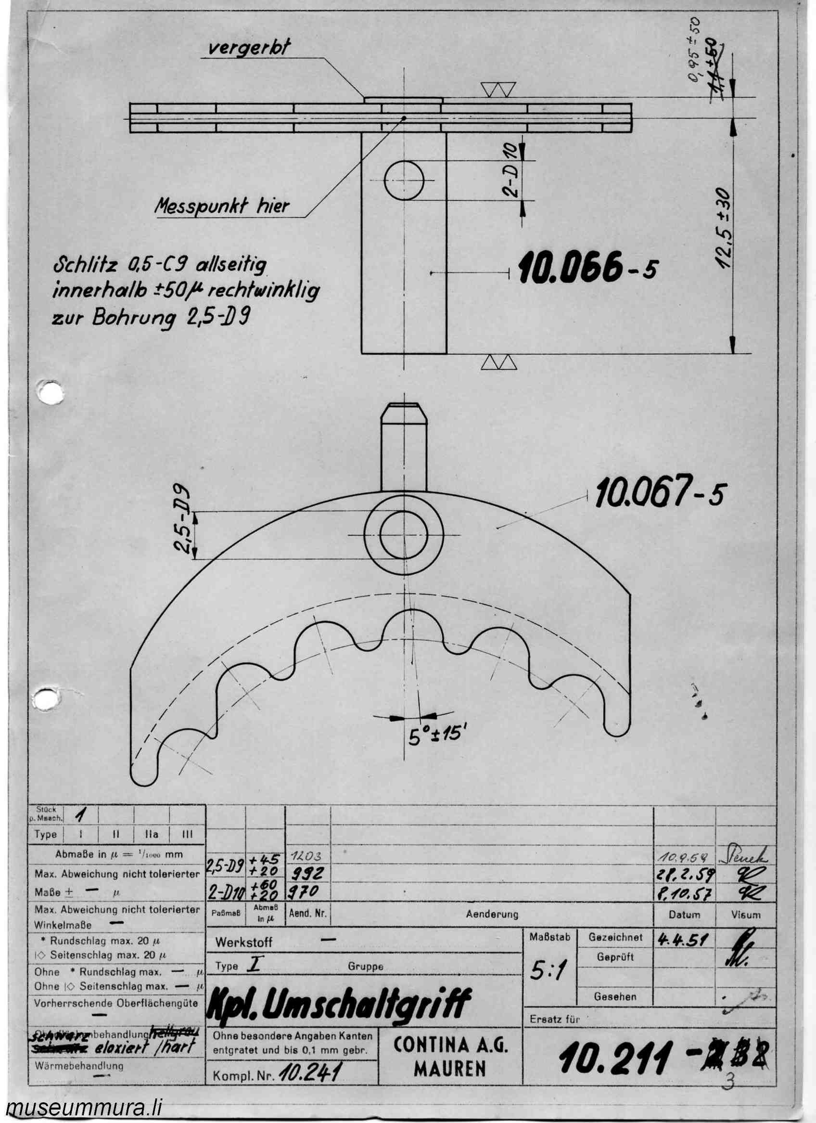
app/curta_jpegs/assembly/Curta_1_10211.jpg
