daeken/ReCurta/app/curta_jpegs/assembly/Curta_1_10213.jpg

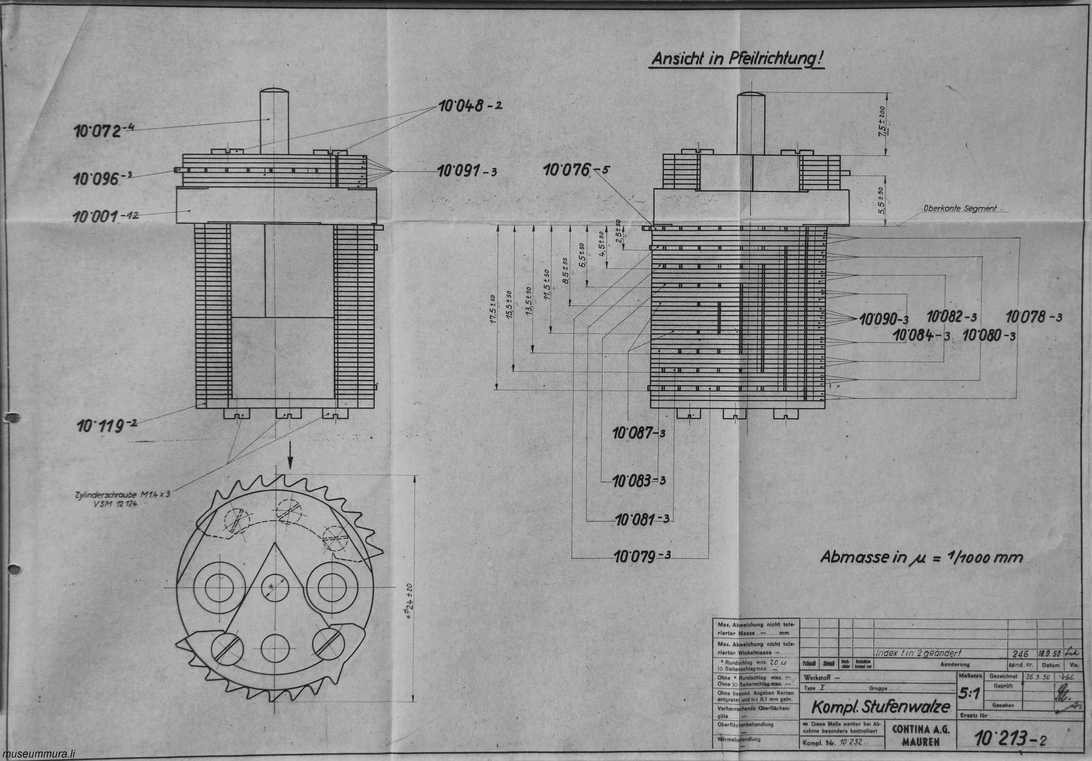
app/curta_jpegs/assembly/Curta_1_10213.jpg
