daeken/ReCurta/app/curta_jpegs/assembly/Curta_1_10214.jpg

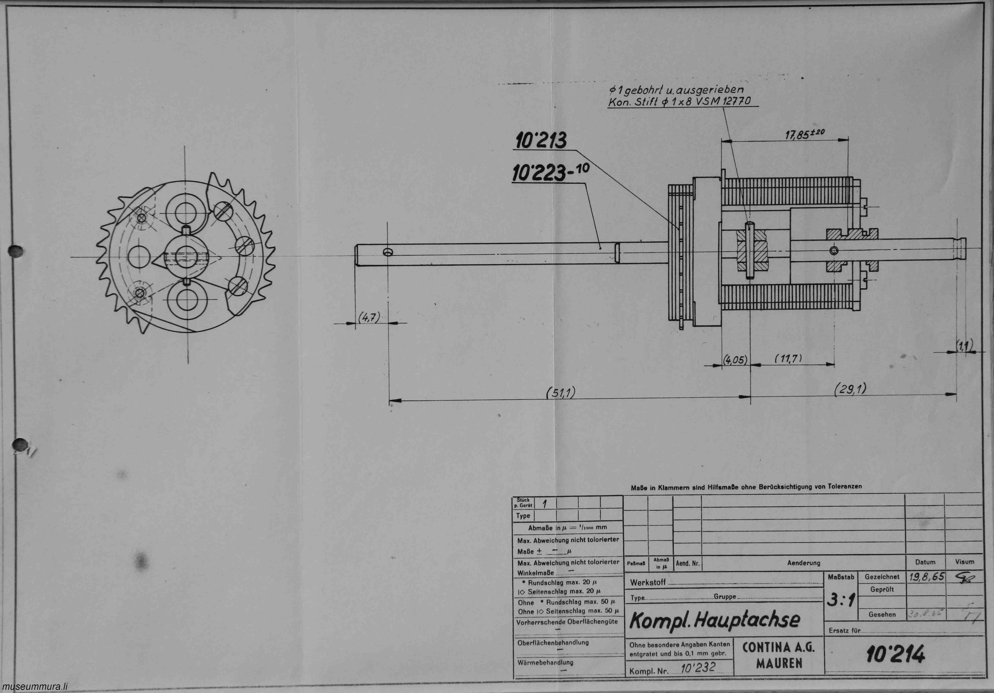
app/curta_jpegs/assembly/Curta_1_10214.jpg
