daeken/ReCurta/app/curta_jpegs/assembly/Curta_1_10215.jpg

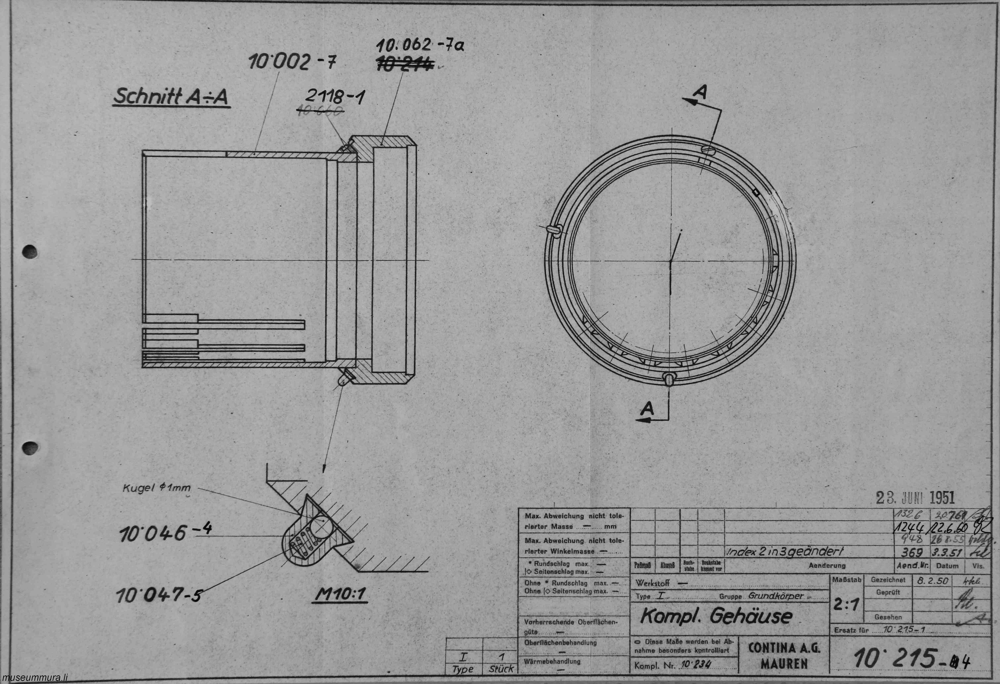
app/curta_jpegs/assembly/Curta_1_10215.jpg
