daeken/ReCurta/app/curta_jpegs/assembly/Curta_1_10218.jpg

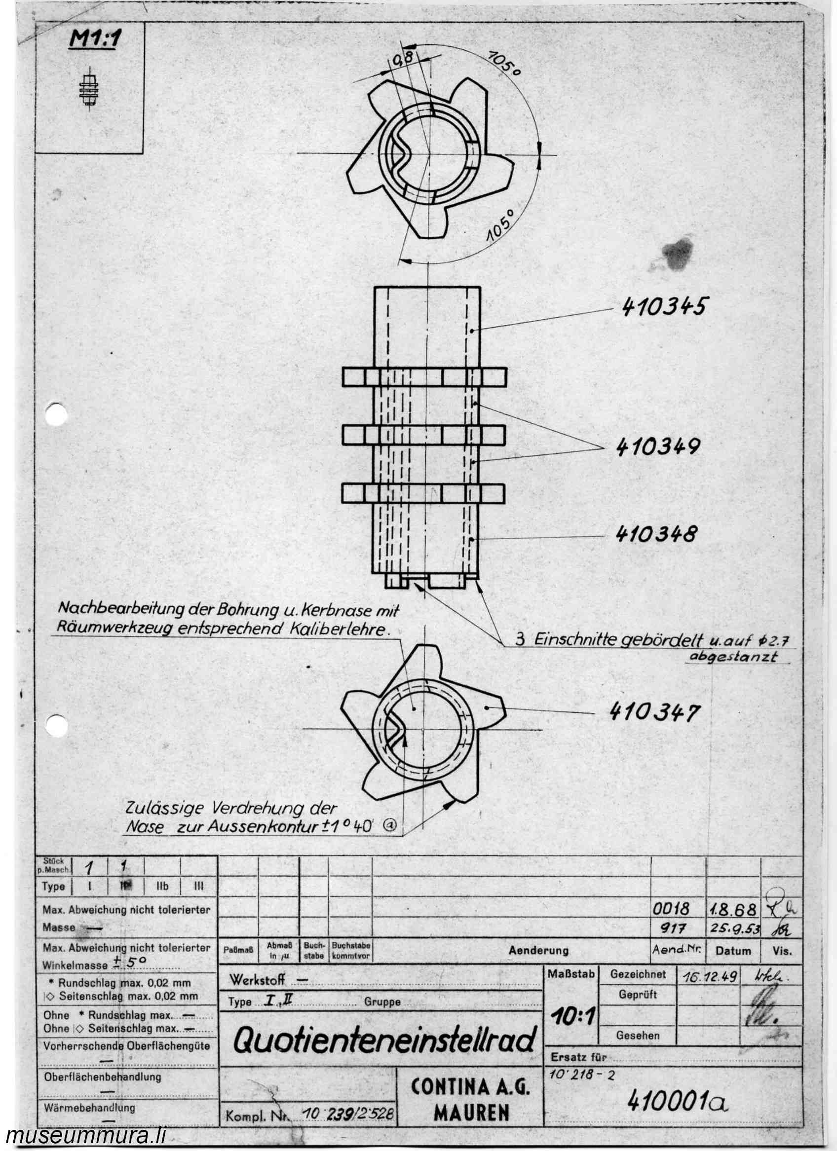
app/curta_jpegs/assembly/Curta_1_10218.jpg
