daeken/ReCurta/app/curta_jpegs/assembly/Curta_1_10219.jpg

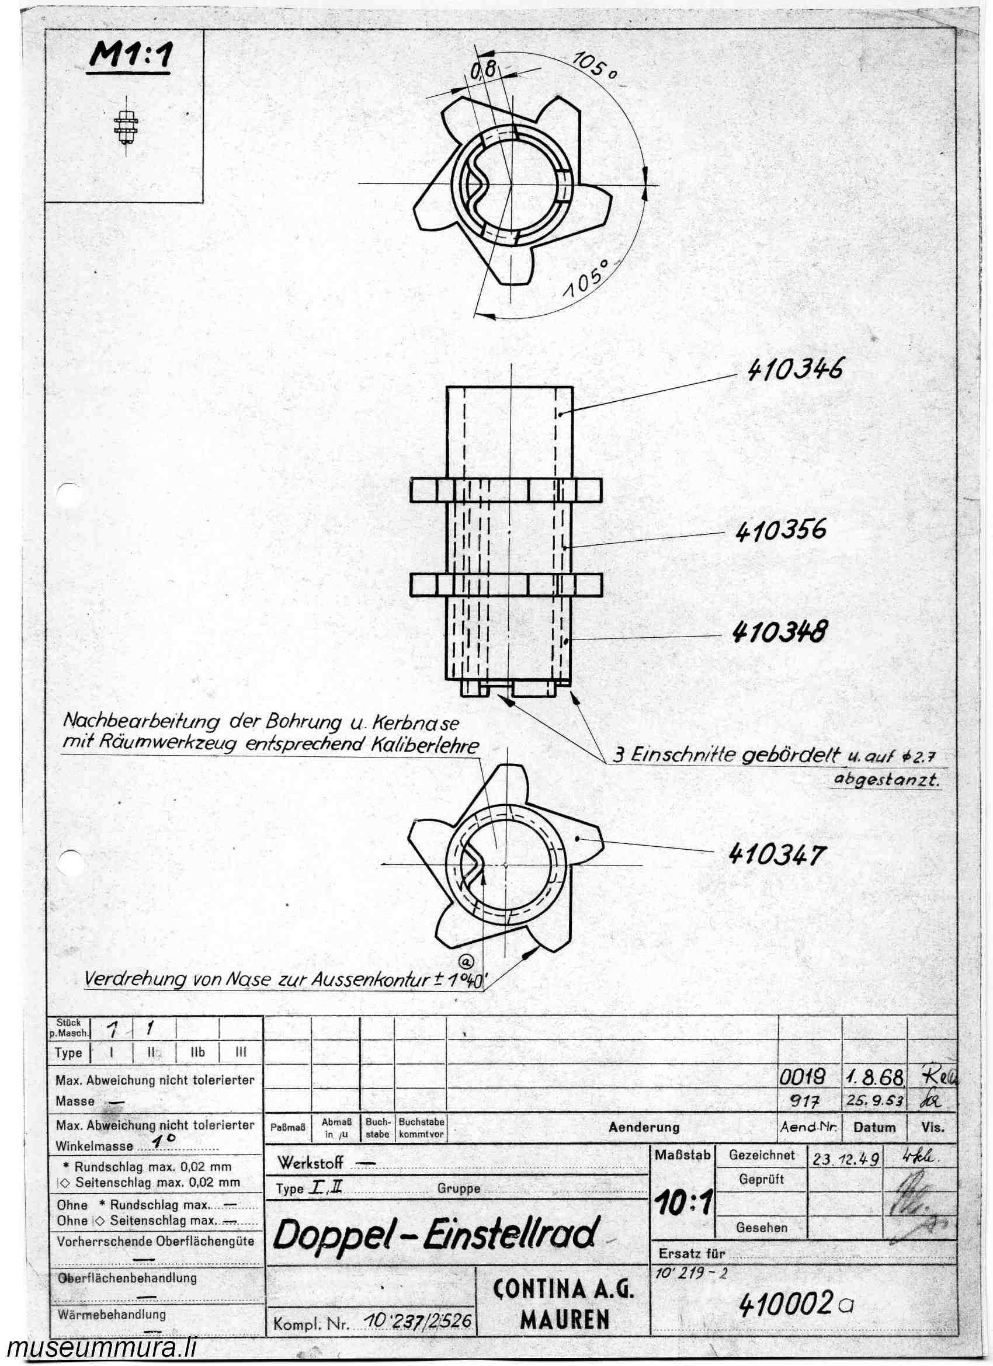
app/curta_jpegs/assembly/Curta_1_10219.jpg
