daeken/ReCurta/app/curta_jpegs/assembly/Curta_1_10220.jpg

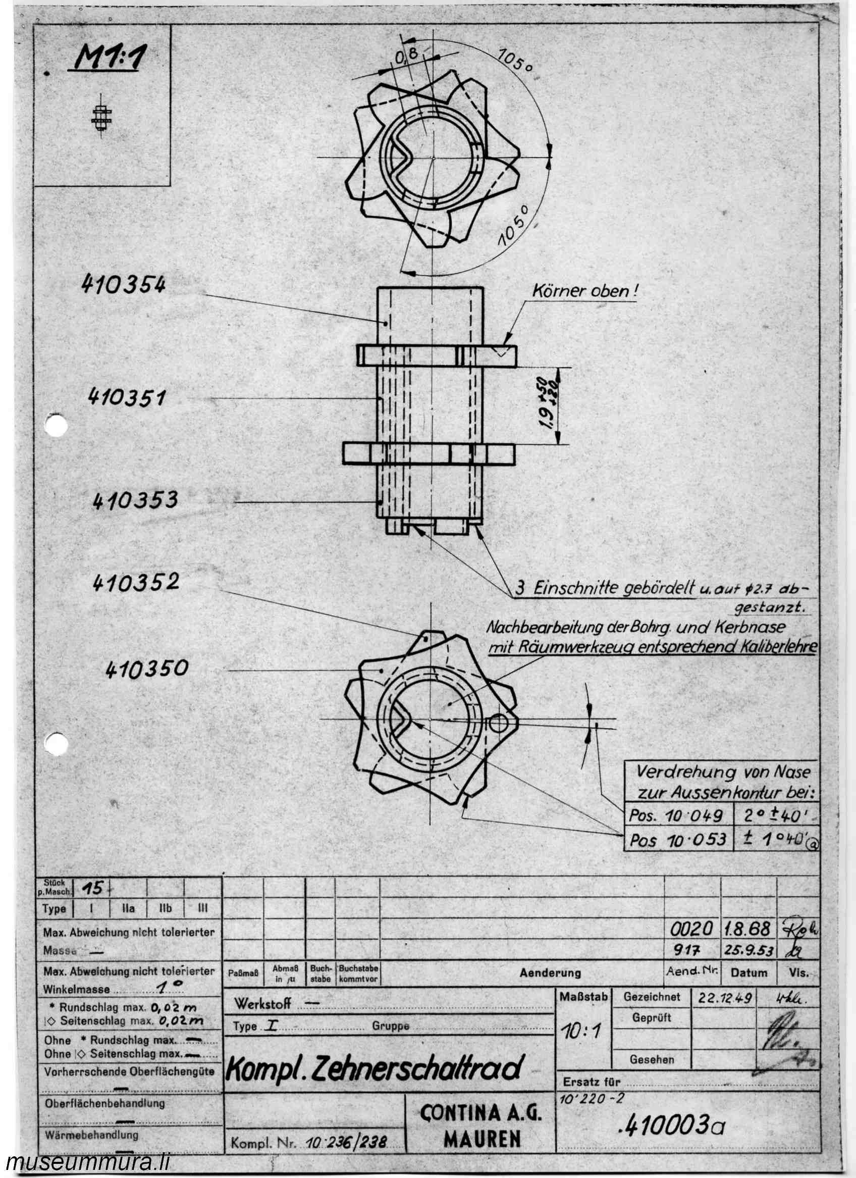
app/curta_jpegs/assembly/Curta_1_10220.jpg
