daeken/ReCurta/app/curta_jpegs/assembly/Curta_1_10221.jpg

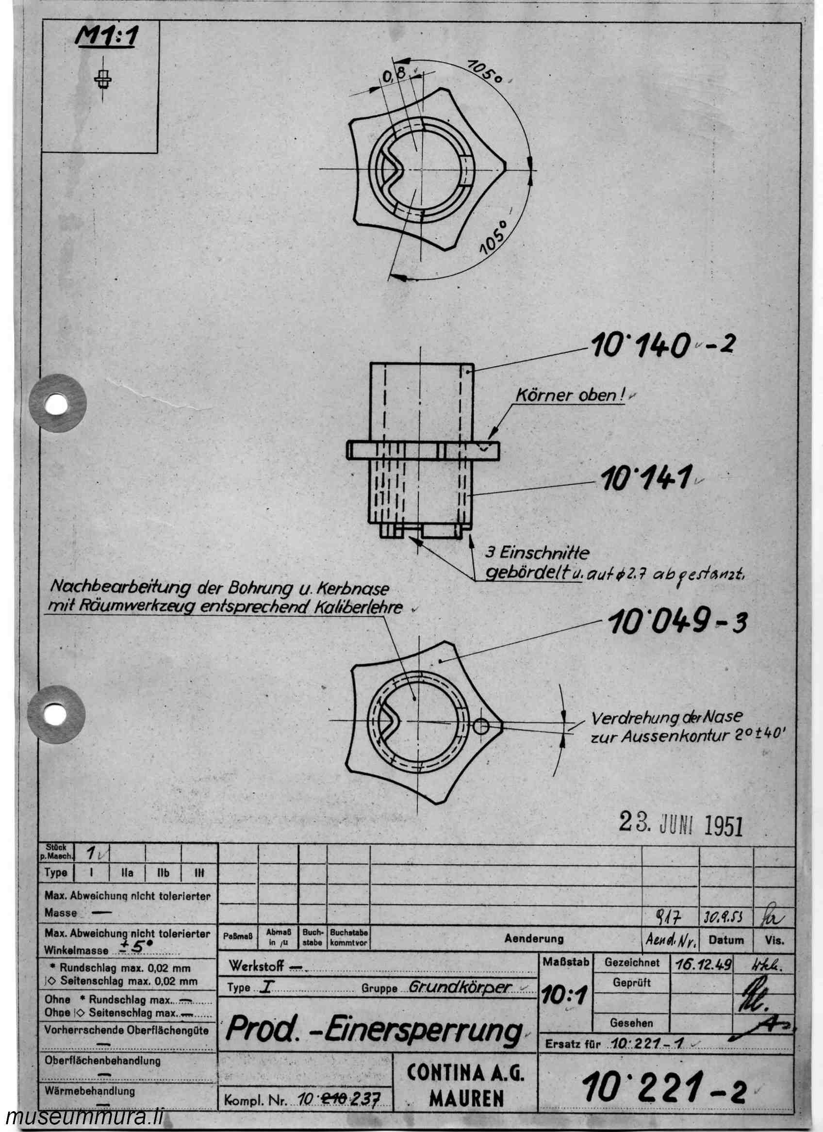
app/curta_jpegs/assembly/Curta_1_10221.jpg
