daeken/ReCurta/app/curta_jpegs/assembly/Curta_1_10223.jpg

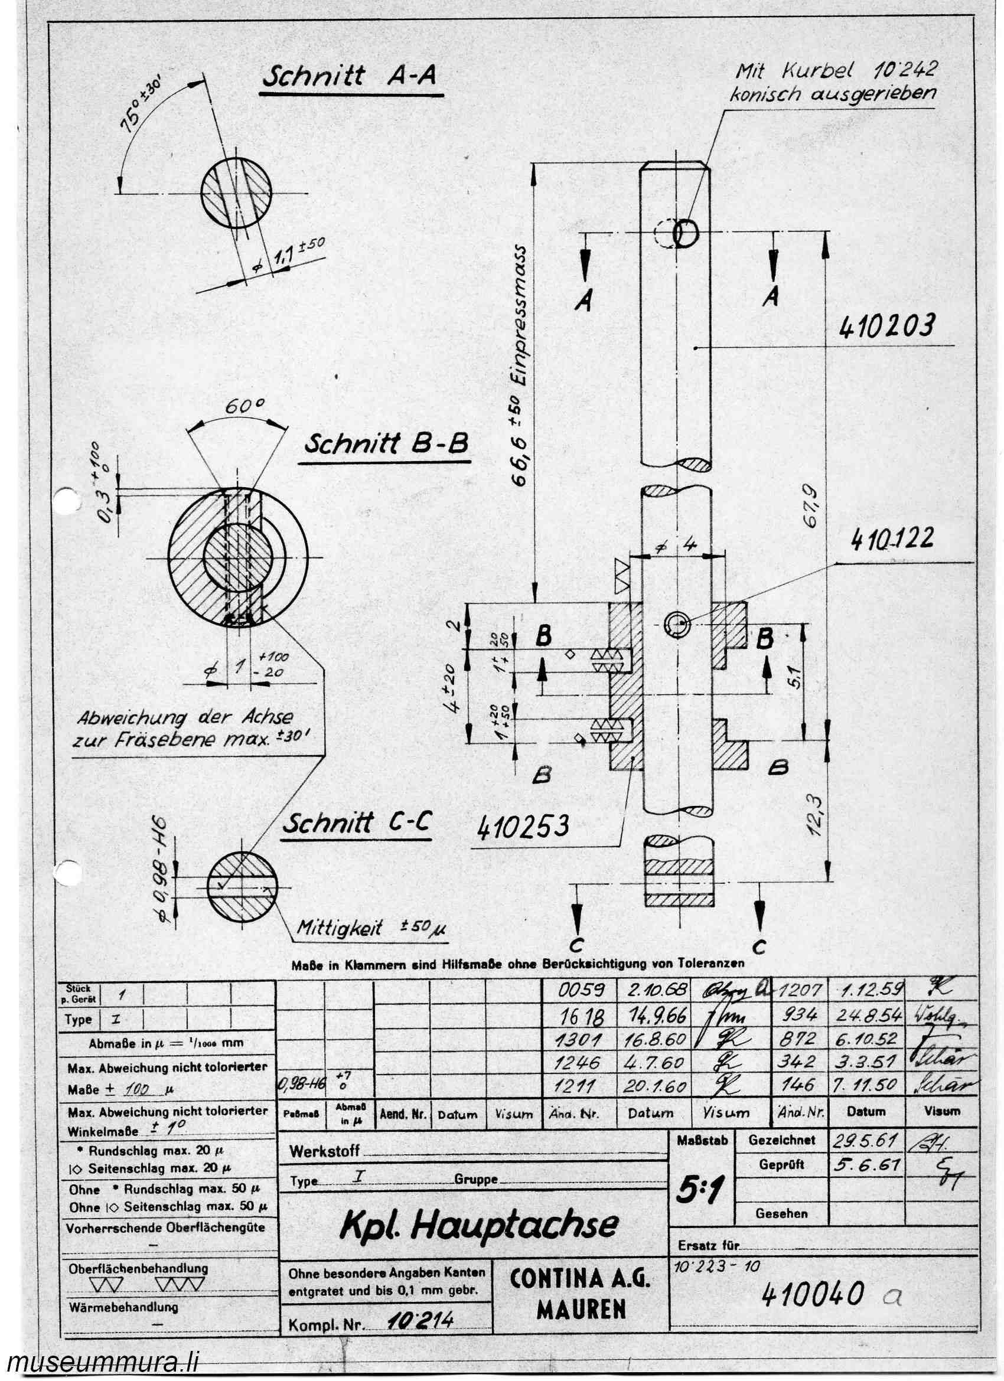
app/curta_jpegs/assembly/Curta_1_10223.jpg
