daeken/ReCurta/app/curta_jpegs/assembly/Curta_1_10224.jpg

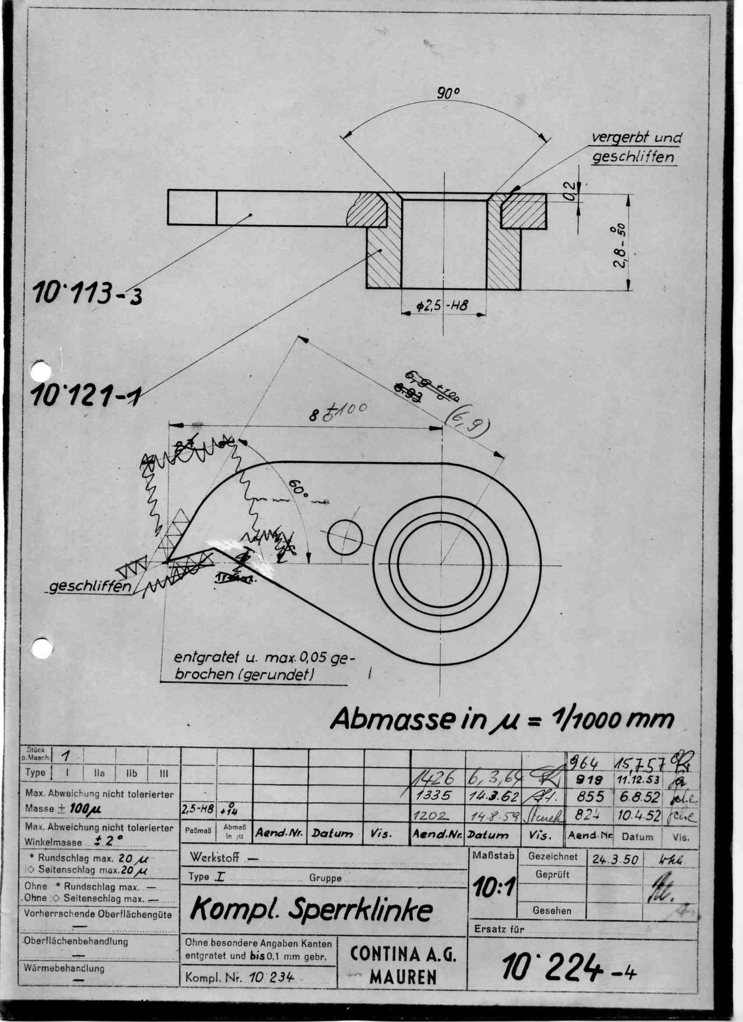
app/curta_jpegs/assembly/Curta_1_10224.jpg
