daeken/ReCurta/app/curta_jpegs/assembly/Curta_1_10225.jpg

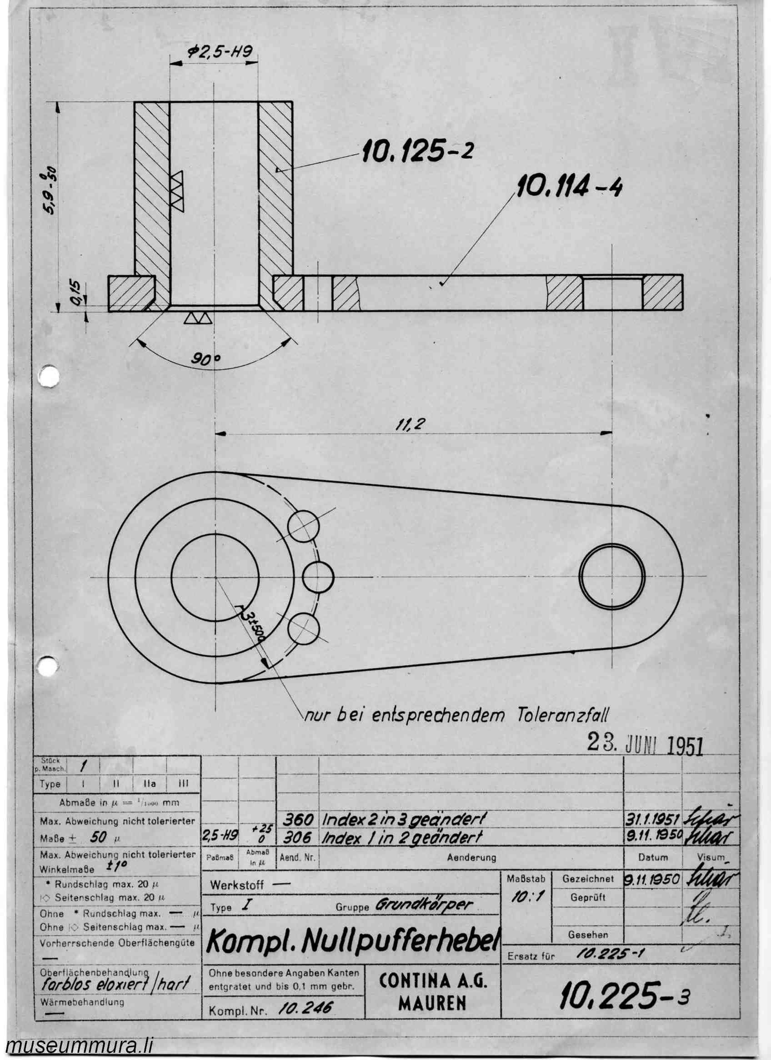
app/curta_jpegs/assembly/Curta_1_10225.jpg
