daeken/ReCurta/app/curta_jpegs/assembly/Curta_1_10226.jpg

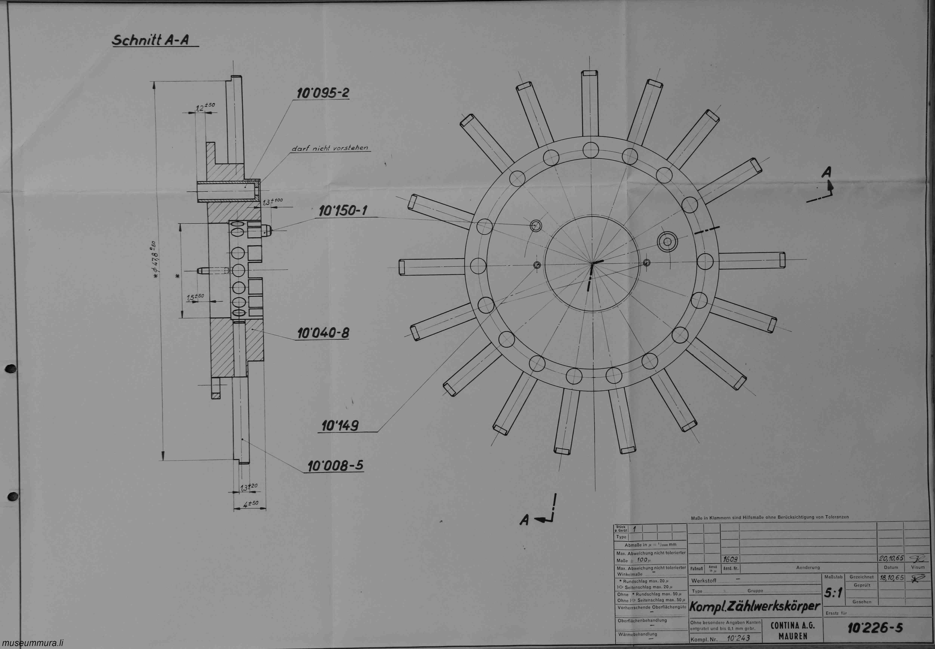
app/curta_jpegs/assembly/Curta_1_10226.jpg
