daeken/ReCurta/app/curta_jpegs/assembly/Curta_1_10228.jpg

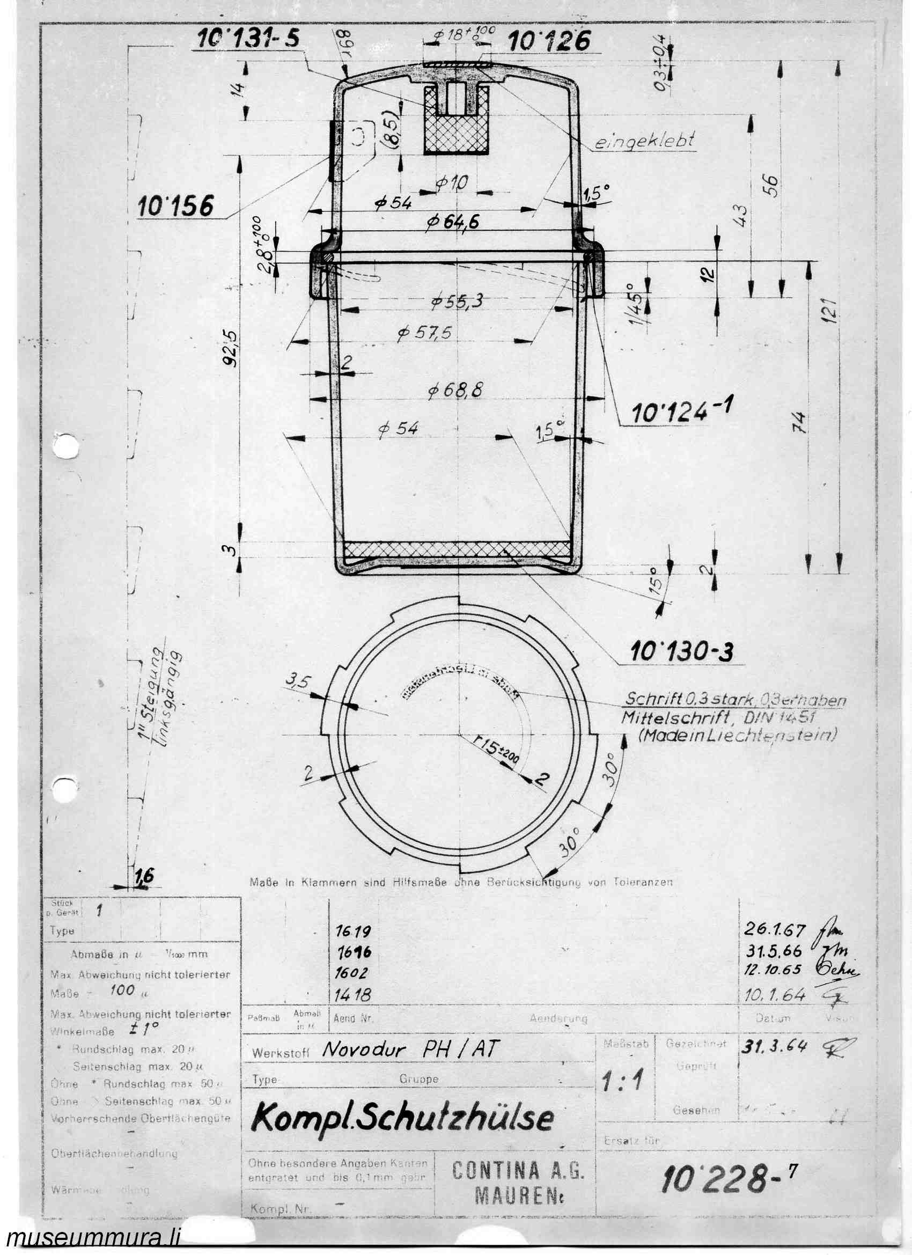
app/curta_jpegs/assembly/Curta_1_10228.jpg
