daeken/ReCurta/app/curta_jpegs/assembly/Curta_1_10229.jpg

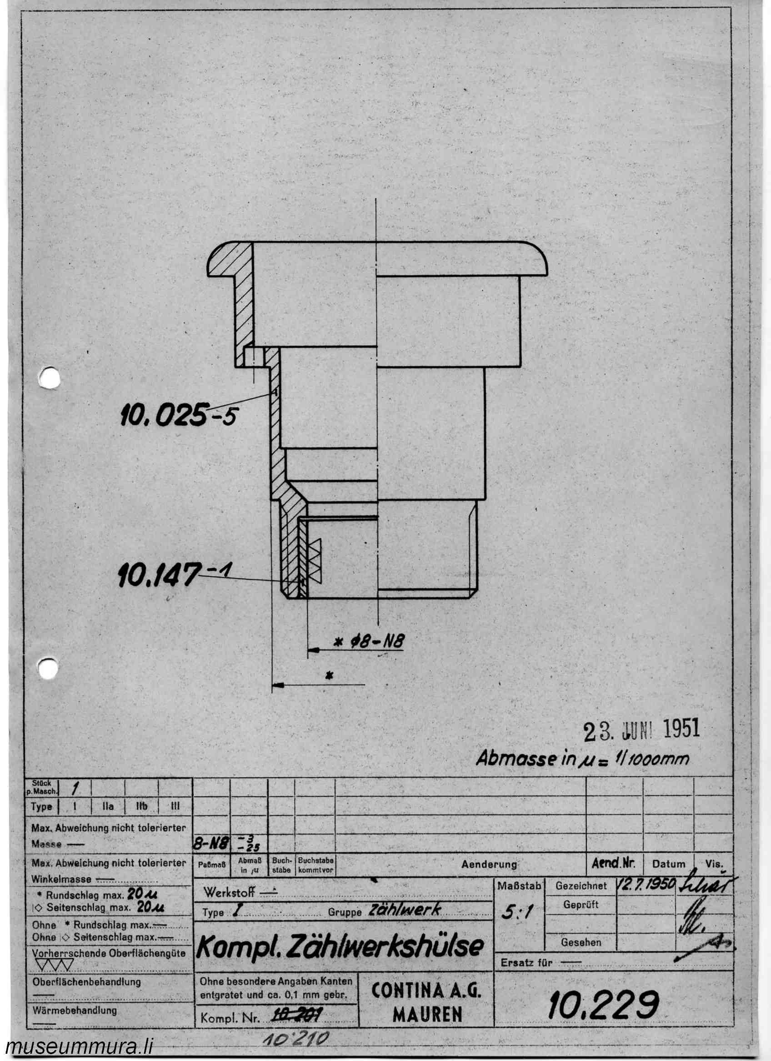
app/curta_jpegs/assembly/Curta_1_10229.jpg
