daeken/ReCurta/app/curta_jpegs/assembly/Curta_1_10230.jpg

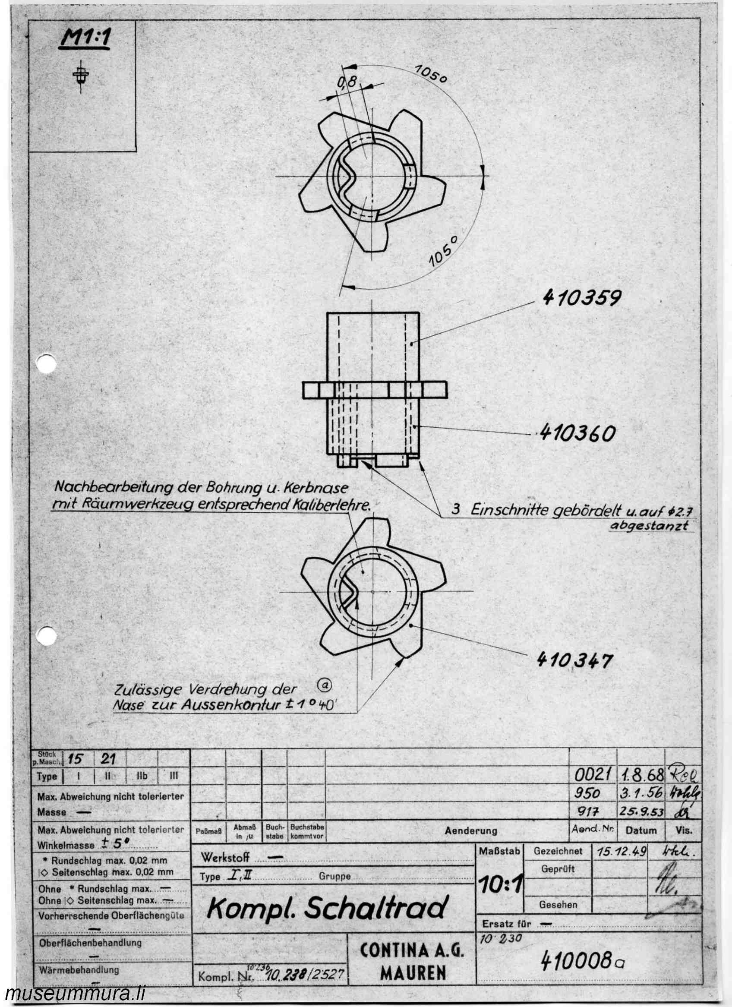
app/curta_jpegs/assembly/Curta_1_10230.jpg
