daeken/ReCurta/app/curta_jpegs/assembly/Curta_1_10231.jpg

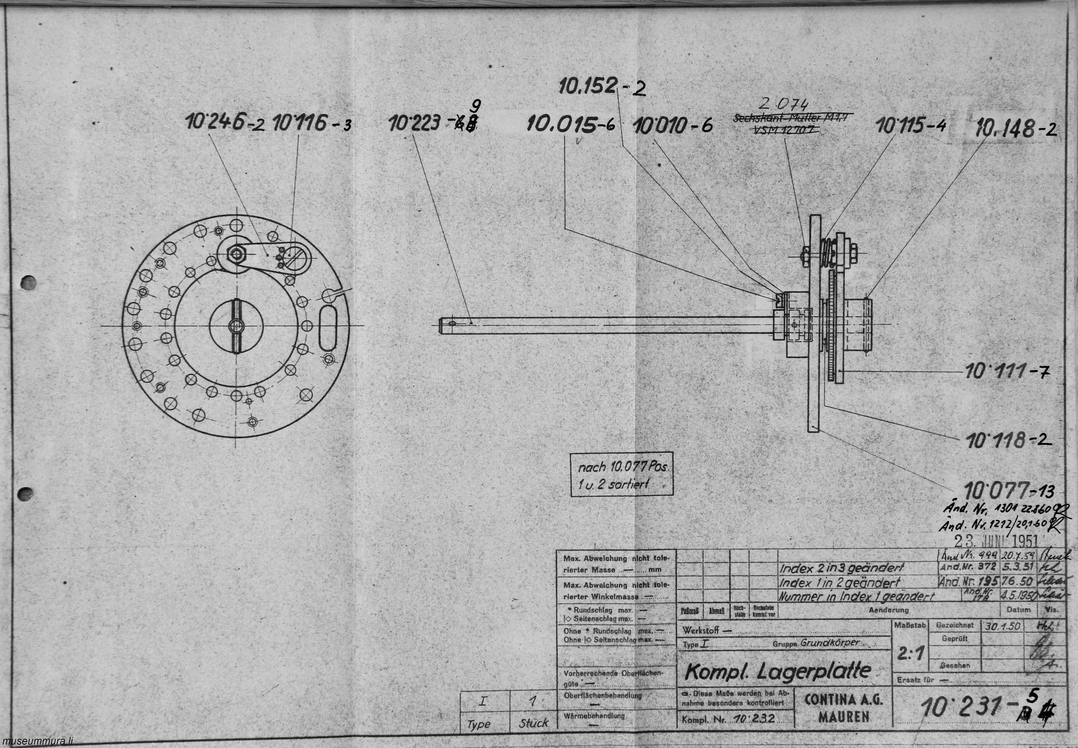
app/curta_jpegs/assembly/Curta_1_10231.jpg
