daeken/ReCurta/app/curta_jpegs/assembly/Curta_1_10232.jpg

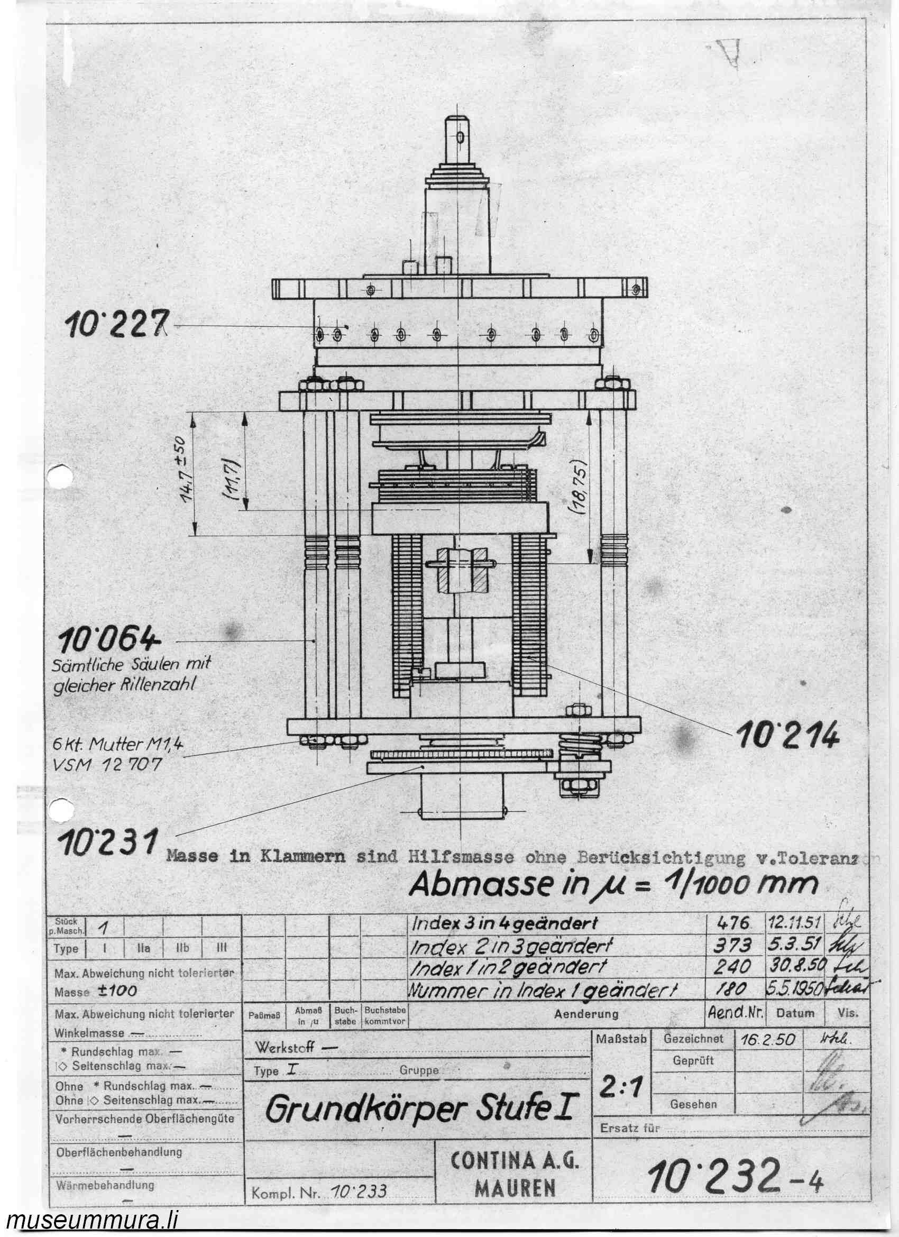
app/curta_jpegs/assembly/Curta_1_10232.jpg
