daeken/ReCurta/app/curta_jpegs/assembly/Curta_1_10233.jpg

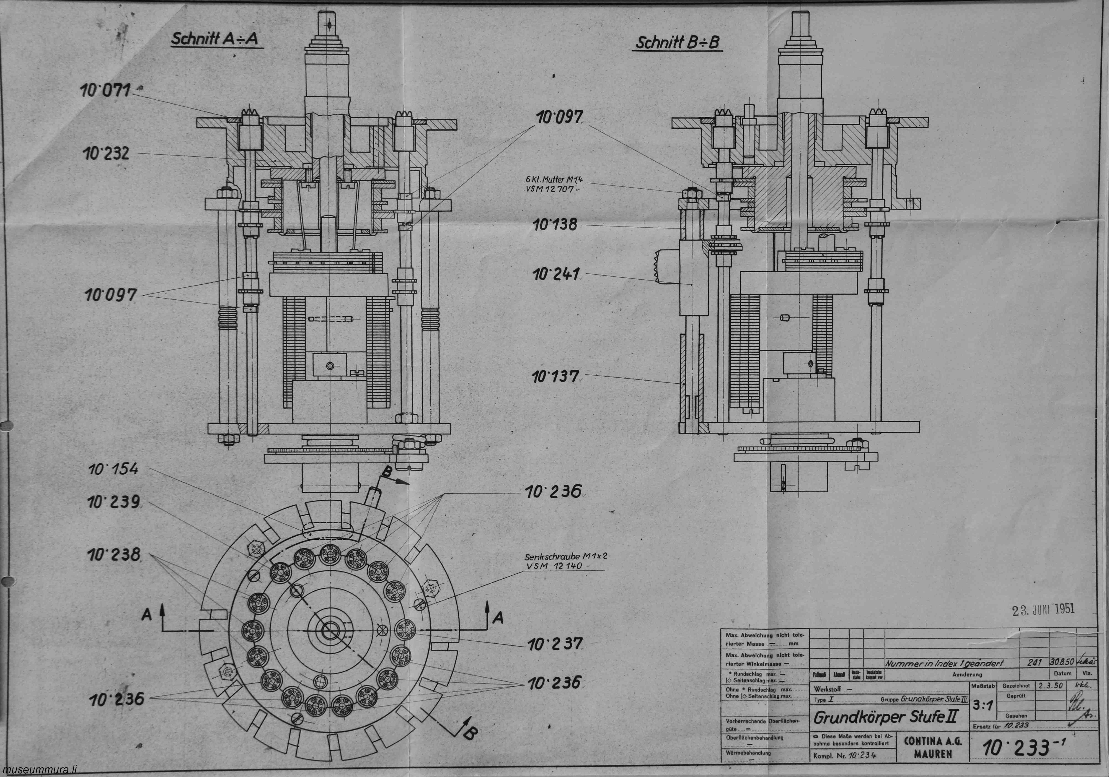
app/curta_jpegs/assembly/Curta_1_10233.jpg
