daeken/ReCurta/app/curta_jpegs/assembly/Curta_1_10234.jpg

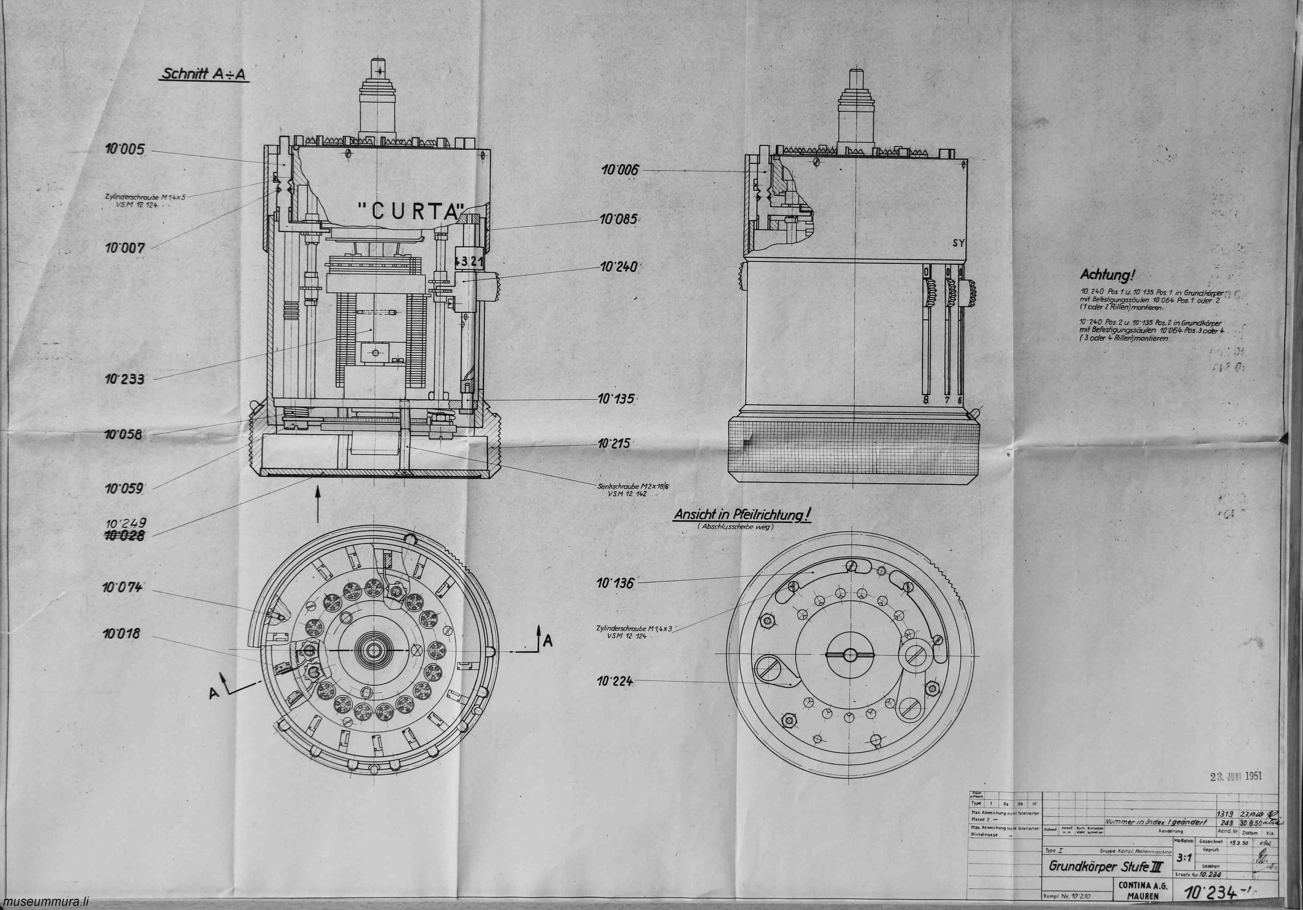
app/curta_jpegs/assembly/Curta_1_10234.jpg
