daeken/ReCurta/app/curta_jpegs/assembly/Curta_1_10236.jpg

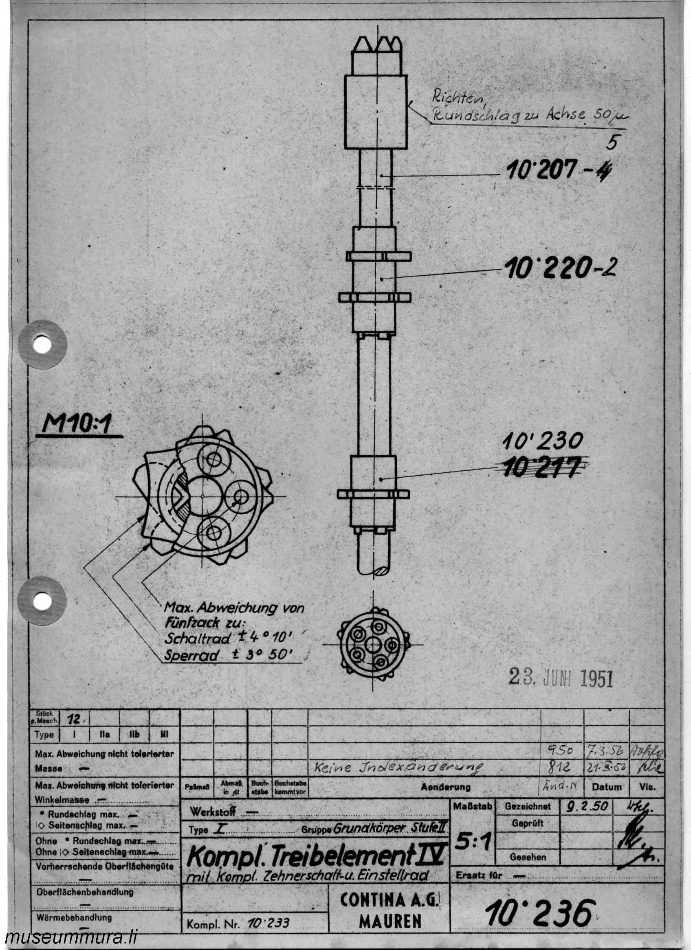
app/curta_jpegs/assembly/Curta_1_10236.jpg
