daeken/ReCurta/app/curta_jpegs/assembly/Curta_1_10237.jpg

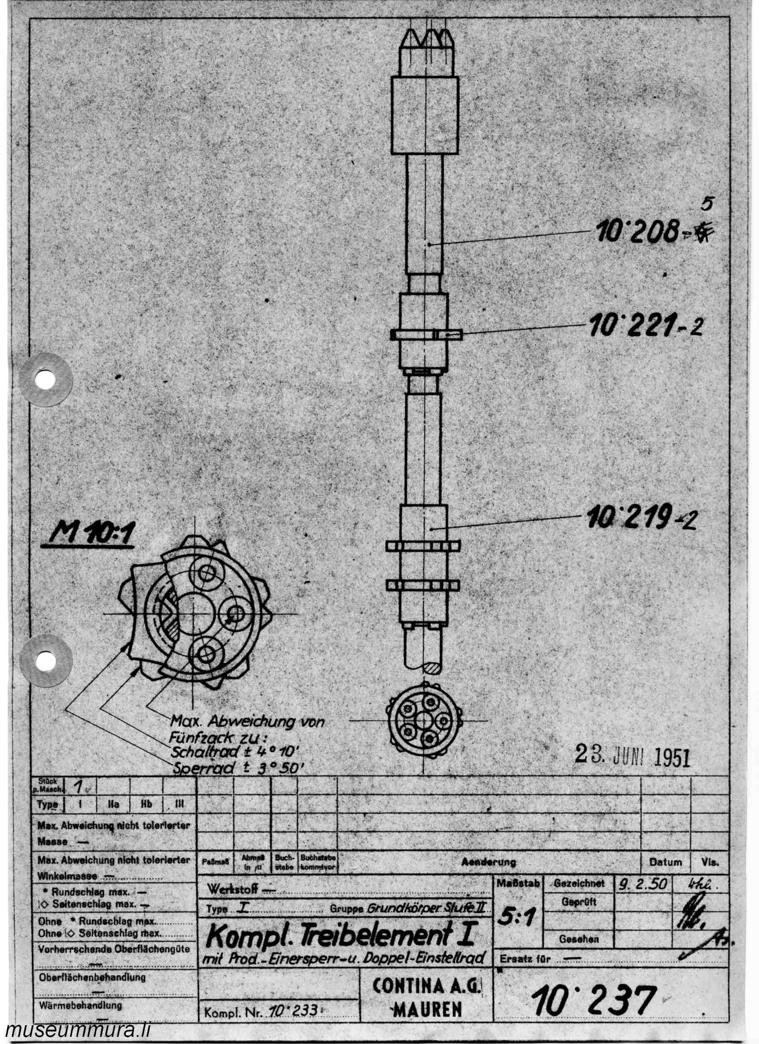
app/curta_jpegs/assembly/Curta_1_10237.jpg
