daeken/ReCurta/app/curta_jpegs/assembly/Curta_1_10238.jpg

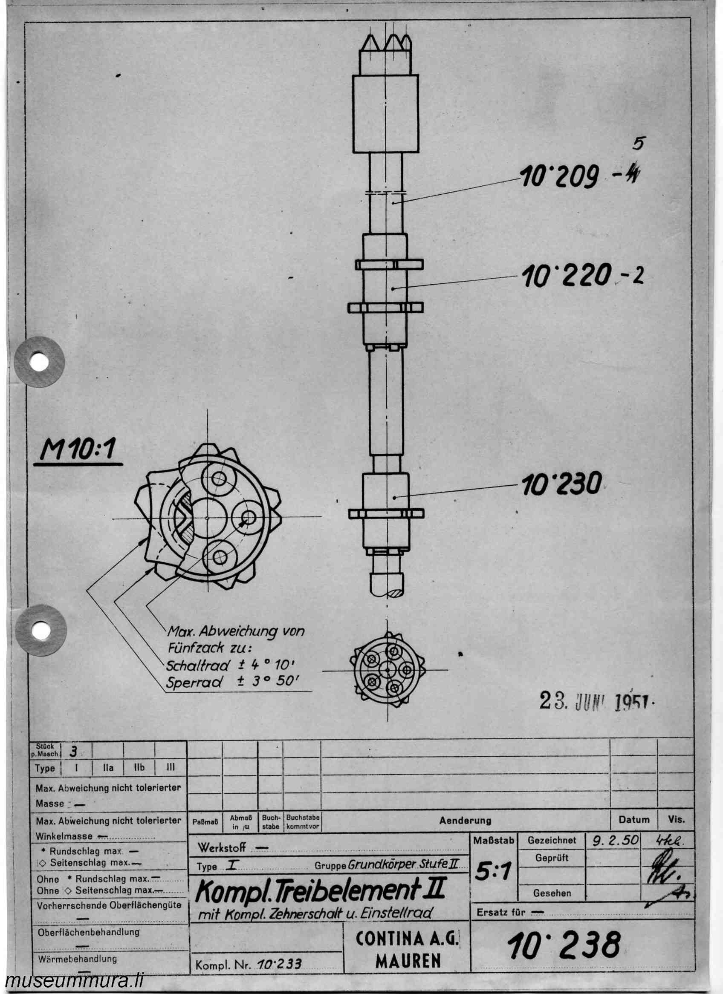
app/curta_jpegs/assembly/Curta_1_10238.jpg
