daeken/ReCurta/app/curta_jpegs/assembly/Curta_1_10239.jpg

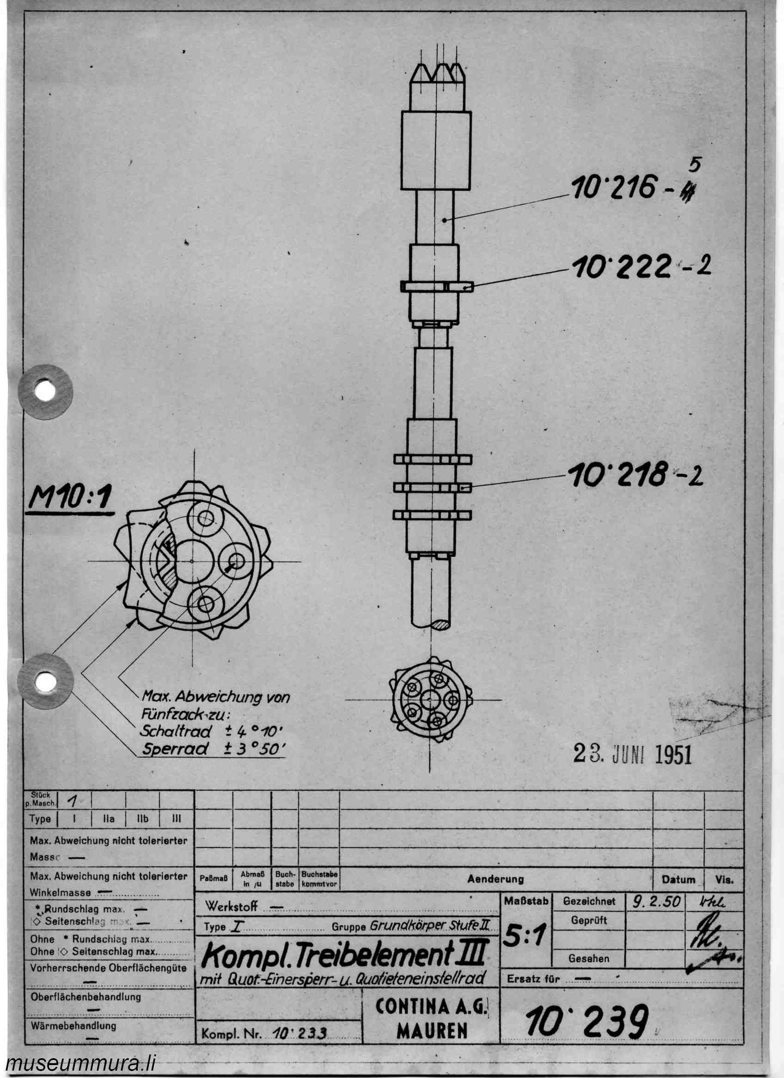
app/curta_jpegs/assembly/Curta_1_10239.jpg
