daeken/ReCurta/app/curta_jpegs/assembly/Curta_1_10240.jpg

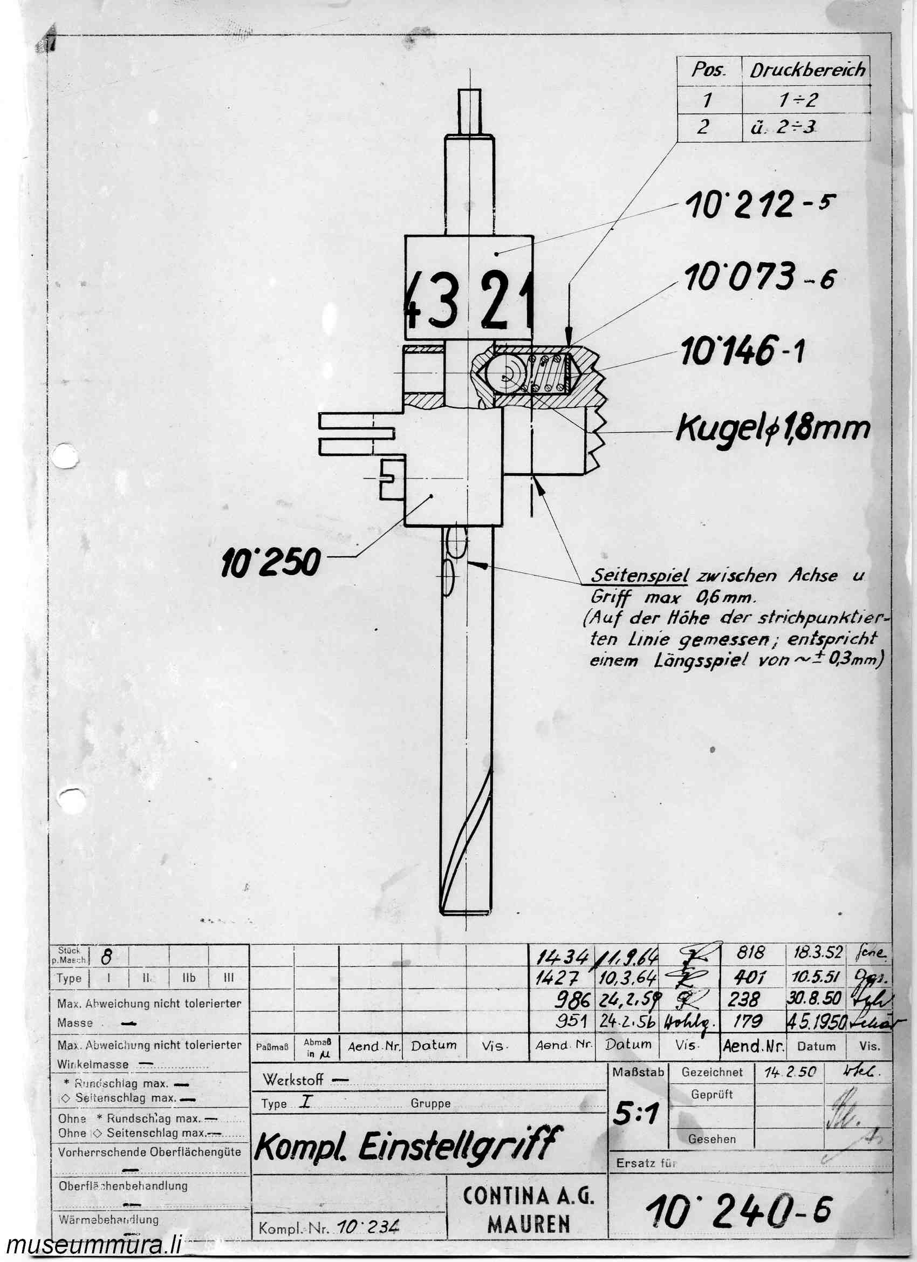
app/curta_jpegs/assembly/Curta_1_10240.jpg
