daeken/ReCurta/app/curta_jpegs/assembly/Curta_1_10241.jpg

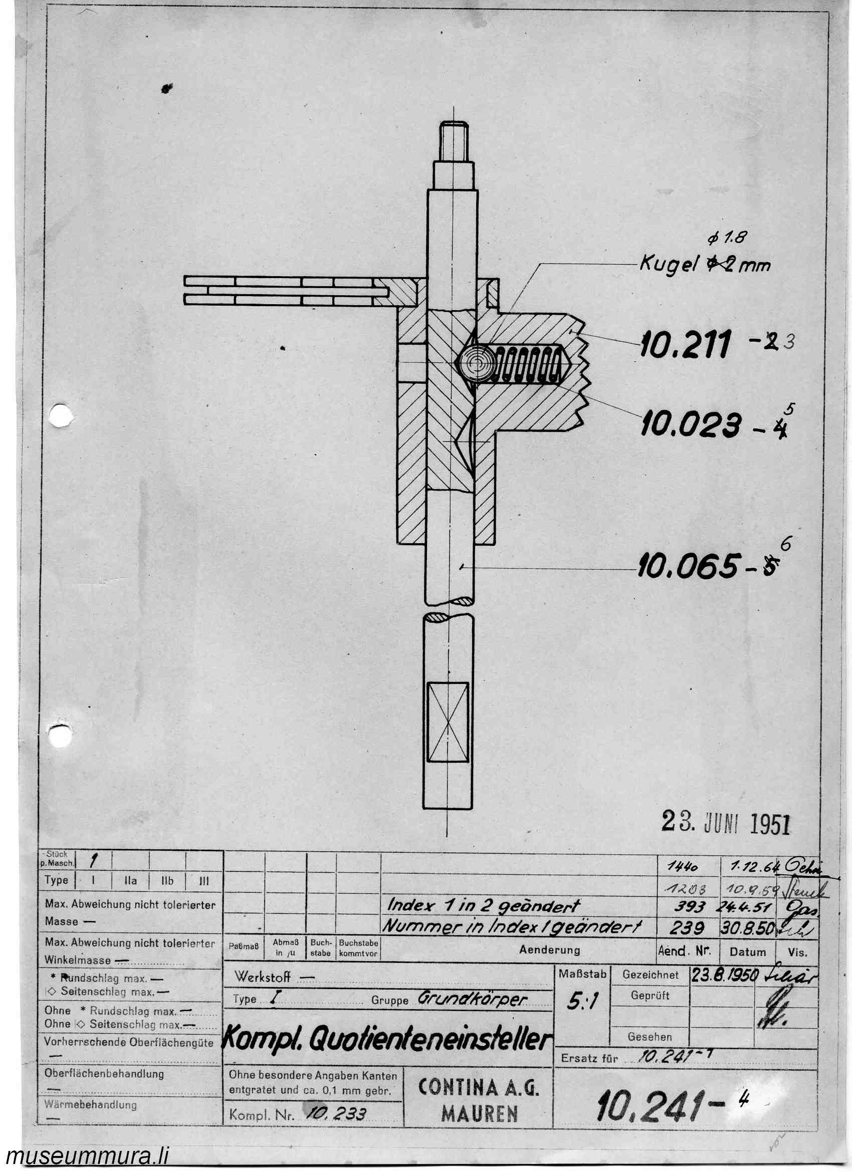
app/curta_jpegs/assembly/Curta_1_10241.jpg
