daeken/ReCurta/app/curta_jpegs/assembly/Curta_1_10242.jpg

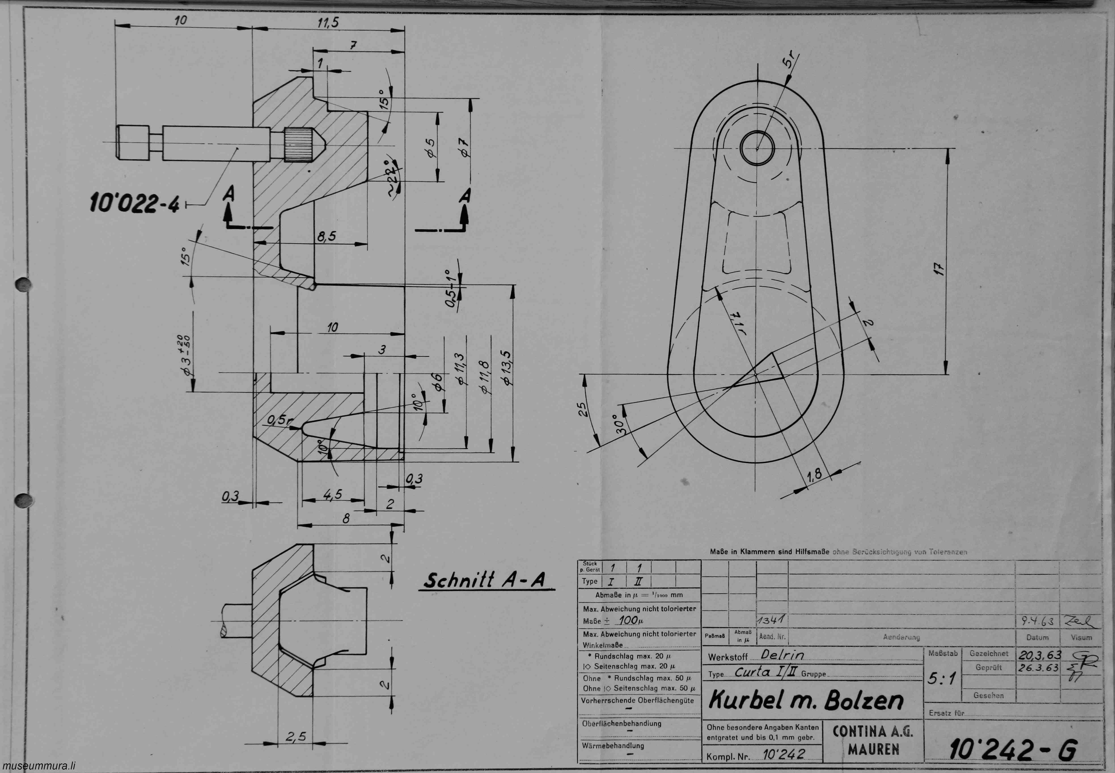
app/curta_jpegs/assembly/Curta_1_10242.jpg
