daeken/ReCurta/app/curta_jpegs/assembly/Curta_1_10242_410062.jpg

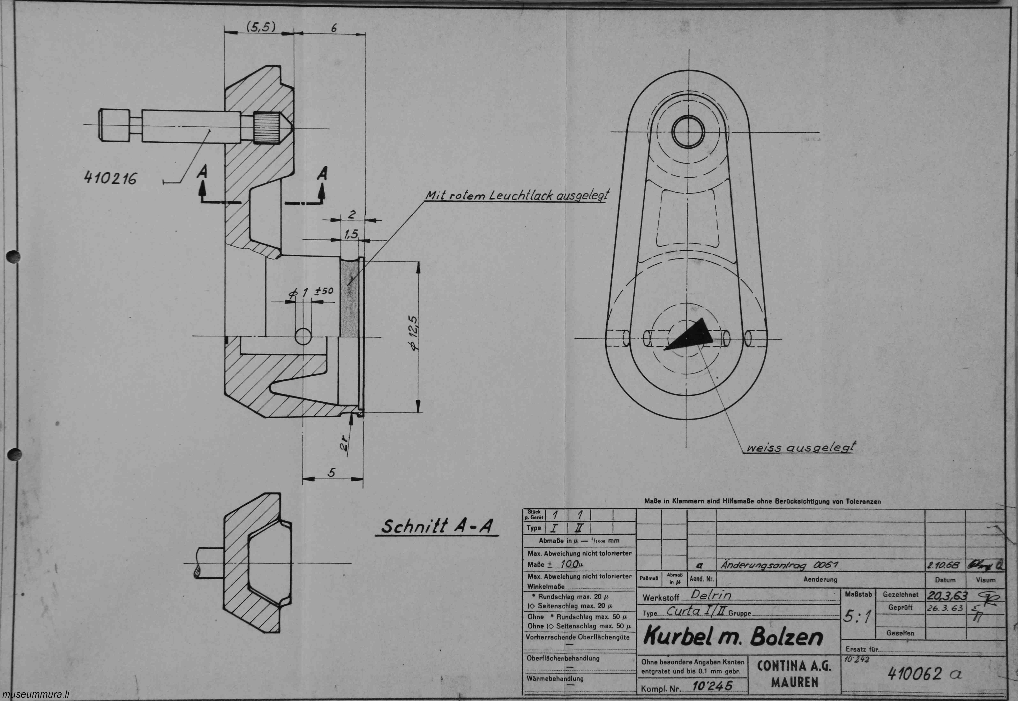
app/curta_jpegs/assembly/Curta_1_10242_410062.jpg
