daeken/ReCurta/app/curta_jpegs/assembly/Curta_1_10243.jpg

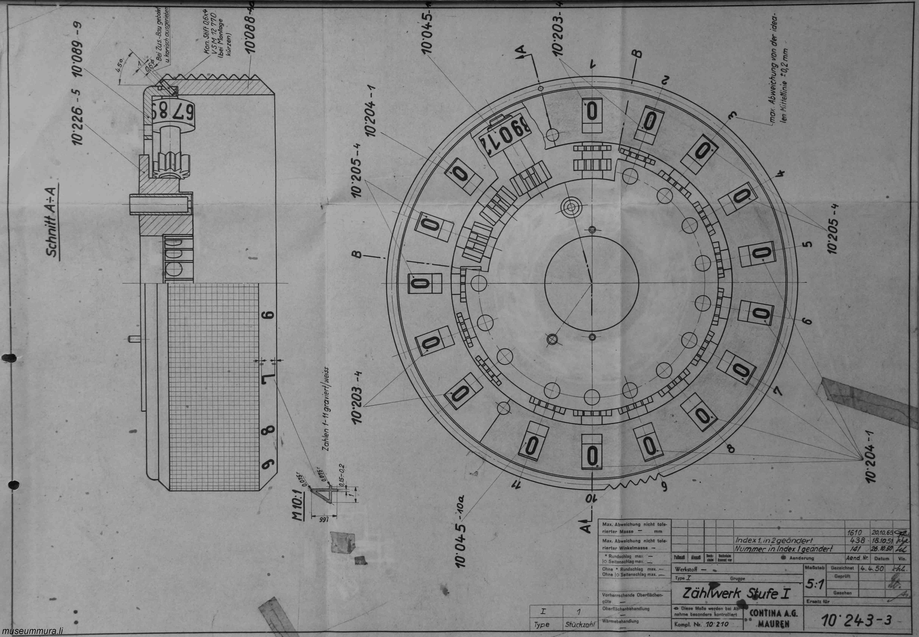
app/curta_jpegs/assembly/Curta_1_10243.jpg
