daeken/ReCurta/app/curta_jpegs/assembly/Curta_1_10244.jpg

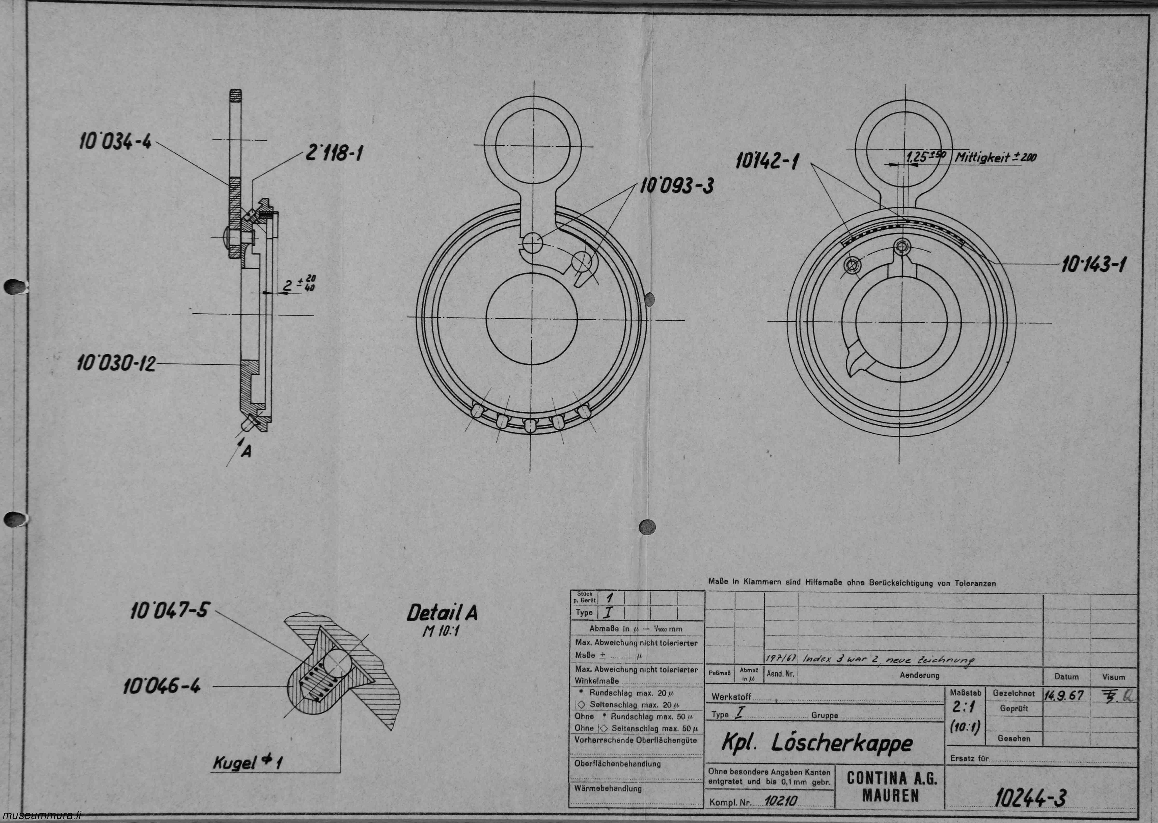
app/curta_jpegs/assembly/Curta_1_10244.jpg
