daeken/ReCurta/app/curta_jpegs/assembly/Curta_1_10245.jpg

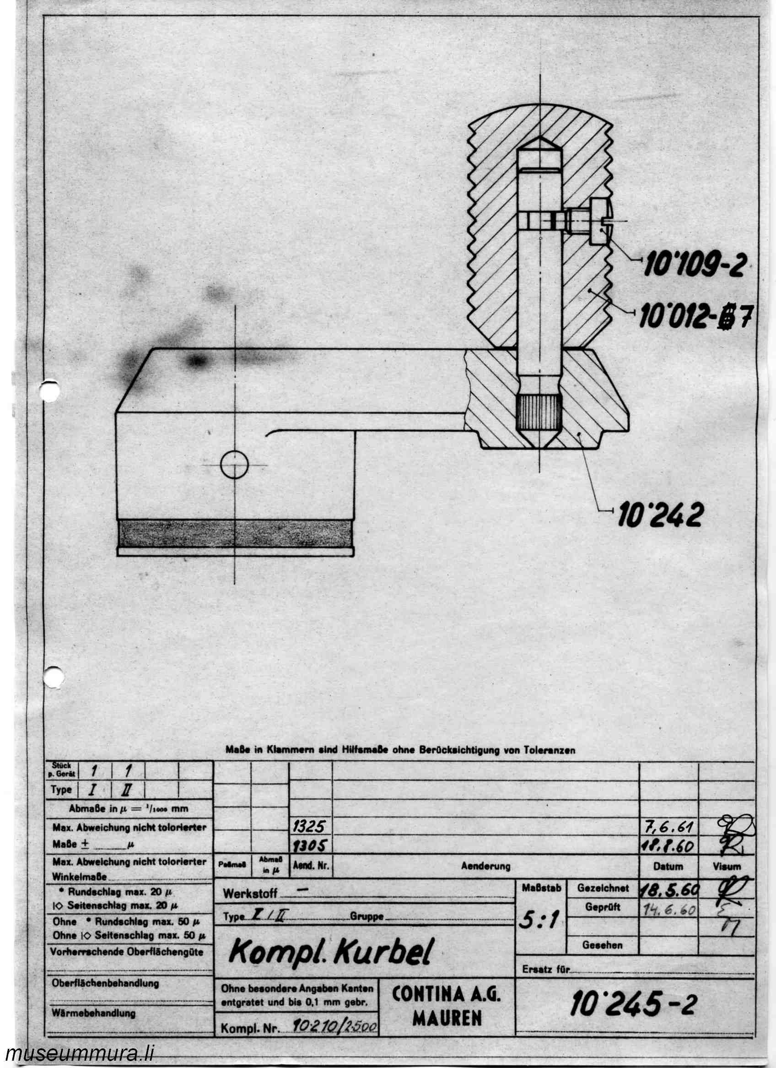
app/curta_jpegs/assembly/Curta_1_10245.jpg
