daeken/ReCurta/app/curta_jpegs/assembly/Curta_1_10246.jpg

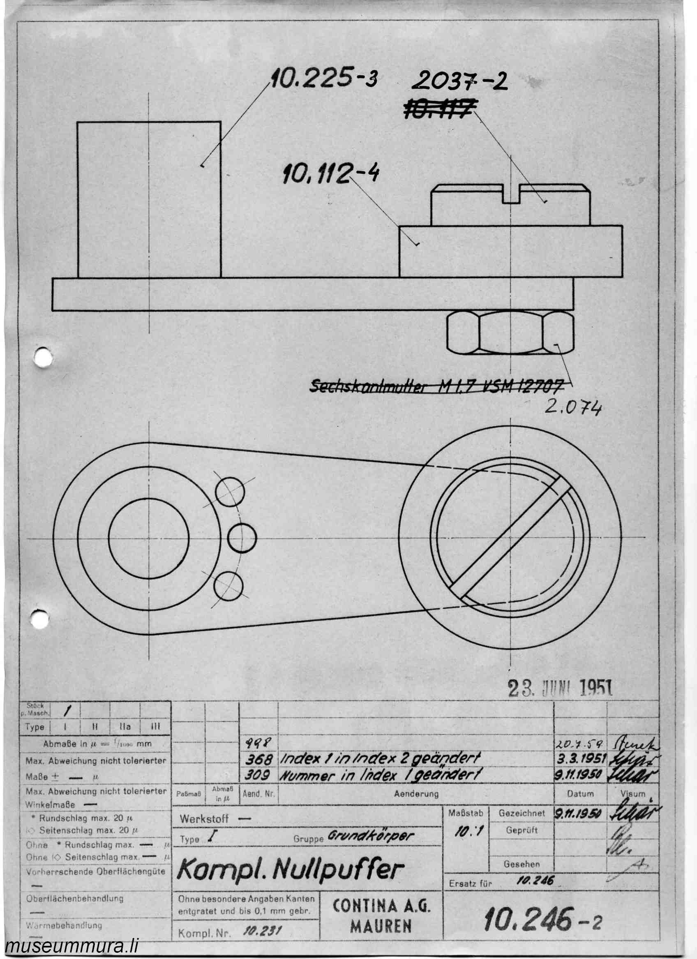
app/curta_jpegs/assembly/Curta_1_10246.jpg
