daeken/ReCurta/app/curta_jpegs/assembly/Curta_1_10247.jpg

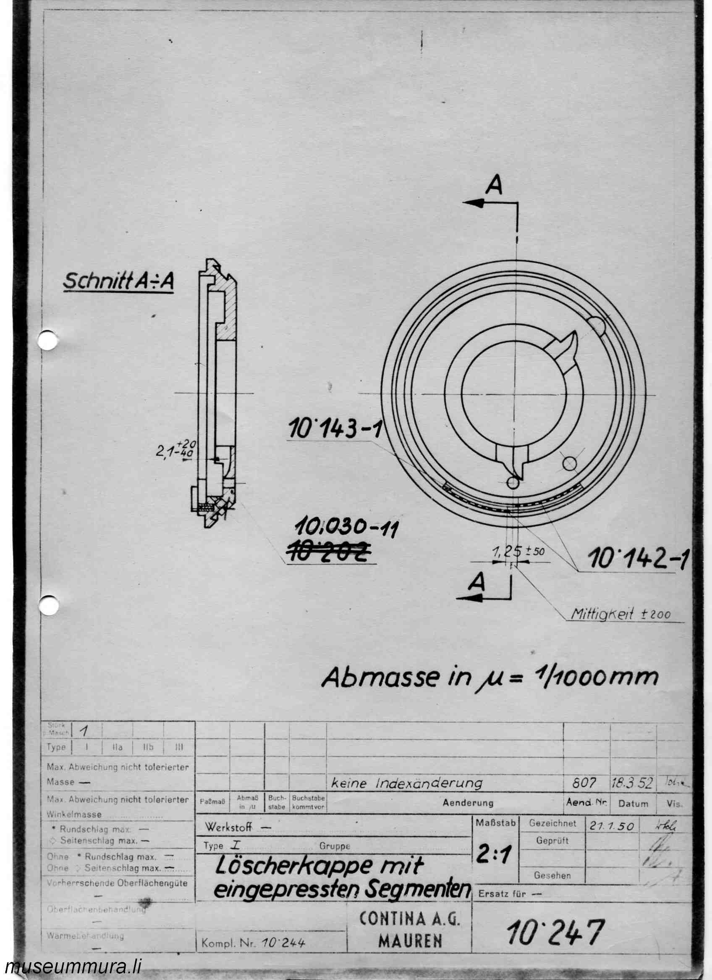
app/curta_jpegs/assembly/Curta_1_10247.jpg
