daeken/ReCurta/app/curta_jpegs/assembly/Curta_1_10248.jpg

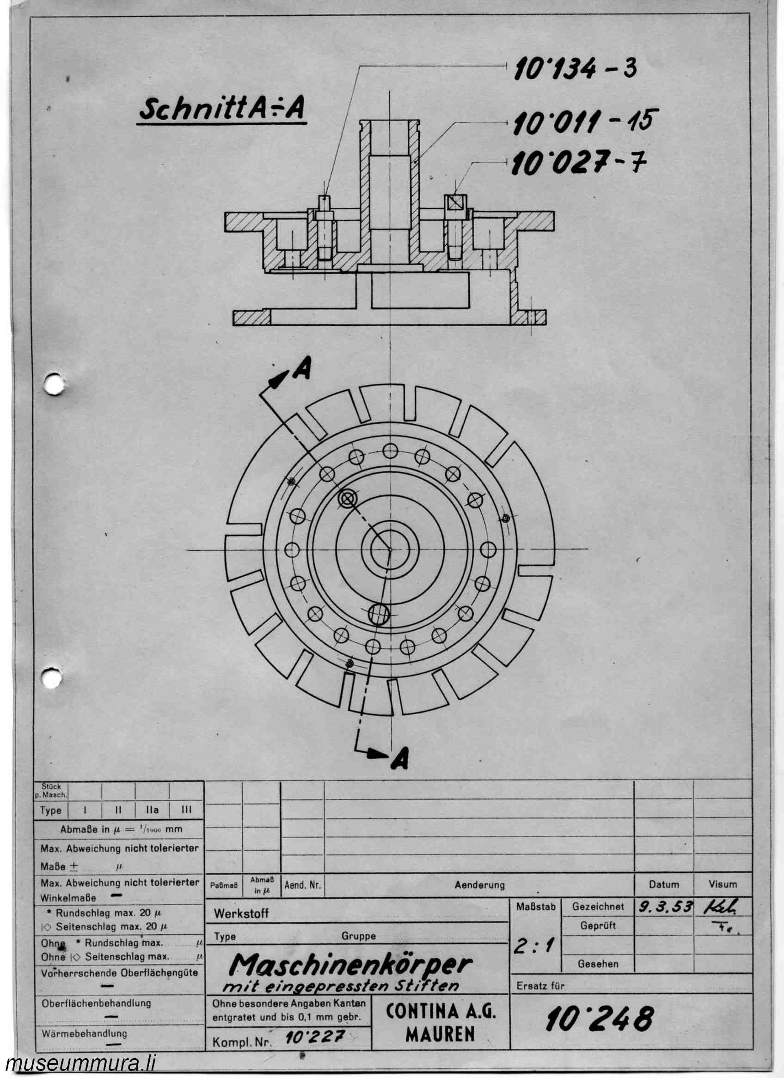
app/curta_jpegs/assembly/Curta_1_10248.jpg
