daeken/ReCurta/app/curta_jpegs/assembly/Curta_1_10249.jpg

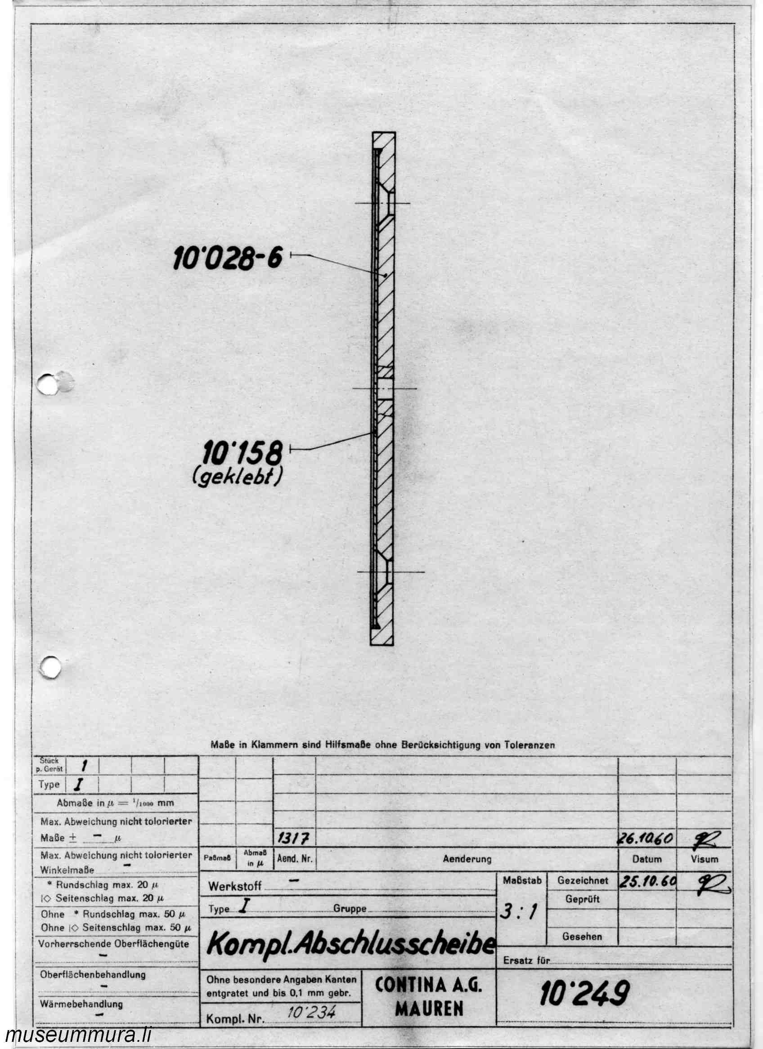
app/curta_jpegs/assembly/Curta_1_10249.jpg
