daeken/ReCurta/app/curta_jpegs/assembly/Curta_1_10250.jpg

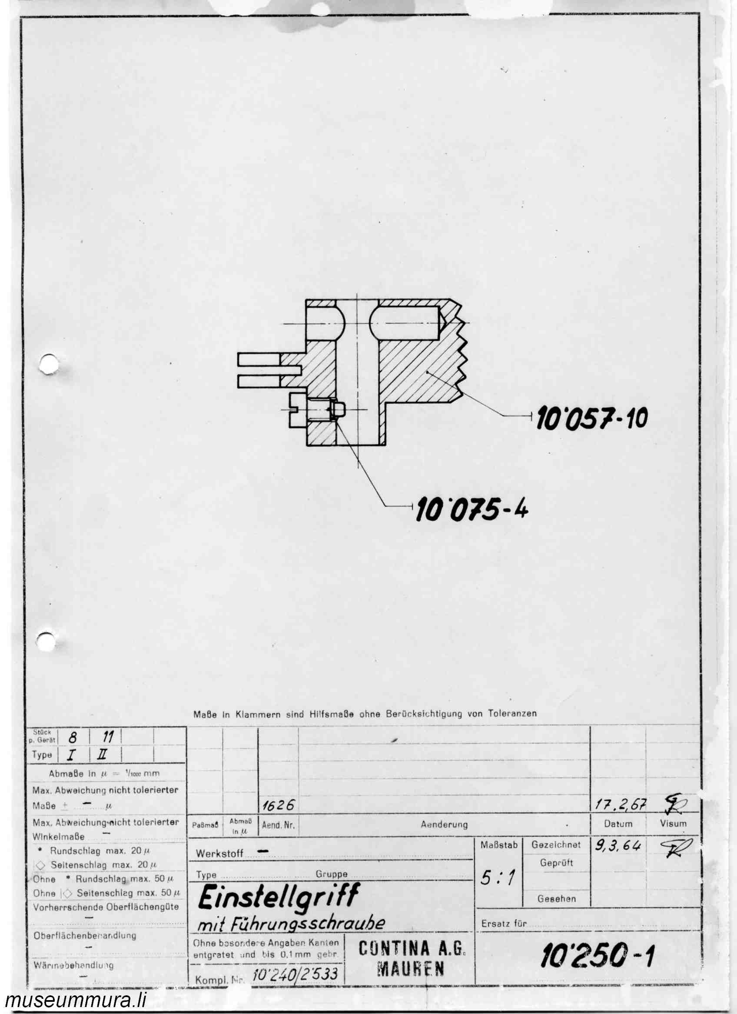
app/curta_jpegs/assembly/Curta_1_10250.jpg
