daeken/ReCurta/Solidworks Drawings/10018.pdf

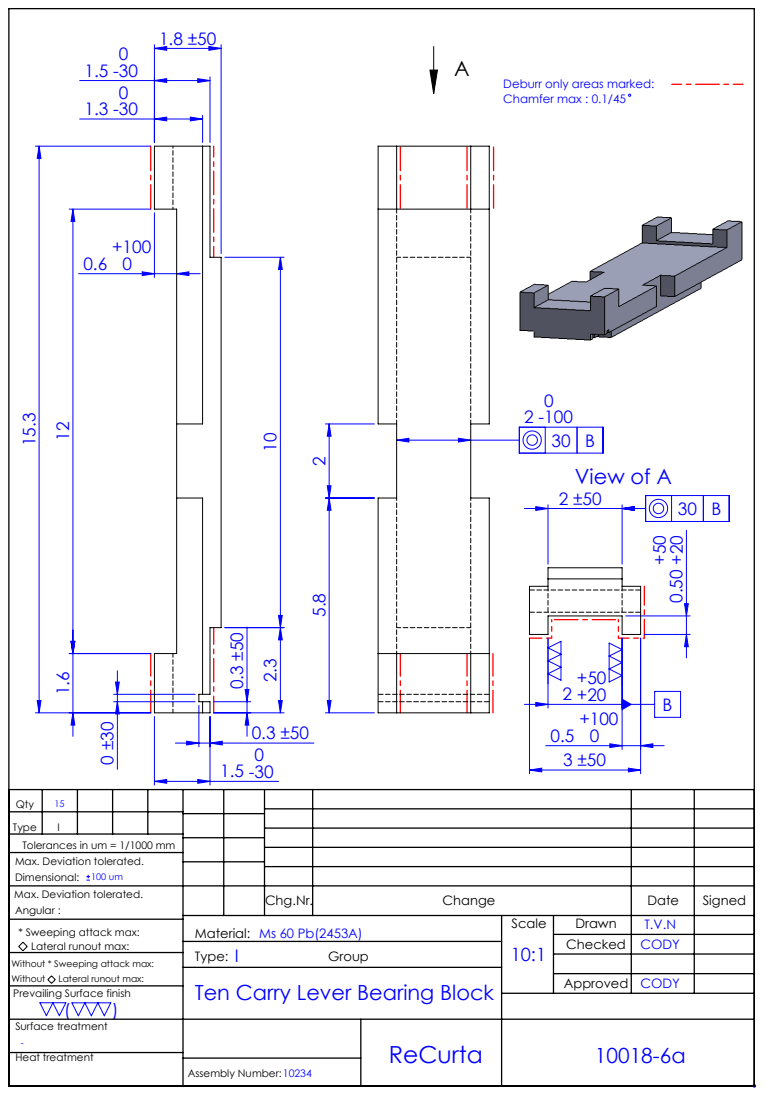
[picture p289: page 1]
View of A; Scale; Drawn Material:; Assembly Number:; Heat treatment; Surface treatment

Deburr only areas marked:
Chamfer max : 0.1/45

Qty | 15
Type | I

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

Ten Carry Lever Bearing Block
