daeken/ReCurta/Solidworks Drawings/10019.pdf

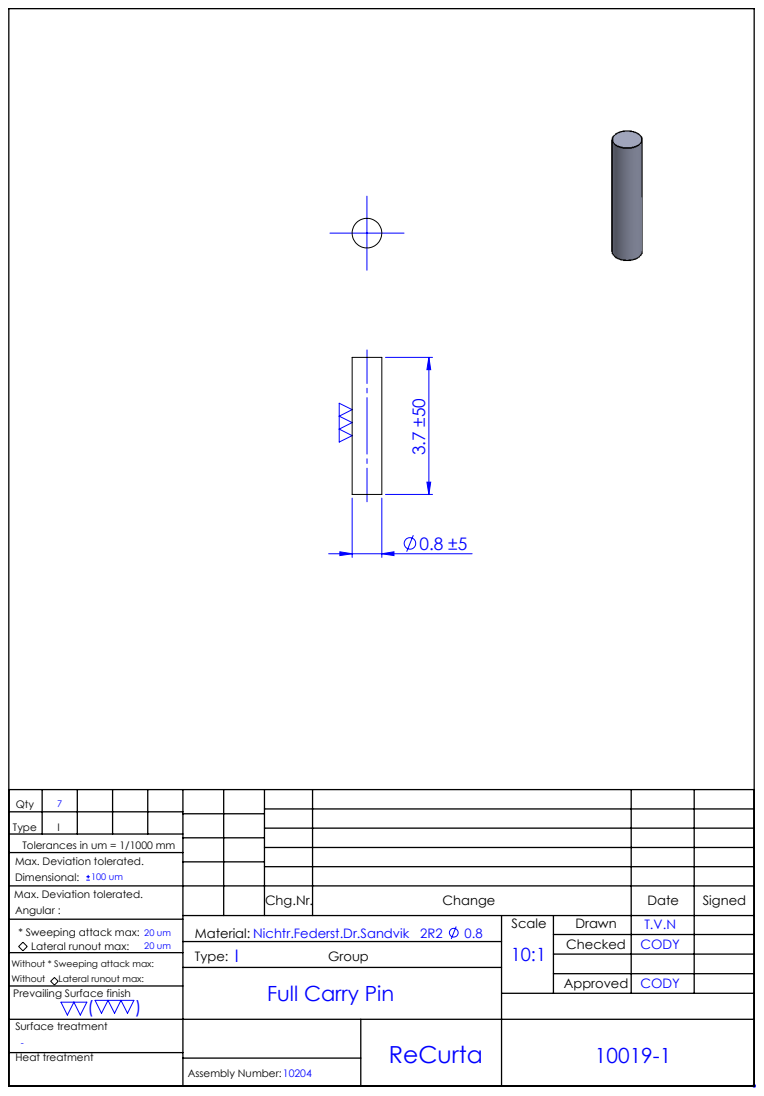
[picture p290: page 1]
Assembly Number:; Heat treatment; Surface treatment

Qty | 7
Type | I

Tolerances in um = 1/1000 mm
Max. Deviation tolerated.
Dimensional:

Max. Deviation tolerated. Angular : | | | Chg.Nr. | Change | Date | Signed

Nichtr.Federst.Dr.Sandvik 2R2 0.8 | Scale 10:1 | Drawn Material: | T.V.N

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

Full Carry Pin

Checked | CODY
