daeken/ReCurta/Solidworks Drawings/10020.pdf

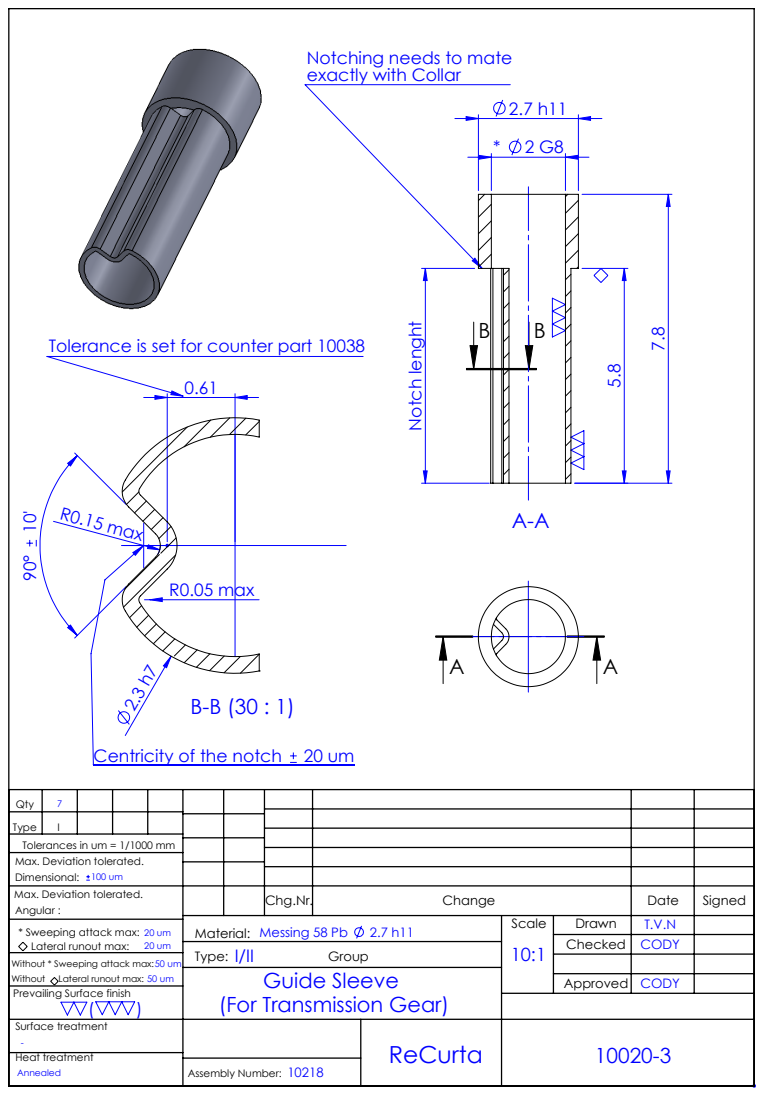
[picture p291: page 1]
Notch lenght; R0.05 max; R0.15 max; Centricity of the notch; Assembly Number:; Heat treatment; Surface treatment

Notching needs to mate
exactly with Collar

Tolerance is set for counter part 10038

Qty | 7
Type | I

Tolerances in um = 1/1000 mm
Max. Deviation tolerated.
Dimensional:

Max. Deviation tolerated. Angular : | | | Chg.Nr. | Change | Date | Signed

Messing 58 Pb 2.7 h11 | Scale 10:1 | Drawn Material: | T.V.N

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

Guide Sleeve
(For Transmission Gear)

Checked | CODY
