daeken/ReCurta/Solidworks Drawings/10023.pdf

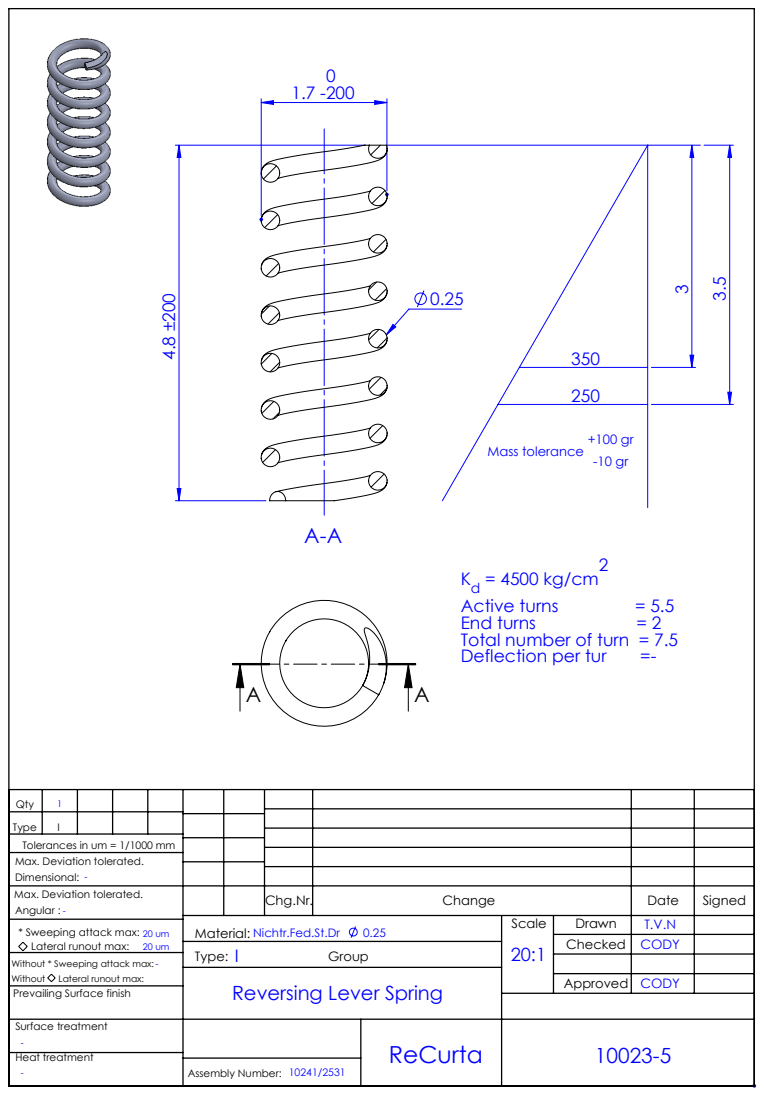
[picture p292: page 1]
Mass tolerance; Active turns; End turns; Deflection per tur; Scale; Drawn Material:; Assembly Number:; Heat treatment; Surface treatment

Total number of turn = 7.5

Qty | 1
Type | I

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

Reversing Lever Spring
