daeken/ReCurta/Solidworks Drawings/10024.pdf

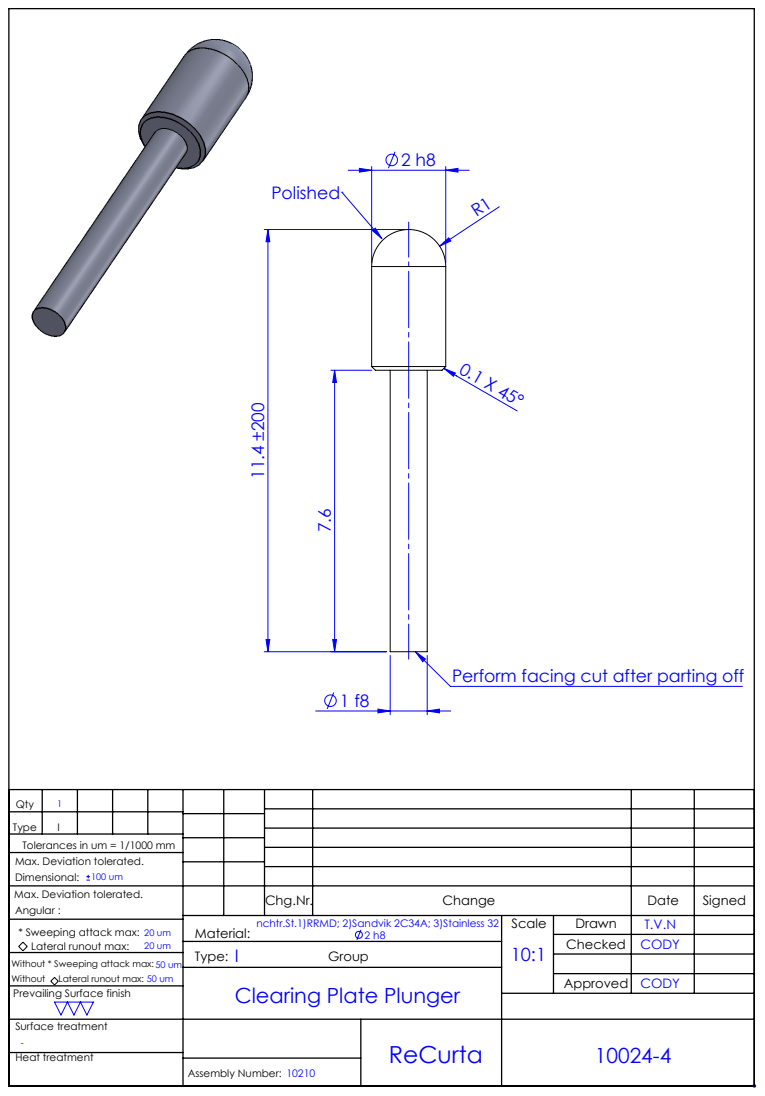
[picture p293: page 1]
Assembly Number:; Heat treatment; Surface treatment

Perform facing cut after parting off

Qty | 1
Type | I

Tolerances in um = 1/1000 mm
Max. Deviation tolerated.
Dimensional:

Max. Deviation tolerated. Angular : | | | Chg.Nr. | Change | Date | Signed

nchtr.St.1)RRMD; 2)Sandvik 2C34A; 3)Stainless 32 2 h8 | Scale 10:1 | Drawn Material: | T.V.N

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

Clearing Plate Plunger

Checked | CODY
