daeken/ReCurta/Solidworks Drawings/10025.pdf

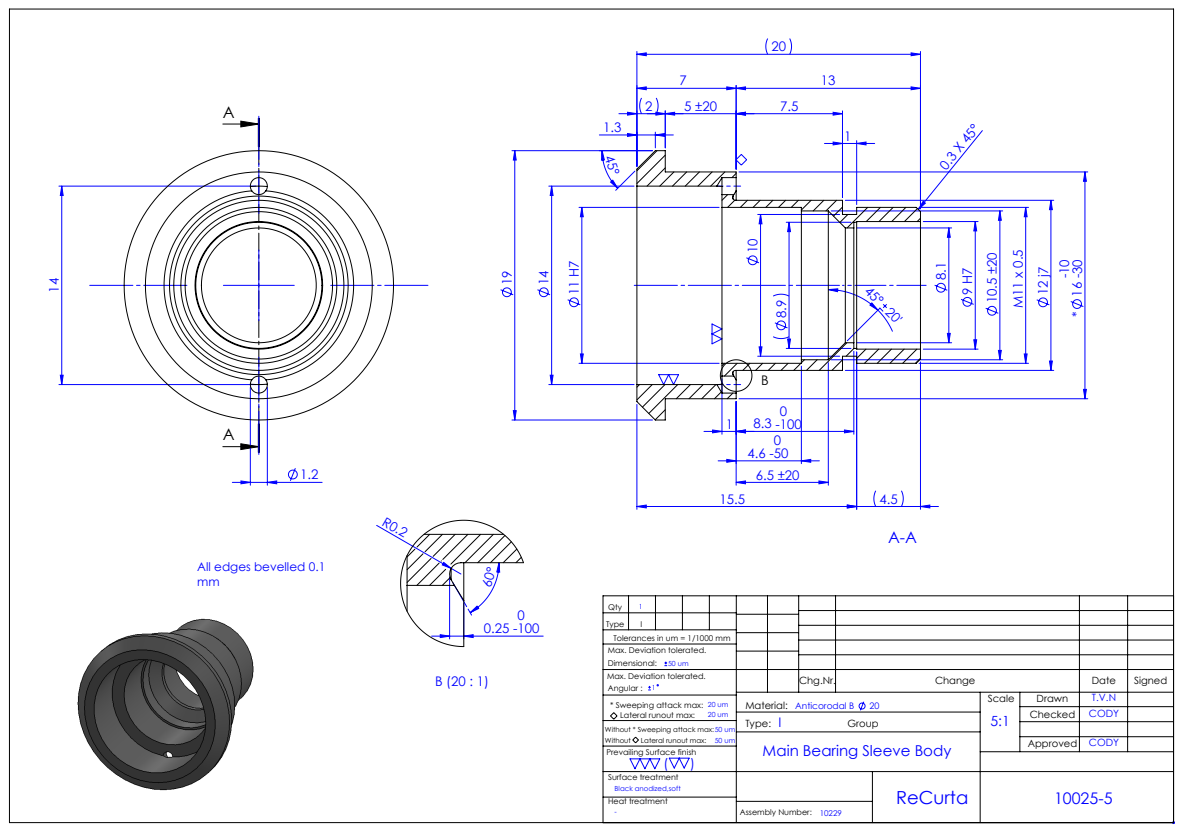
[picture p294: page 1]
Anticorodal B; Assembly Number:

All edges bevelled 0.1

Qty | 1
Type | I

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

Main Bearing Sleeve Body

Surface treatment
Black anodized,soft
Heat treatment
