daeken/ReCurta/Solidworks Drawings/10026.pdf

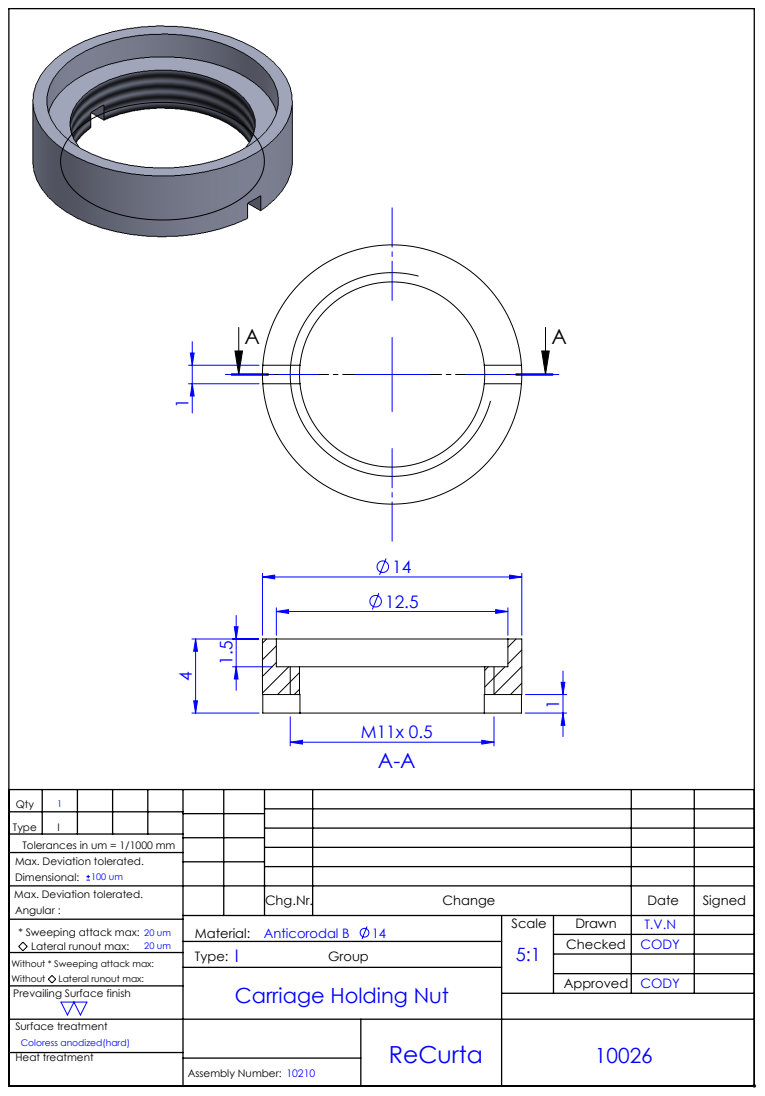
[picture p295: page 1]
Assembly Number:

Qty | 1
Type | I

Tolerances in um = 1/1000 mm
Max. Deviation tolerated.
Dimensional:

Max. Deviation tolerated. Angular : | | | Chg.Nr. | Change | Date | Signed

Anticorodal B 14 | Scale 5:1 | Drawn Material: | T.V.N

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

Carriage Holding Nut

Checked | CODY

Surface treatment
Coloress anodized(hard)
Heat treatment
