daeken/ReCurta/Solidworks Drawings/10028.pdf

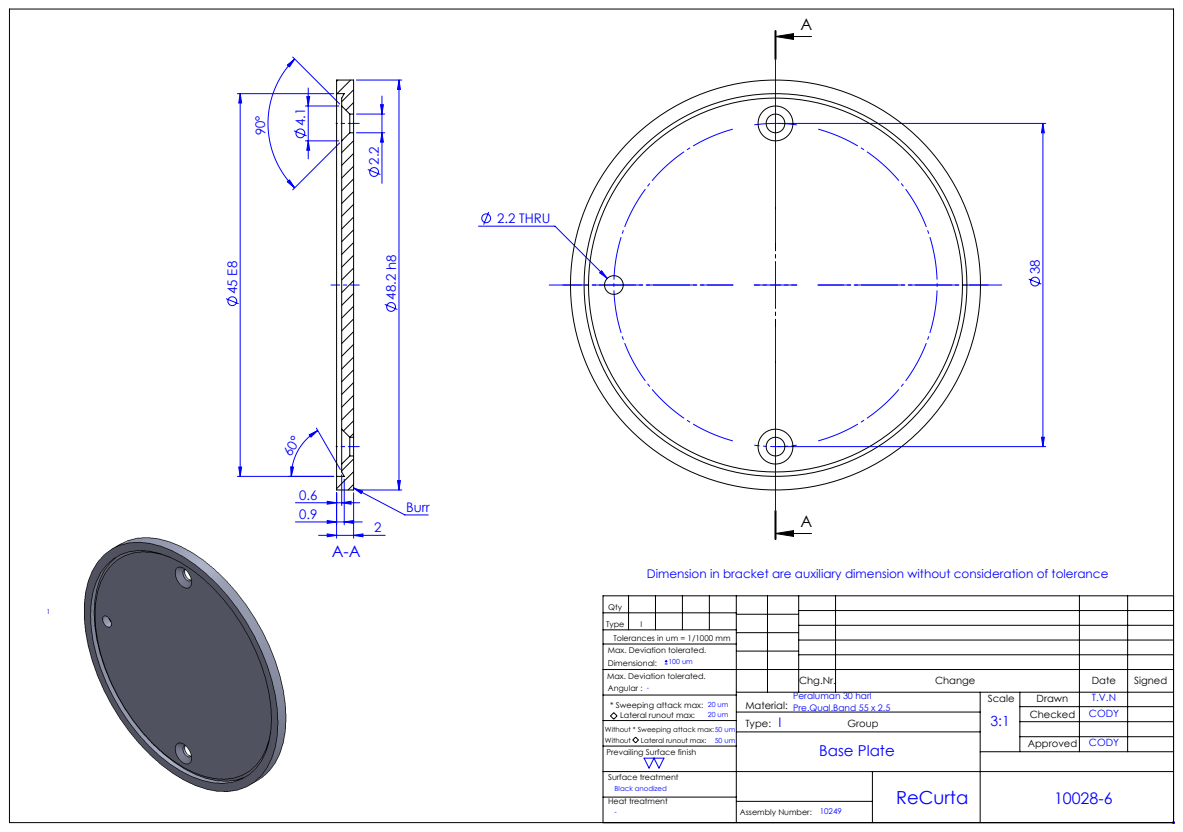
[picture p296: page 1]
2.2 THRU; Black anodized; Base Plate; Surface treatment; Heat treatment; Assembly Number:

Dimension in bracket are auxiliary dimension without consideration of tolerance

Qty
Type | I

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

Peraluman 30 harl
Pre.Qual.Band 55 x 2.5
