daeken/ReCurta/Solidworks Drawings/10029.pdf

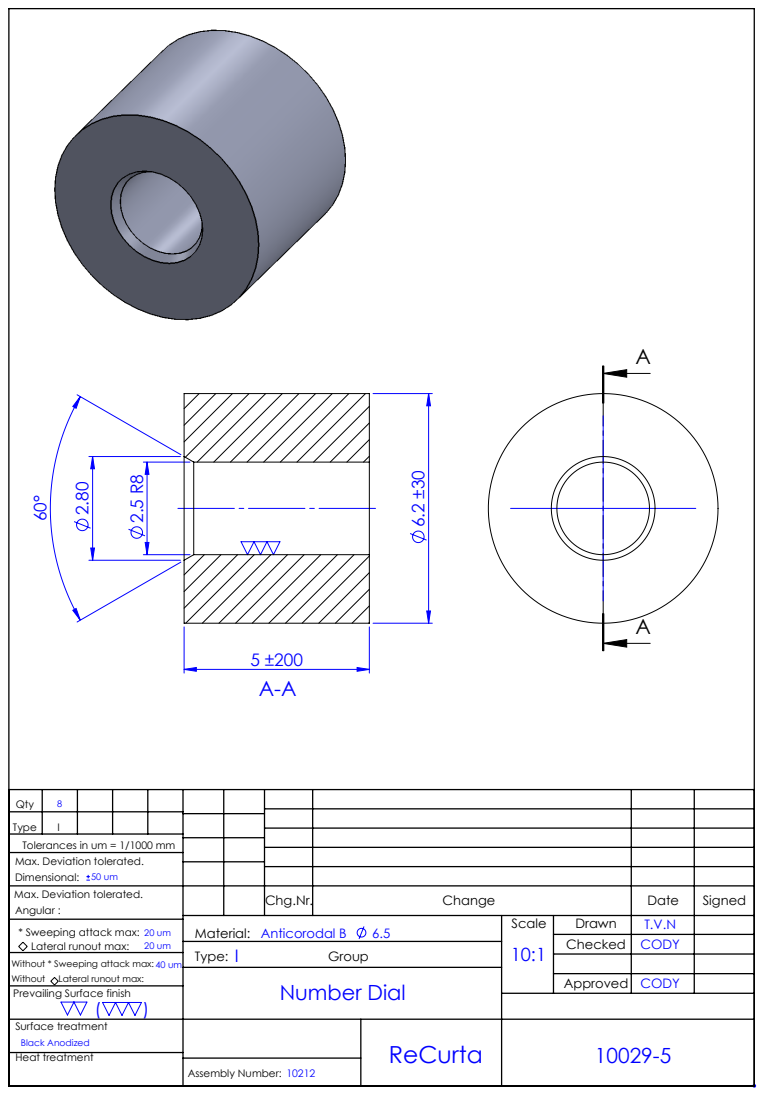
[picture p297: page 1]
Number Dial; Black Anodized; Assembly Number:; Heat treatment; Surface treatment

Qty | 8
Type | I

Tolerances in um = 1/1000 mm
Max. Deviation tolerated.
Dimensional:

Max. Deviation tolerated. Angular : | | | Chg.Nr. | Change | Date | Signed

Anticorodal B 6.5 | Scale 10:1 | Drawn Material: | T.V.N

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

Checked | CODY
