daeken/ReCurta/Solidworks Drawings/10030.pdf

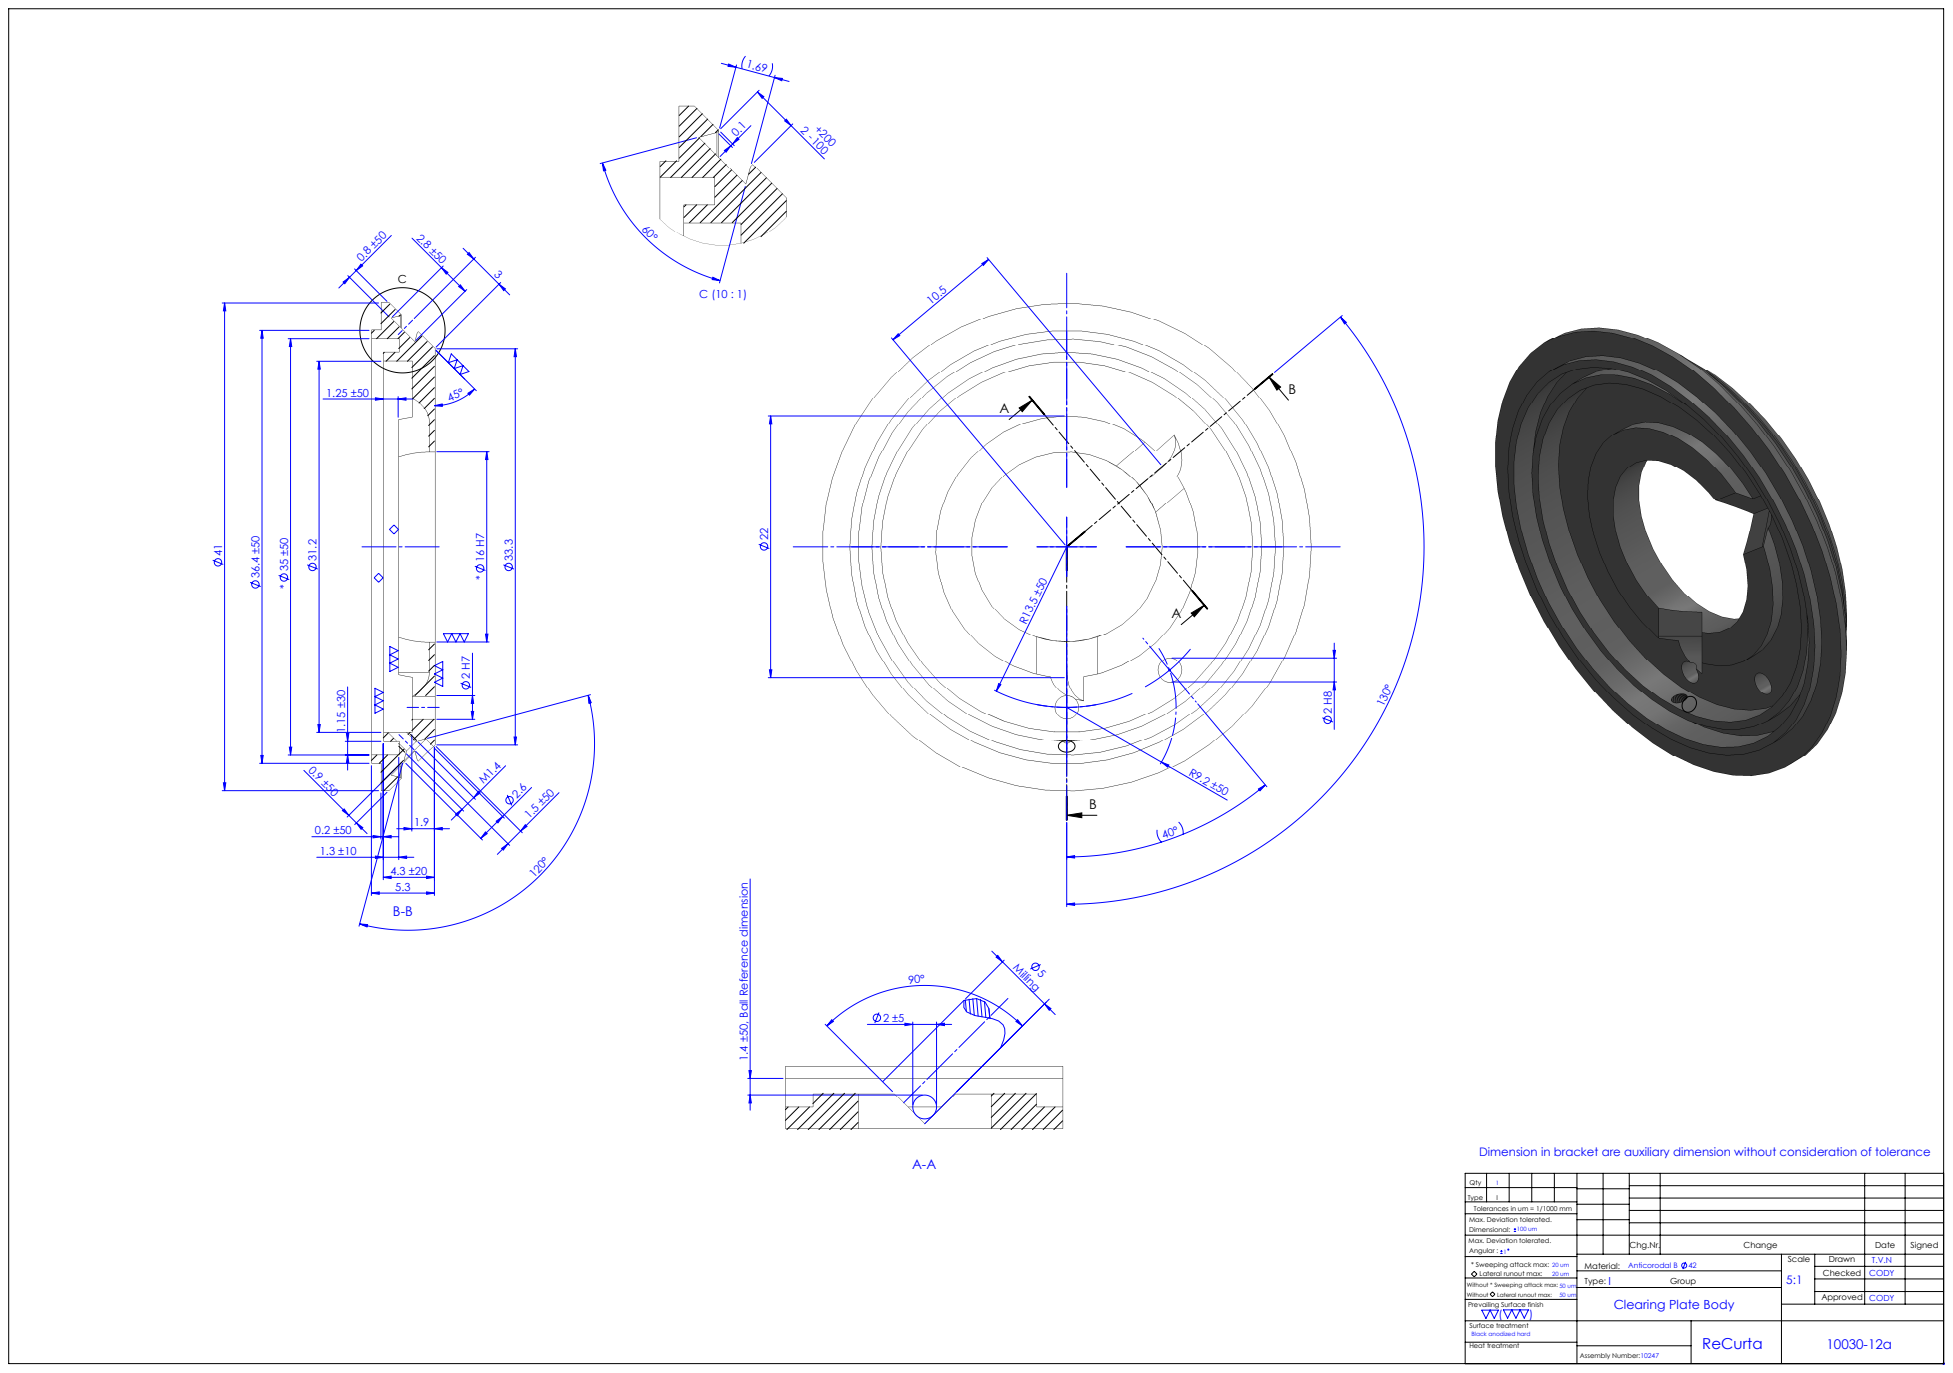
[picture p298: page 1]
Anticorodal B 42; Assembly Number:

1.4 ±50, Ball Reference dimension

Dimension in bracket are auxiliary dimension without consideration of tolerance

Qty | 1
Type | I

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

Clearing Plate Body

Surface treatment
Black anodized hard
Heat treatment
