daeken/ReCurta/Solidworks Drawings/10035.pdf

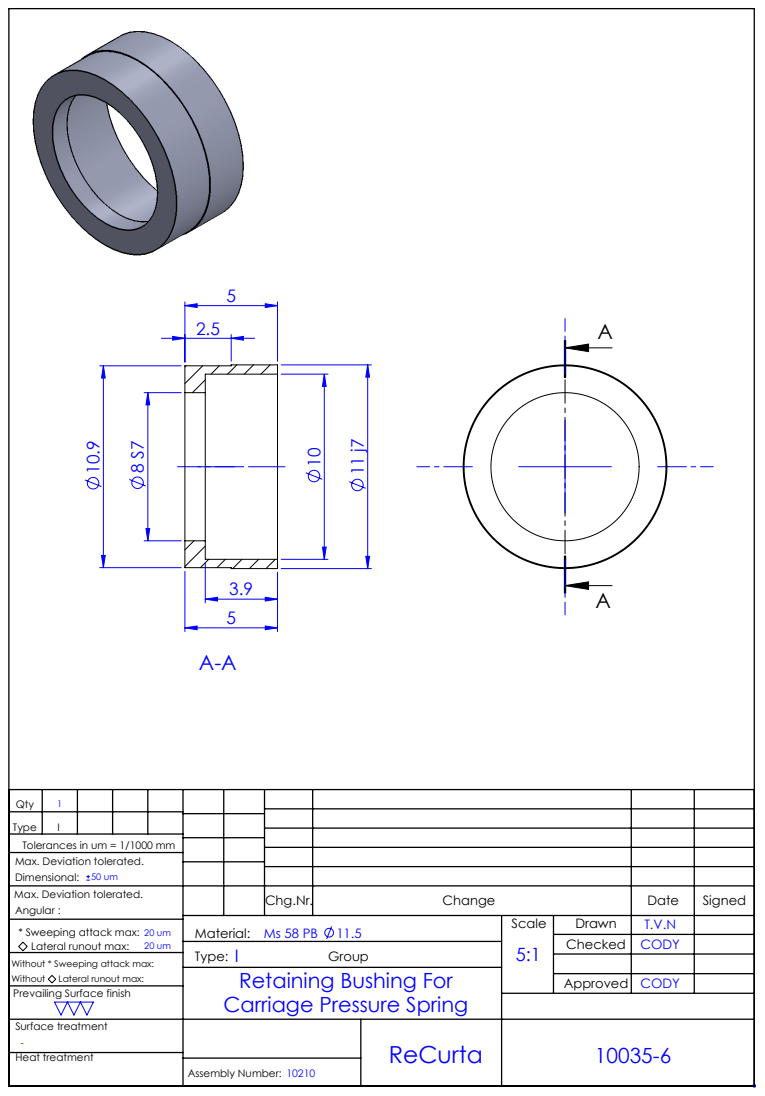
[picture p299: page 1]
Assembly Number:; Heat treatment; Surface treatment

Qty | 1
Type | I

Tolerances in um = 1/1000 mm
Max. Deviation tolerated.
Dimensional:

Max. Deviation tolerated. Angular : | | | Chg.Nr. | Change | Date | Signed

Ms 58 PB 11.5 | Scale 5:1 | Drawn Material: | T.V.N

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

Retaining Bushing For
Carriage Pressure Spring

Checked | CODY
