daeken/ReCurta/Solidworks Drawings/10038.pdf

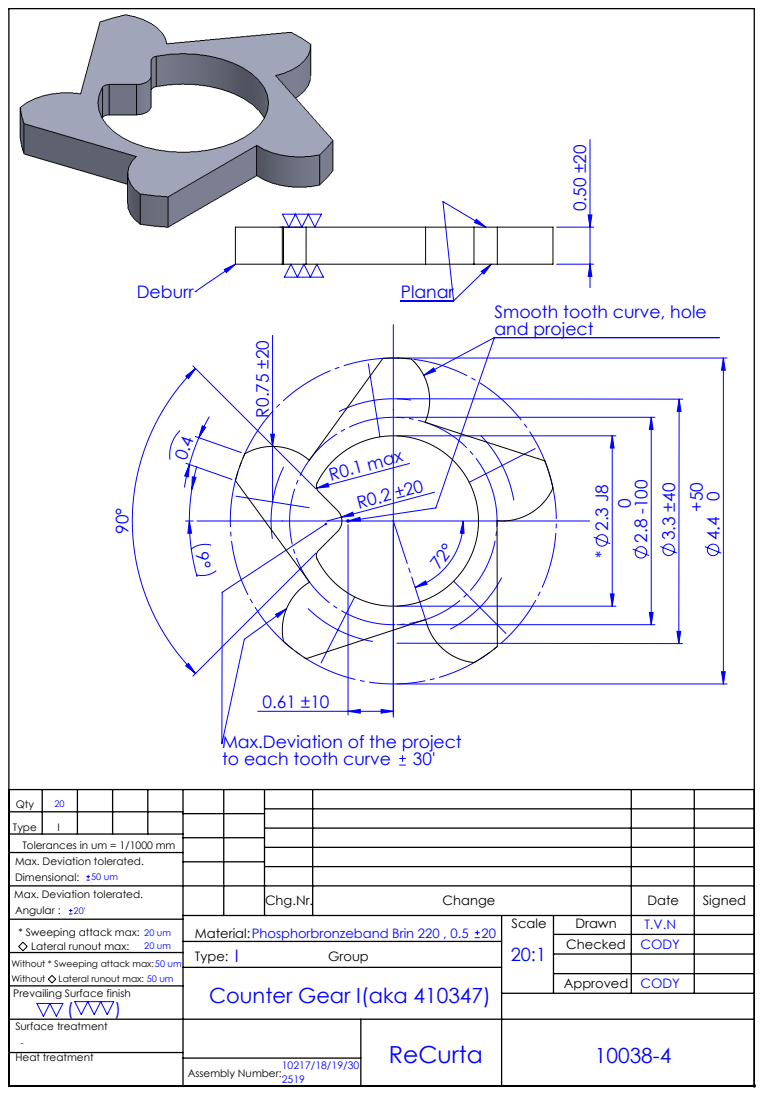
[picture p300: page 1]
Deburr; Planar R0.75 ±20; R0.1 max; to each tooth curve; Assembly Number:; Heat treatment; Surface treatment

Smooth tooth curve, hole
and project

Max.Deviation of the project

Qty | 20
Type | I

Tolerances in um = 1/1000 mm
Max. Deviation tolerated.
Dimensional:

Max. Deviation tolerated. Angular : 20' | | | Chg.Nr. | Change | Date | Signed

Phosphorbronzeband Brin 220 , 0.5 20 | Scale 20:1 | Drawn Material: | T.V.N

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

Counter Gear I(aka 410347)

Checked | CODY
