daeken/ReCurta/Solidworks Drawings/10039.pdf

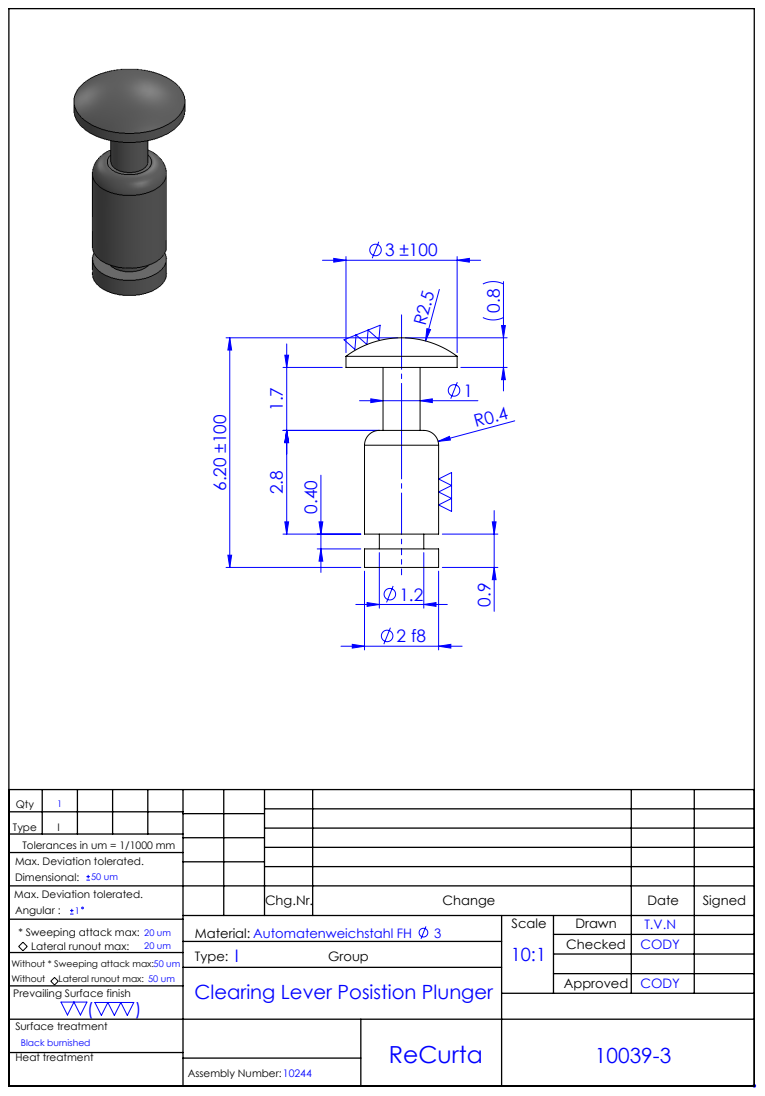
[picture p301: page 1]
Black burnished; Assembly Number:; Heat treatment; Surface treatment

Qty | 1
Type | I

Tolerances in um = 1/1000 mm
Max. Deviation tolerated.
Dimensional:

Max. Deviation tolerated. Angular : 1 | | | Chg.Nr. | Change | Date | Signed

Automatenweichstahl FH 3 | Scale 10:1 | Drawn Material: | T.V.N

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

Clearing Lever Posistion Plunger

Checked | CODY
