daeken/ReCurta/Solidworks Drawings/10040.pdf

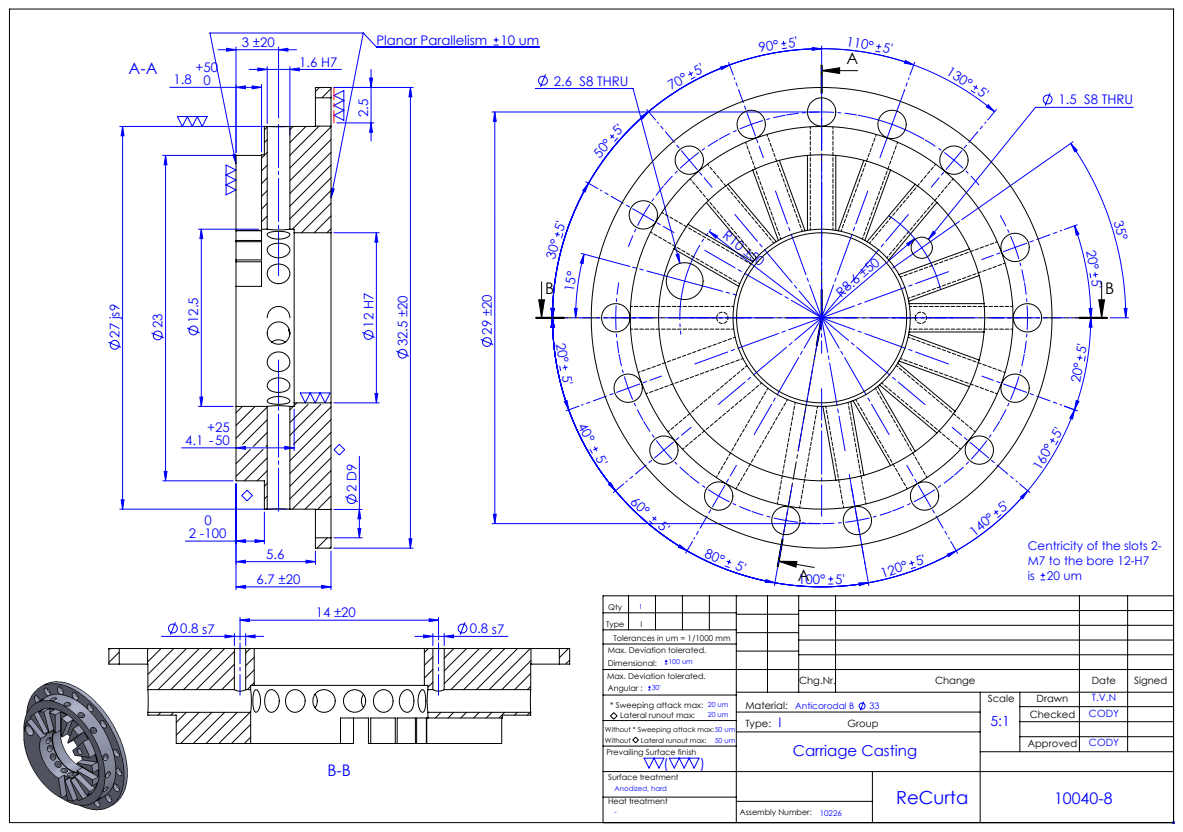
[picture p302: page 1]
1.5 S8 THRU; 2.6 S8 THRU; Planar Parallelism; Anodized, hard; Anticorodal B; Carriage Casting; Surface treatment; Heat treatment; Assembly Number:

Centricity of the slots 2-
M7 to the bore 12-H7

Qty | 1
Type | I

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
