daeken/ReCurta/Solidworks Drawings/10042.pdf

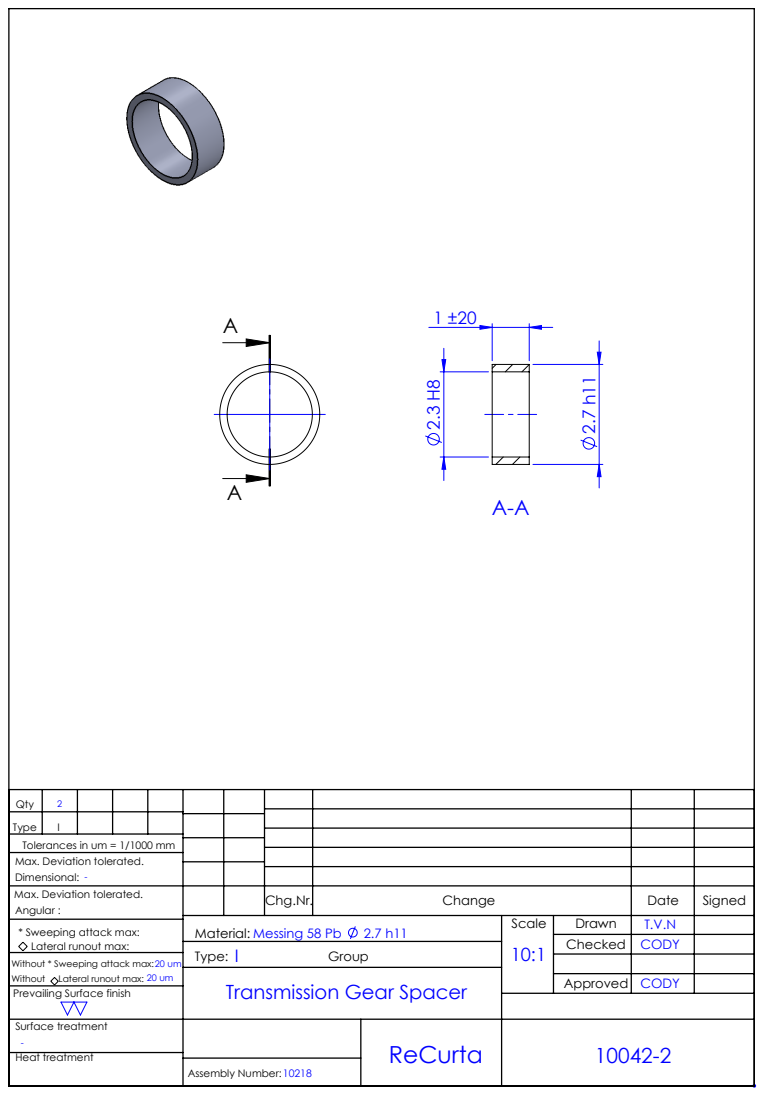
[picture p303: page 1]
Messing 58 Pb; Scale; Drawn Material:; Assembly Number:; Heat treatment; Surface treatment

Qty | 2
Type | I

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

Transmission Gear Spacer
