daeken/ReCurta/Solidworks Drawings/10043.pdf

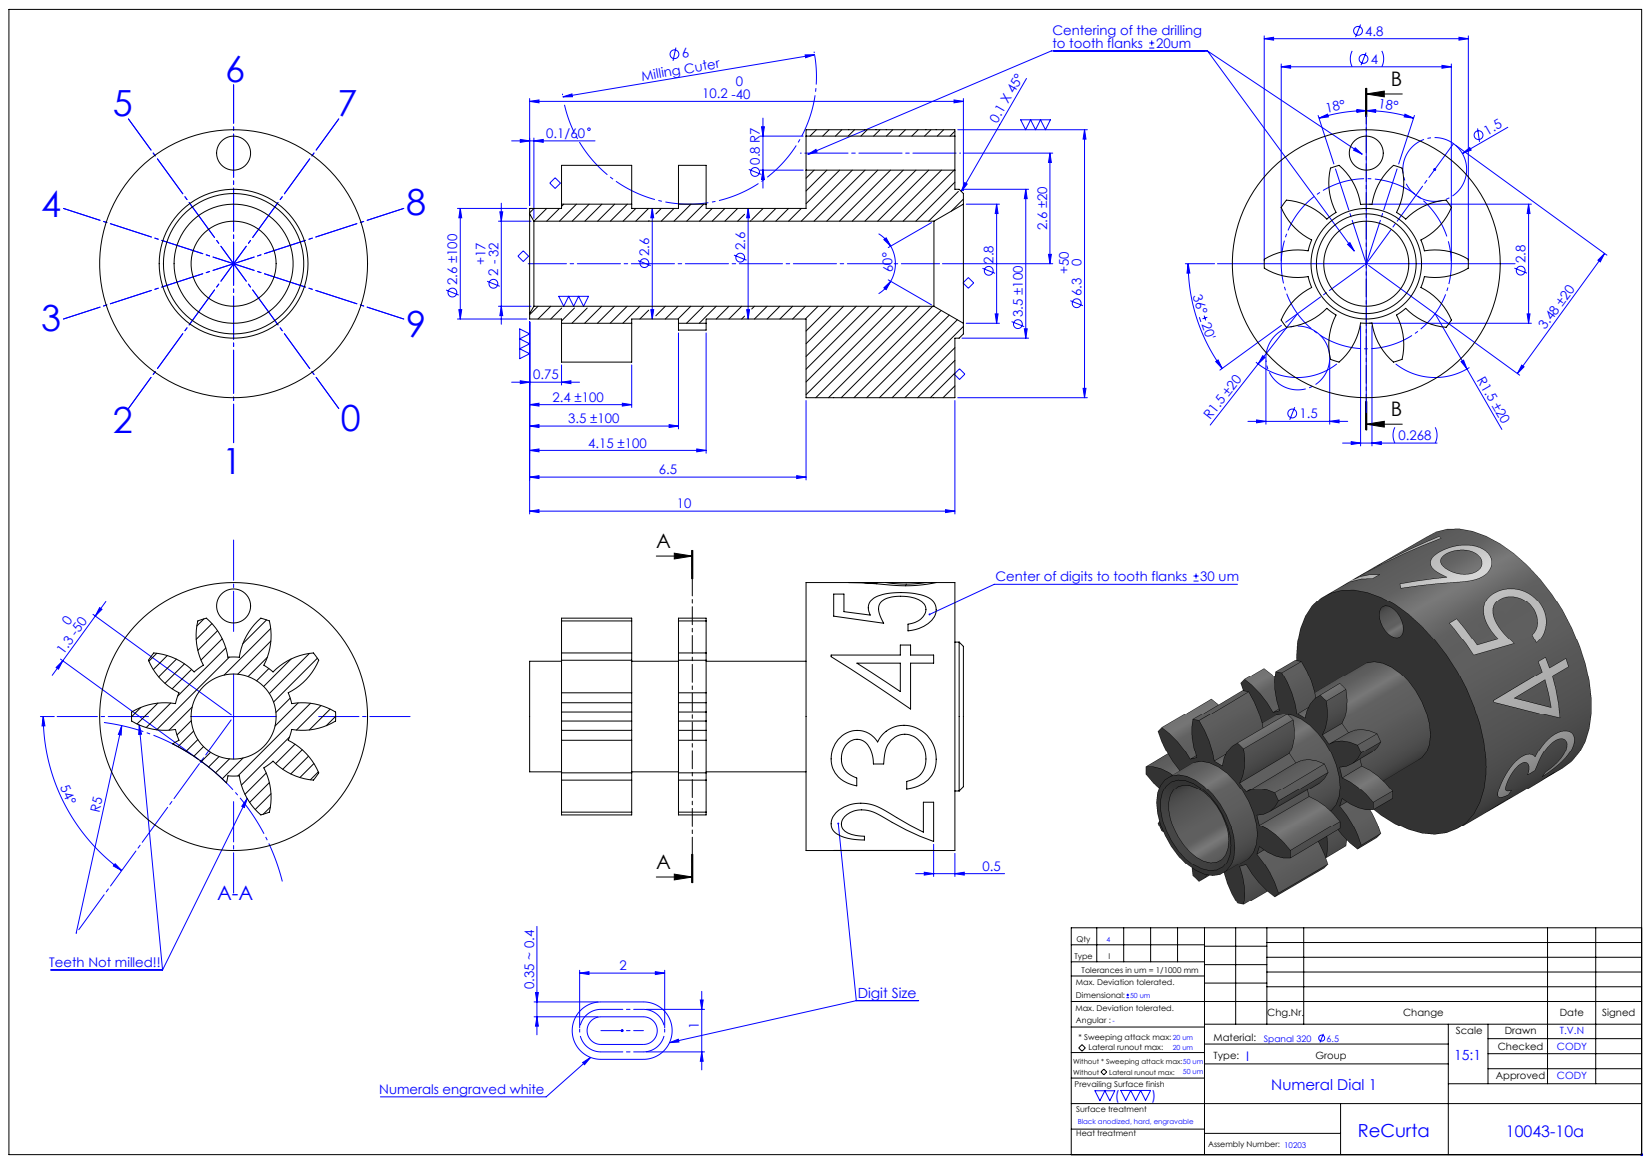
[picture p304: page 1]
Center of digits to tooth flanks; Milling Cuter; Spanal 320; Numeral Dial 1; Digit Size; to tooth flanks; Scale; Drawn Material:; Assembly Number:

Centering of the drilling

Qty | 4
Type | I

Teeth Not milled!!

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

Numerals engraved white

Surface treatment
10043-10a Black anodized, hard, engravable
Heat treatment
