daeken/ReCurta/Solidworks Drawings/10045.pdf

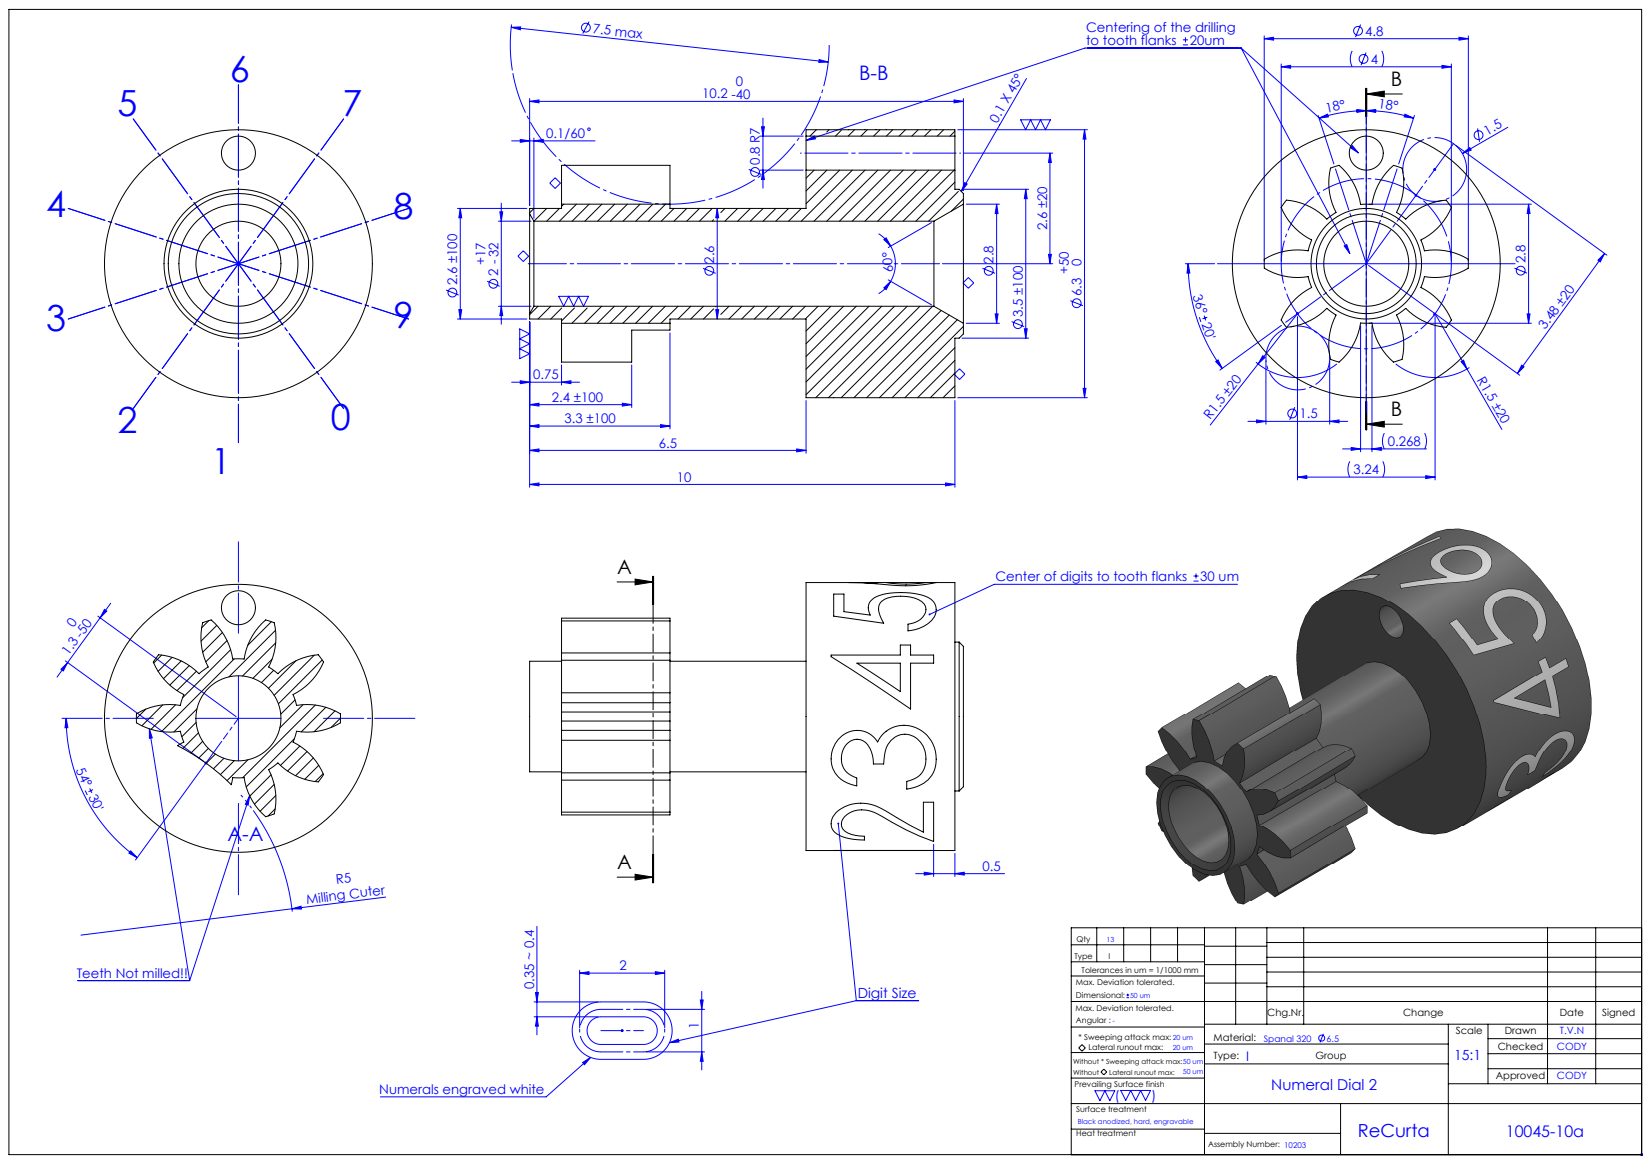
[picture p305: page 1]
Center of digits to tooth flanks; Milling Cuter; 7.5 max; to tooth flanks; Spanal 320; Numeral Dial 2; Digit Size; Scale; Drawn Material:; Assembly Number:

Centering of the drilling

Qty | 13
Type | I

Teeth Not milled!!

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

Numerals engraved white

Surface treatment
10045-10a Black anodized, hard, engravable
Heat treatment
