daeken/ReCurta/Solidworks Drawings/10047.pdf

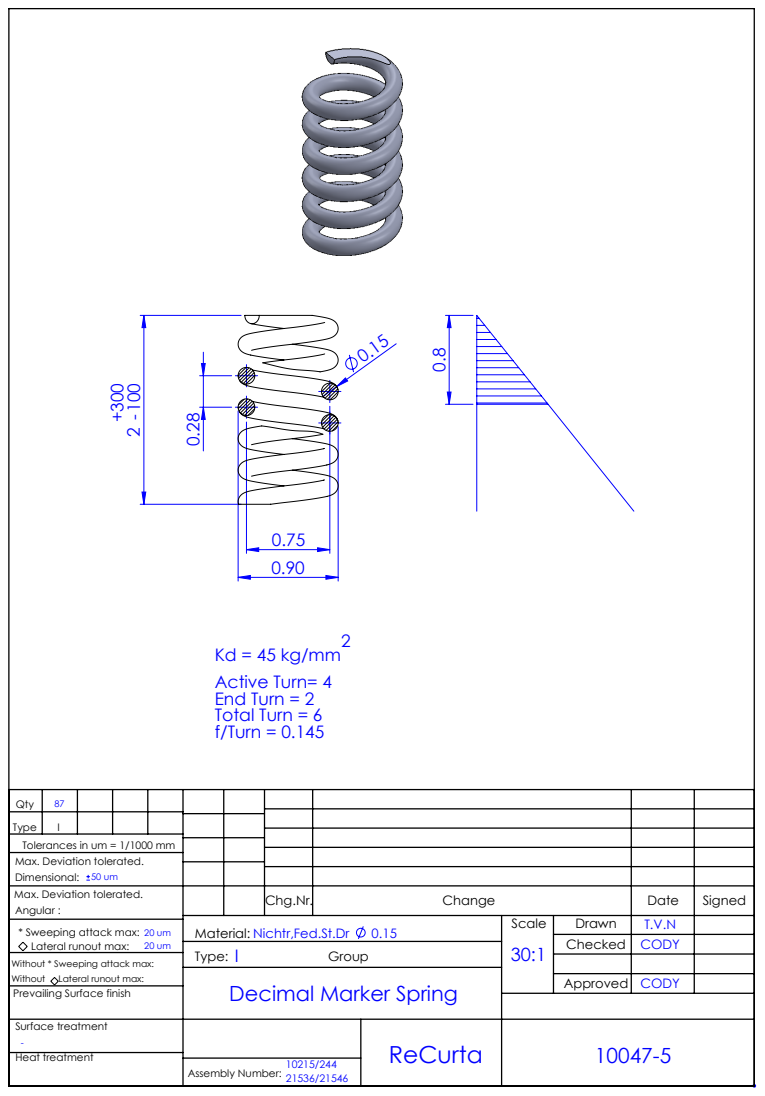
[picture p306: page 1]
Assembly Number:; Heat treatment; Surface treatment

Active Turn= 4
End Turn = 2
Total Turn = 6
f/Turn = 0.145

Qty | 87
Type | I

Tolerances in um = 1/1000 mm
Max. Deviation tolerated.
Dimensional:

Max. Deviation tolerated. Angular : | | | Chg.Nr. | Change | Date | Signed

Nichtr,Fed.St.Dr 0.15 | Scale 30:1 | Drawn Material: | T.V.N

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

Decimal Marker Spring

Checked | CODY
