daeken/ReCurta/Solidworks Drawings/10049.pdf

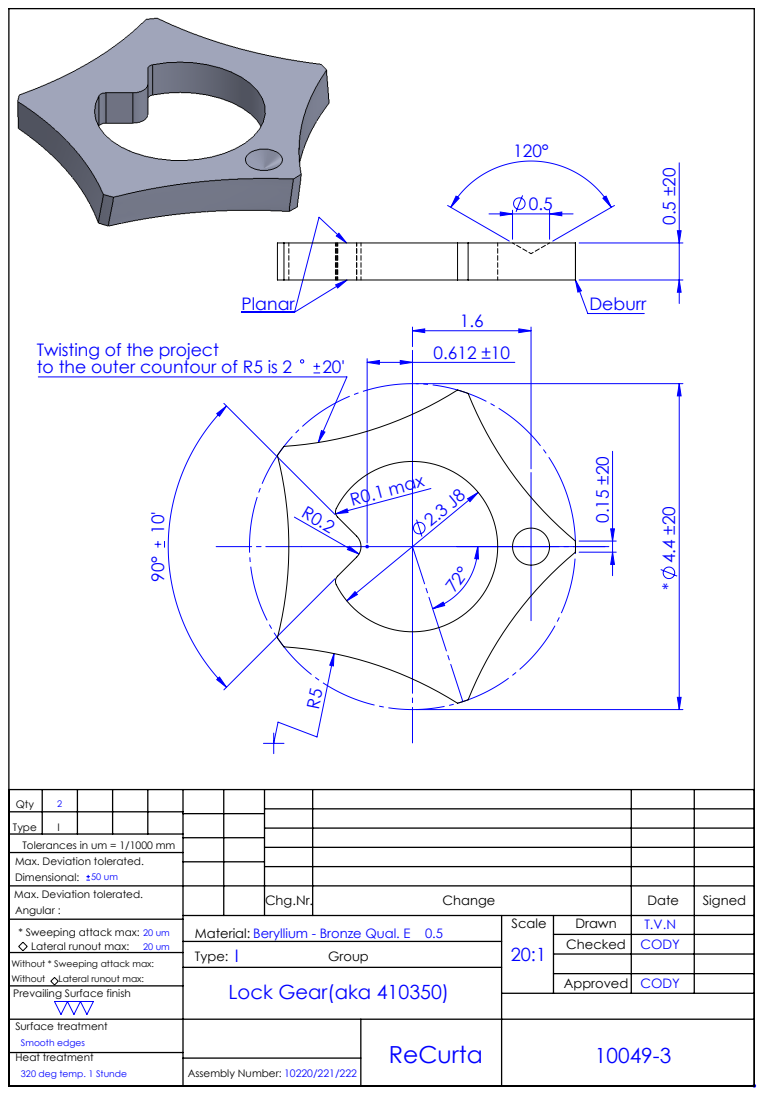
[picture p307: page 1]
R0.1 max R0.2; Twisting of the project; to the outer countour of R5 is 2; Scale; Drawn Material:; Assembly Number:

Qty | 2
Type | I

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

Beryllium - Bronze Qual. E 0.5
Lock Gear(aka 410350)

Surface treatment
Smooth edges
Heat treatment
320 deg temp. 1 Stunde
