daeken/ReCurta/Solidworks Drawings/10062.pdf

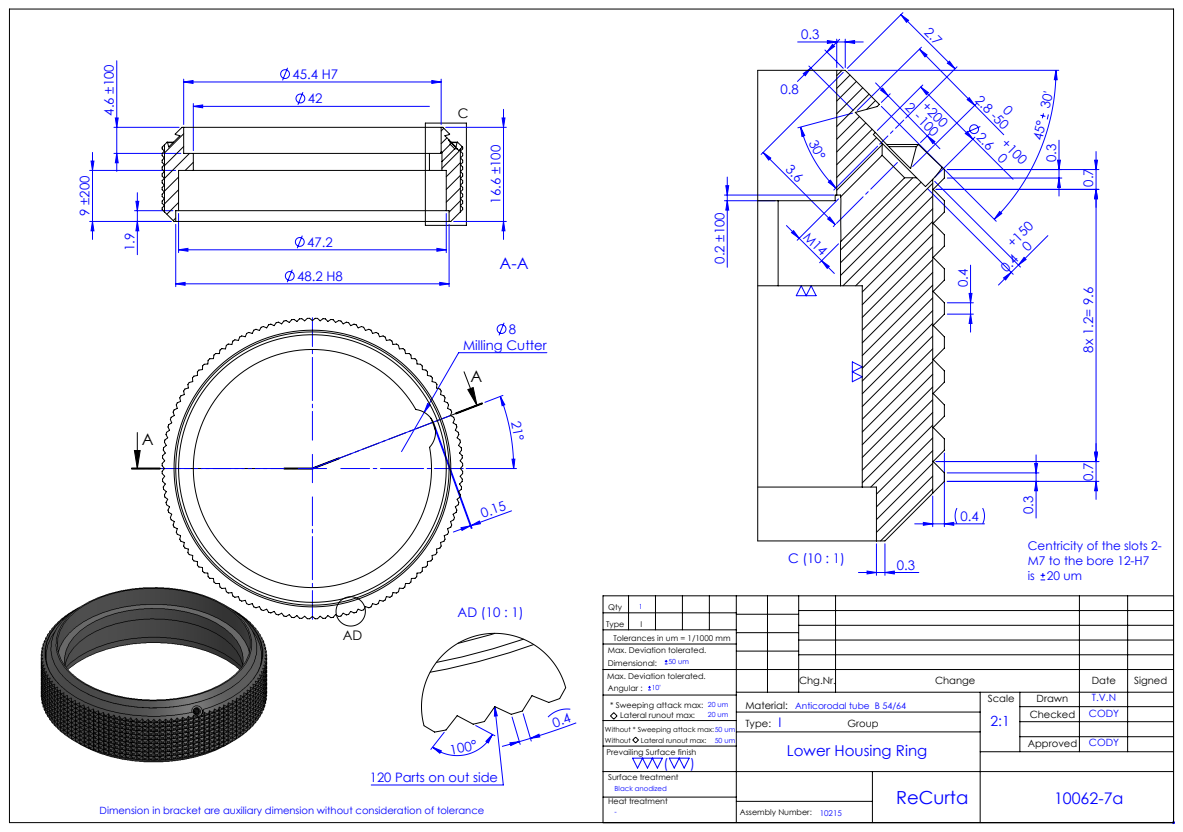
[picture p308: page 1]
Milling Cutter; Black anodized; Anticorodal tube B 54/64; Surface treatment; Heat treatment; Assembly Number:

Centricity of the slots 2-
M7 to the bore 12-H7

Qty | 1
Type | I

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

Lower Housing Ring

120 Parts on out side

Dimension in bracket are auxiliary dimension without consideration of tolerance
