daeken/ReCurta/Solidworks Drawings/10066.pdf

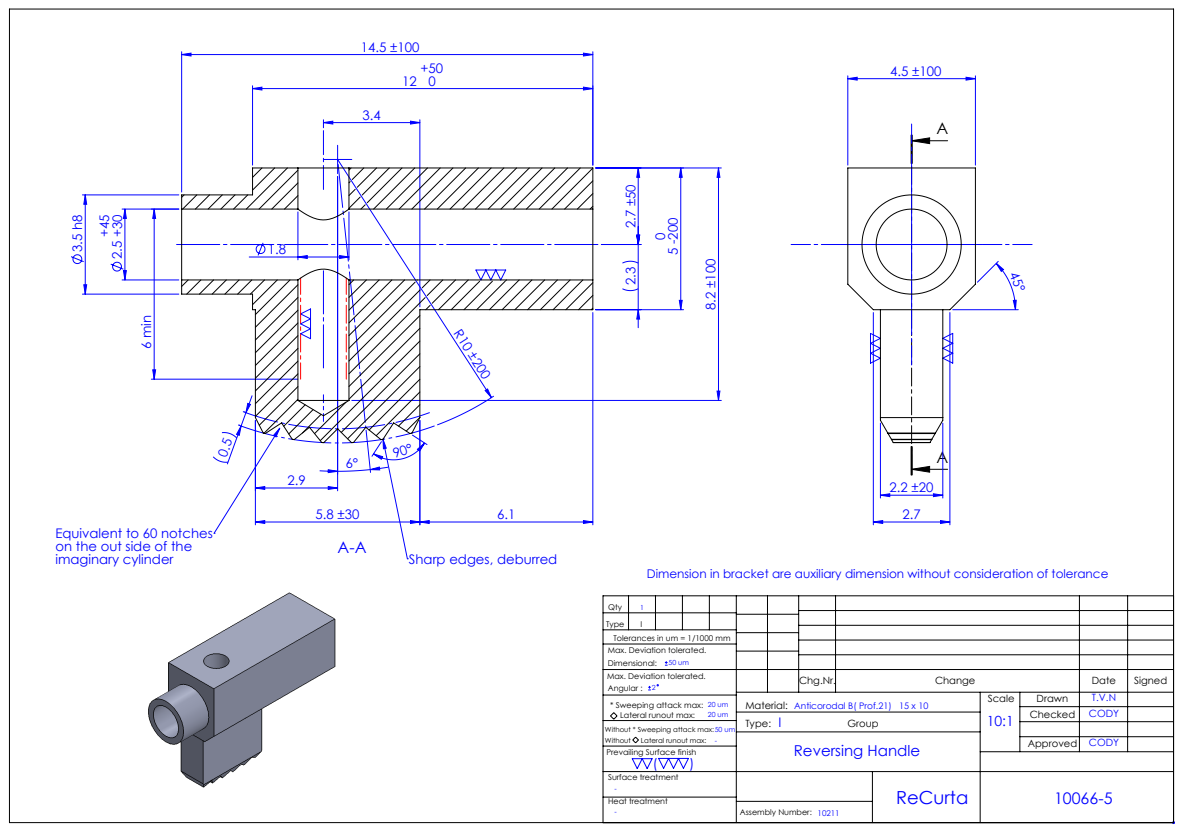
[picture p309: page 1]
6 min; imaginary cylinder; Sharp edges, deburred; Anticorodal B( Prof.21) 15 x 10; Reversing Handle; Surface treatment; Assembly Number:

Equivalent to 60 notches
on the out side of the

Dimension in bracket are auxiliary dimension without consideration of tolerance

Qty | 1
Type | I

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
