daeken/ReCurta/Solidworks Drawings/10071.pdf

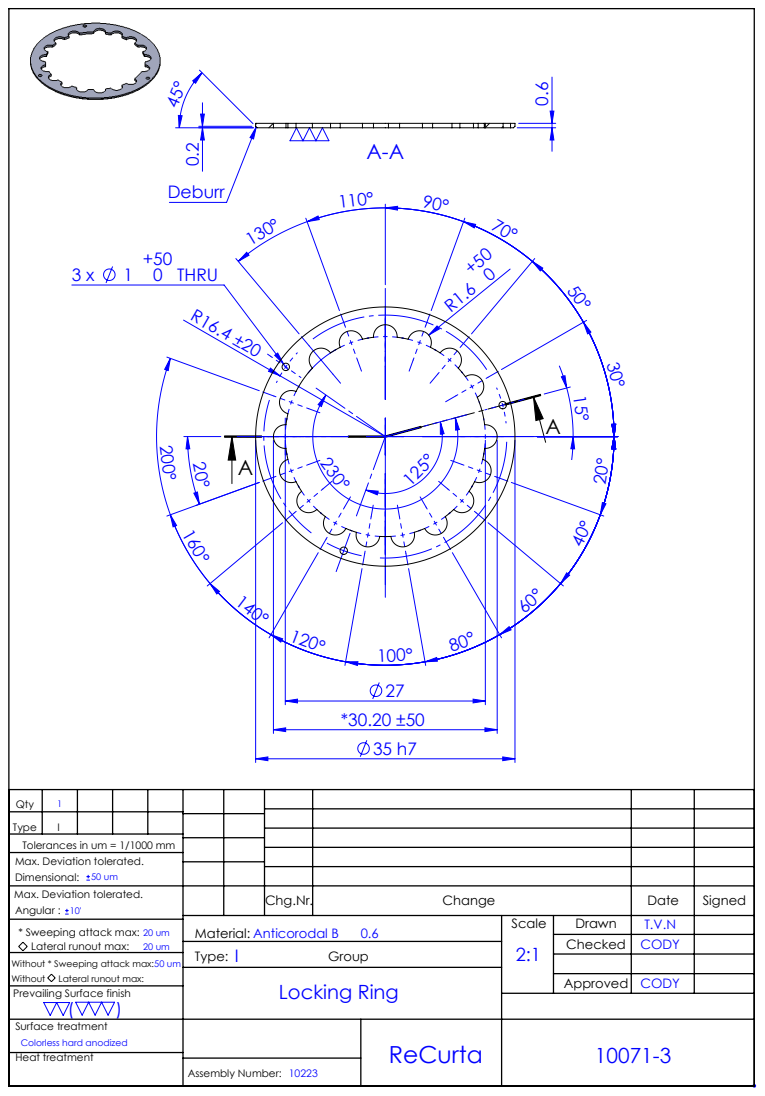
[picture p310: page 1]
0 THRU; Locking Ring; Anticorodal B; Scale; Drawn Material:; Assembly Number:

Qty | 1
Type | I

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

Surface treatment
Colorless hard anodized
Heat treatment
