daeken/ReCurta/Solidworks Drawings/10076.pdf

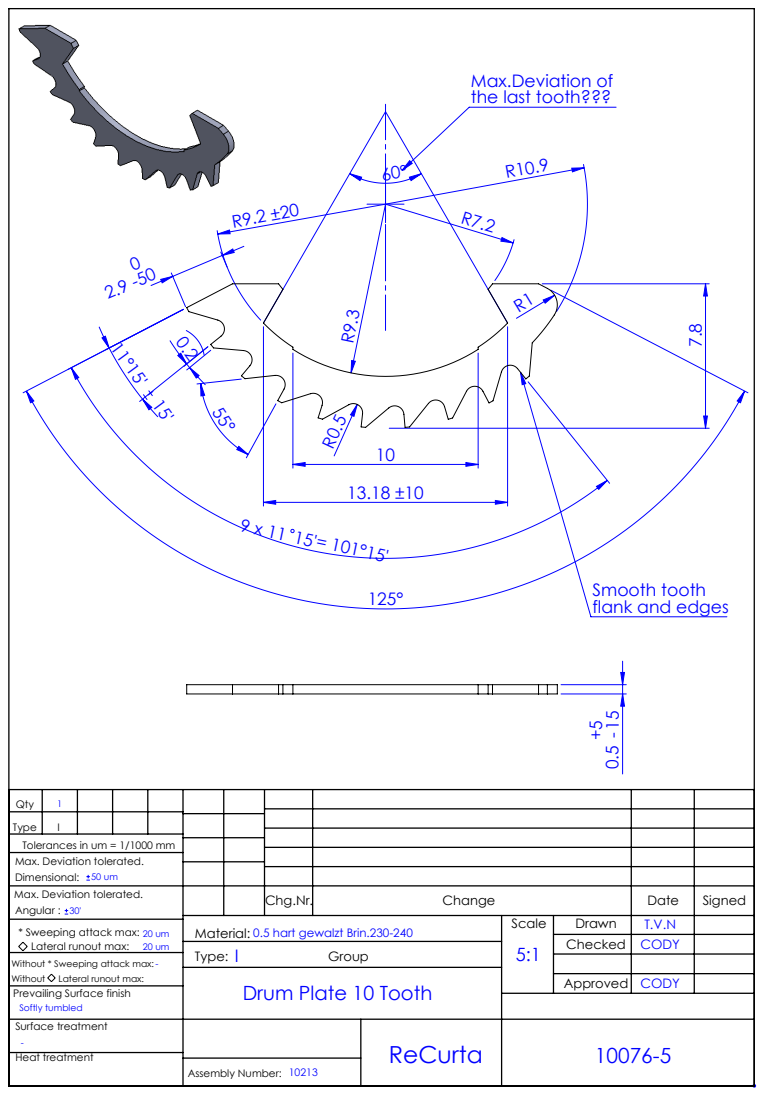
[picture p311: page 1]
Scale; Drawn Material:; Assembly Number:

Max.Deviation of
the last tooth???

Smooth tooth
flank and edges 0.5

Qty | 1
Type | I

Tolerances in um = 1/1000 mm
Max. Deviation tolerated.
Dimensional:
Angular :
* Sweeping attack max:
Lateral runout max:
Without * Sweeping attack max:
Without Lateral runout max:
Prevailing Surface finish
Softly tumbled
Surface treatment
Heat treatment

Drum Plate 10 Tooth

0.5 hart gewalzt Brin.230-240
