daeken/ReCurta/Solidworks Drawings/10077.pdf

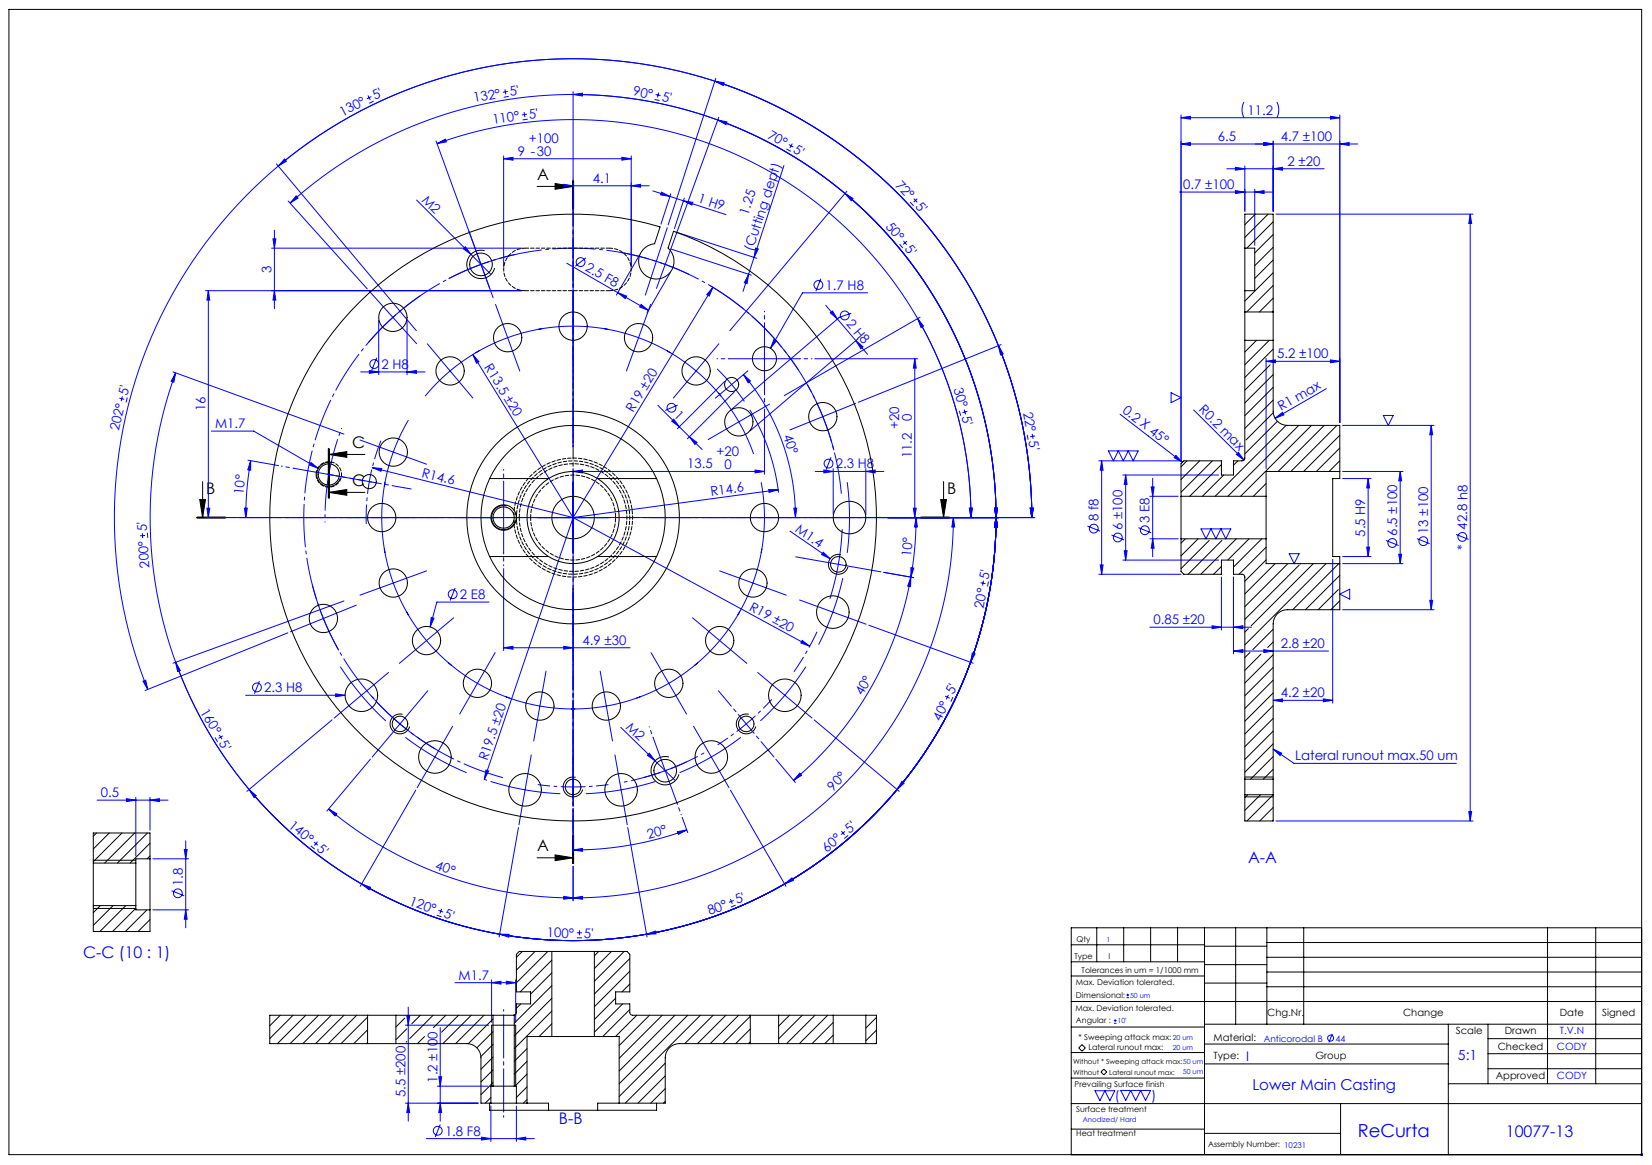
[picture p312: page 1]
(Cutting dept); R0.2 max; R1 max; Anodized/ Hard; Anticorodal B 44; Scale; Drawn Material:; Assembly Number:; Heat treatment; Surface treatment

Lateral runout max.50 um

Qty | 1
Type | I

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

Lower Main Casting
