daeken/ReCurta/Solidworks Drawings/10078.pdf

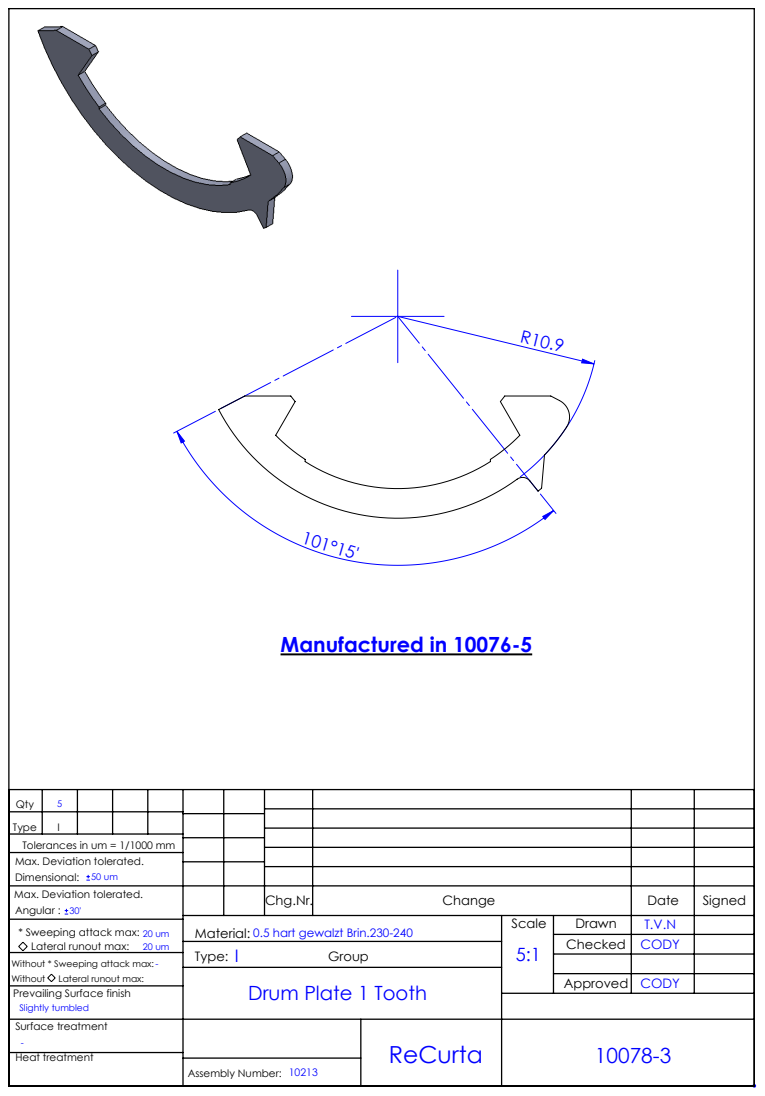
[picture p313: page 1]
Manufactured in 10076-5; Scale; Drawn Material:; Assembly Number:

Qty | 5
Type | I

Tolerances in um = 1/1000 mm
Max. Deviation tolerated.
Dimensional:
Angular :
* Sweeping attack max:
Lateral runout max:
Without * Sweeping attack max:
Without Lateral runout max:
Prevailing Surface finish
Slightly tumbled
Surface treatment
Heat treatment

Drum Plate 1 Tooth

0.5 hart gewalzt Brin.230-240
