daeken/ReCurta/Solidworks Drawings/10080.pdf

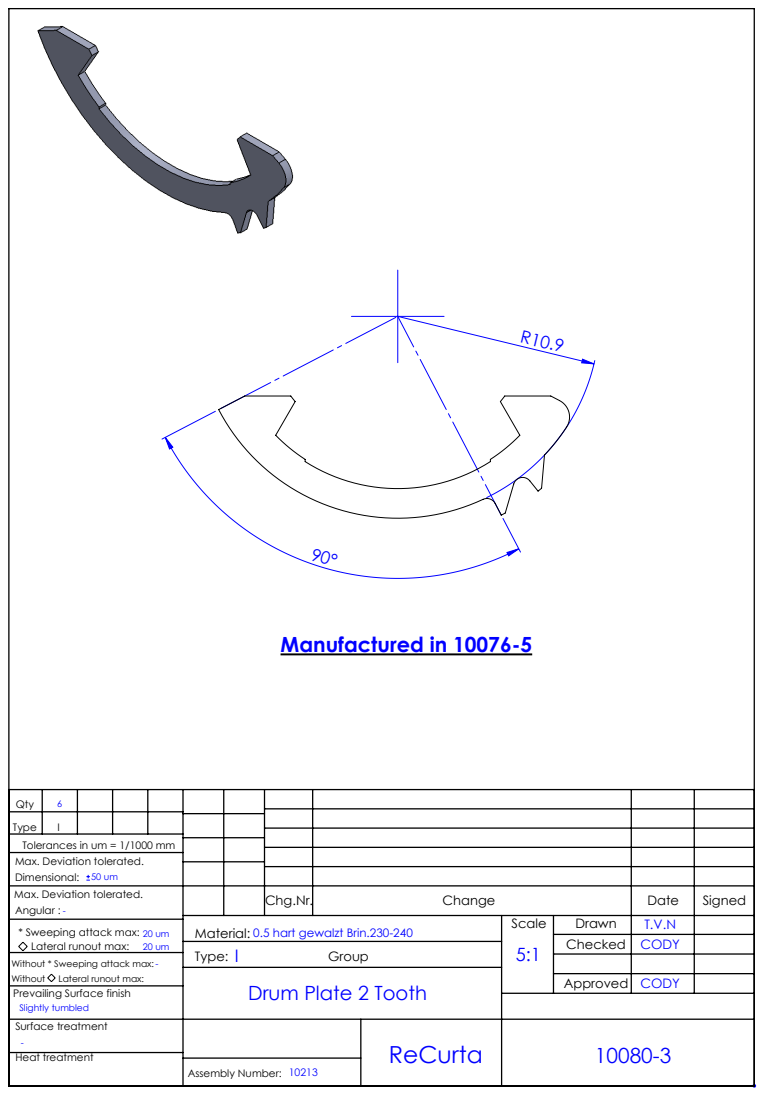
[picture p314: page 1]
Manufactured in 10076-5; Scale; Drawn Material:; Assembly Number:

Qty | 6
Type | I

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

Drum Plate 2 Tooth

0.5 hart gewalzt Brin.230-240
