daeken/ReCurta/Solidworks Drawings/10085.pdf

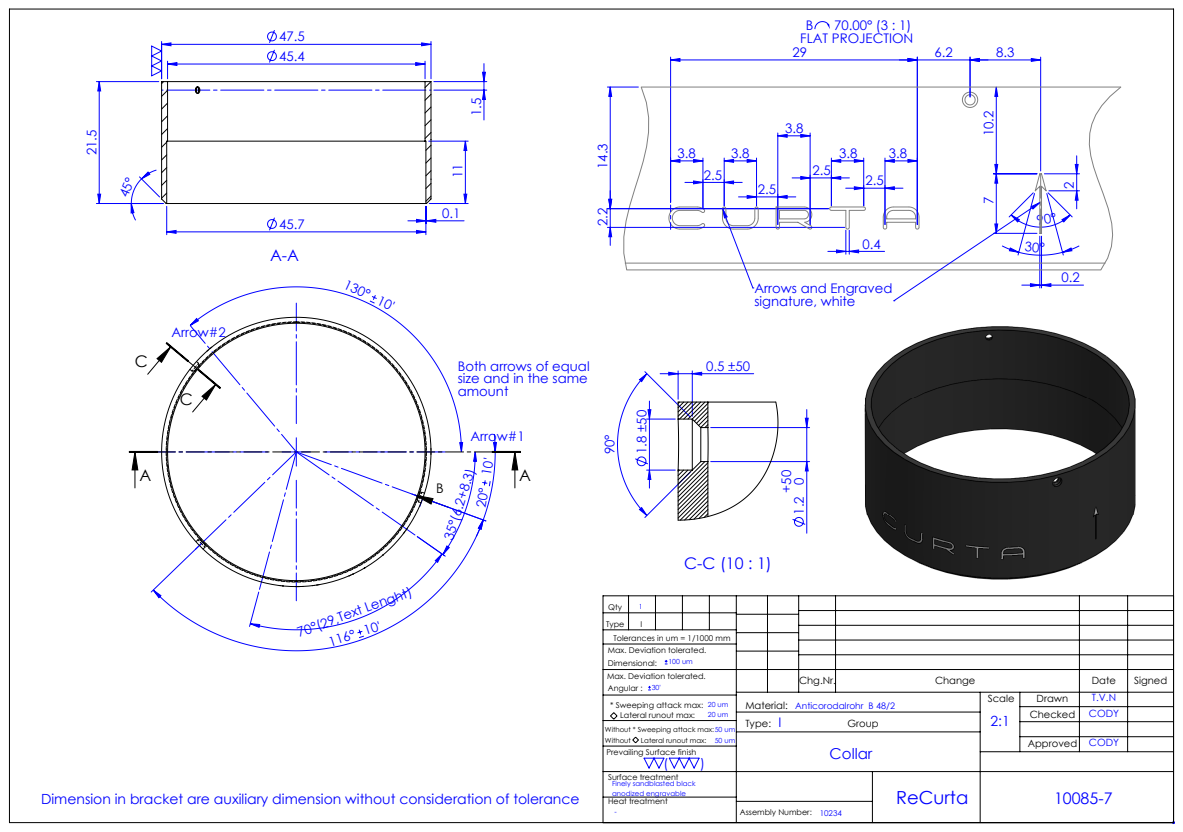
[picture p315: page 1]
70°(29,Text Lenght); B 70.00° (3 : 1) FLAT PROJECTION; Anticorodalrohr B 48/2; Assembly Number:

Arrows and Engraved
signature, white

Both arrows of equal
size and in the same
amount

Qty | 1
Type | I

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

Surface treatment
Finely sandblasted black
anodized engravable
Heat treatment

Dimension in bracket are auxiliary dimension without consideration of tolerance
