daeken/ReCurta/Solidworks Drawings/10086.pdf

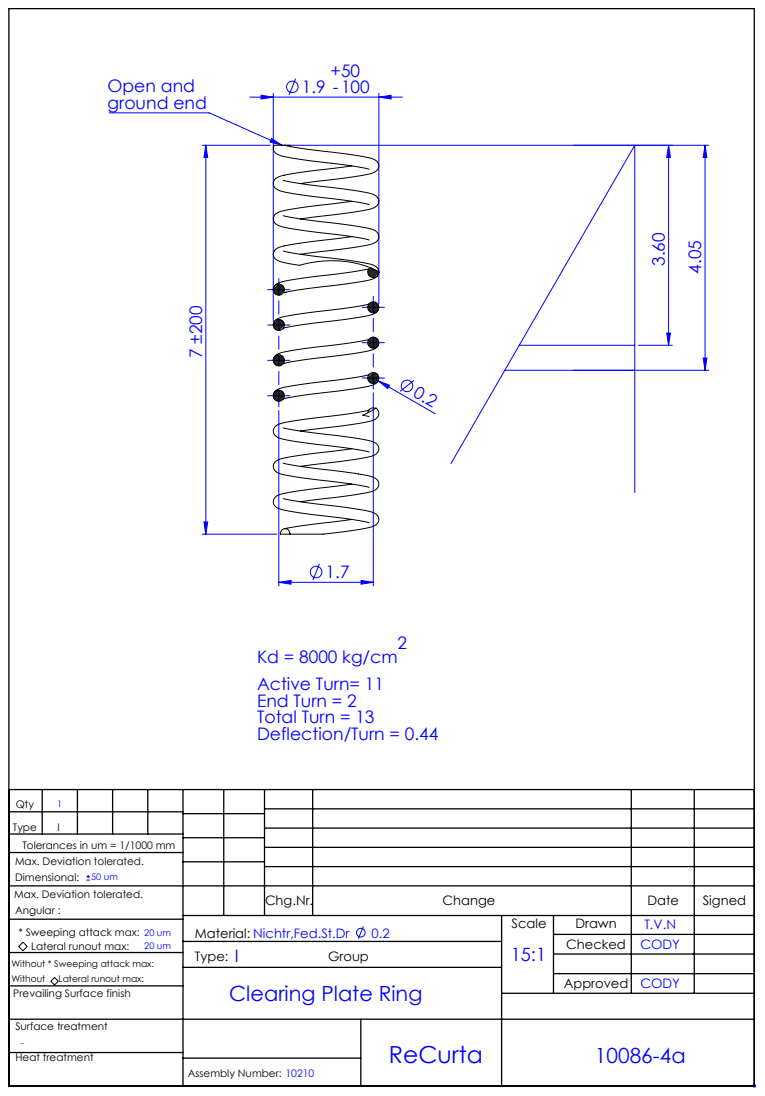
[picture p316: page 1]
Open and ground end; Assembly Number:; Heat treatment; Surface treatment

Active Turn= 11
End Turn = 2
Total Turn = 13
Deflection/Turn = 0.44

Qty | 1
Type | I

Tolerances in um = 1/1000 mm
Max. Deviation tolerated.
Dimensional:

Max. Deviation tolerated. Angular : | | | Chg.Nr. | Change | Date | Signed

Nichtr,Fed.St.Dr 0.2 | Scale 15:1 | Drawn Material: | T.V.N

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

Clearing Plate Ring

Checked | CODY
