daeken/ReCurta/Solidworks Drawings/10088.pdf

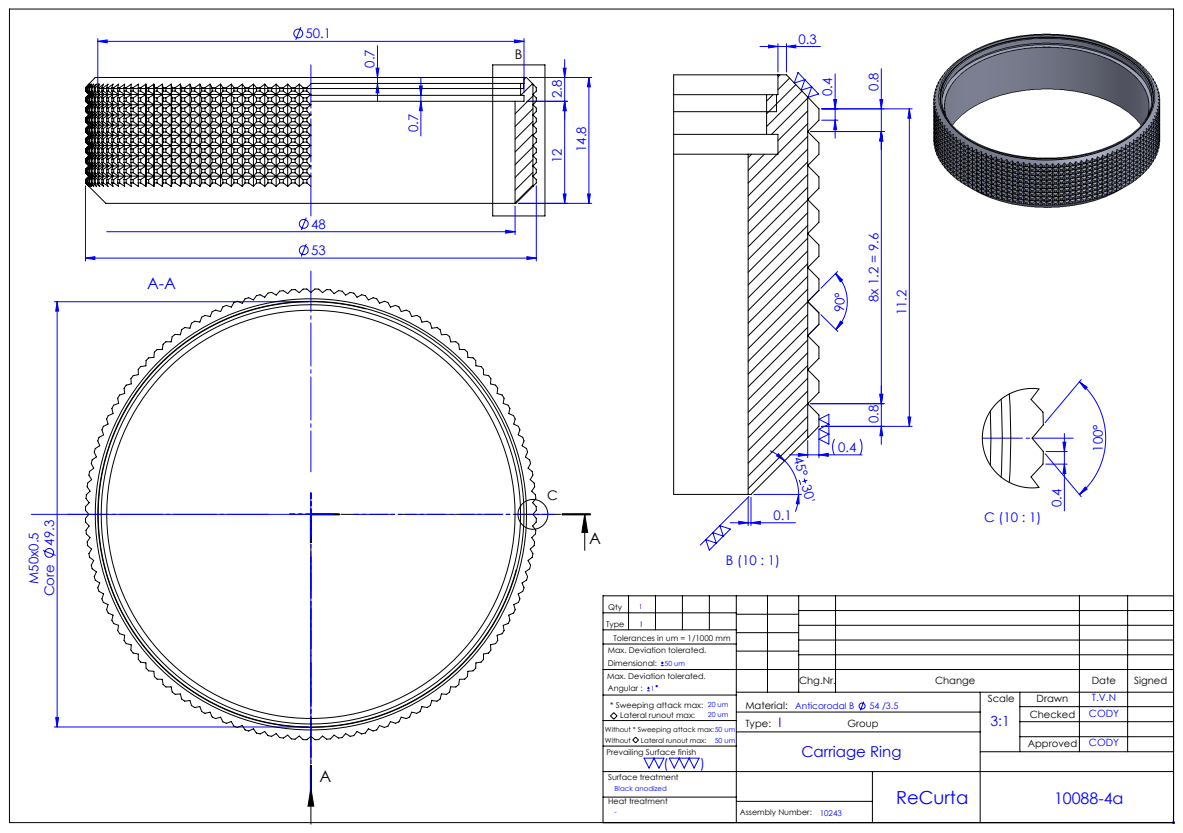
[picture p317: page 1]
Core 49.3; Black anodized; Anticorodal B; Carriage Ring; Surface treatment; Heat treatment; Assembly Number:

Qty | 1
Type | I

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
