daeken/ReCurta/Solidworks Drawings/10097.pdf

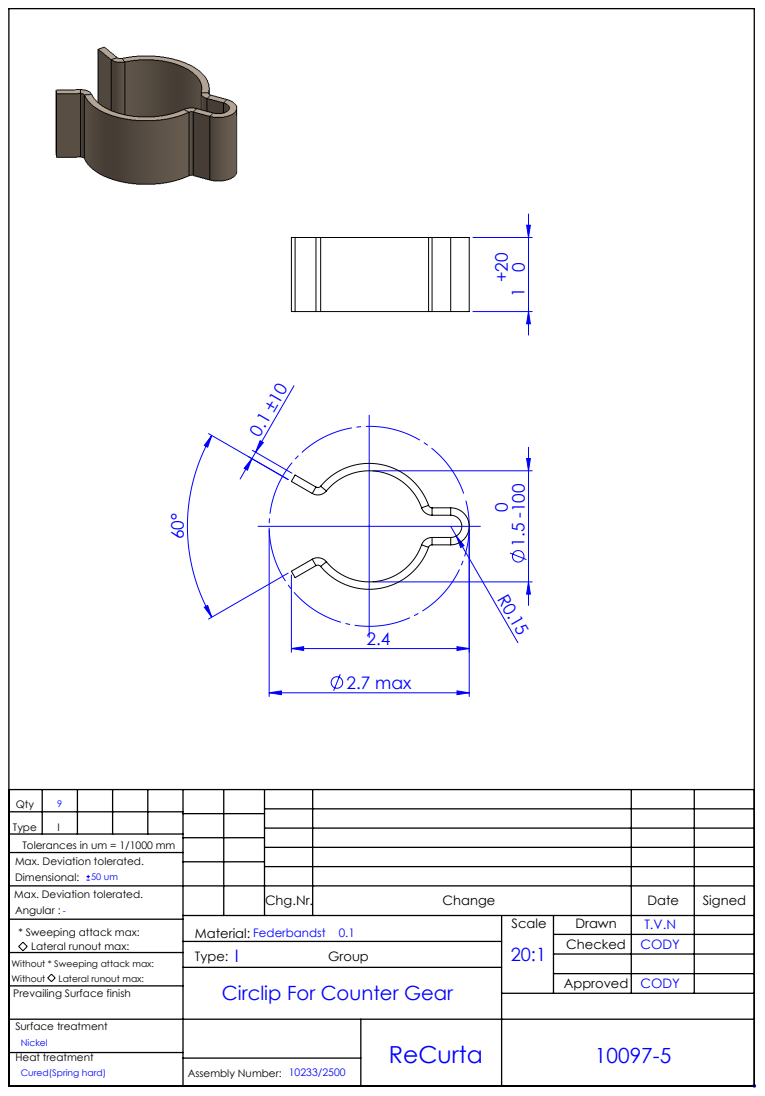
[picture p318: page 1]
2.7 max; Federbandst 0.1; Scale; Drawn Material:; Assembly Number:

Qty | 9
Type | I

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

Circlip For Counter Gear

Surface treatment
Nickel
Heat treatment
Cured(Spring hard)
