daeken/ReCurta/Solidworks Drawings/10099.pdf

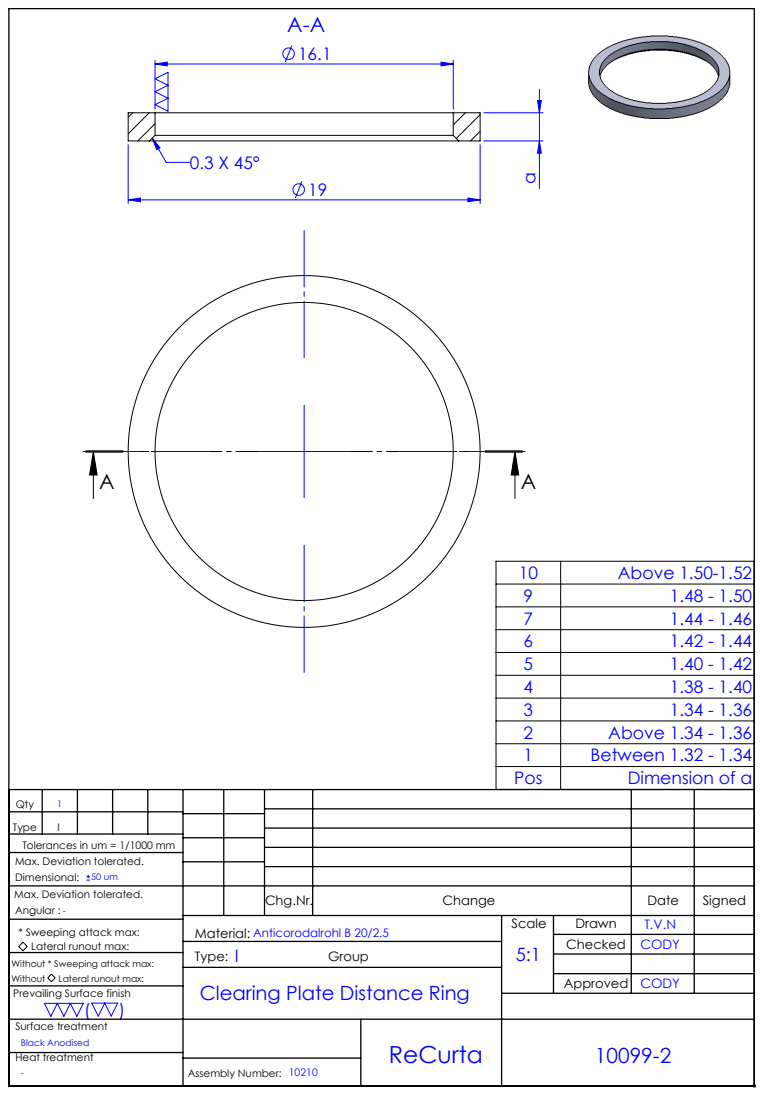
[picture p319: page 1]
Black Anodised; Anticorodalrohl B 20/2.5; Scale; Drawn Material:; Assembly Number:; Heat treatment; Surface treatment

10 | Above 1.50-1.52
9 | 1.48 - 1.50
7 | 1.44 - 1.46
6 | 1.42 - 1.44
5 | 1.40 - 1.42
4 | 1.38 - 1.40
3 | 1.34 - 1.36
2 | Above 1.34 - 1.36
1 | Between 1.32 - 1.34
Pos | Dimension of a

Qty | 1
Type | I

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

Clearing Plate Distance Ring
