daeken/ReCurta/reference-photos/IMG_1088.jpg

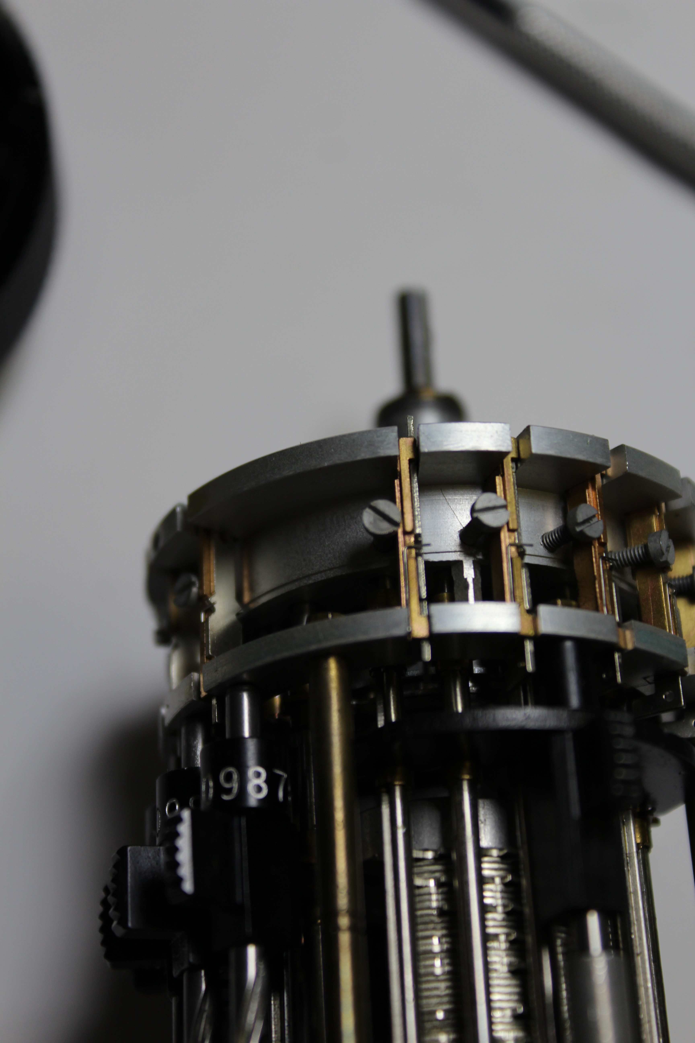
reference-photos/IMG_1088.jpg
